mylabpcb/myCPU/Cad/Sep2_200_Wall v2.stl

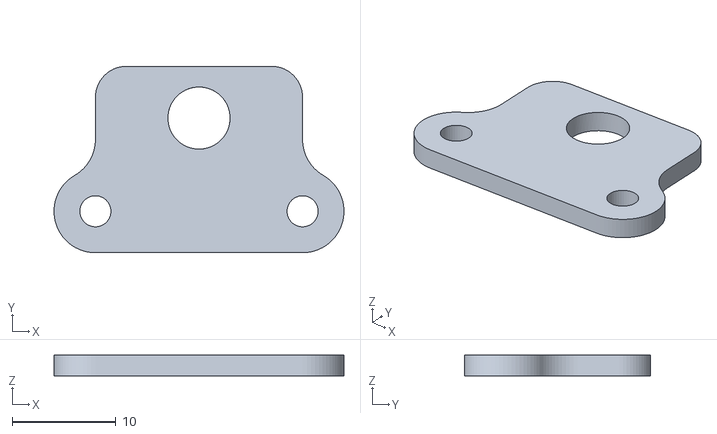
[picture p21: CAD file, 2022-01-03]
Cad/Sep2_200_Wall v2.stl
28.0 x 18.0 x 2.00
