mylabpcb/myCPU/Cad/Sep3_200_Wall v3.stl

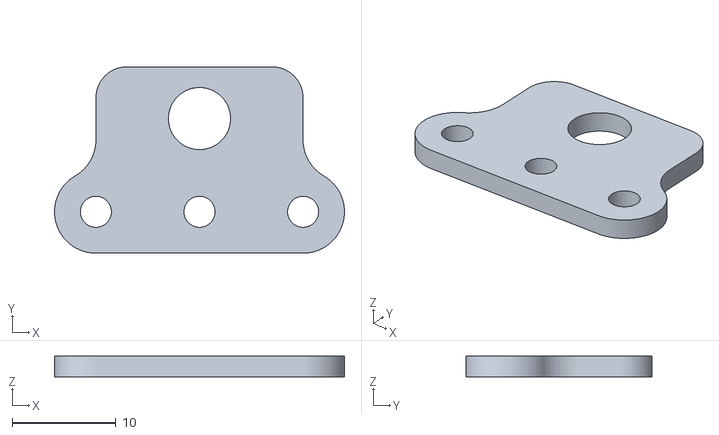
[picture p22: CAD file, 2022-01-03]
Cad/Sep3_200_Wall v3.stl
28.0 x 18.0 x 2.00
