mylabpcb/myCPU/Cad/Sep.stl

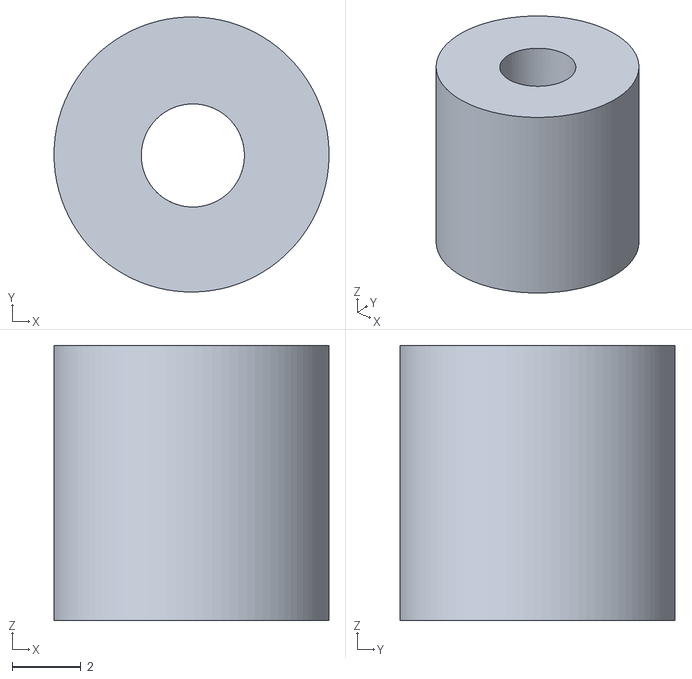
[picture p23: CAD file, 2022-01-03]
Cad/Sep.stl
8.00 x 8.00 x 8.00
