mylabpcb/myCPU/Cad/Sep2_180.stl

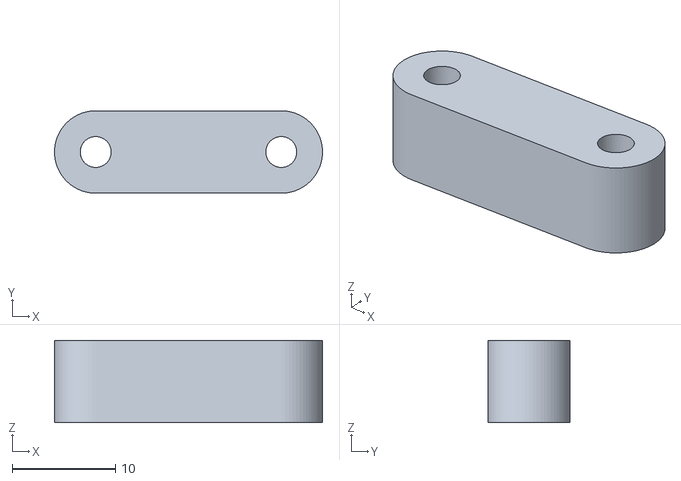
[picture p24: CAD file, 2022-01-03]
Cad/Sep2_180.stl
26.0 x 8.00 x 8.00
