mylabpcb/myCPU/Docs/myCPU_BUS_Manager_module_full.pdf

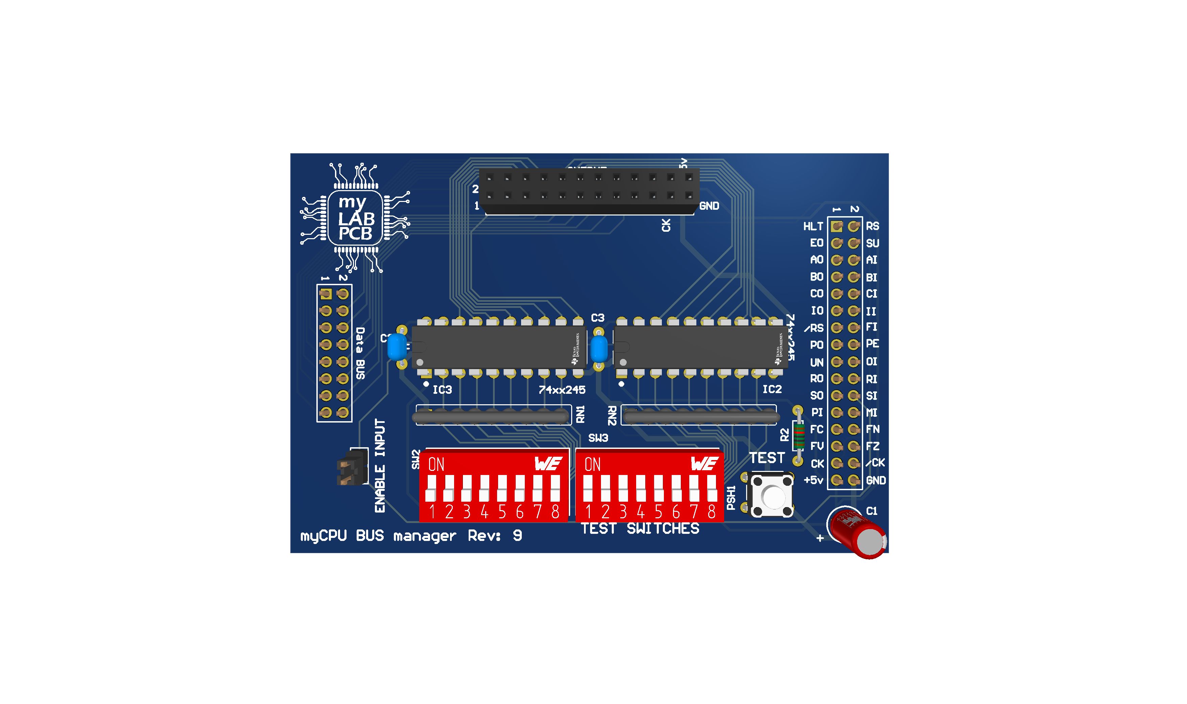
[picture p73: page 1]

Decoupling Capacitors 31 | 42 5 | 6 7 | 8 9 | 10 11 | 12

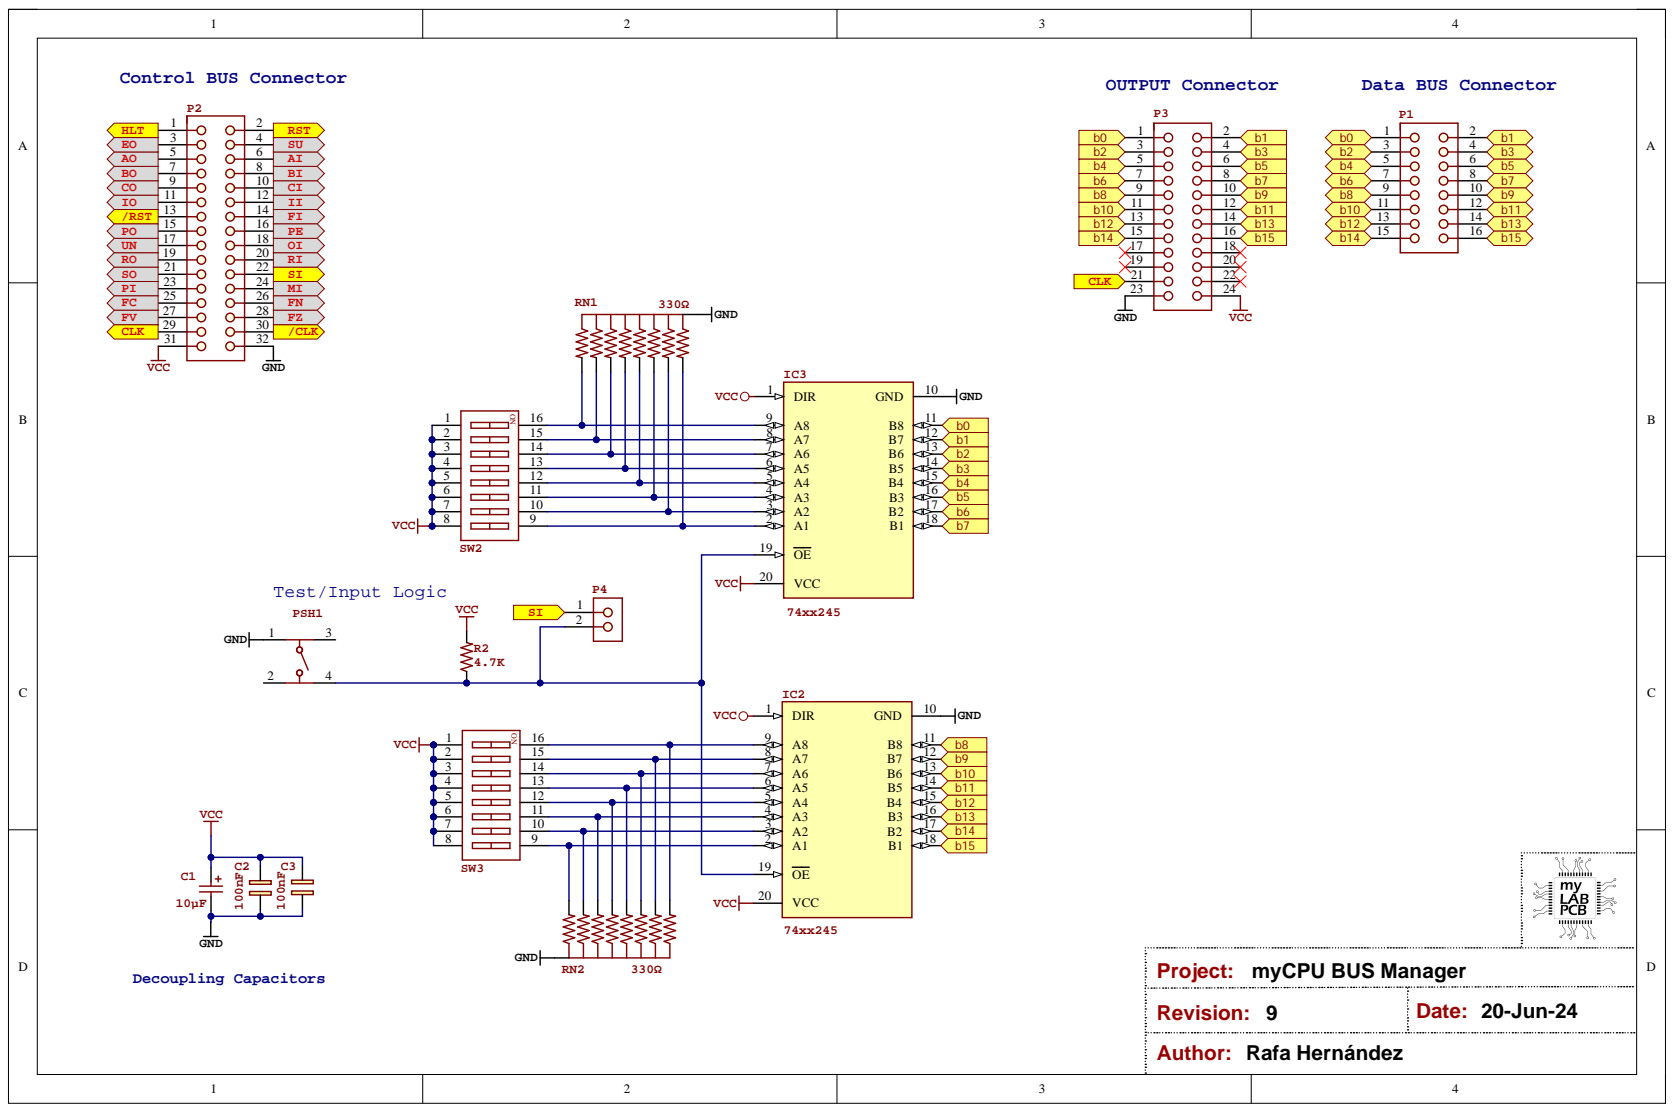
[picture p74: page 3]

Project: myCPU BUS Manager

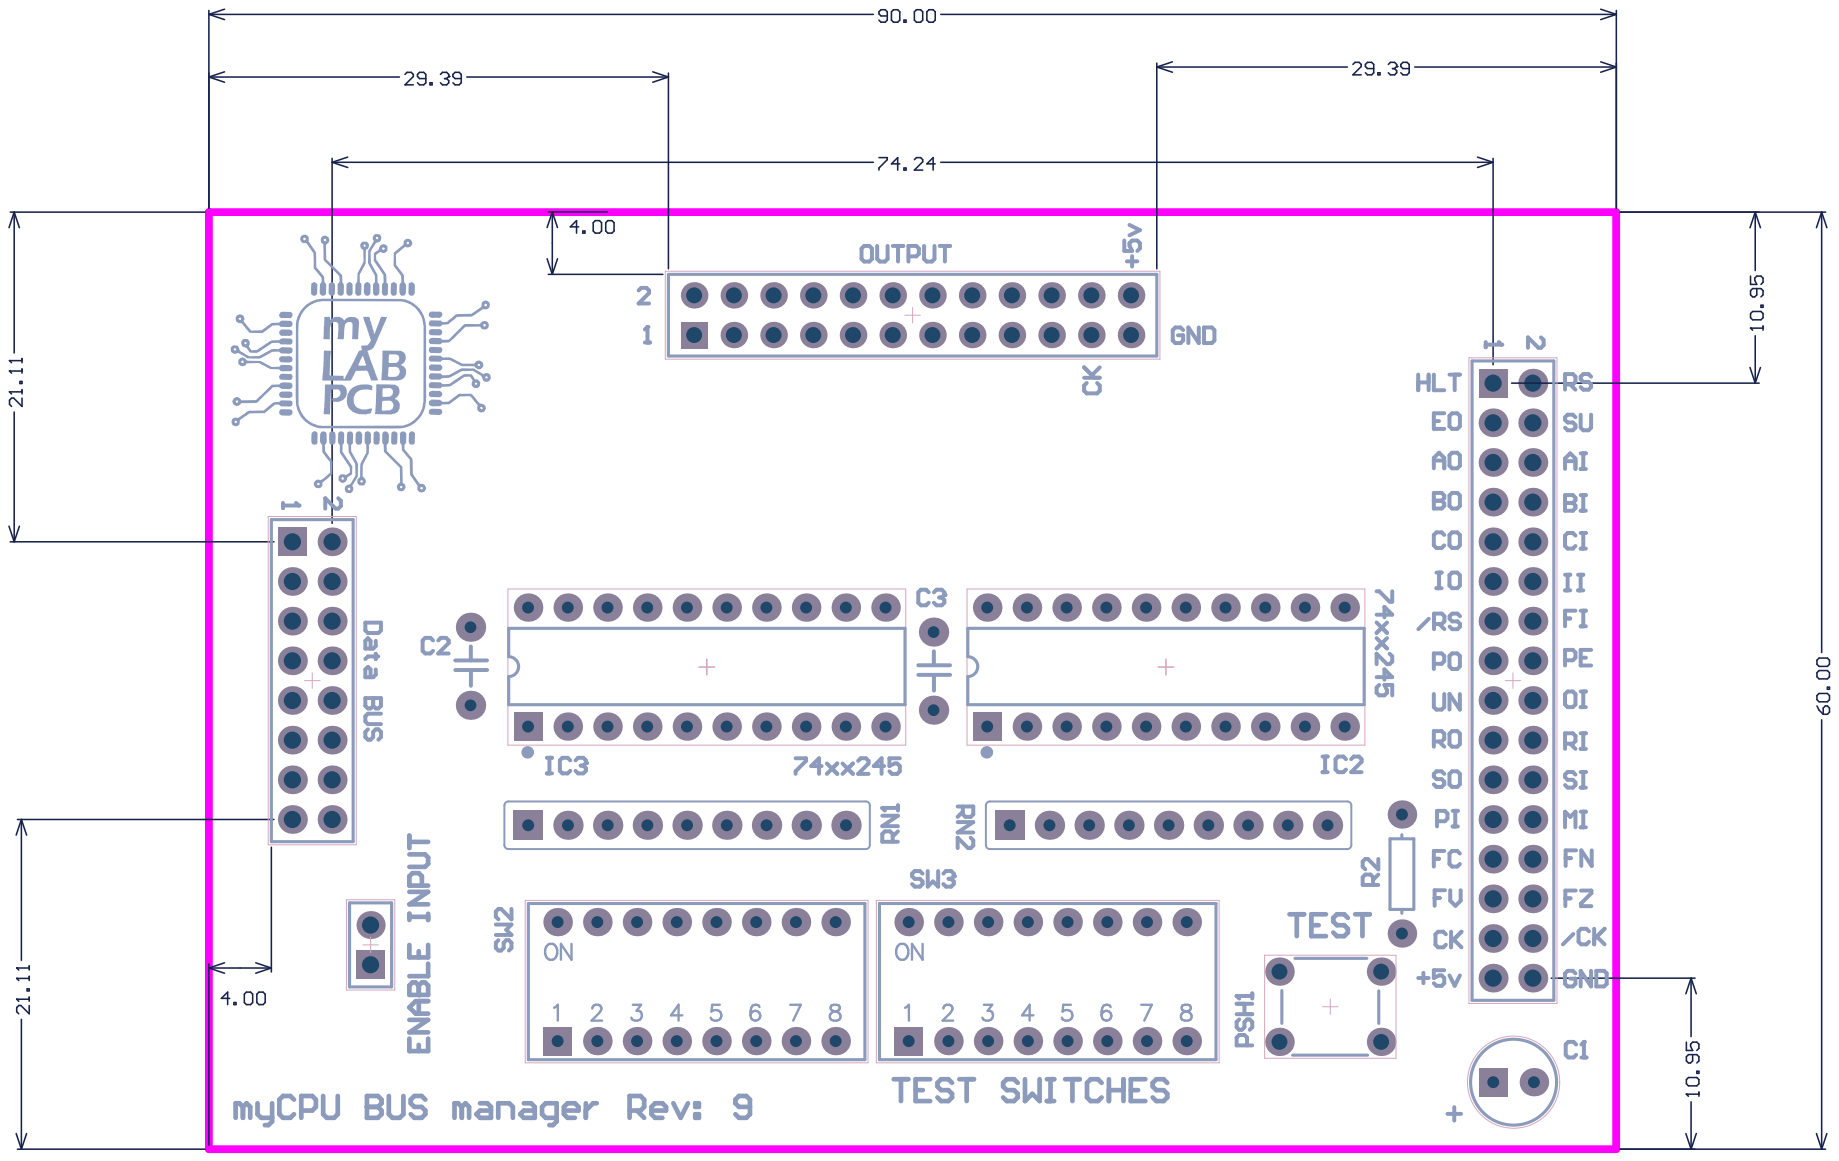
[picture p75: page 4]

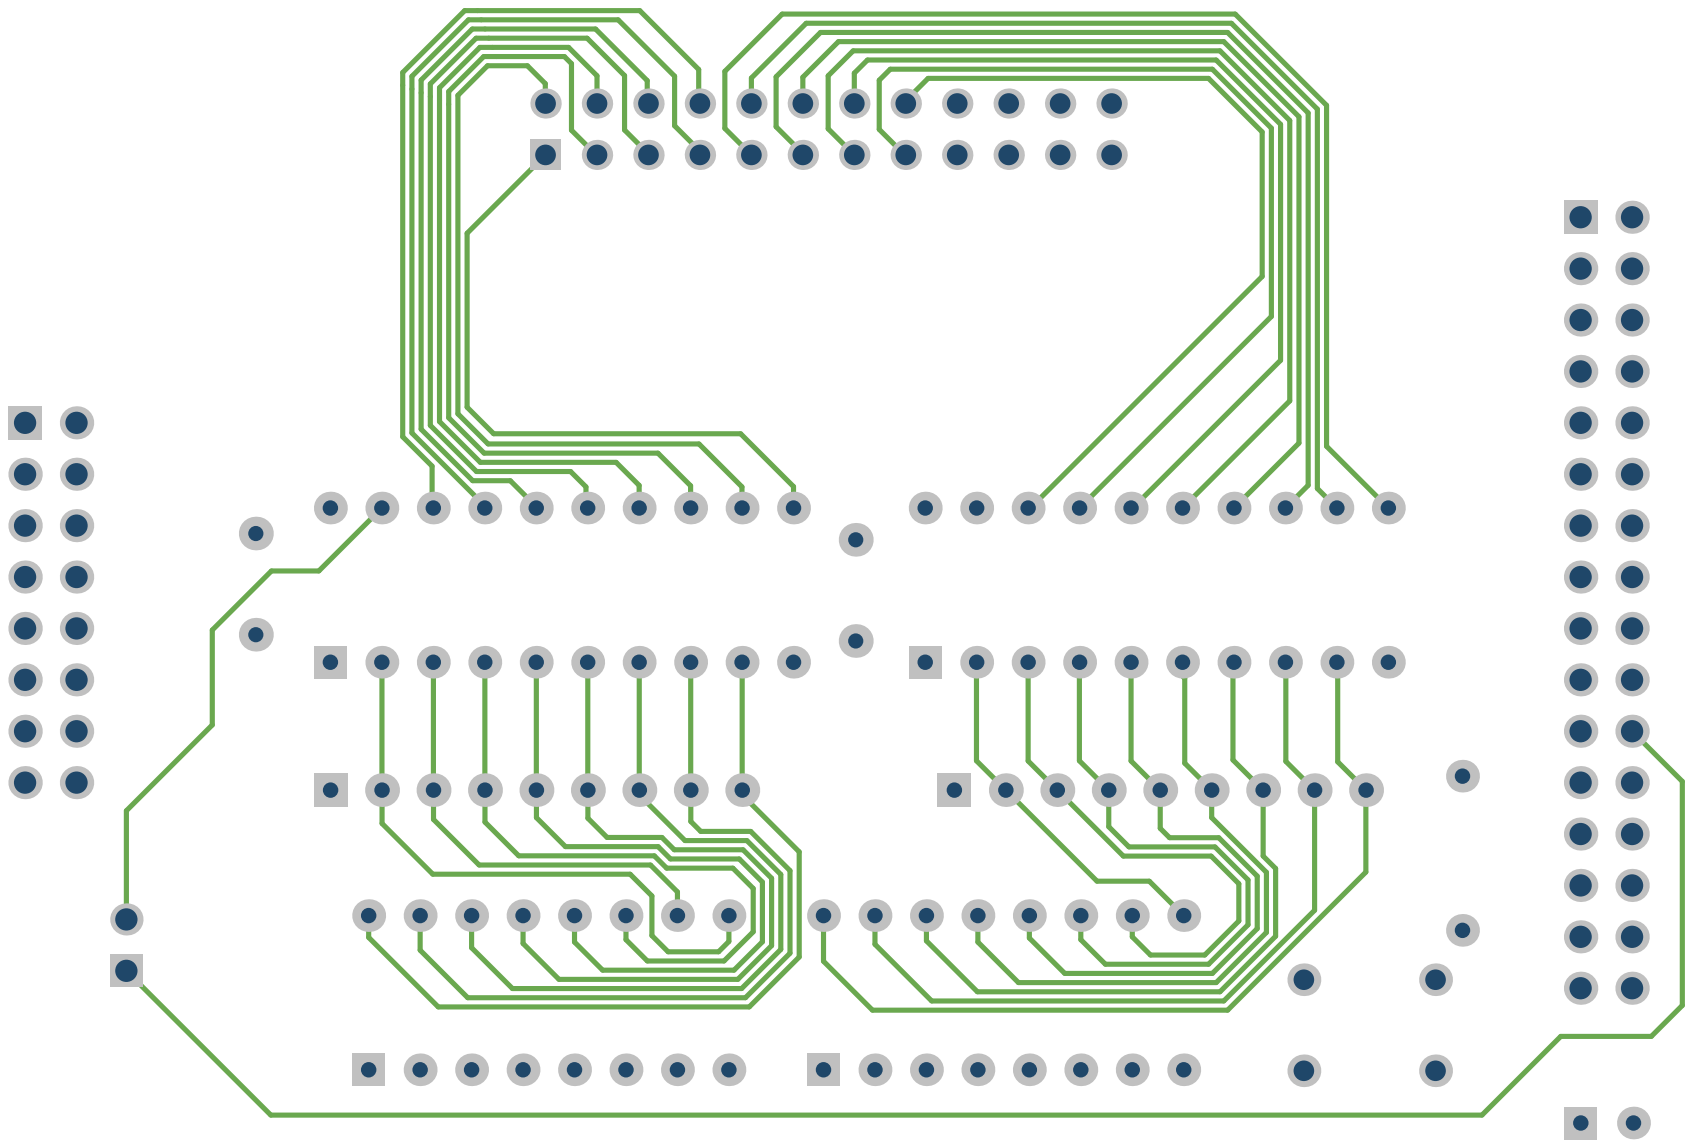
[picture p76: page 5]

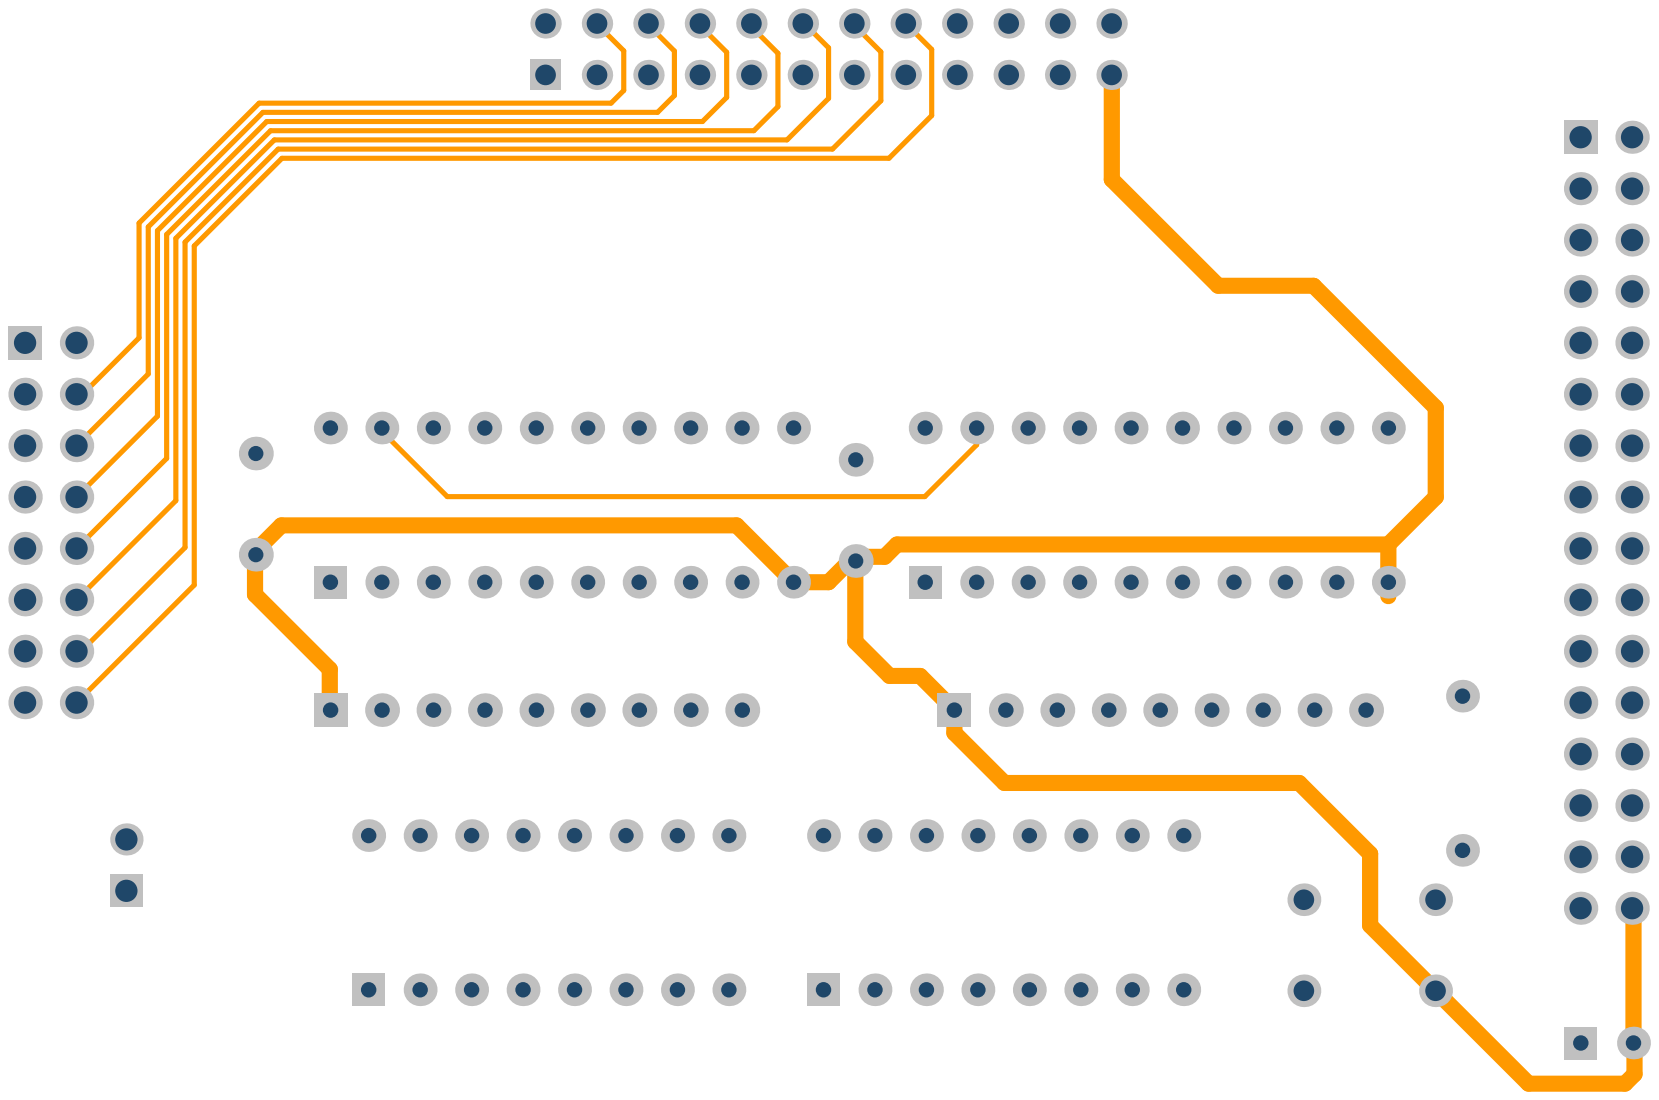
[picture p77: page 6]

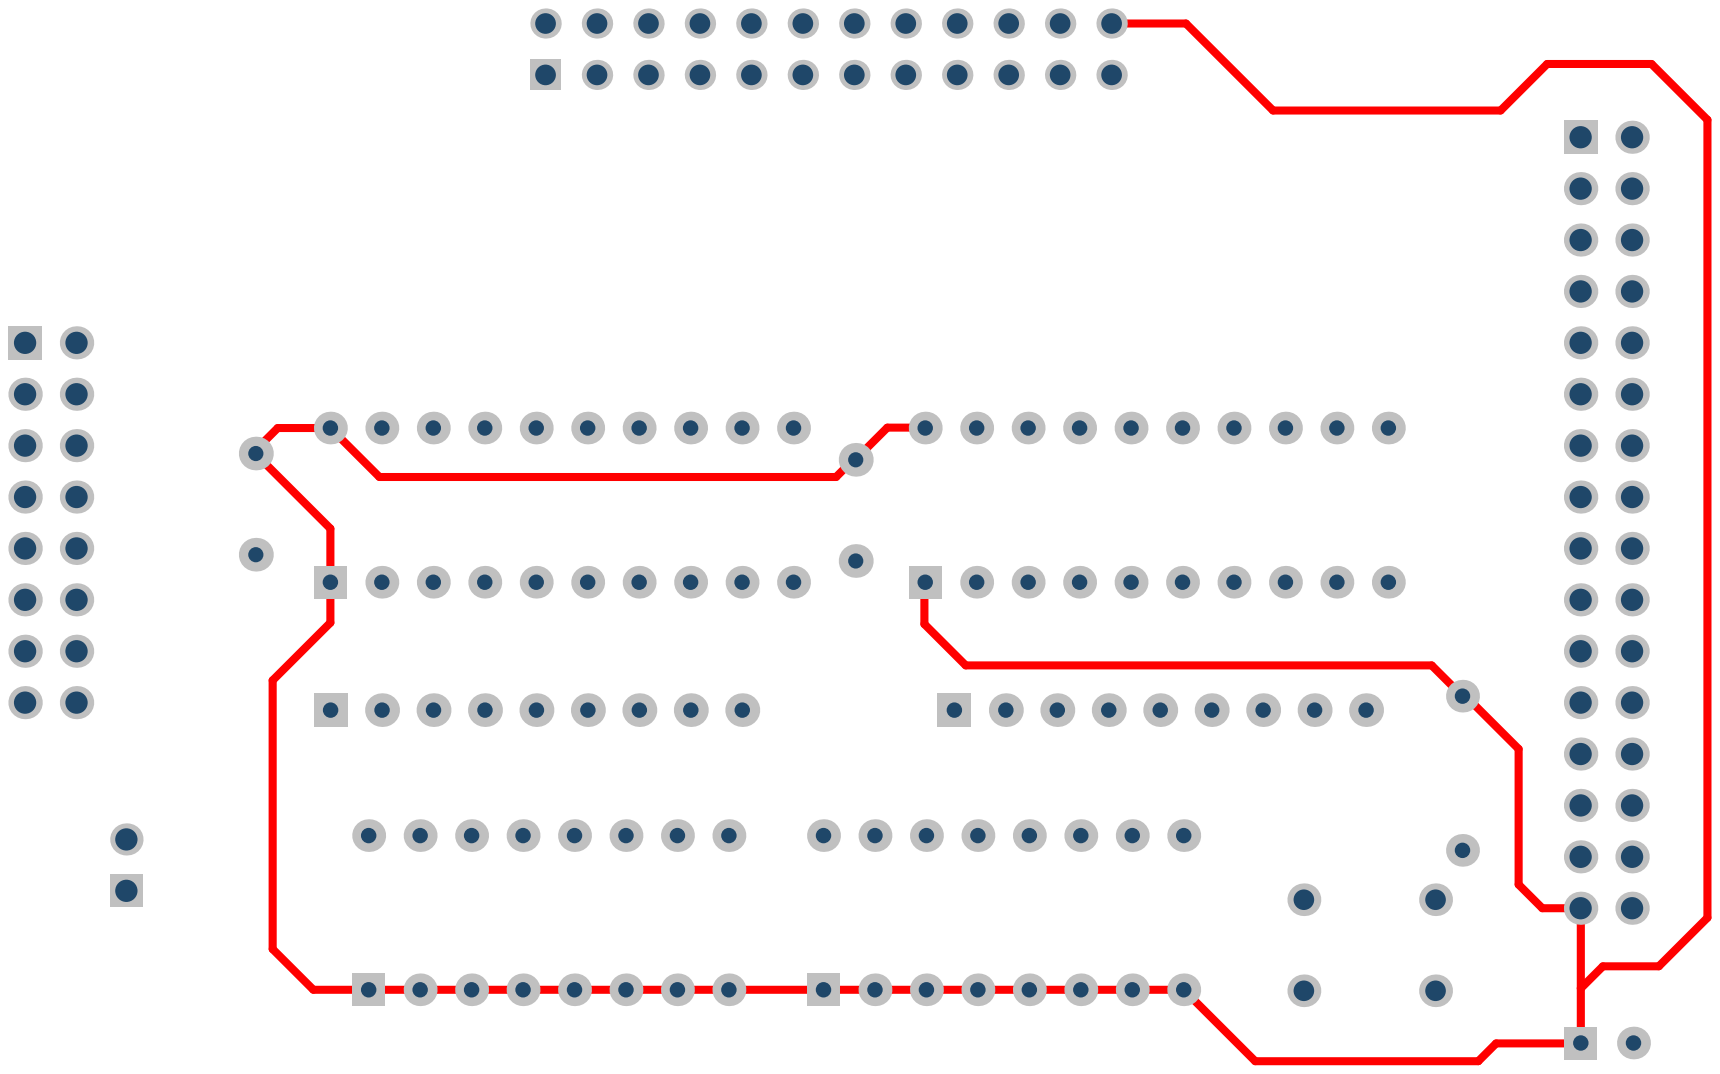
[picture p78: page 7]

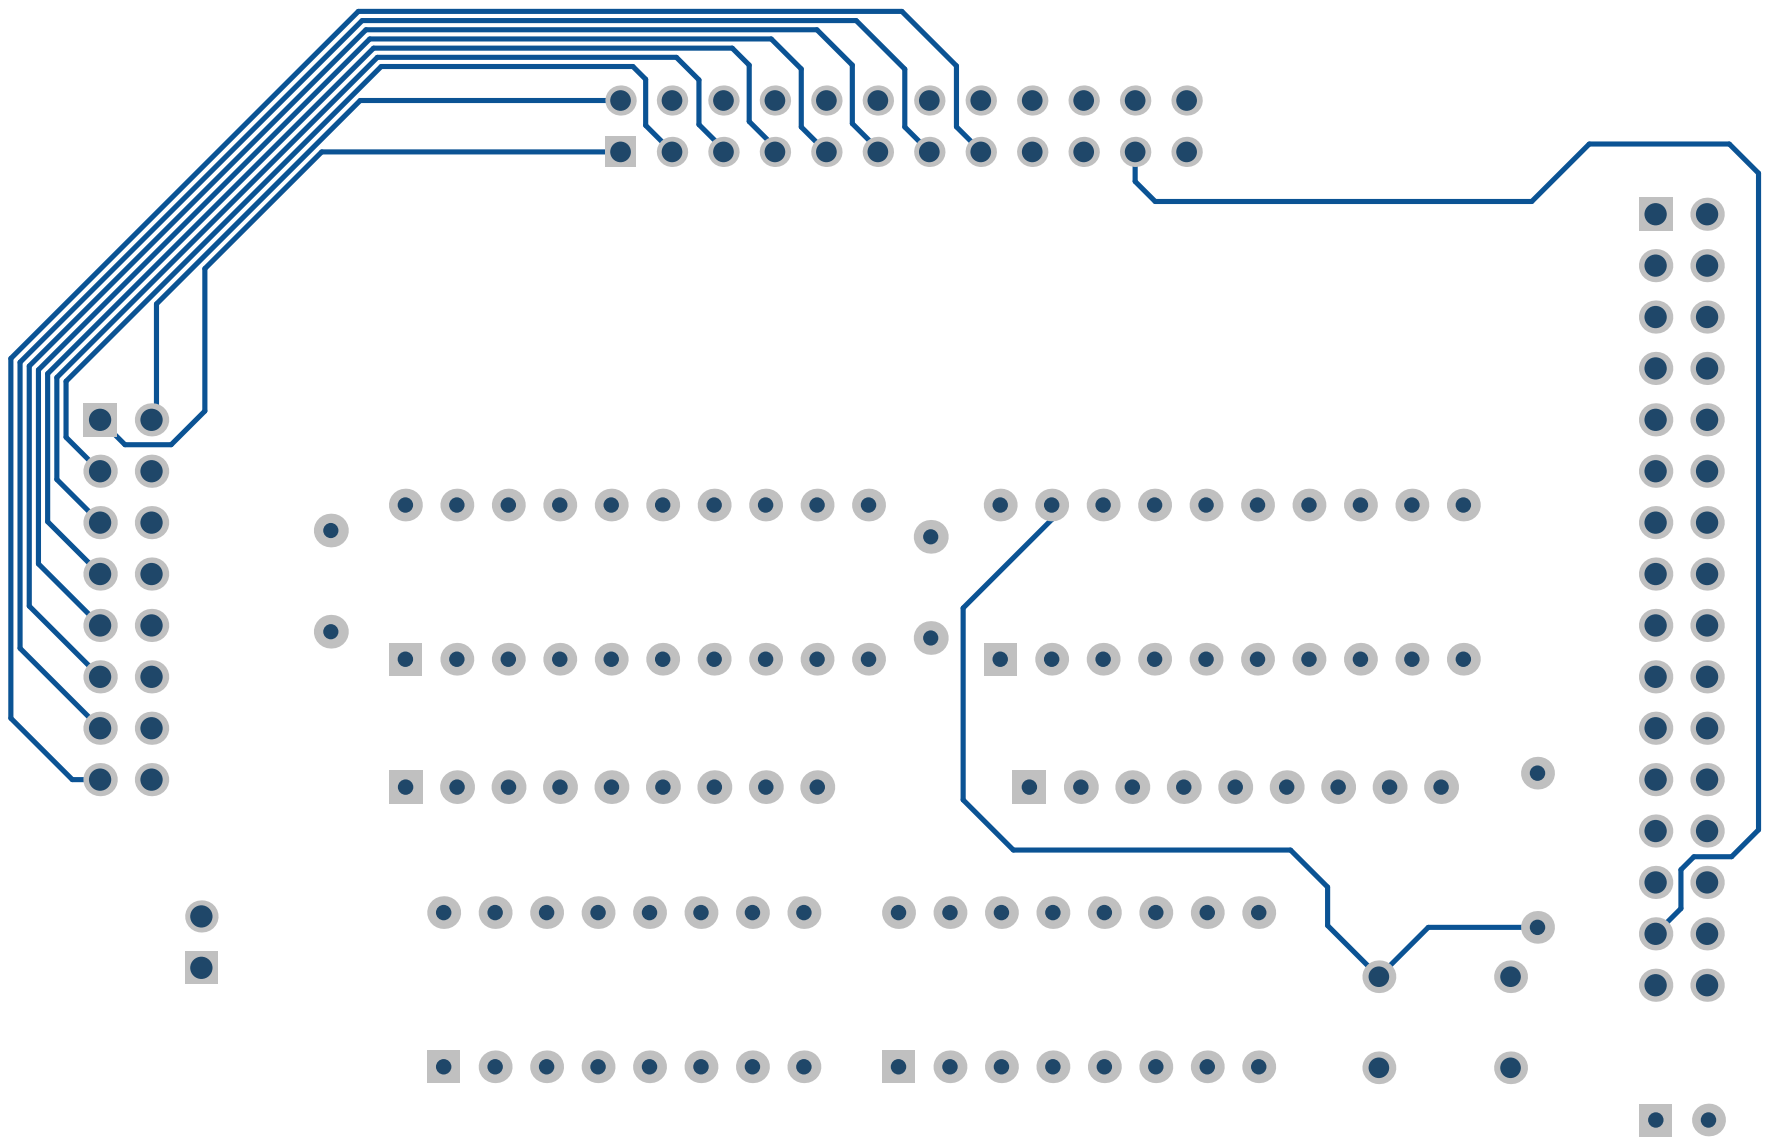
[picture p79: page 8]

# Bill of Materials

# myCPU BUS Manager

Description | Value | Q
Electrolytic capacitor 16v/50v | 10µF | 1
Ceramic capacitor | 100nF | 2
Non inverting bus transceiver | 74xx245 | 2
Pin Header, THT, pitch 2.54mm, Dual Row, Vertical | 16p | 1
Pin Header, THT, pitch 2.54mm, Dual Row, Vertical | 32p | 1
Socket Header, THT, pitch 2.54mm, Dual Row, Vertical | 24p | 1
Pin Header, THT, pitch 2.54mm, Single Row, Vertical | 2p | 1
Tactile button 6 mm | 6mm | 1
Resistor Axial | 4.7K | 1
Resistor array 8 elements,9 pins | 330 | 2
DIP switch 8 positions | 8p | 2

# Assembly List

## myCPU BUS Manager

Designator | Description | Value
C1 | Electrolytic capacitor 16v/50v | 10µF
C2 | Ceramic capacitor | 100nF
C3 | Ceramic capacitor | 100nF
IC2 | Non inverting bus transceiver | 74xx245
IC3 | Non inverting bus transceiver | 74xx245
P1 | Pin Header, THT, pitch 2.54mm, Dual Row, Vertical | 16p
P2 | Pin Header, THT, pitch 2.54mm, Dual Row, Vertical | 32p
P3 | Socket Header, THT, pitch 2.54mm, Dual Row, Vertical | 24p
P4 | Pin Header, THT, pitch 2.54mm, Single Row, Vertical | 2p
PSH1 | Tactile button 6 mm | 6mm
R2 | Resistor Axial | 4.7K
RN1 | Resistor array 8 elements,9 pins | 330
RN2 | Resistor array 8 elements,9 pins | 330
SW2 | DIP switch 8 positions | 8p
SW3 | DIP switch 8 positions | 8p
