mylabpcb/myCPU/Docs/myCPU_BUS_module_full.pdf

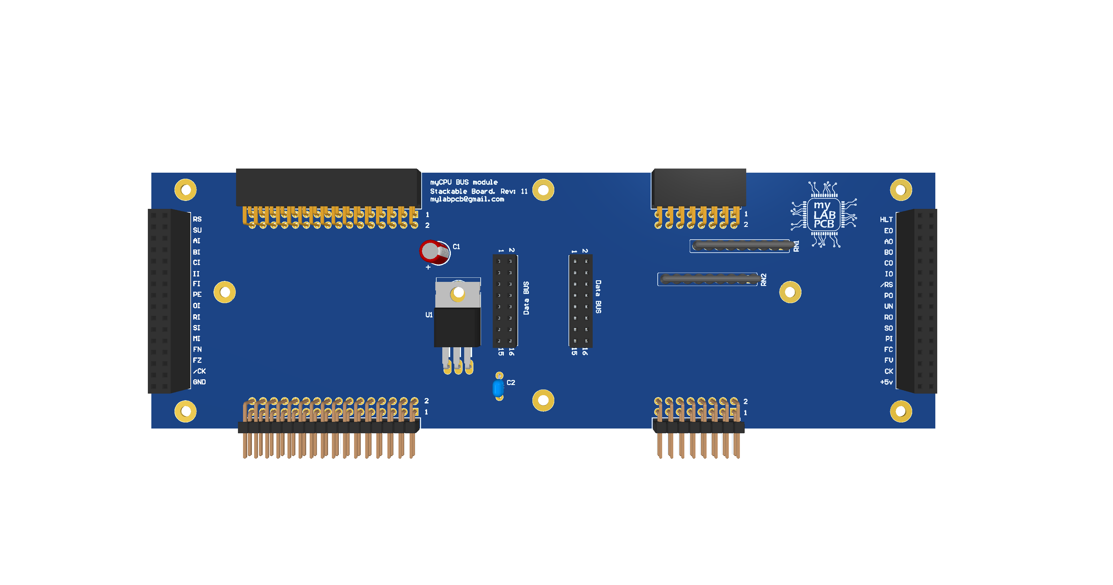
[picture p80: page 1]

# GND GND b1b3b5b7b9b11 b13 b15

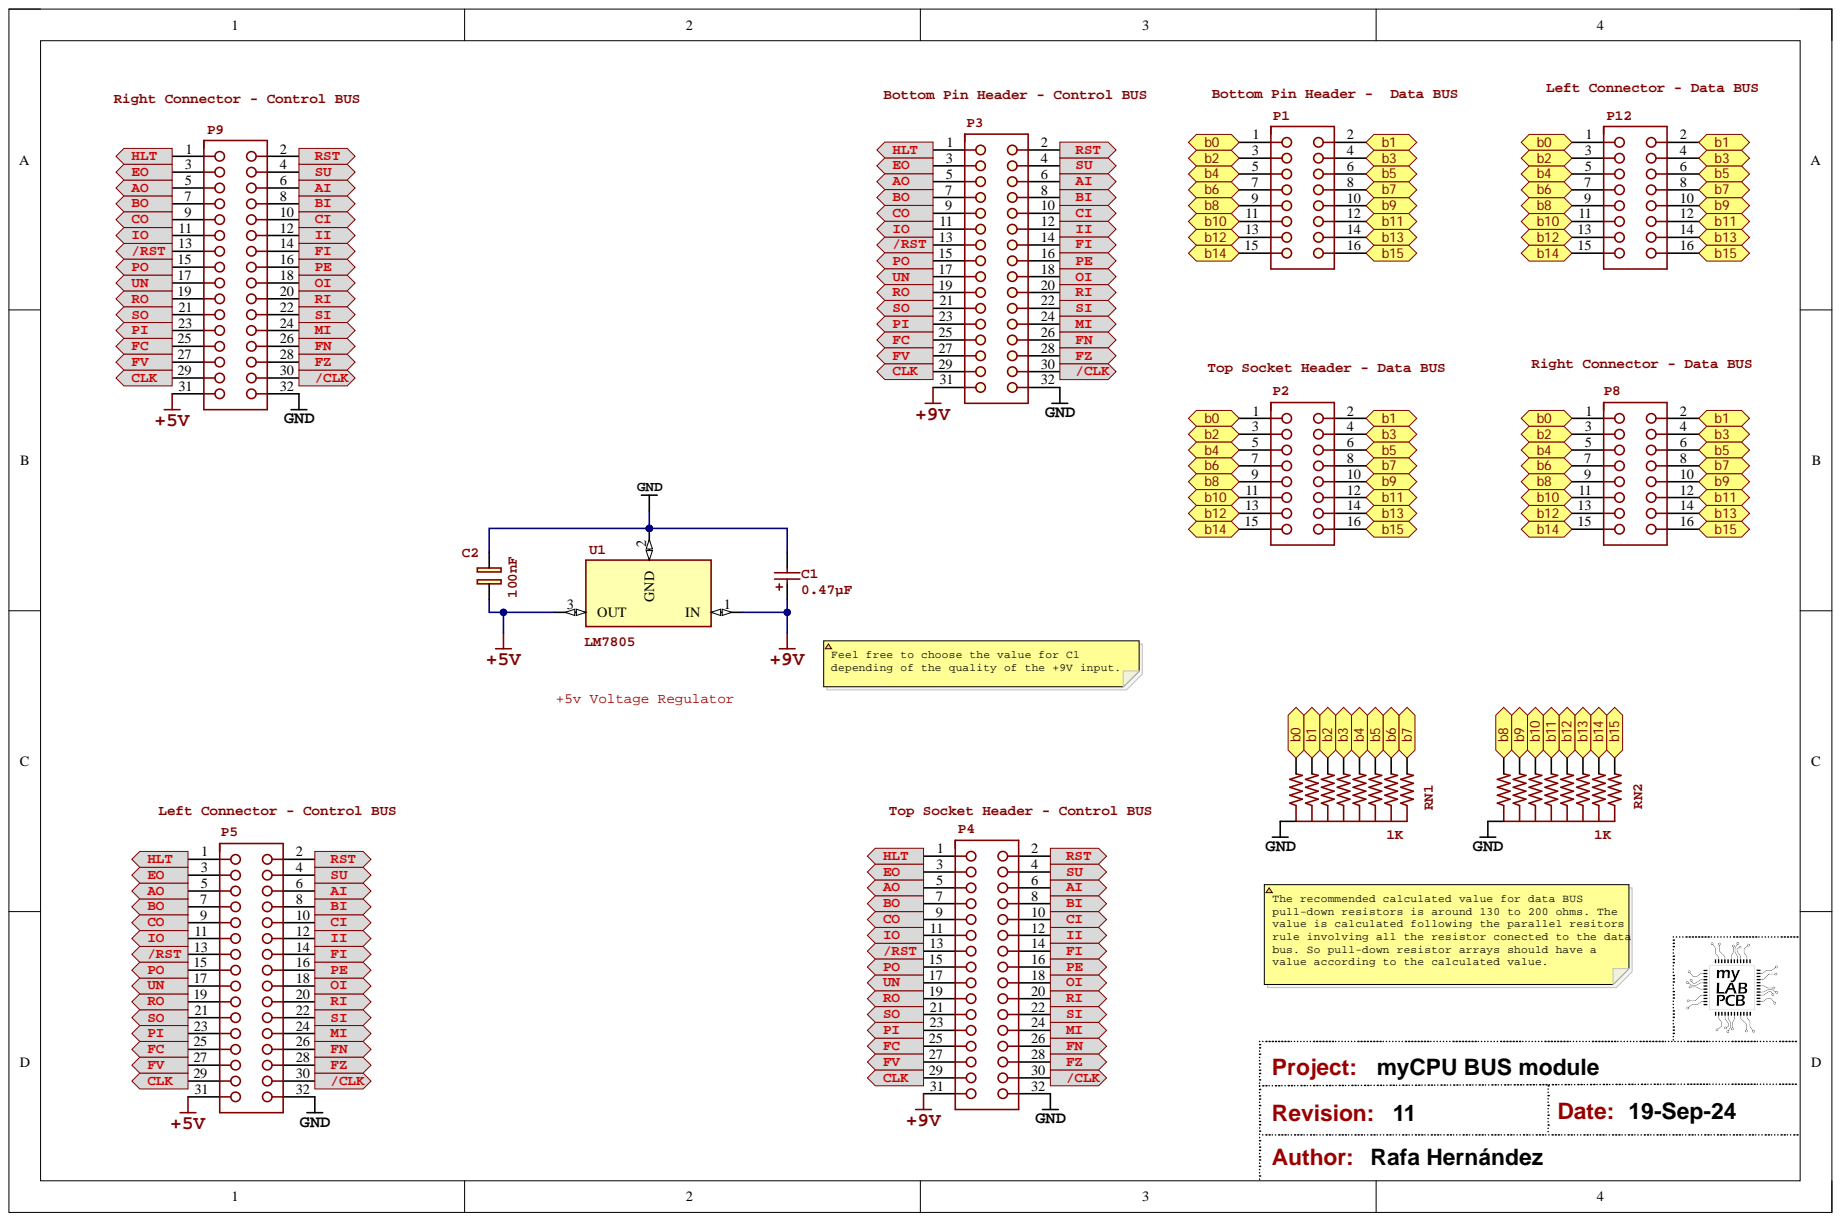
[picture p81: page 3]

Left Connector - Data BUS

Right Connector - Control BUS

Bottom Pin Header - Control BUS

Right Connector - Data BUS

Left Connector - Control BUS

Top Socket Header - Control BUS

Project: myCPU BUS module

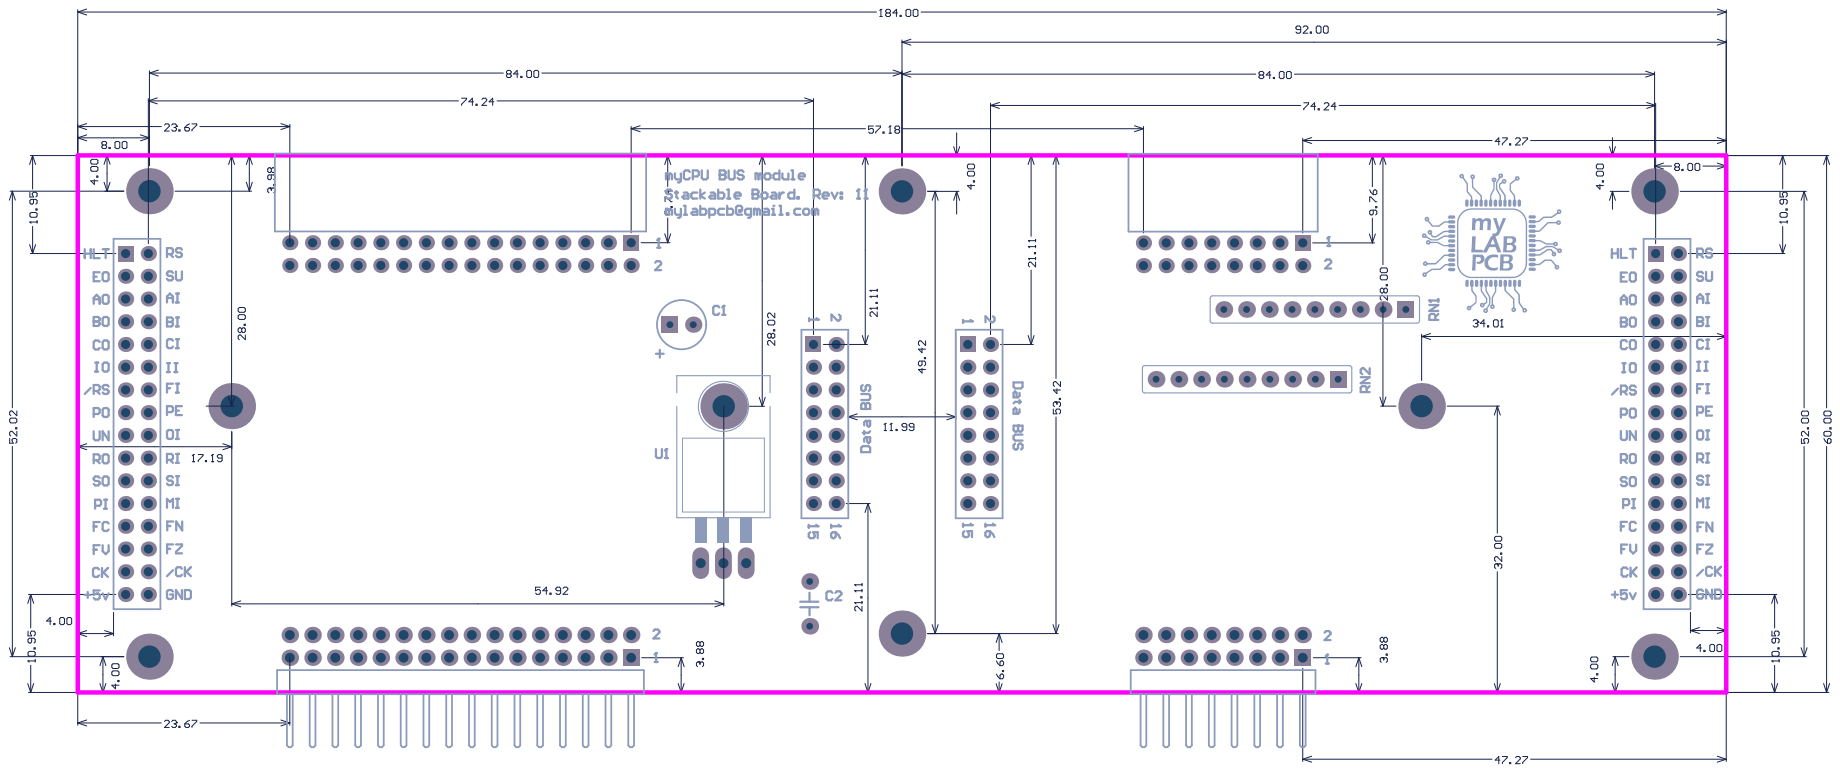
[picture p82: page 4]

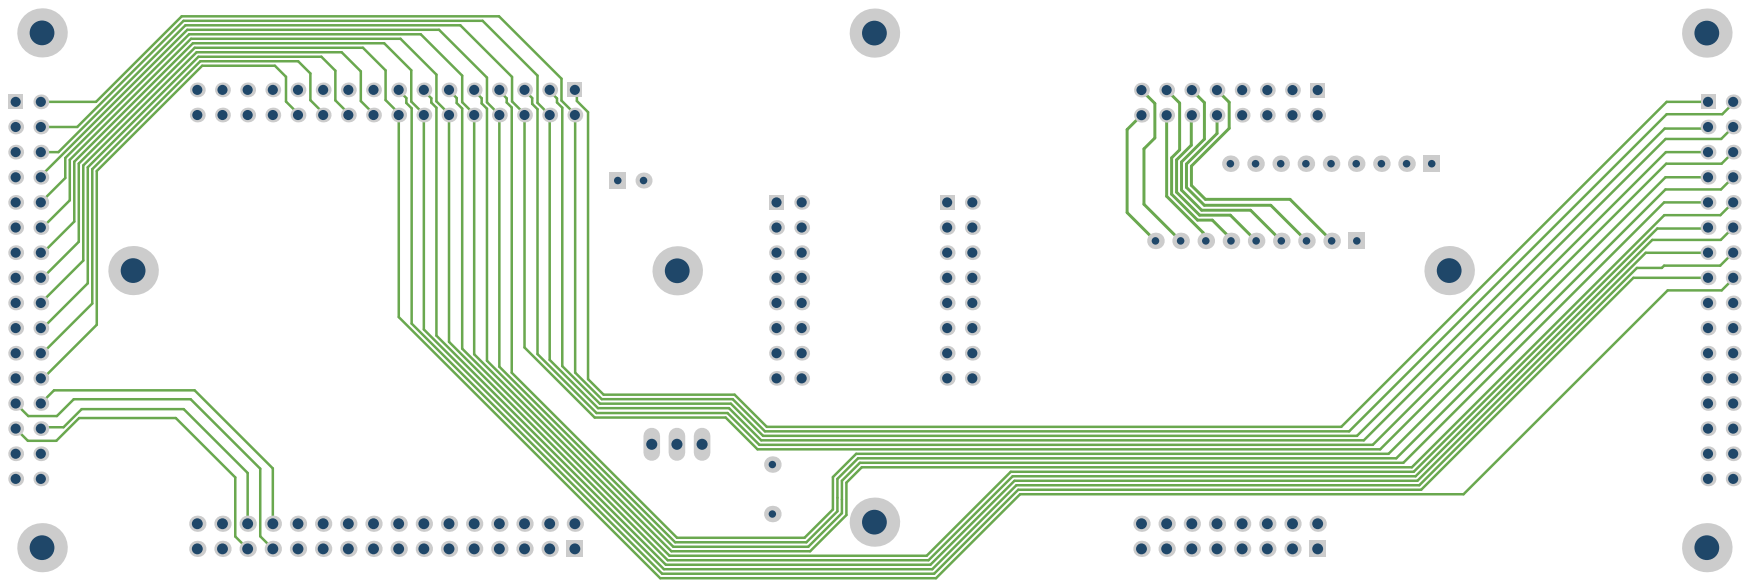
[picture p83: page 5]

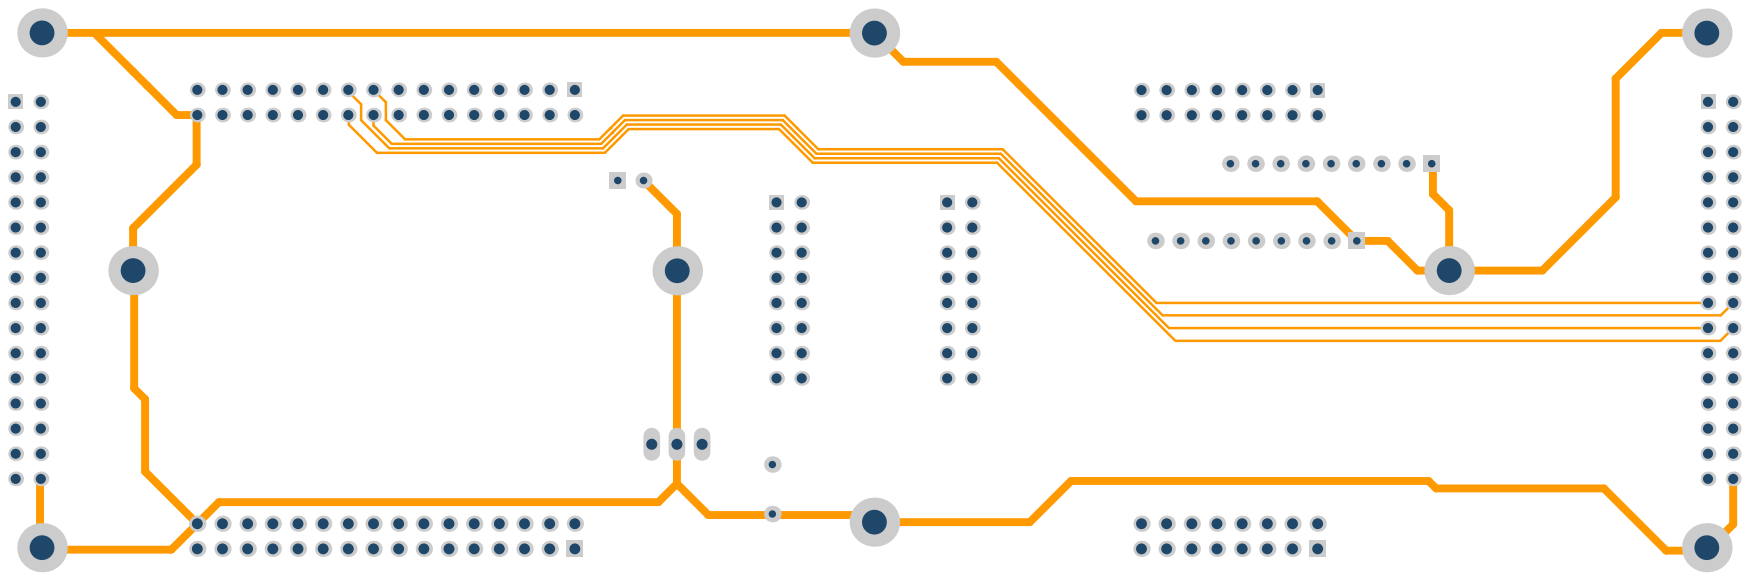
[picture p84: page 6]

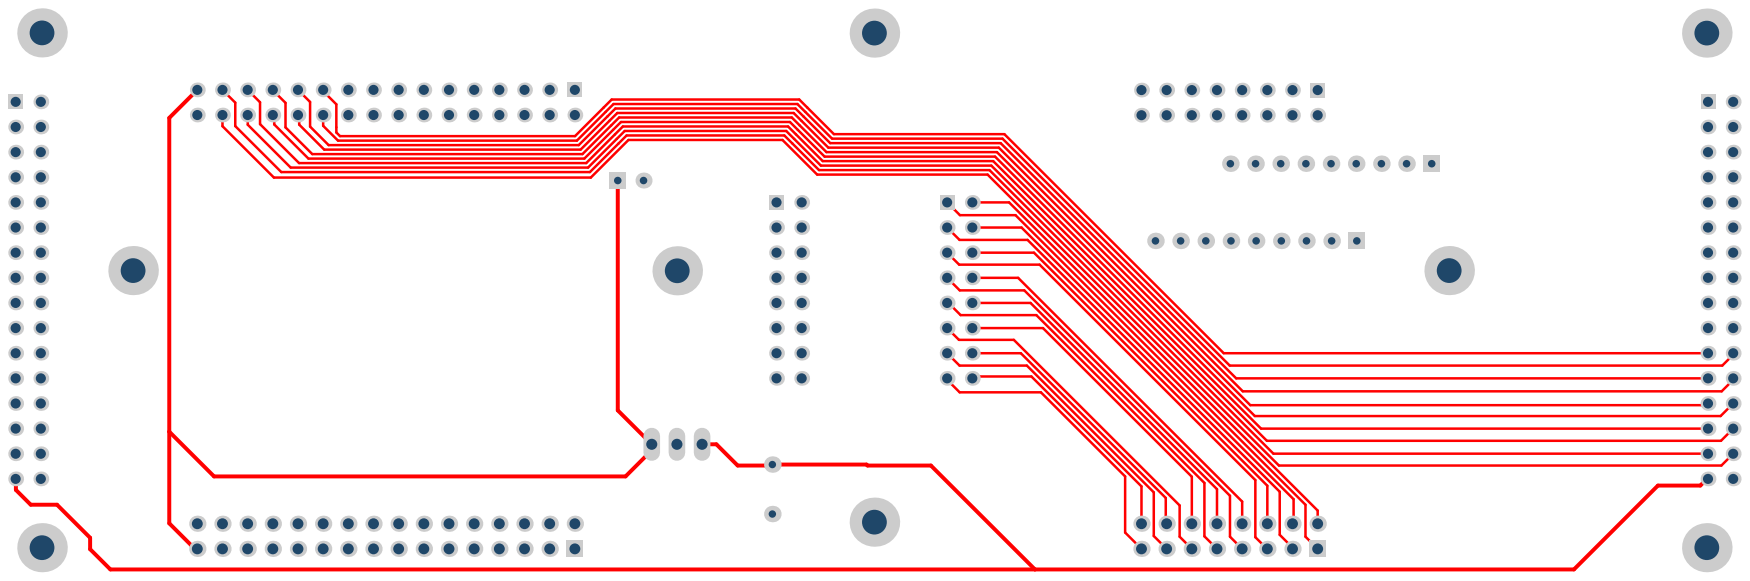
[picture p85: page 7]

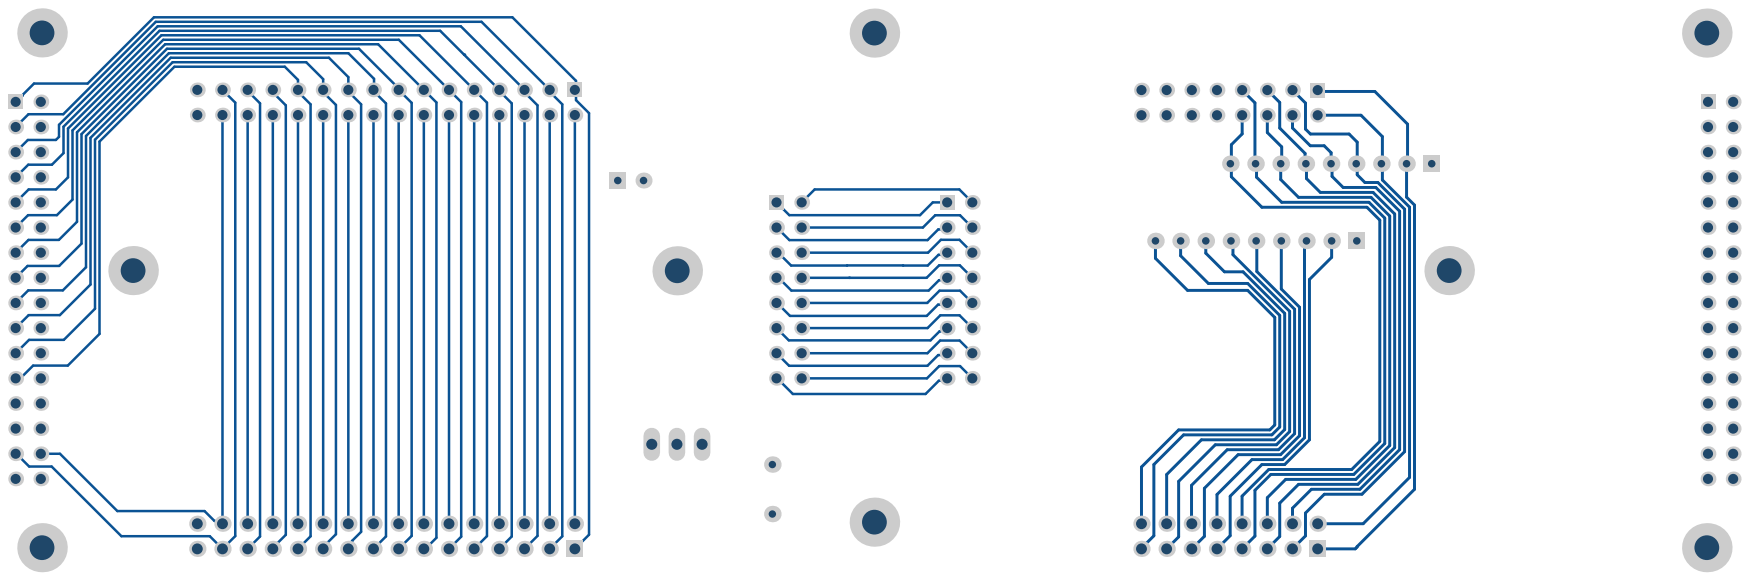
[picture p86: page 8]

# Bill of Materials

# myCPU BUS module

Description | Value | Q
Electrolytic capacitor 16v/50v | 0.47µF | 1
Ceramic capacitor | 100nF | 1
Pin Header, THT, pitch 2.54mm, Dual Row, Angled | 16p | 1
Socket Header, THT, pitch 2.54mm, Dual Row, Angled | 16p | 1
Pin Header, THT, pitch 2.54mm, Dual Row, Angled | 32p | 1
Socket Header, THT, pitch 2.54mm, Dual Row, Angled | 32p | 1
Socket Header, THT, pitch 2.54mm, Dual Row, Vertical | 32p | 2
Socket Header, THT, pitch 2.54mm, Dual Row, Vertical | 16p | 2
Resistor array 8 elements,9 pins | 1K | 2
5v/1A Voltage Regulator | LM7805 | 1

# Assembly List

## myCPU BUS module

Designator | Description | Value
C1 | Electrolytic capacitor 16v/50v | 0.47µF
C2 | Ceramic capacitor | 100nF
P1 | Pin Header, THT, pitch 2.54mm, Dual Row, Angled | 16p
P2 | Socket Header, THT, pitch 2.54mm, Dual Row, Angled | 16p
P3 | Pin Header, THT, pitch 2.54mm, Dual Row, Angled | 32p
P4 | Socket Header, THT, pitch 2.54mm, Dual Row, Angled | 32p
P5 | Socket Header, THT, pitch 2.54mm, Dual Row, Vertical | 32p
P8 | Socket Header, THT, pitch 2.54mm, Dual Row, Vertical | 16p
P9 | Socket Header, THT, pitch 2.54mm, Dual Row, Vertical | 32p
P12 | Socket Header, THT, pitch 2.54mm, Dual Row, Vertical | 16p
RN1 | Resistor array 8 elements,9 pins | 1K
RN2 | Resistor array 8 elements,9 pins | 1K
U1 | 5v/1A Voltage Regulator | LM7805
