mylabpcb/myCPU/Docs/myCPU_CSM_module_full.pdf

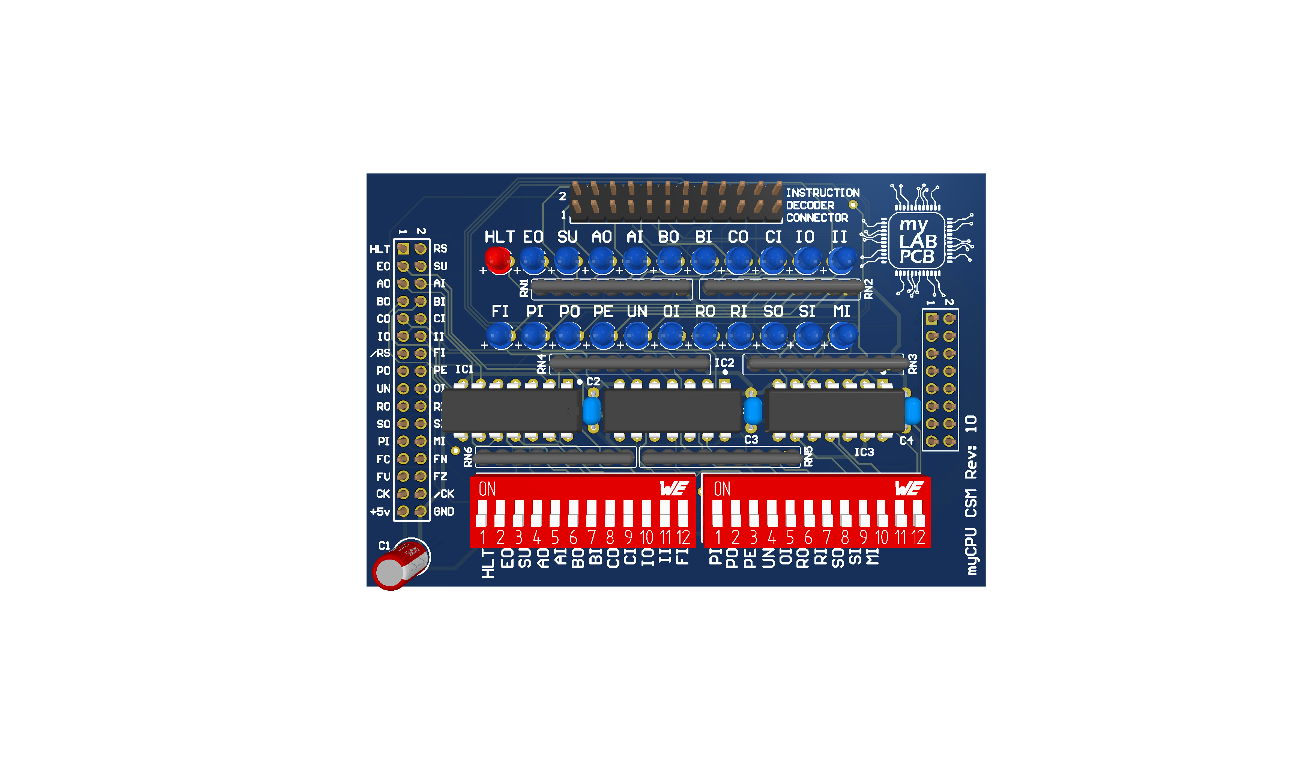
[picture p87: page 1]

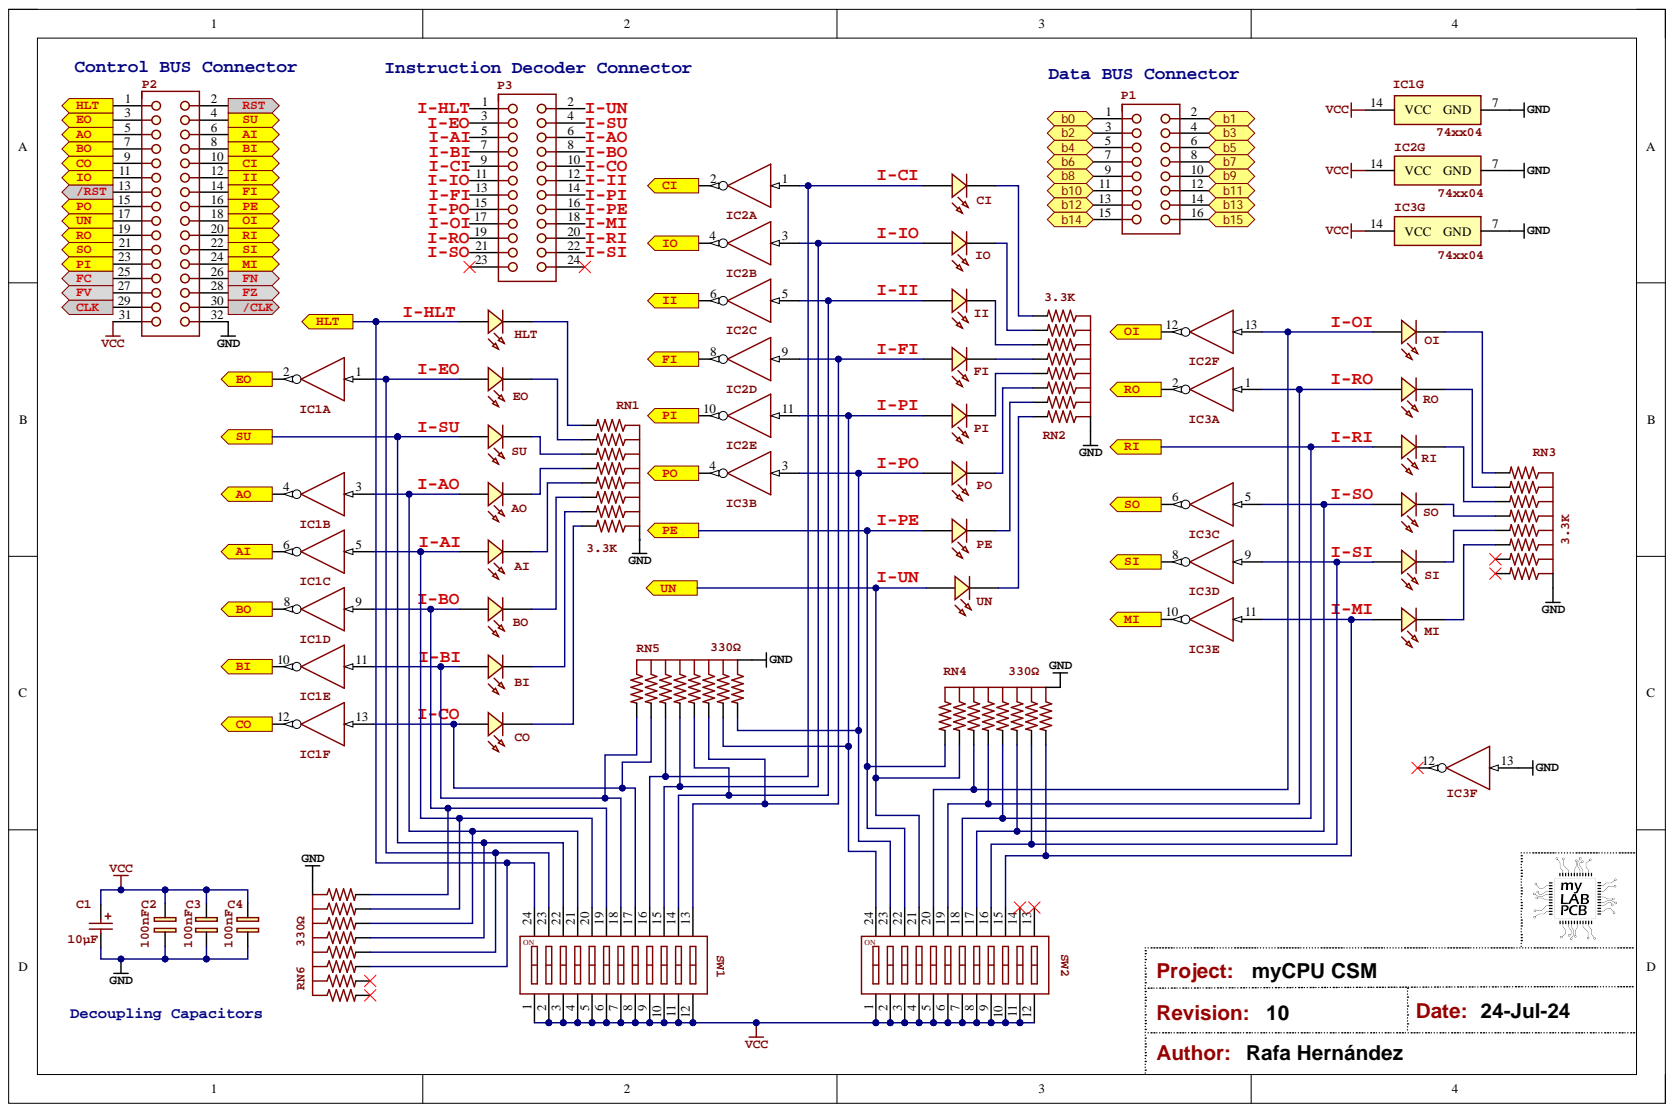
[picture p88: page 3]

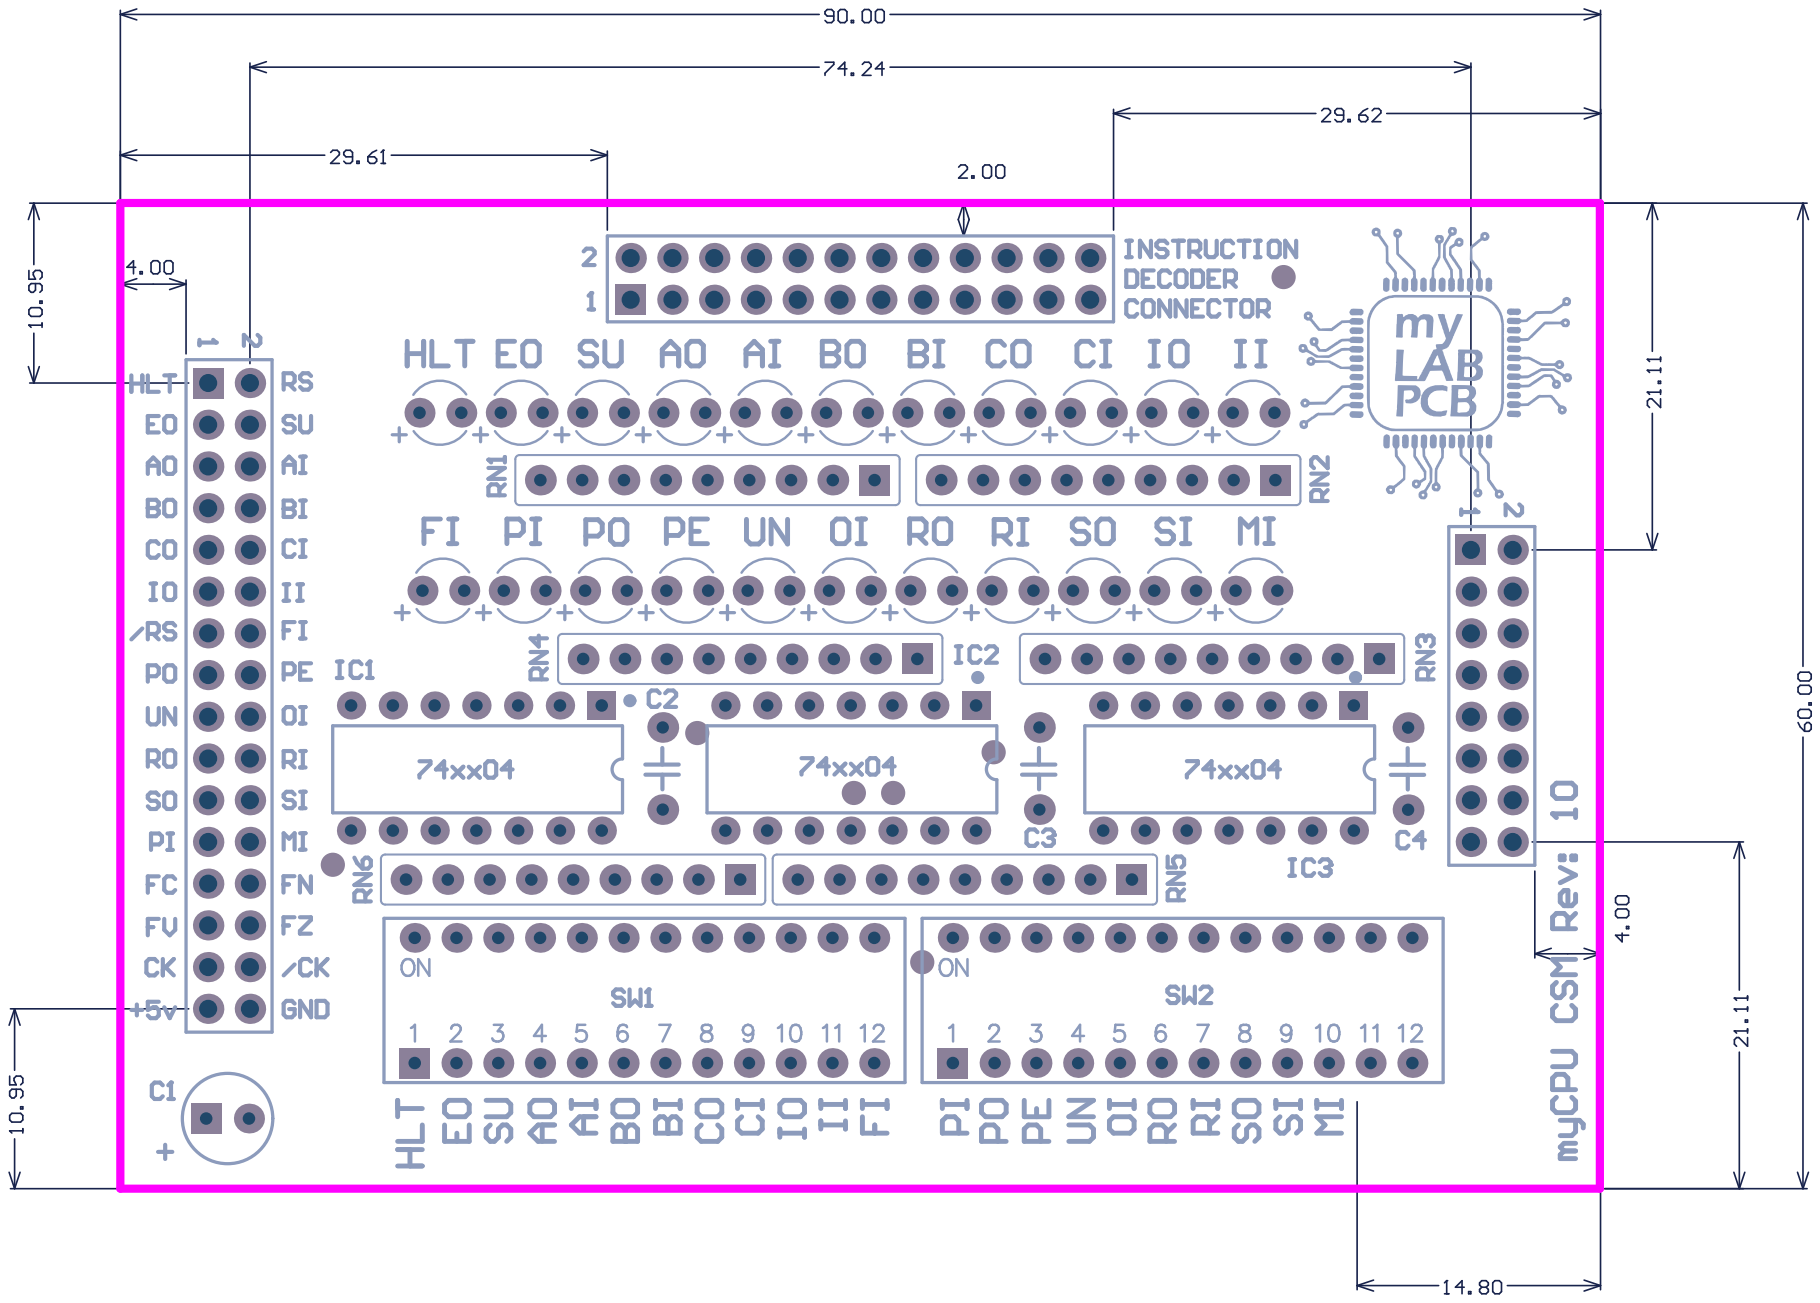
[picture p89: page 4]

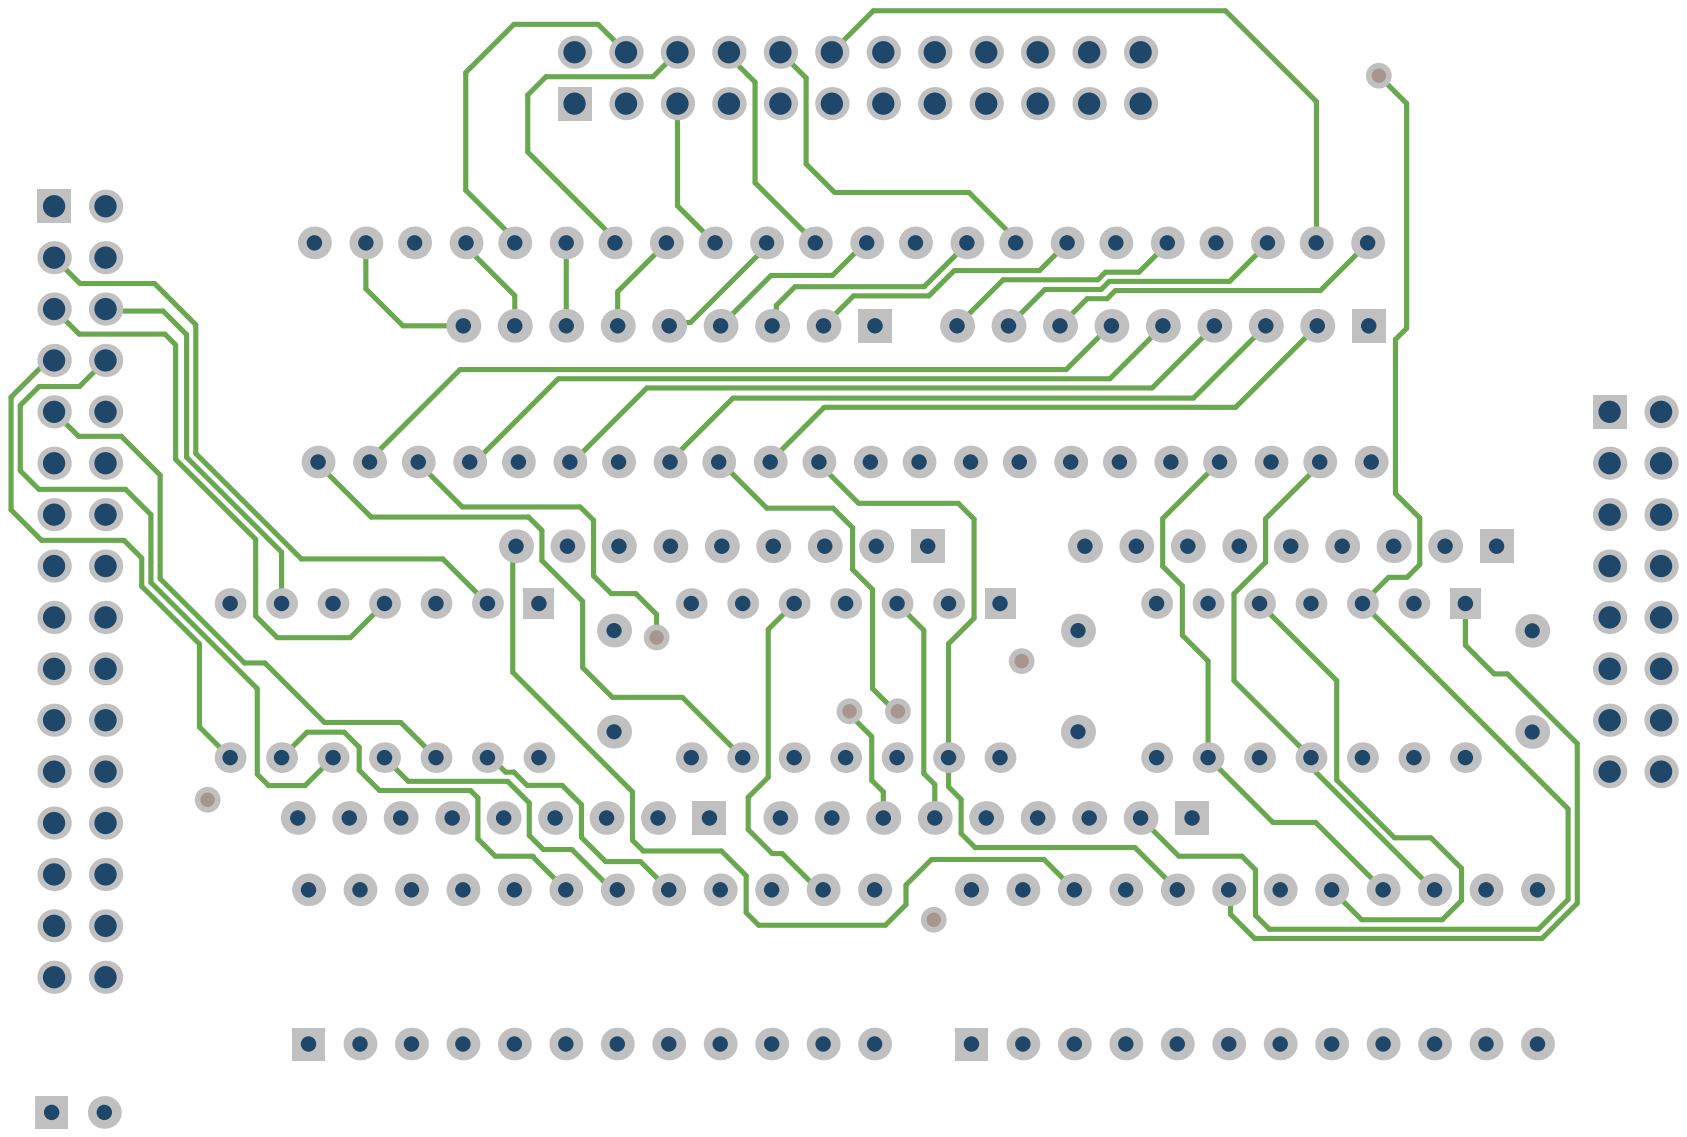
[picture p90: page 5]

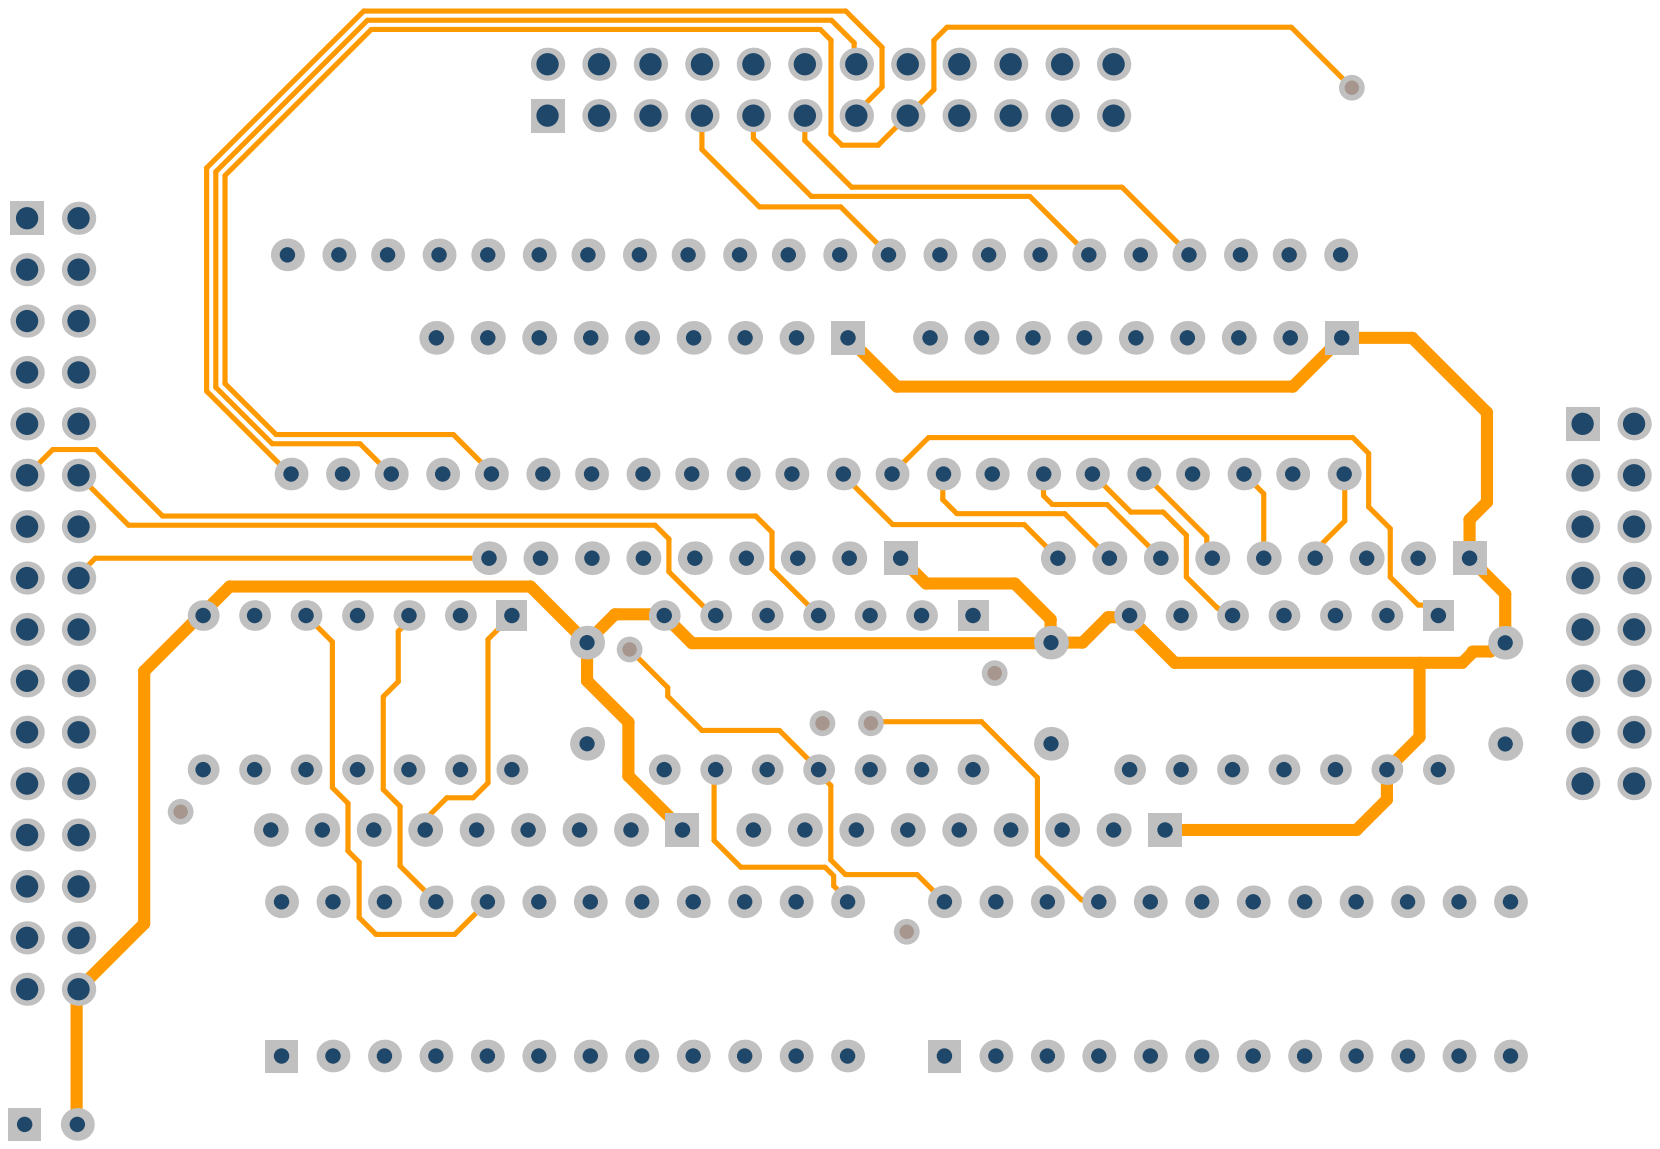
[picture p91: page 6]

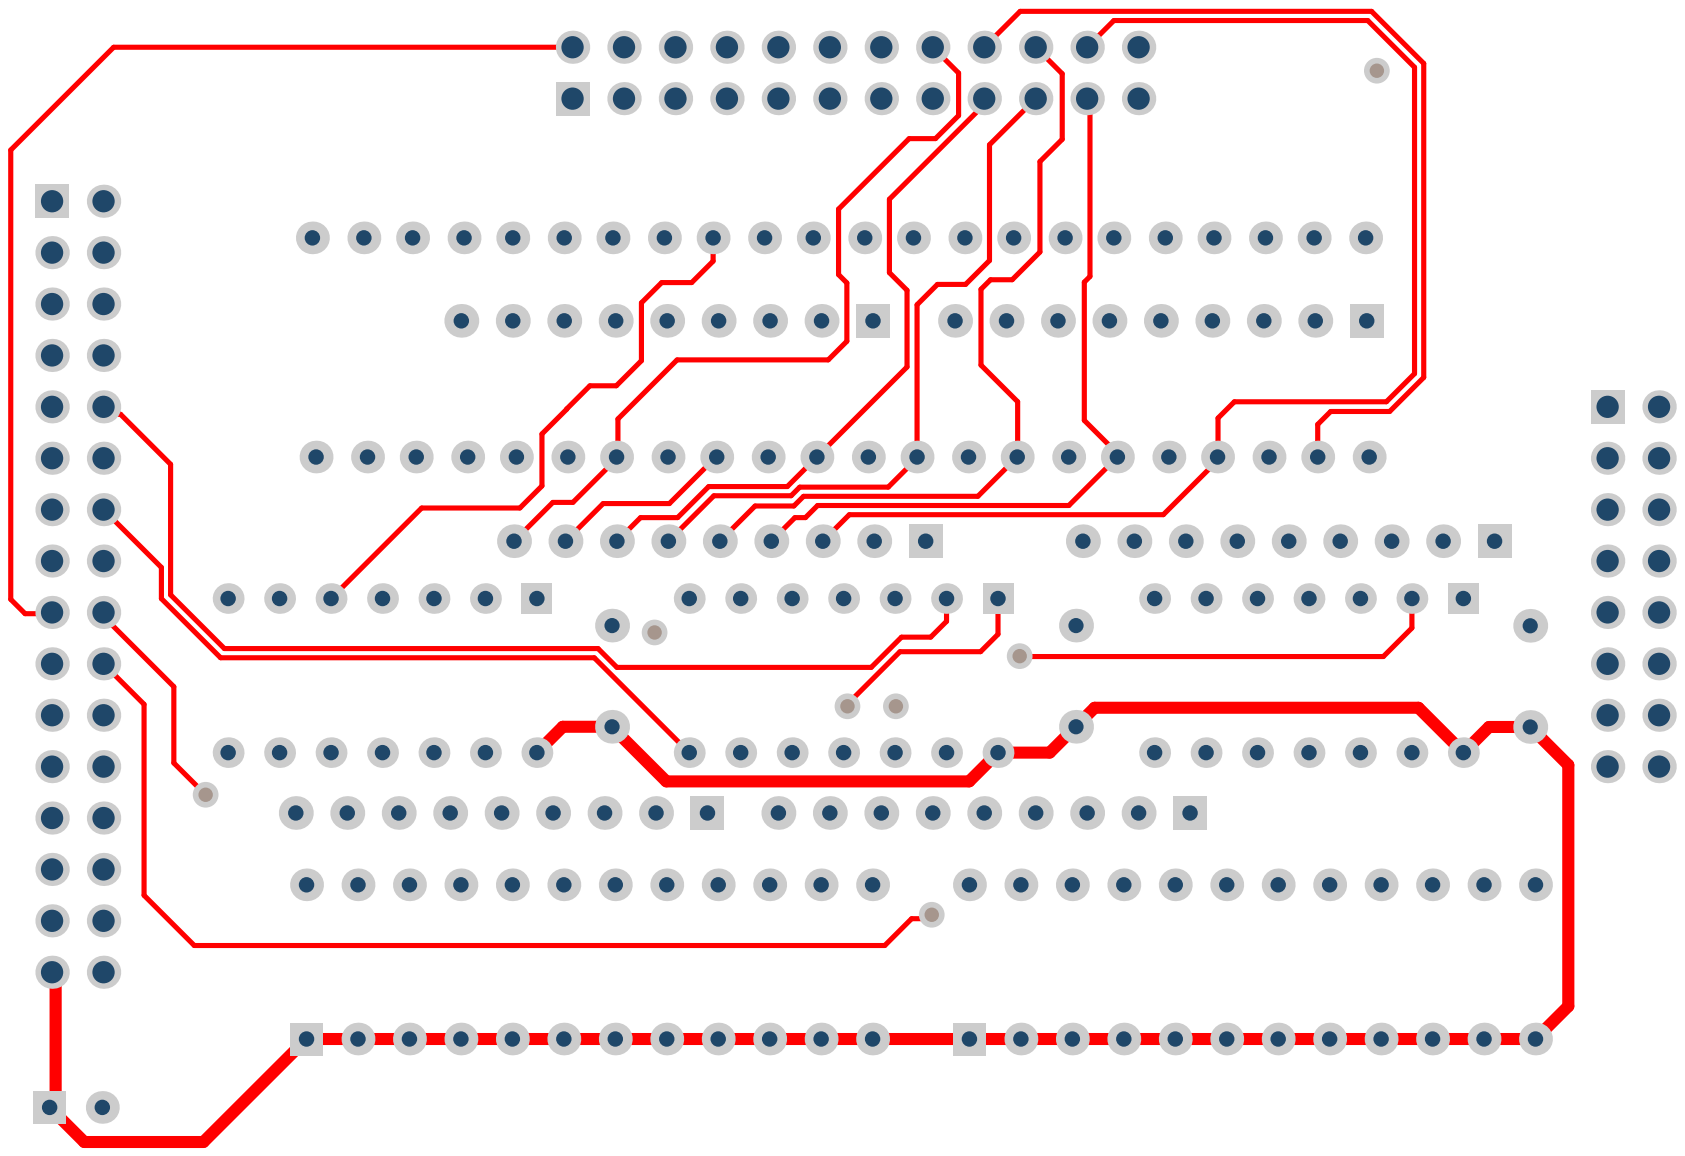
[picture p92: page 7]

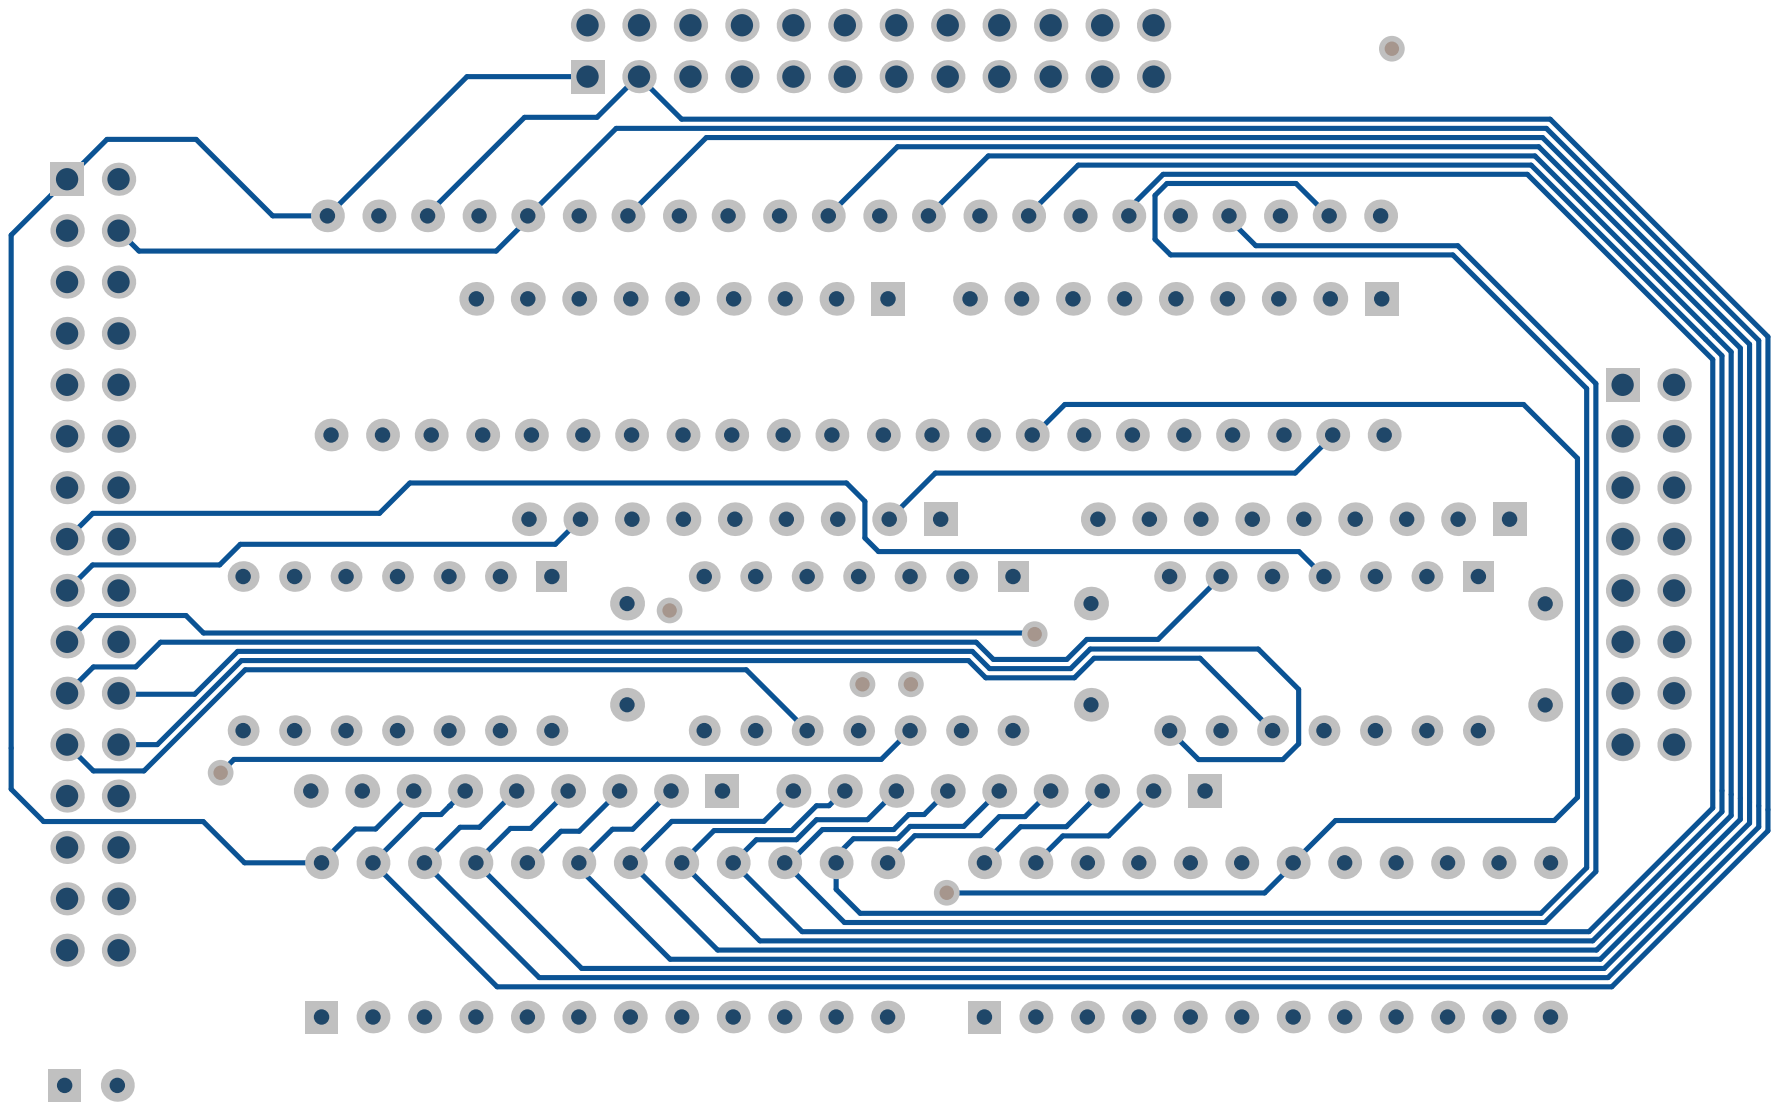
[picture p93: page 8]

# Bill of Materials

## myCPU CSM

Description | Value | Q
Led 3mm Round | Blue | 21
Electrolytic capacitor 16v/50v | 10µF | 1
Ceramic capacitor | 100nF | 3
Led 3mm Round | Red | 1
Hex inverters | 74xx04 | 3
Pin Header, THT, pitch 2.54mm, Dual Row, Vertical | 16p | 1
Pin Header, THT, pitch 2.54mm, Dual Row, Vertical | 32p | 1
Pin Header, THT, pitch 2.54mm, Dual Row, Vertical | 24p | 1
Resistor array 8 elements,9 pins | 3.3K | 3
Resistor array 8 elements,9 pins | 330 | 3
DIP switch 12 positions | 12p | 2

# Assembly List

## myCPU CSM

Designator | Description | Value
AI | Led 3mm Round | Blue
AO | Led 3mm Round | Blue
BI | Led 3mm Round | Blue
BO | Led 3mm Round | Blue
C1 | Electrolytic capacitor 16v/50v | 10µF
C2 | Ceramic capacitor | 100nF
C3 | Ceramic capacitor | 100nF
C4 | Ceramic capacitor | 100nF
CI | Led 3mm Round | Blue
CO | Led 3mm Round | Blue
EO | Led 3mm Round | Blue
FI | Led 3mm Round | Blue
HLT | Led 3mm Round | Red
IC1 | Hex inverters | 74xx04
IC2 | Hex inverters | 74xx04
IC3 | Hex inverters | 74xx04
II | Led 3mm Round | Blue
IO | Led 3mm Round | Blue
MI | Led 3mm Round | Blue
OI | Led 3mm Round | Blue
P1 | Pin Header, THT, pitch 2.54mm, Dual Row, Vertical | 16p
P2 | Pin Header, THT, pitch 2.54mm, Dual Row, Vertical | 32p
P3 | Pin Header, THT, pitch 2.54mm, Dual Row, Vertical | 24p
PE | Led 3mm Round | Blue
PI | Led 3mm Round | Blue
PO | Led 3mm Round | Blue
RI | Led 3mm Round | Blue
RN1 | Resistor array 8 elements,9 pins | 3.3K
RN2 | Resistor array 8 elements,9 pins | 3.3K
RN3 | Resistor array 8 elements,9 pins | 3.3K
RN4 | Resistor array 8 elements,9 pins | 330
RN5 | Resistor array 8 elements,9 pins | 330
RN6 | Resistor array 8 elements,9 pins | 330
RO | Led 3mm Round | Blue
SI | Led 3mm Round | Blue
SO | Led 3mm Round | Blue
SU | Led 3mm Round | Blue
SW1 | DIP switch 12 positions | 12p
SW2 | DIP switch 12 positions | 12p
UN | Led 3mm Round | Blue
