mylabpcb/myCPU/Docs/myCPU_EEProm Programmer_AT28C64_module_full.pdf

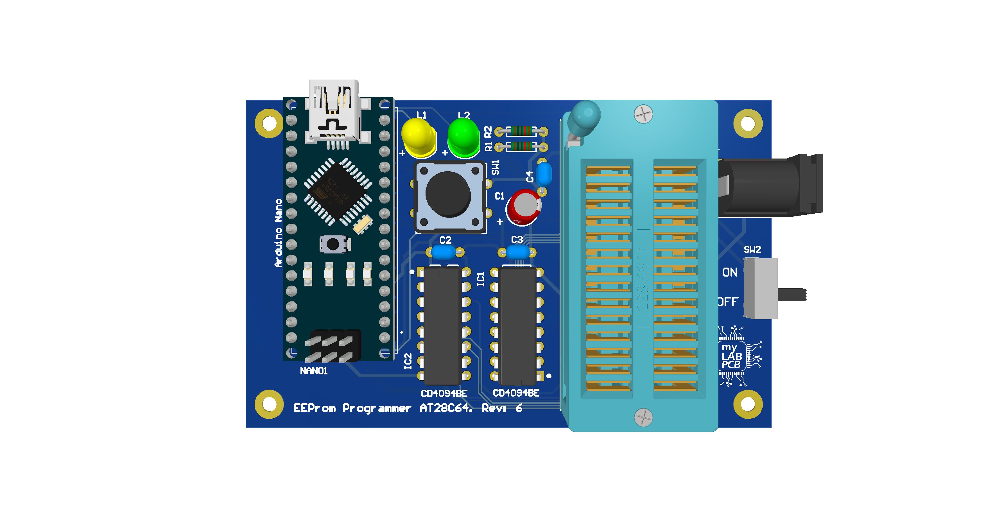
[picture p101: page 1]

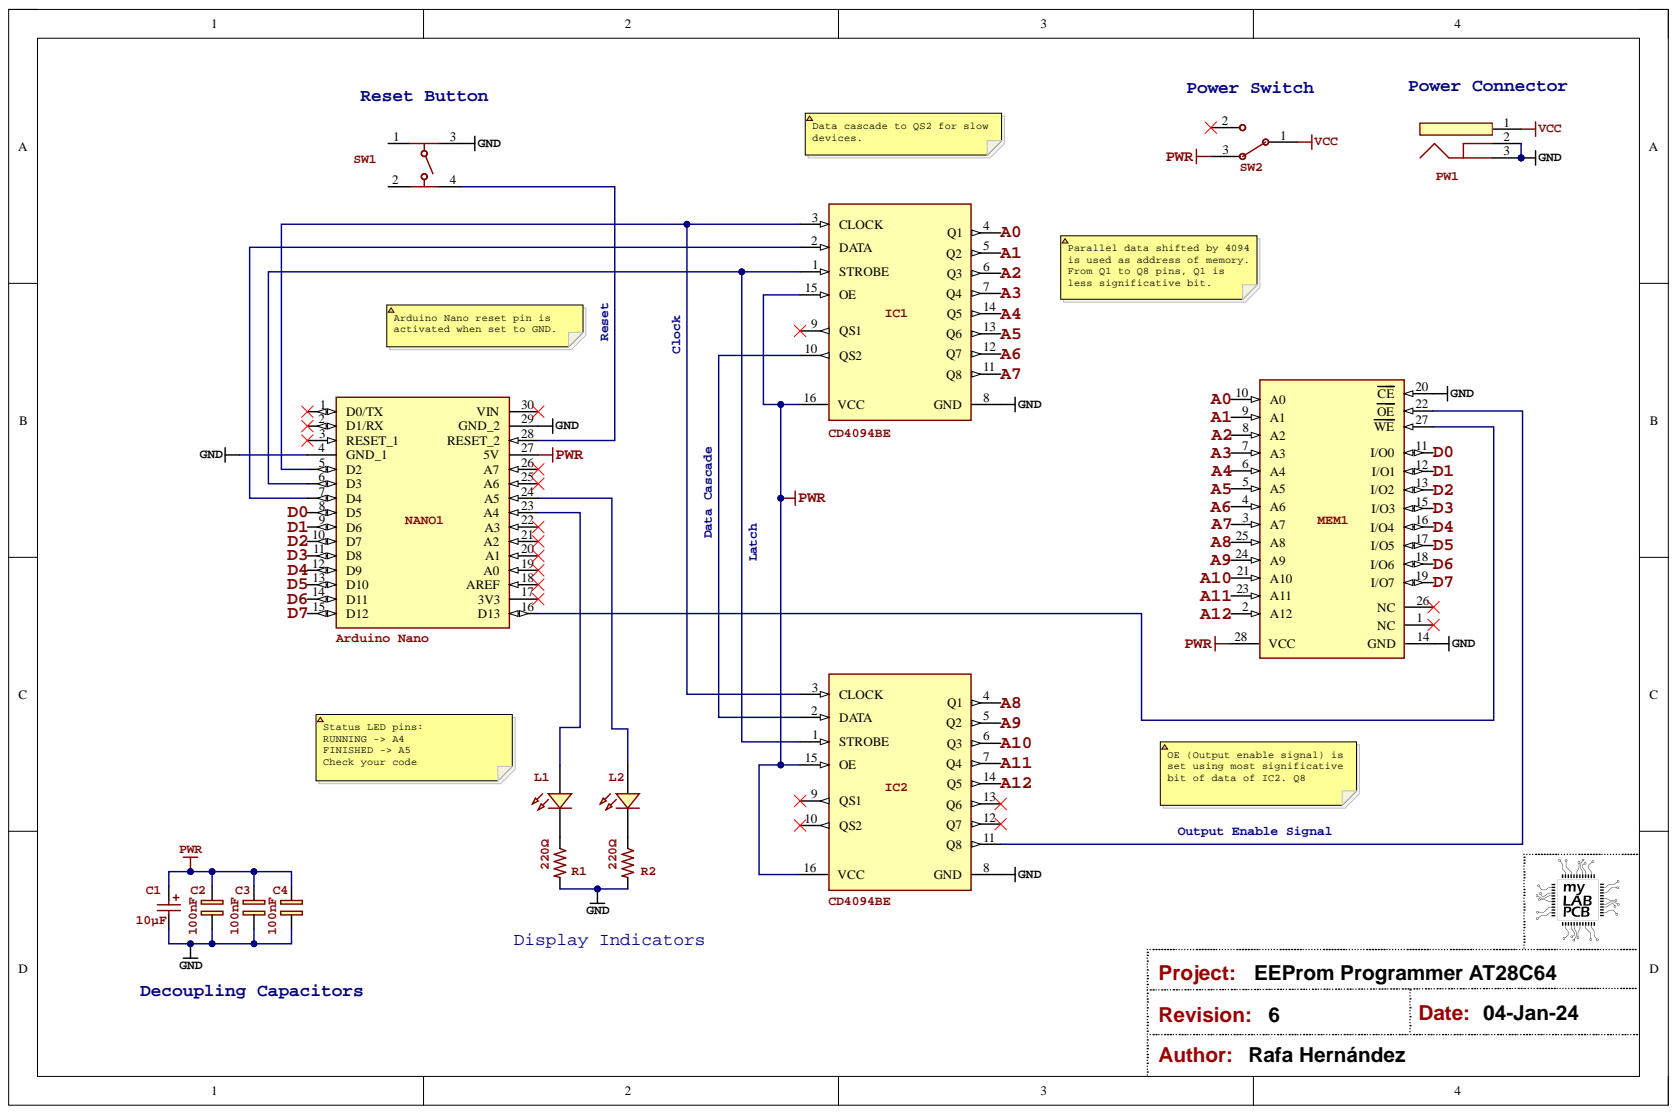
[picture p102: page 3]

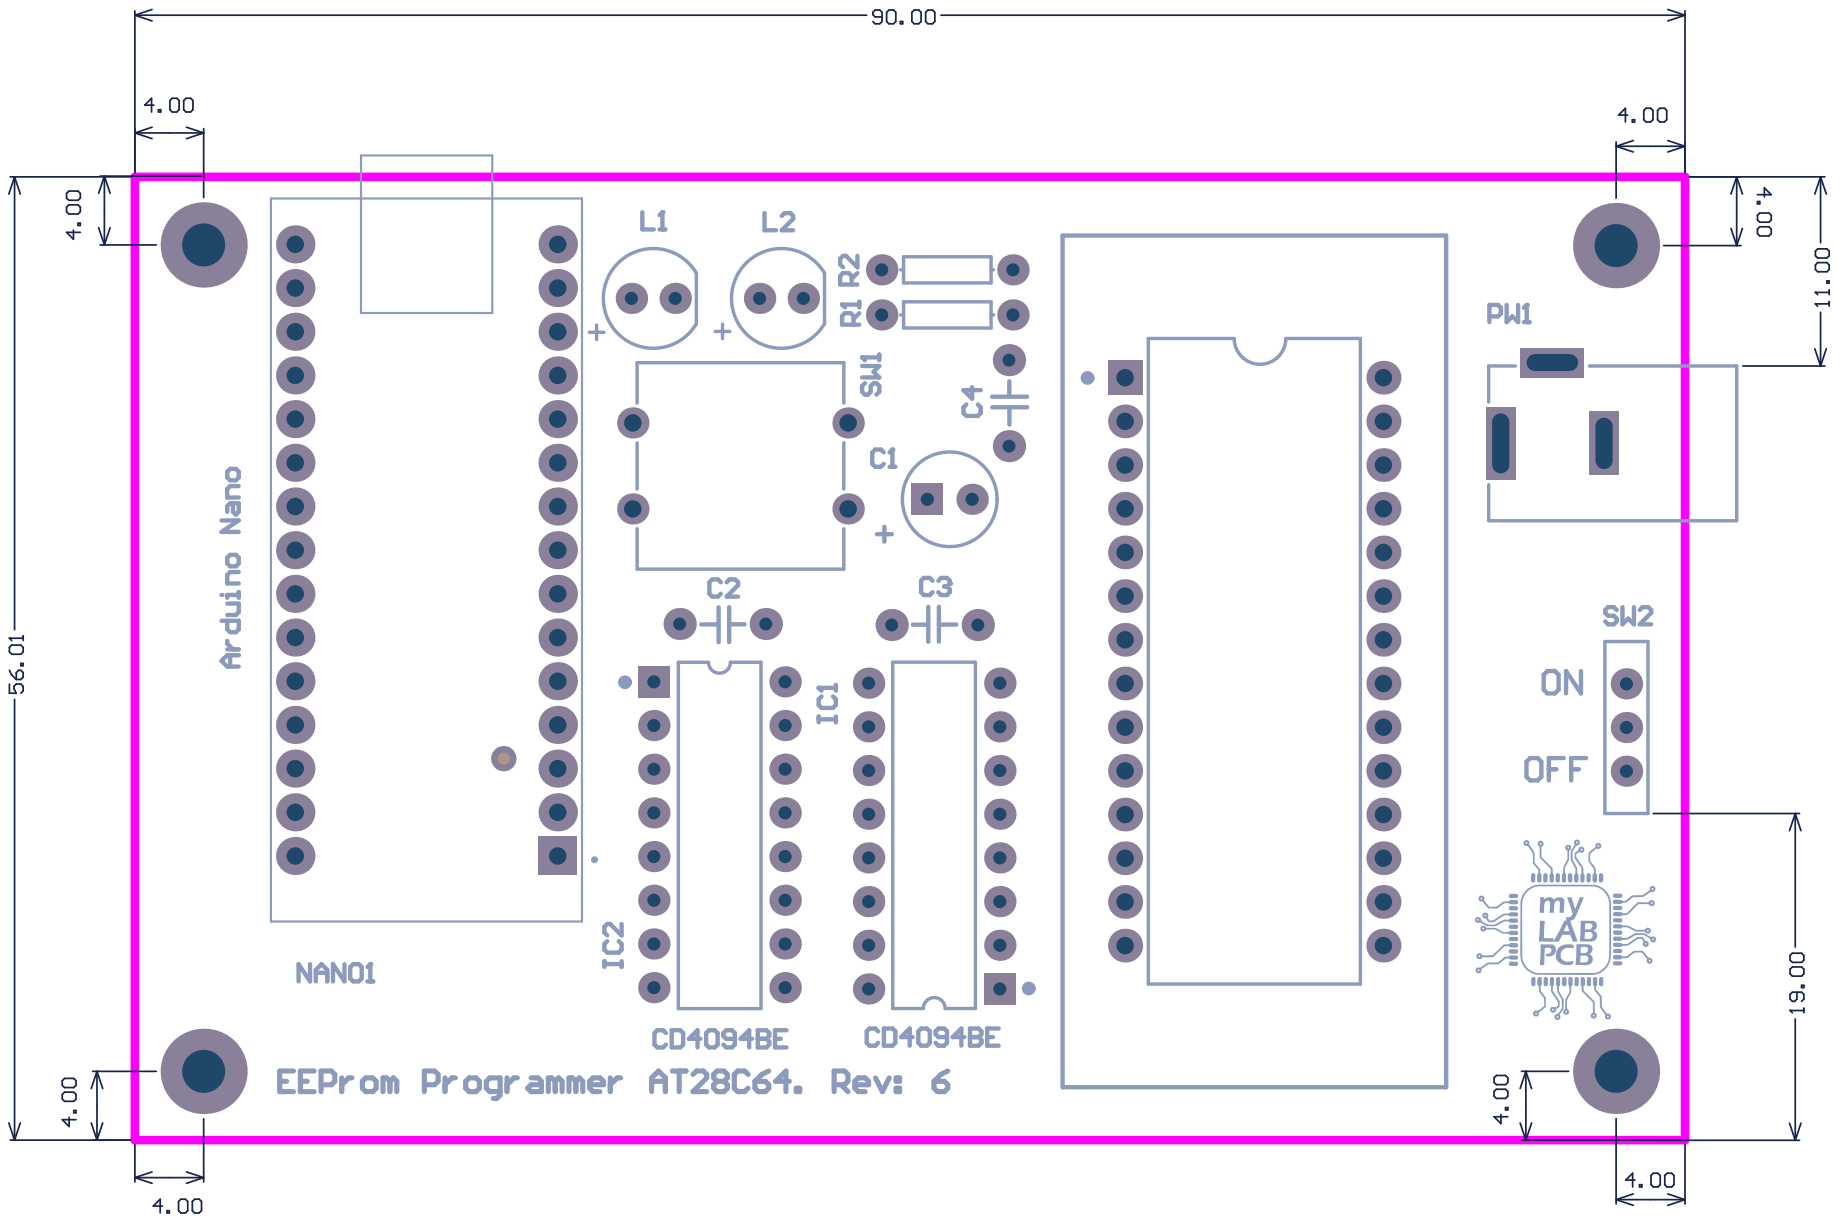
[picture p103: page 4]

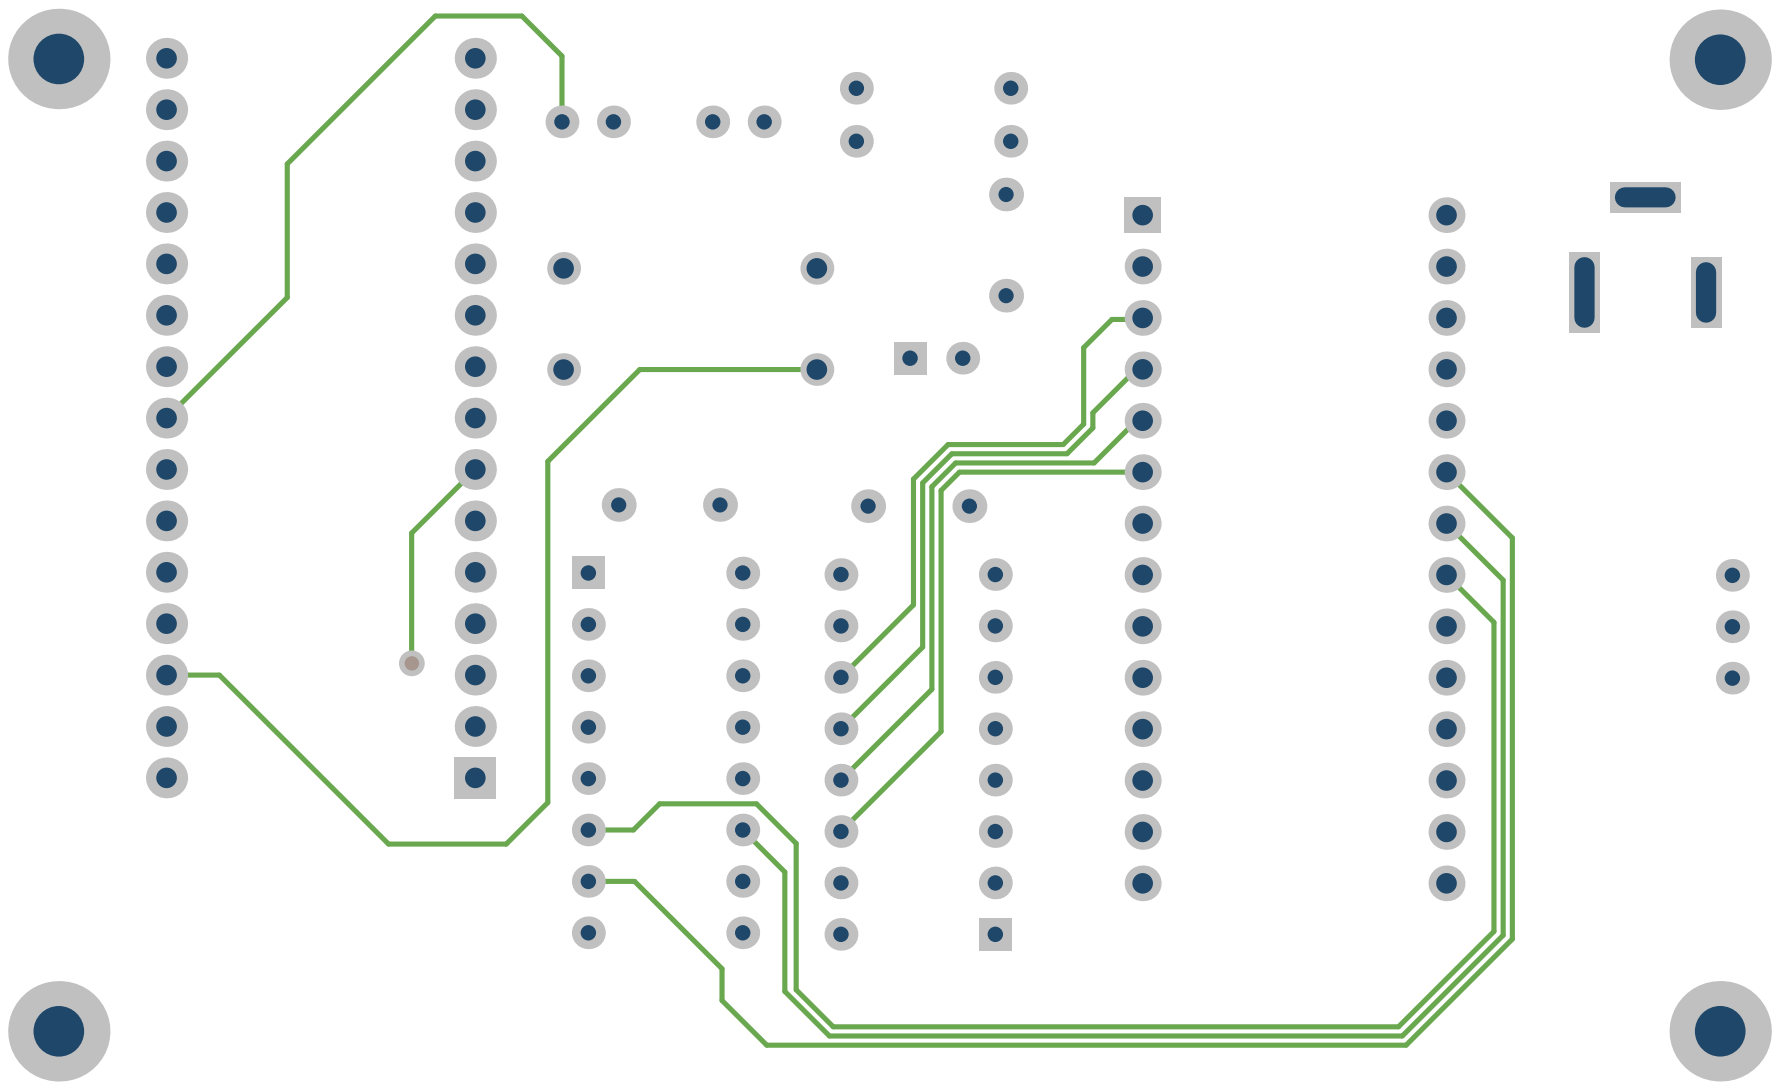
[picture p104: page 5]

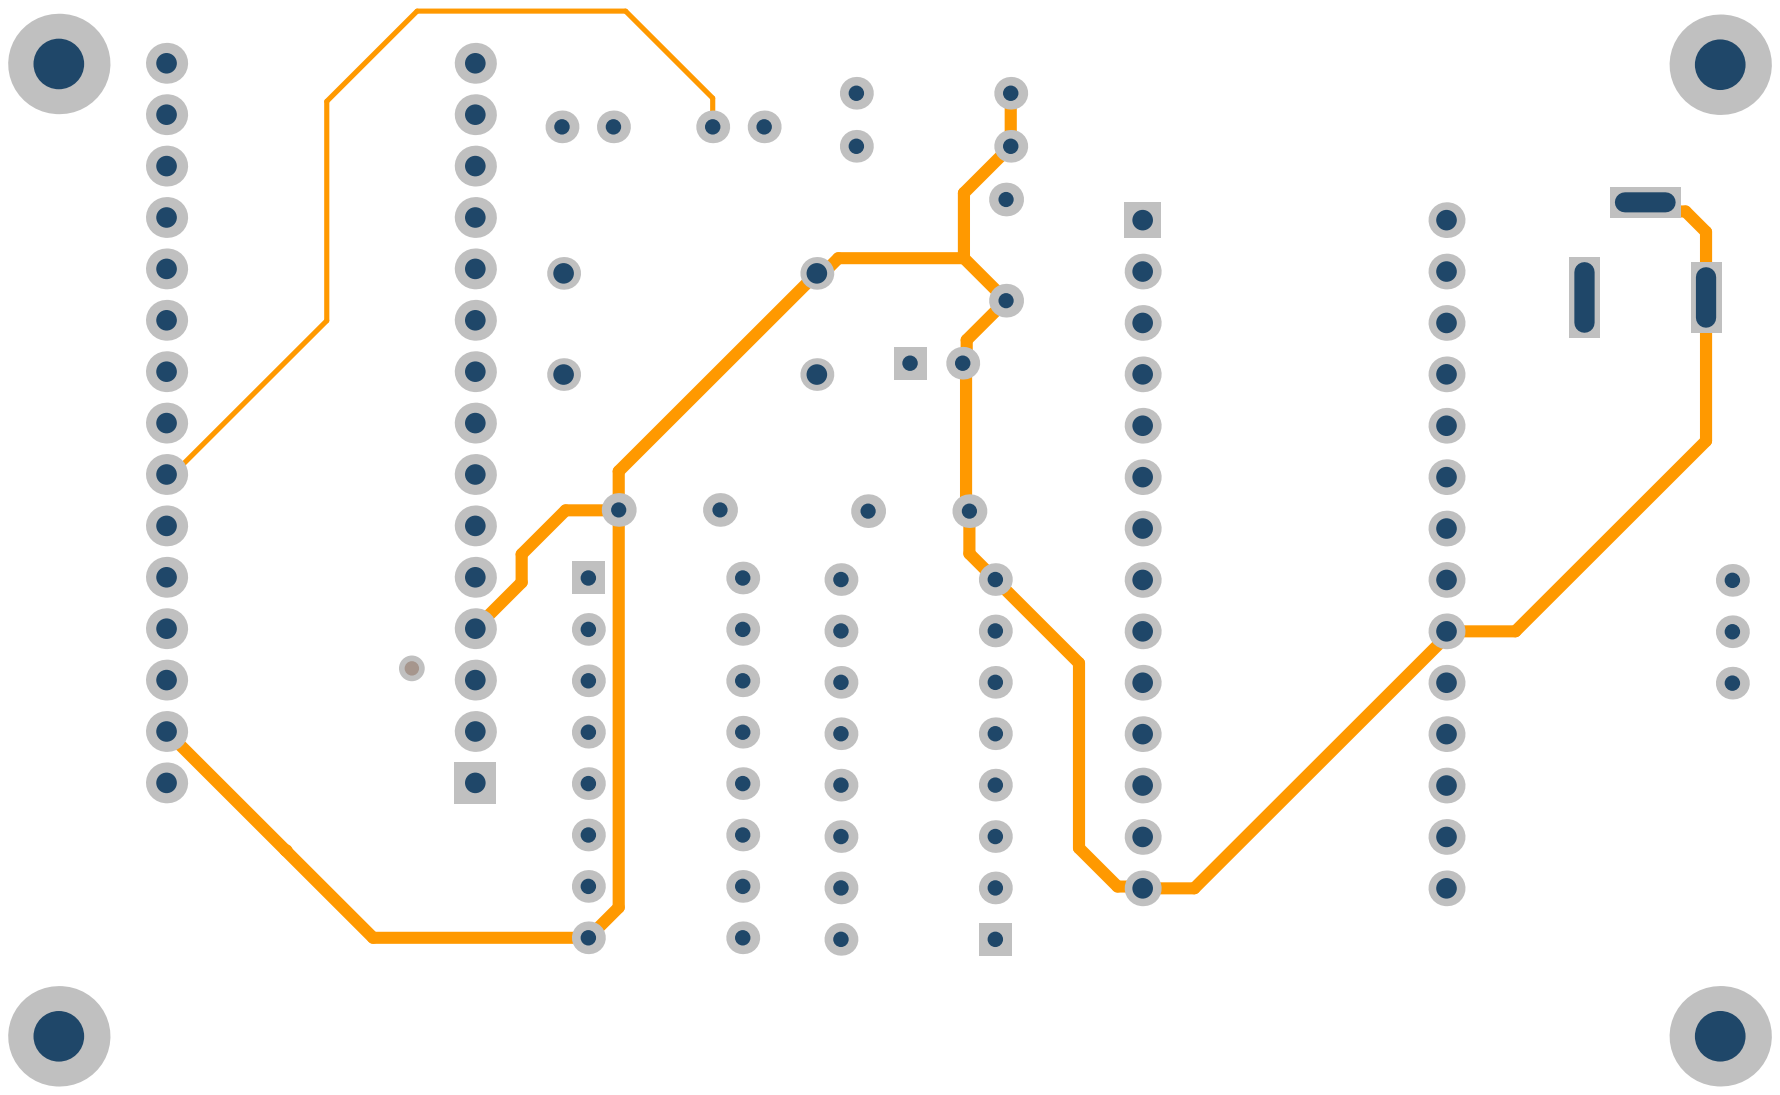
[picture p105: page 6]

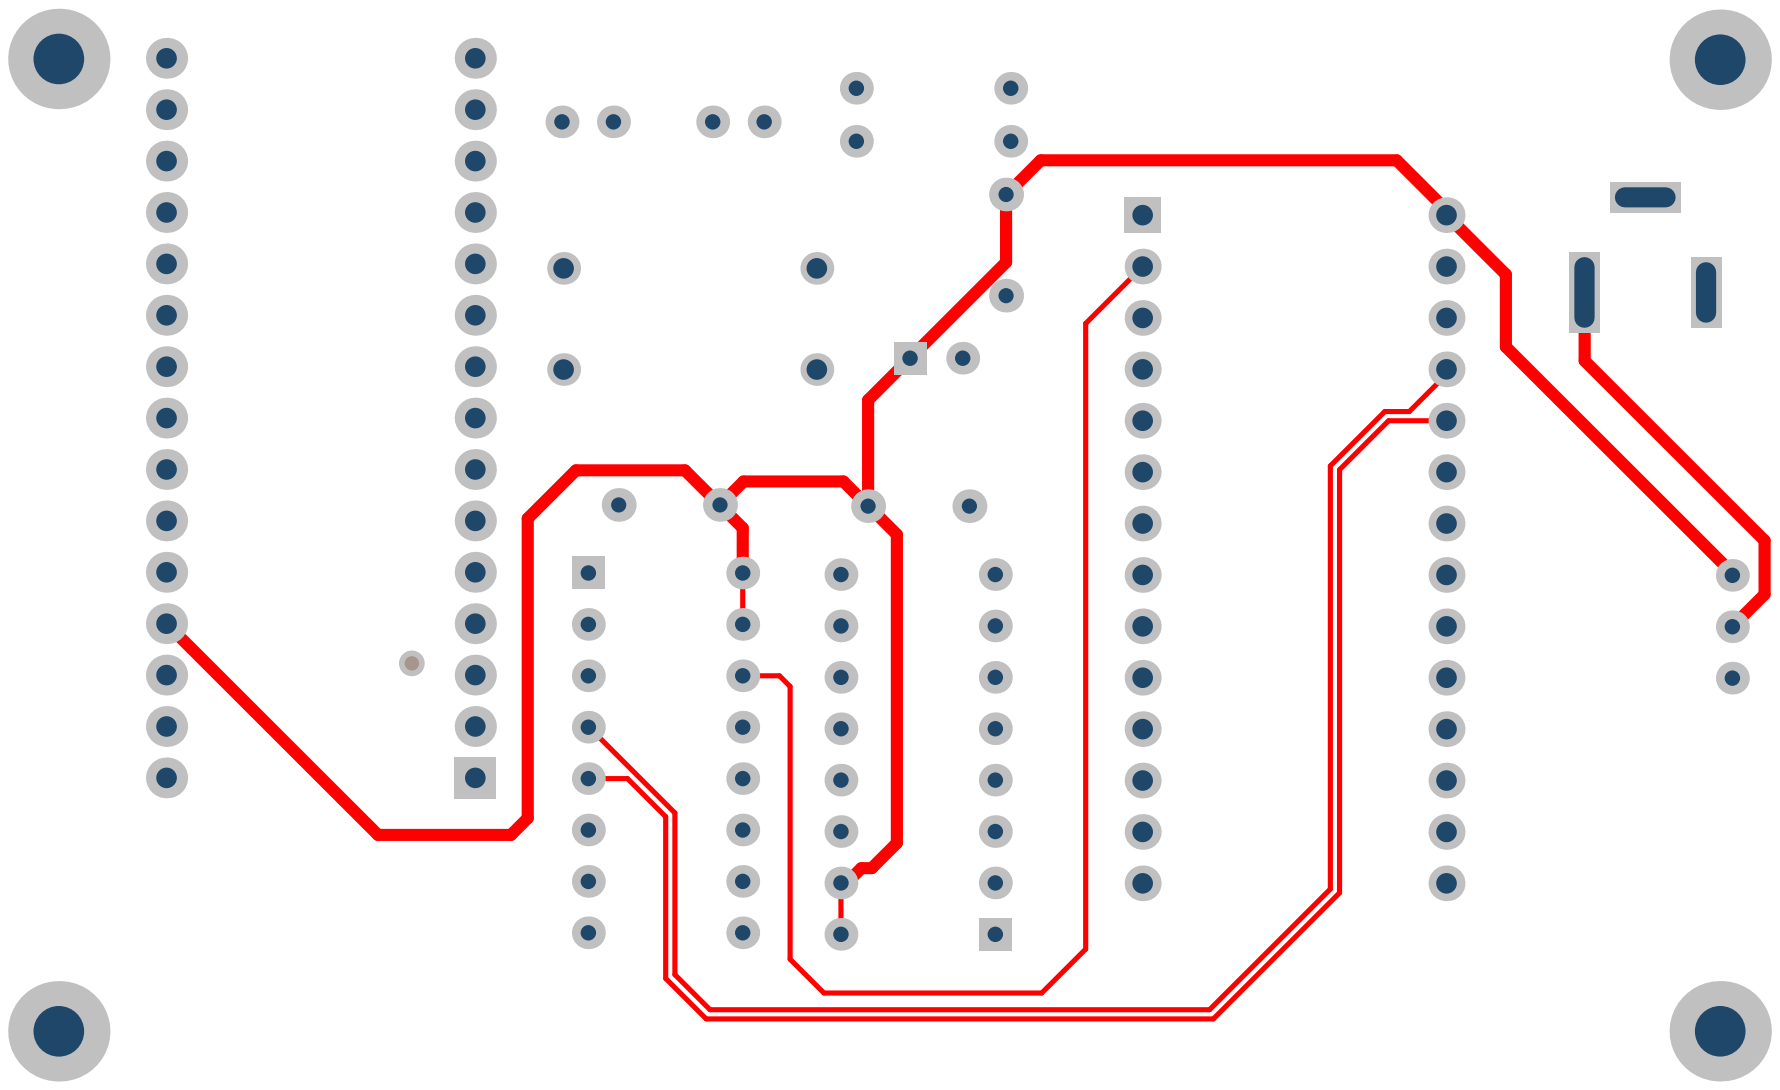
[picture p106: page 7]

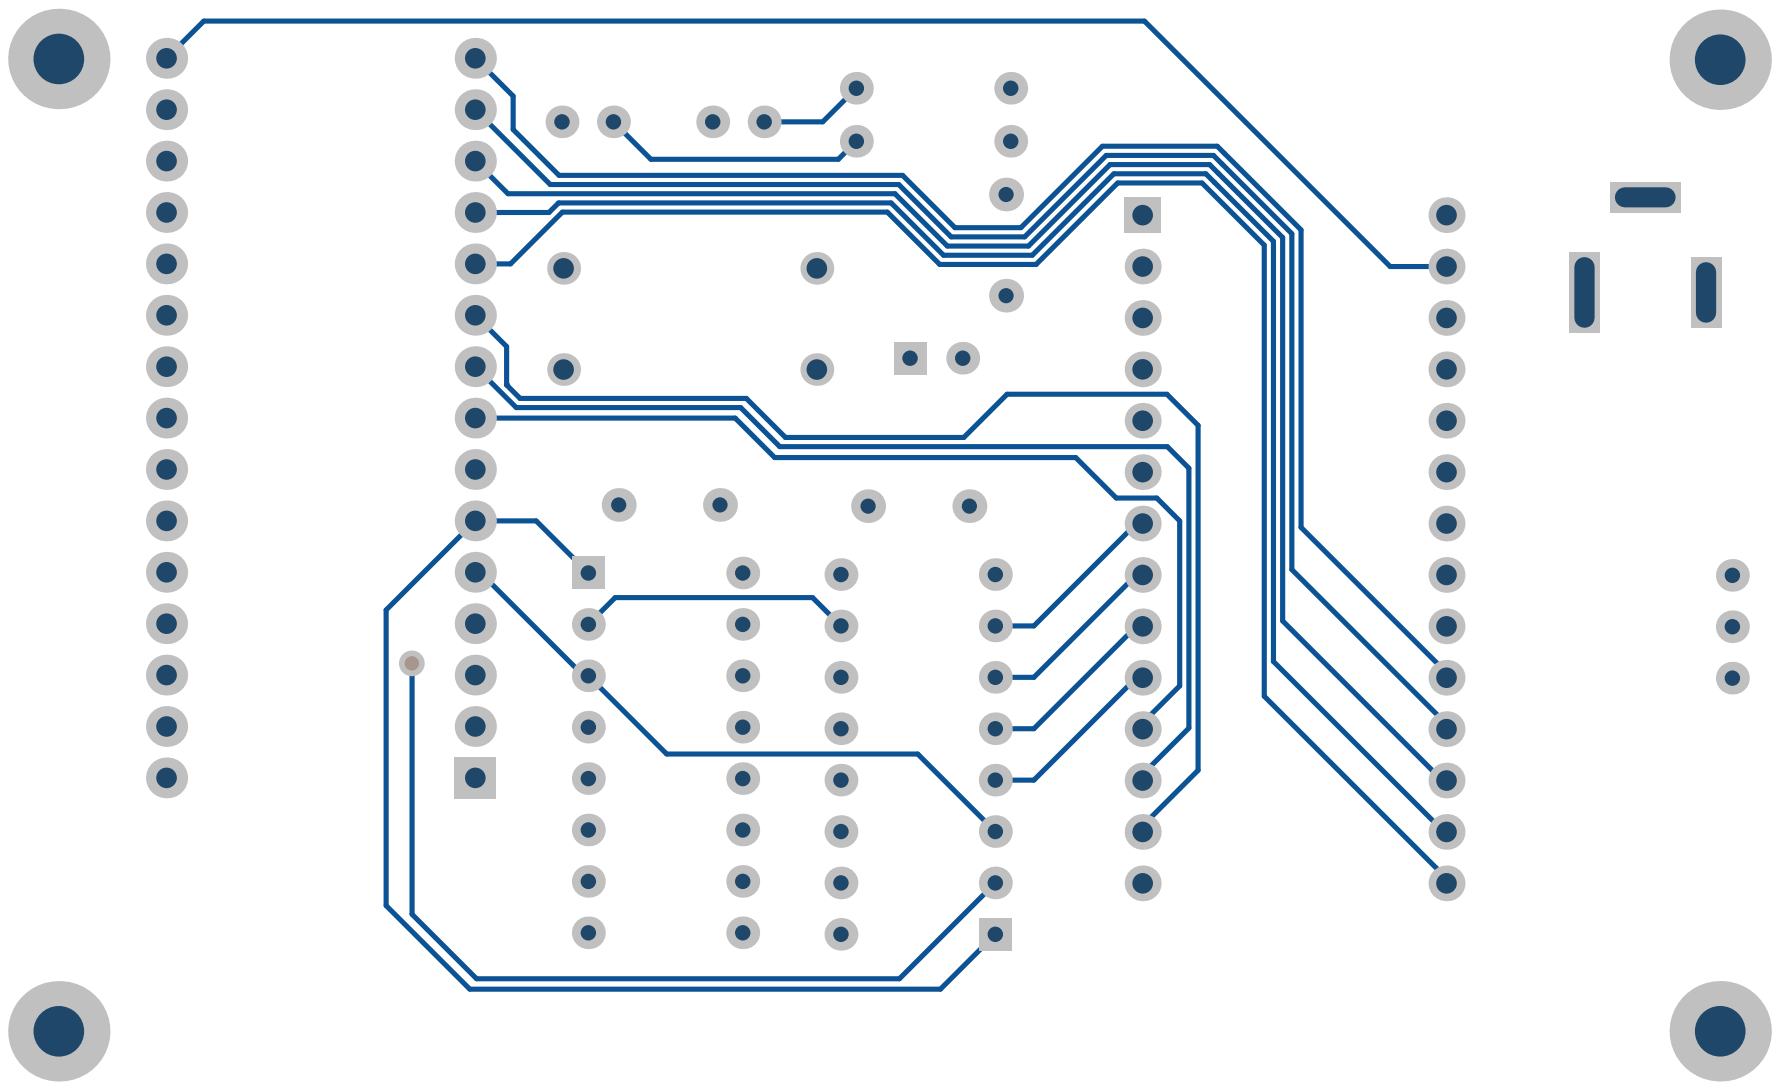
[picture p107: page 8]

# Bill of Materials

# EEProm Programmer AT28C64

Description | Value | Q
Electrolytic capacitor 16v/50v | 10µF | 1
Ceramic capacitor | 100nF | 3
CMOS 8 bits shift register,3 state | CD4094 | 2
Led 5mm Round | Yellow | 1
Led 5mm Round | Green | 1
AT28C64 ZIF Socket | ZIF socket 28W | 1
Arduino NANO v3 | v3 | 1
DC Power Jack, 2.5 A, 2mm Center Pin, 3 Position | 2mm 3p | 1
Resistor Axial | 220 | 2
Tactile button 12 mm | 12mm | 1
Mini slide switch 2 pos, 3 pins | SP2T | 1

# Assembly List

## EEProm Programmer AT28C64

Designator | Description | Value
C1 | Electrolytic capacitor 16v/50v | 10µF
C2 | Ceramic capacitor | 100nF
C3 | Ceramic capacitor | 100nF
C4 | Ceramic capacitor | 100nF
IC1 | CMOS 8 bits shift register,3 state | CD4094
IC2 | CMOS 8 bits shift register,3 state | CD4094
L1 | Led 5mm Round | Yellow
L2 | Led 5mm Round | Green
MEM1 | AT28C64 ZIF Socket | ZIF socket 28W
NANO1 | Arduino NANO v3 | v3
PW1 | DC Power Jack, 2.5 A, 2mm Center Pin, 3 Position | 2mm 3p
R1 | Resistor Axial | 220
R2 | Resistor Axial | 220
SW1 | Tactile button 12 mm | 12mm
SW2 | Mini slide switch 2 pos, 3 pins | SP2T
