mylabpcb/myCPU/Docs/myCPU_Program_Counter_module_full.pdf

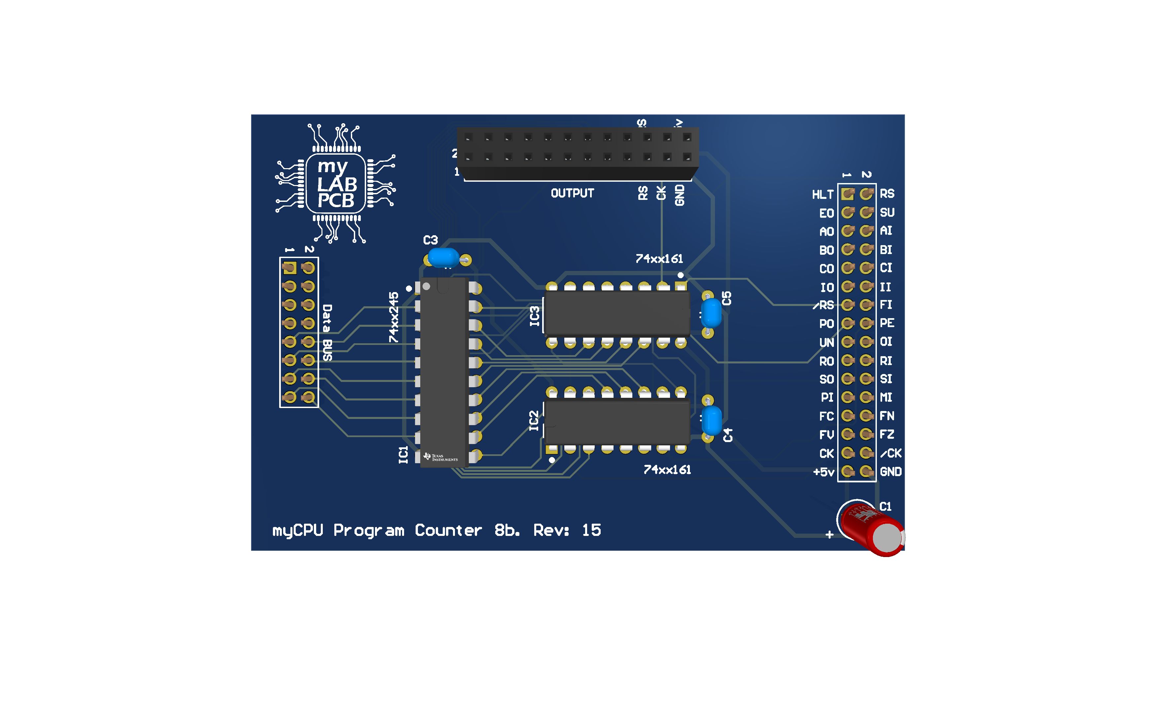
[picture p122: page 1]

Control BUS Connector | OUTPUT Connector | Data BUS Connector

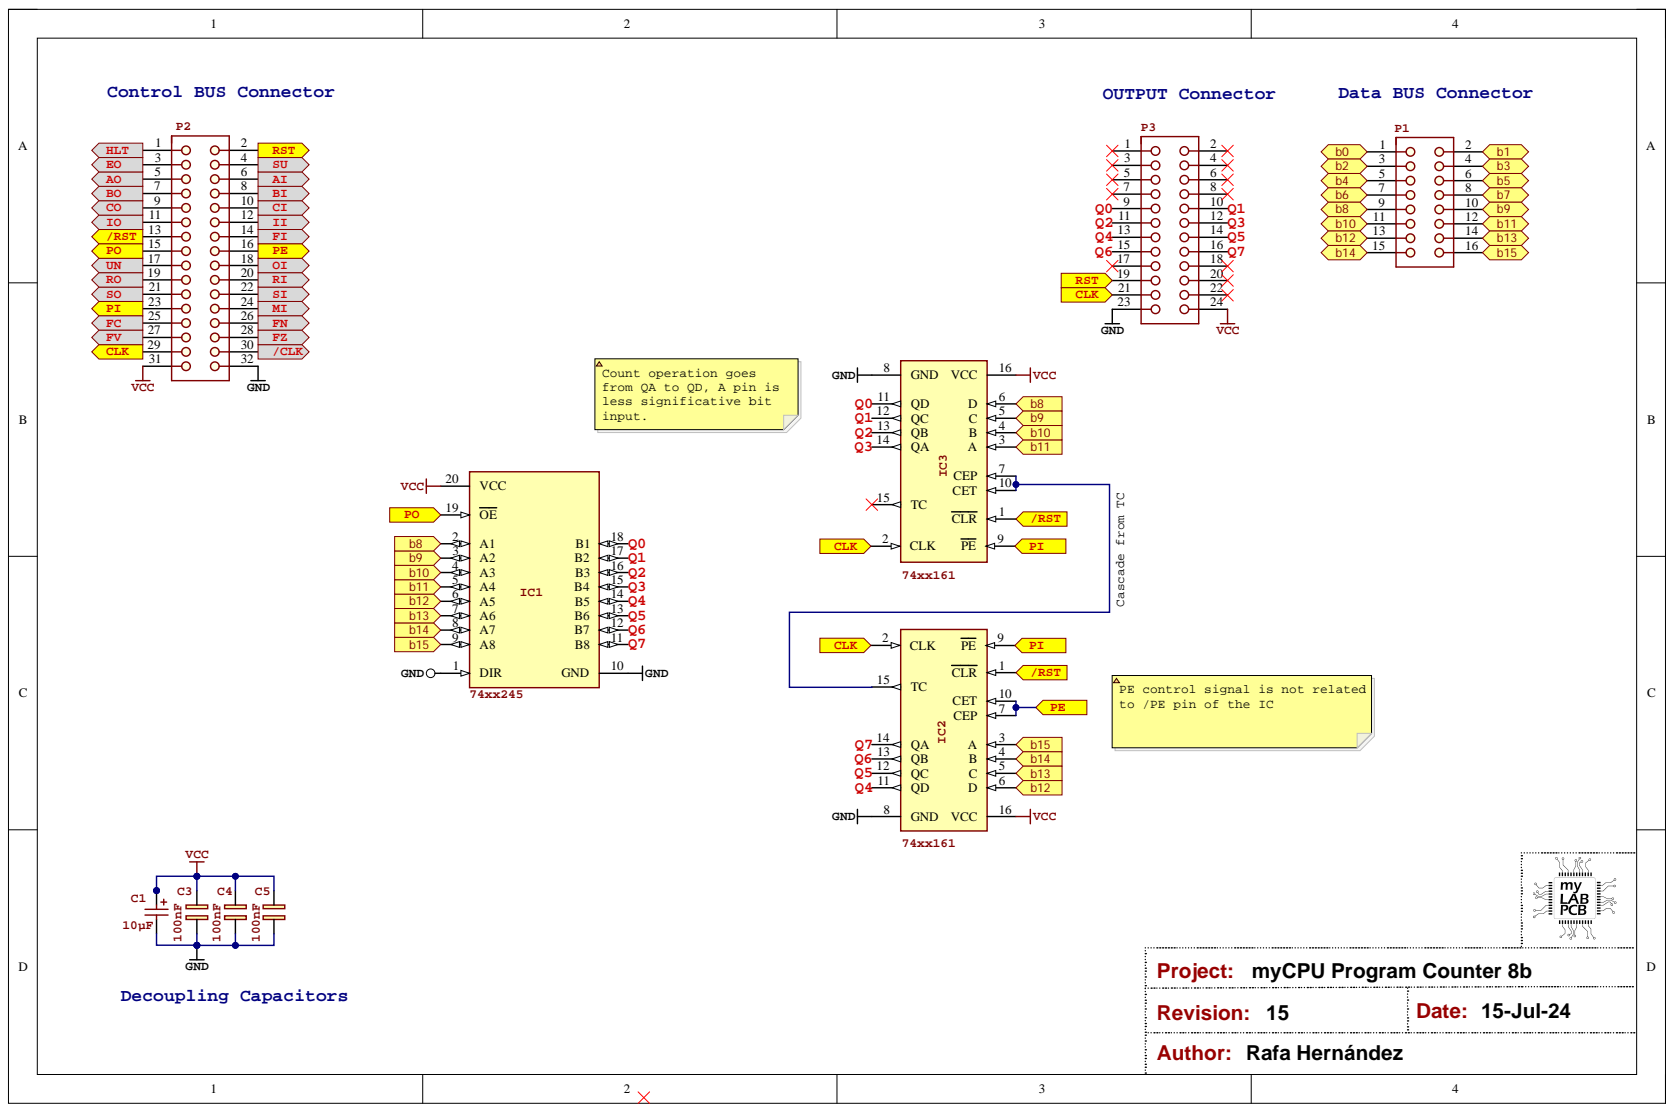
[picture p123: page 3]

Count operation goes
from QA to QD, A pin is
less significative bit
input.

PE control signal is not related
to /PE pin of the IC

Project: myCPU Program Counter 8b

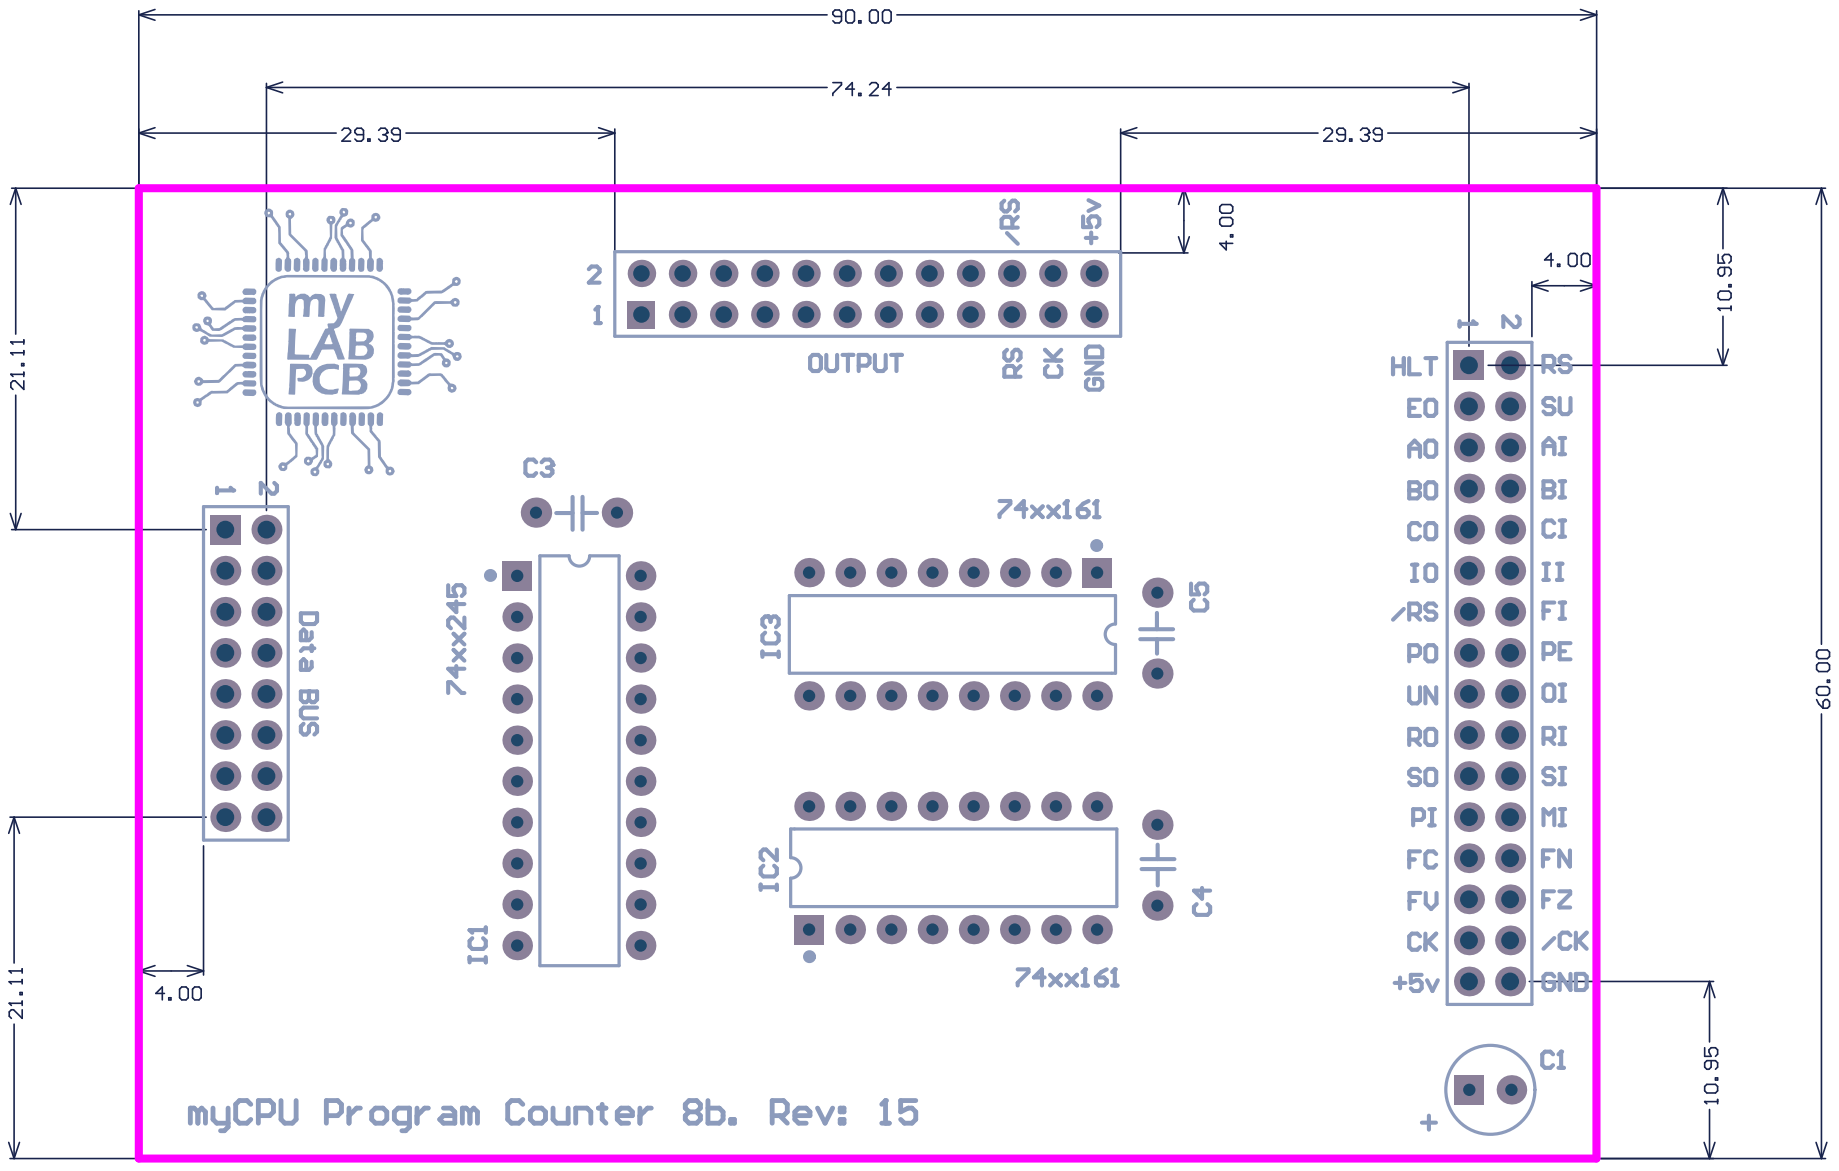
[picture p124: page 4]

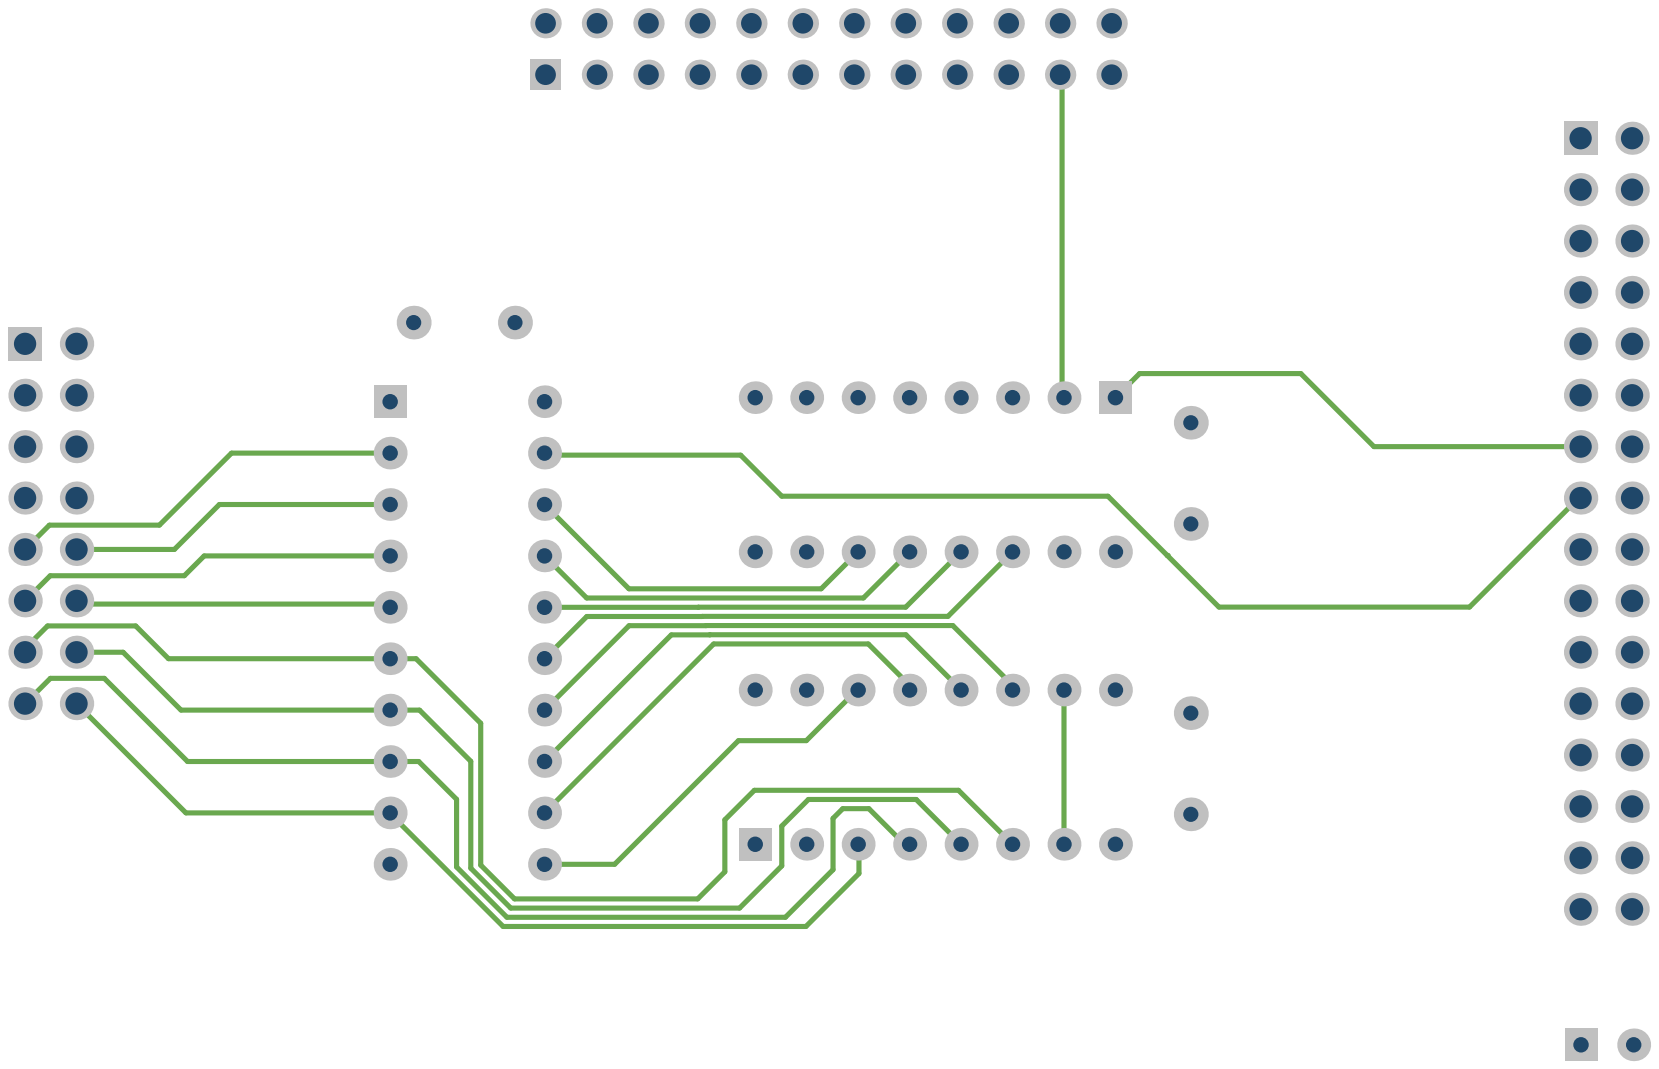
[picture p125: page 5]

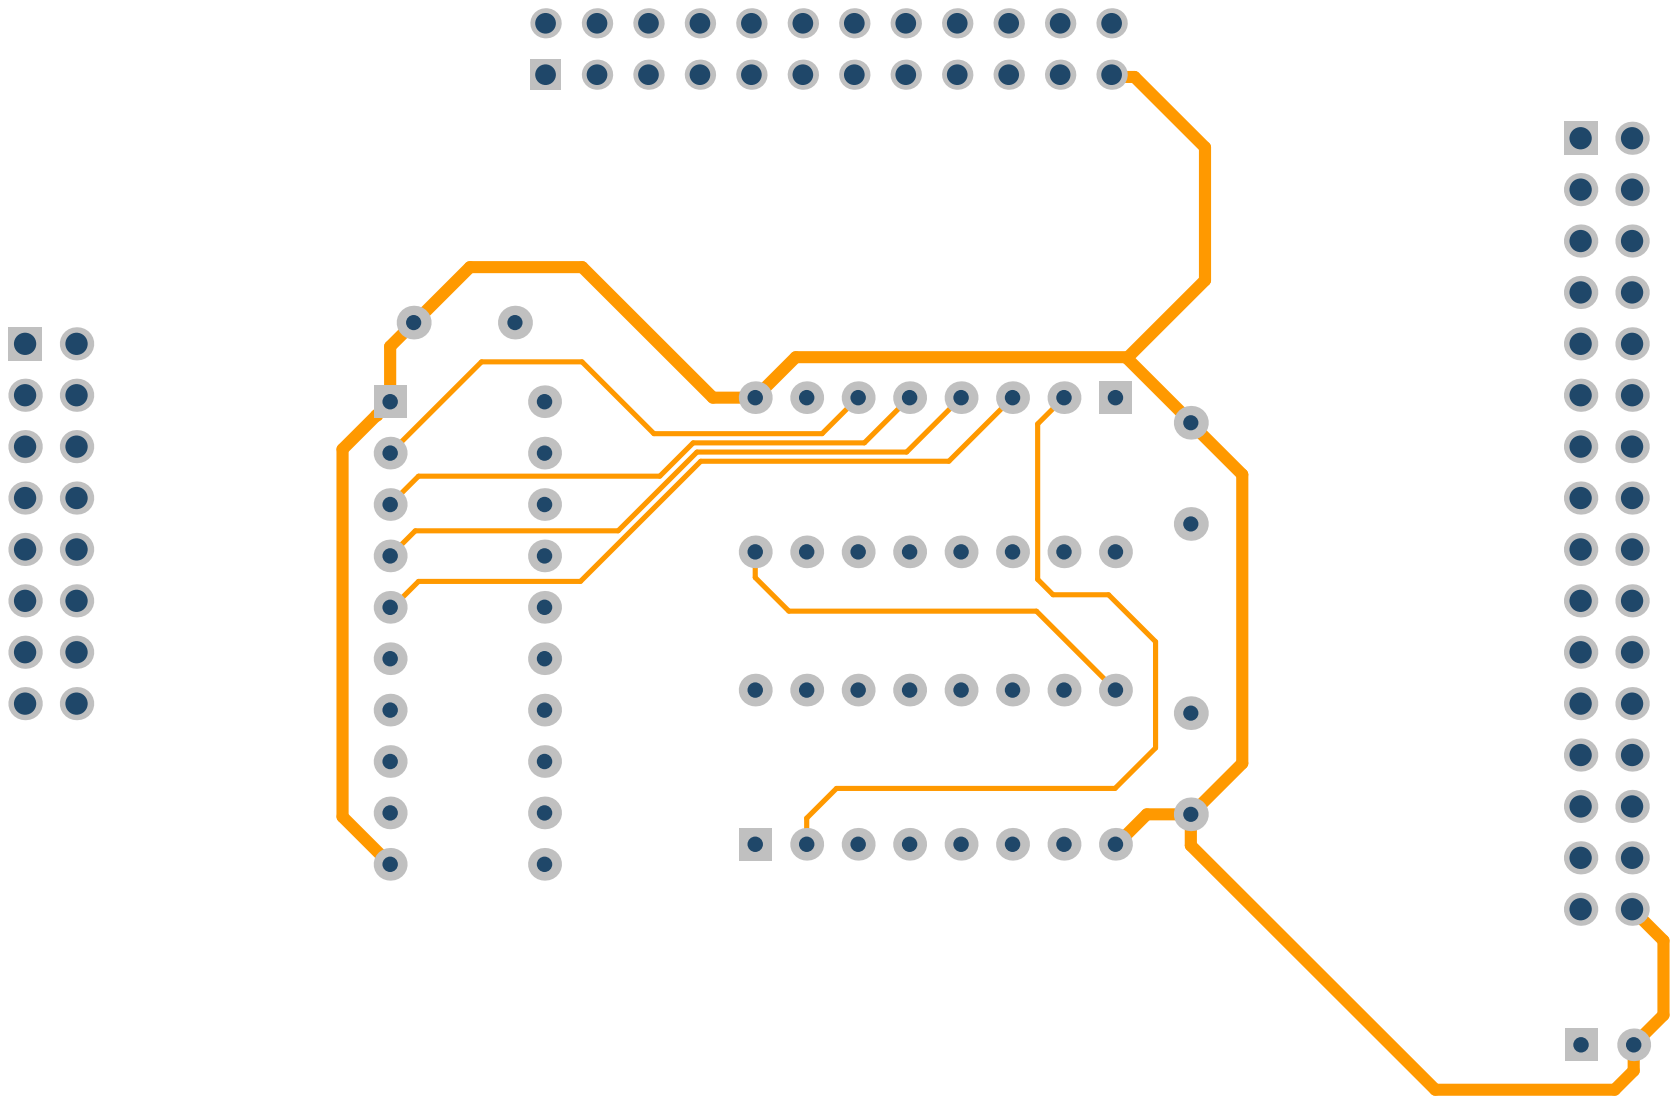
[picture p126: page 6]

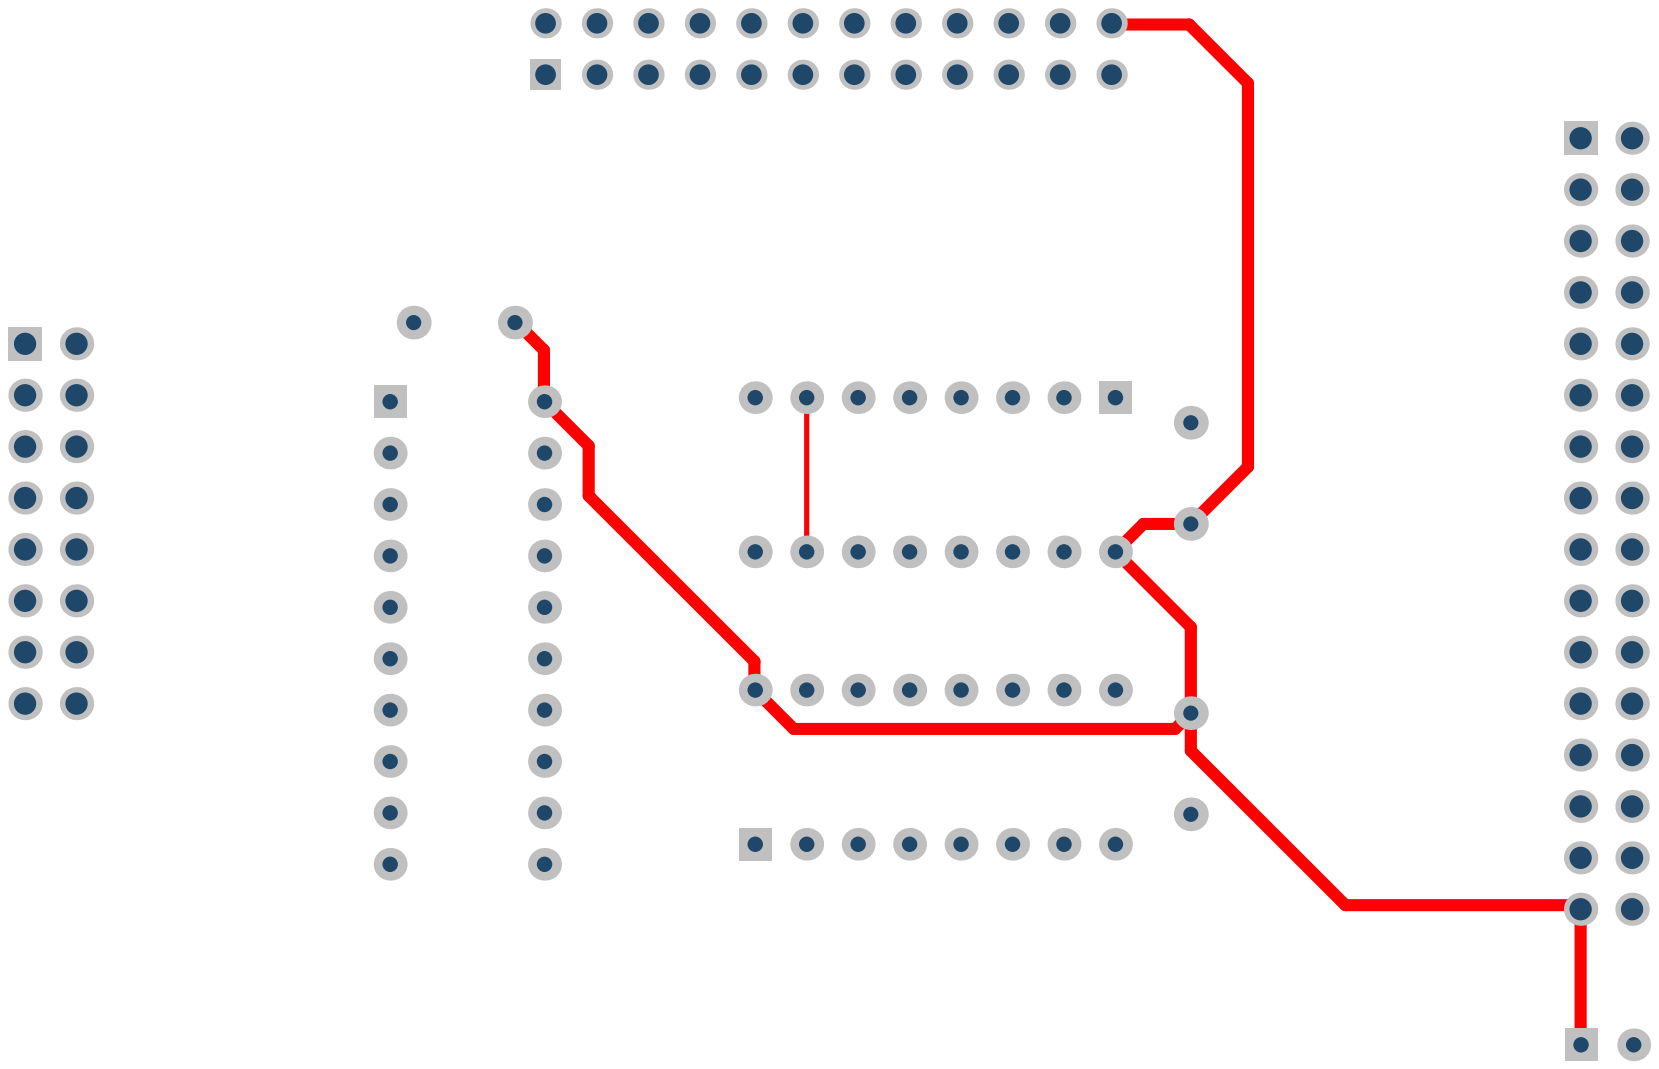
[picture p127: page 7]

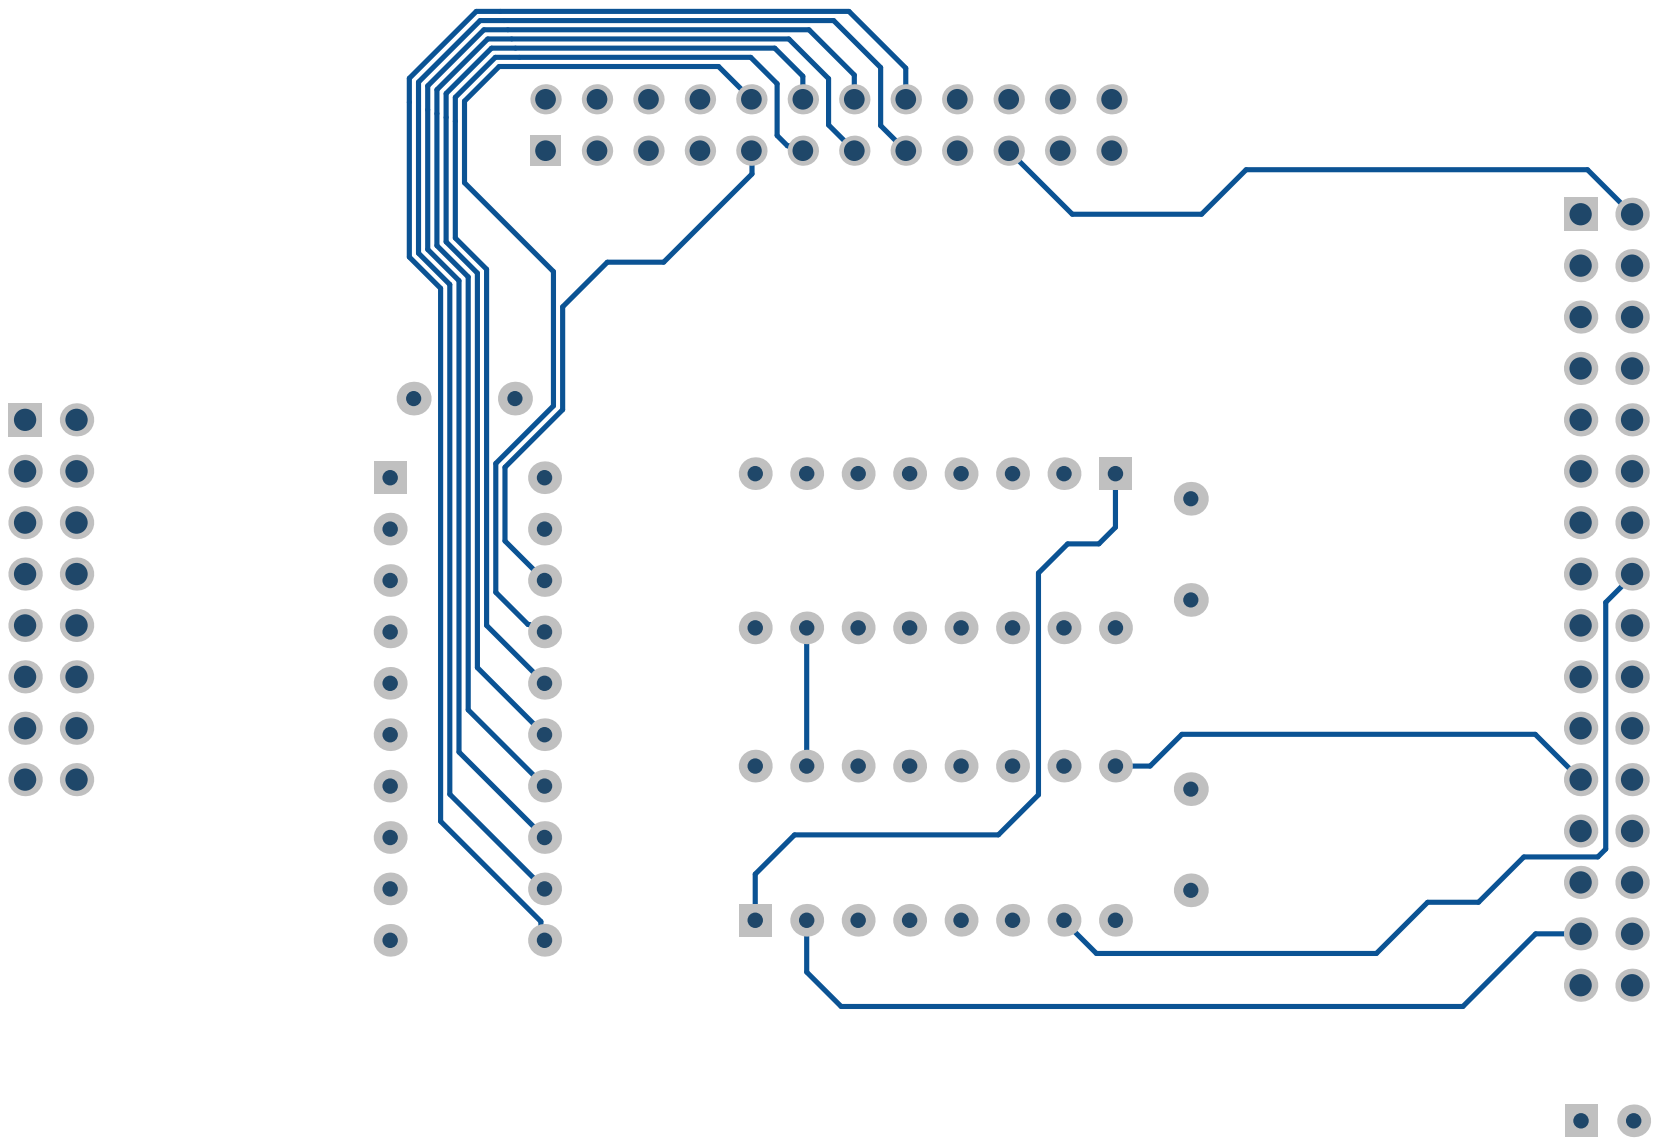
[picture p128: page 8]

# Bill of Materials

# myCPU Program Counter 8b

Description | Value | Q
Electrolytic capacitor 16v/50v | 10µF | 1
Ceramic capacitor | 100nF | 3
Non inverting bus transceiver | 74xx245 | 1
4-Bit sync counter | 74xx161 | 2
Pin Header, THT, pitch 2.54mm, Dual Row, Vertical | 16p | 1
Pin Header, THT, pitch 2.54mm, Dual Row, Vertical | 32p | 1
Socket Header, THT, pitch 2.54mm, Dual Row, Vertical | 24p | 1

# Assembly List

# myCPU Program Counter 8b

Designator | Description | Value
C1 | Electrolytic capacitor 16v/50v | 10µF
C3 | Ceramic capacitor | 100nF
C4 | Ceramic capacitor | 100nF
C5 | Ceramic capacitor | 100nF
IC1 | Non inverting bus transceiver | 74xx245
IC2 | 4-Bit sync counter | 74xx161
IC3 | 4-Bit sync counter | 74xx161
P1 | Pin Header, THT, pitch 2.54mm, Dual Row, Vertical | 16p
P2 | Pin Header, THT, pitch 2.54mm, Dual Row, Vertical | 32p
P3 | Socket Header, THT, pitch 2.54mm, Dual Row, Vertical | 24p
