mylabpcb/myCPU/Docs/myCPU_Protoboard_245_L_module_full.pdf

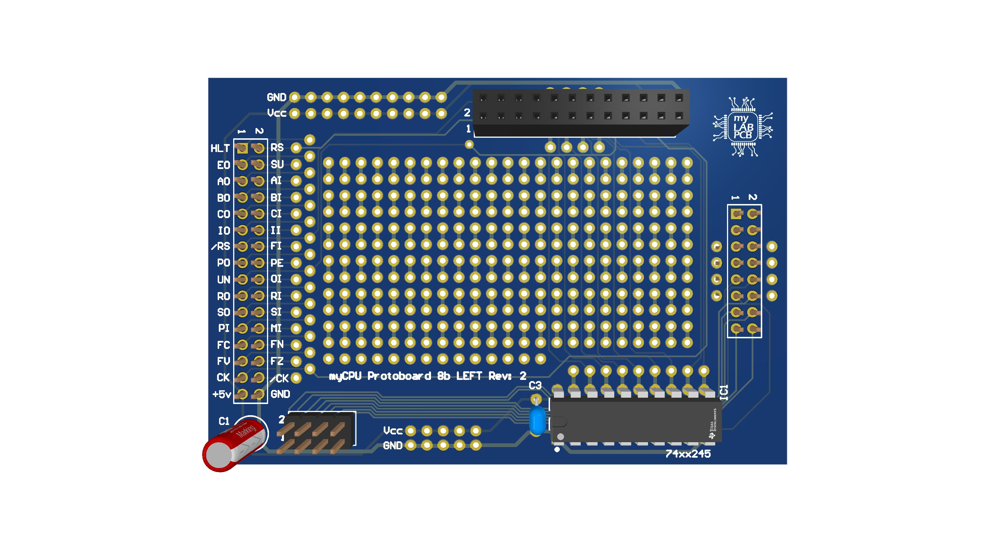
[picture p129: page 1]

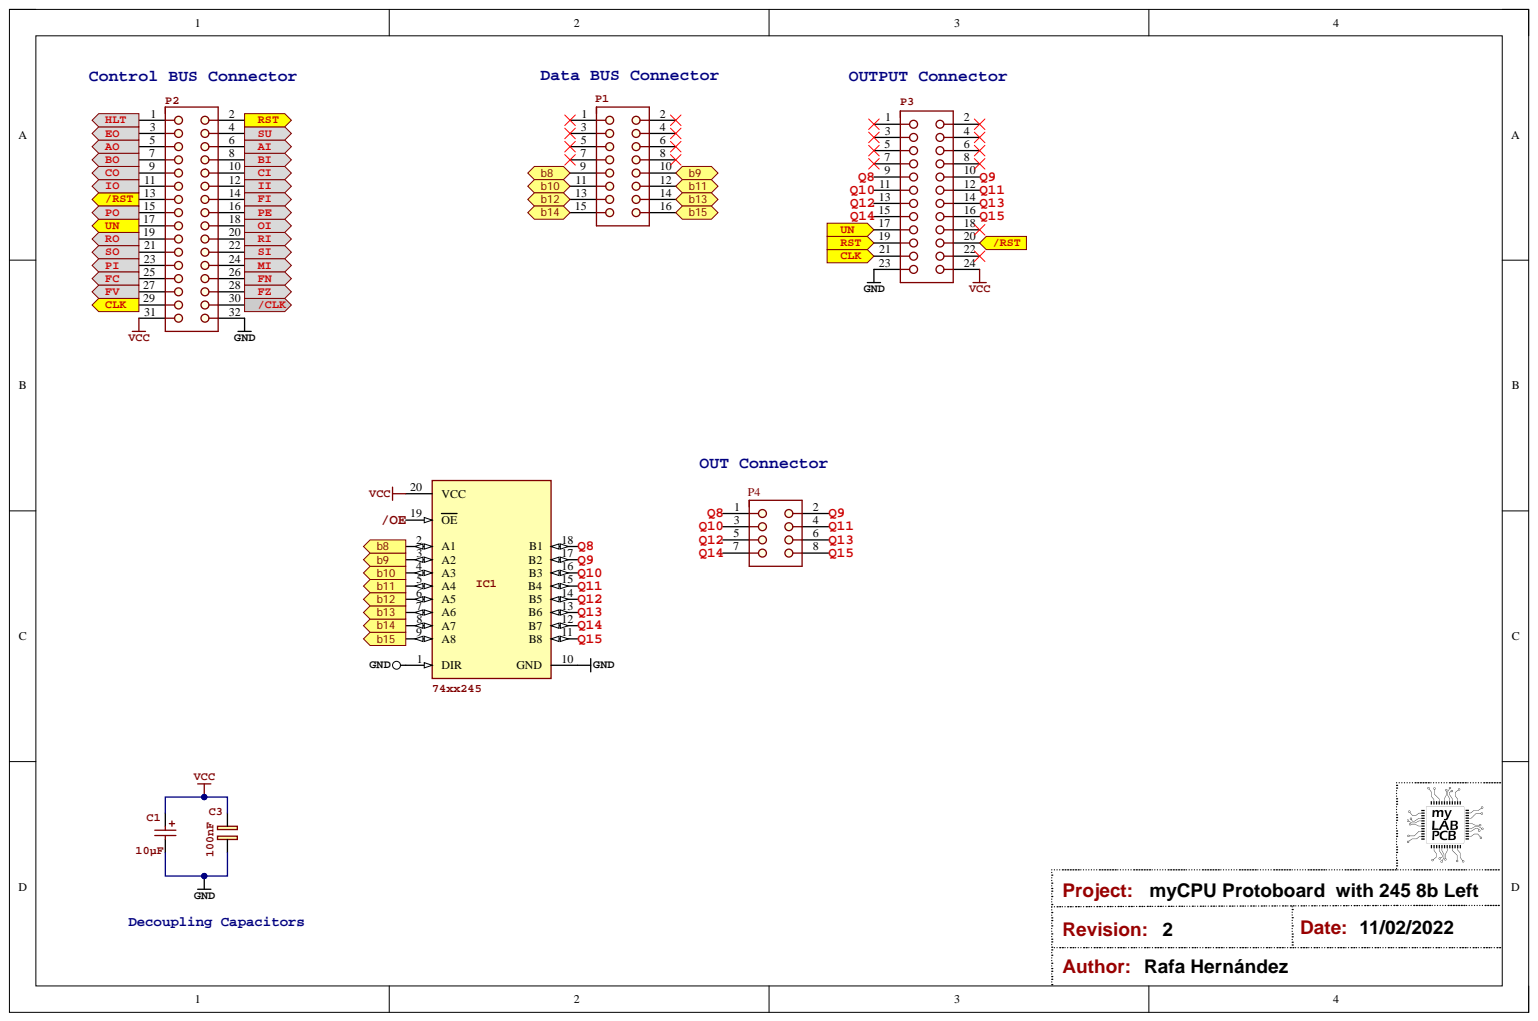
[picture p130: page 3]

Project: myCPU Protoboard with 245 8b Left

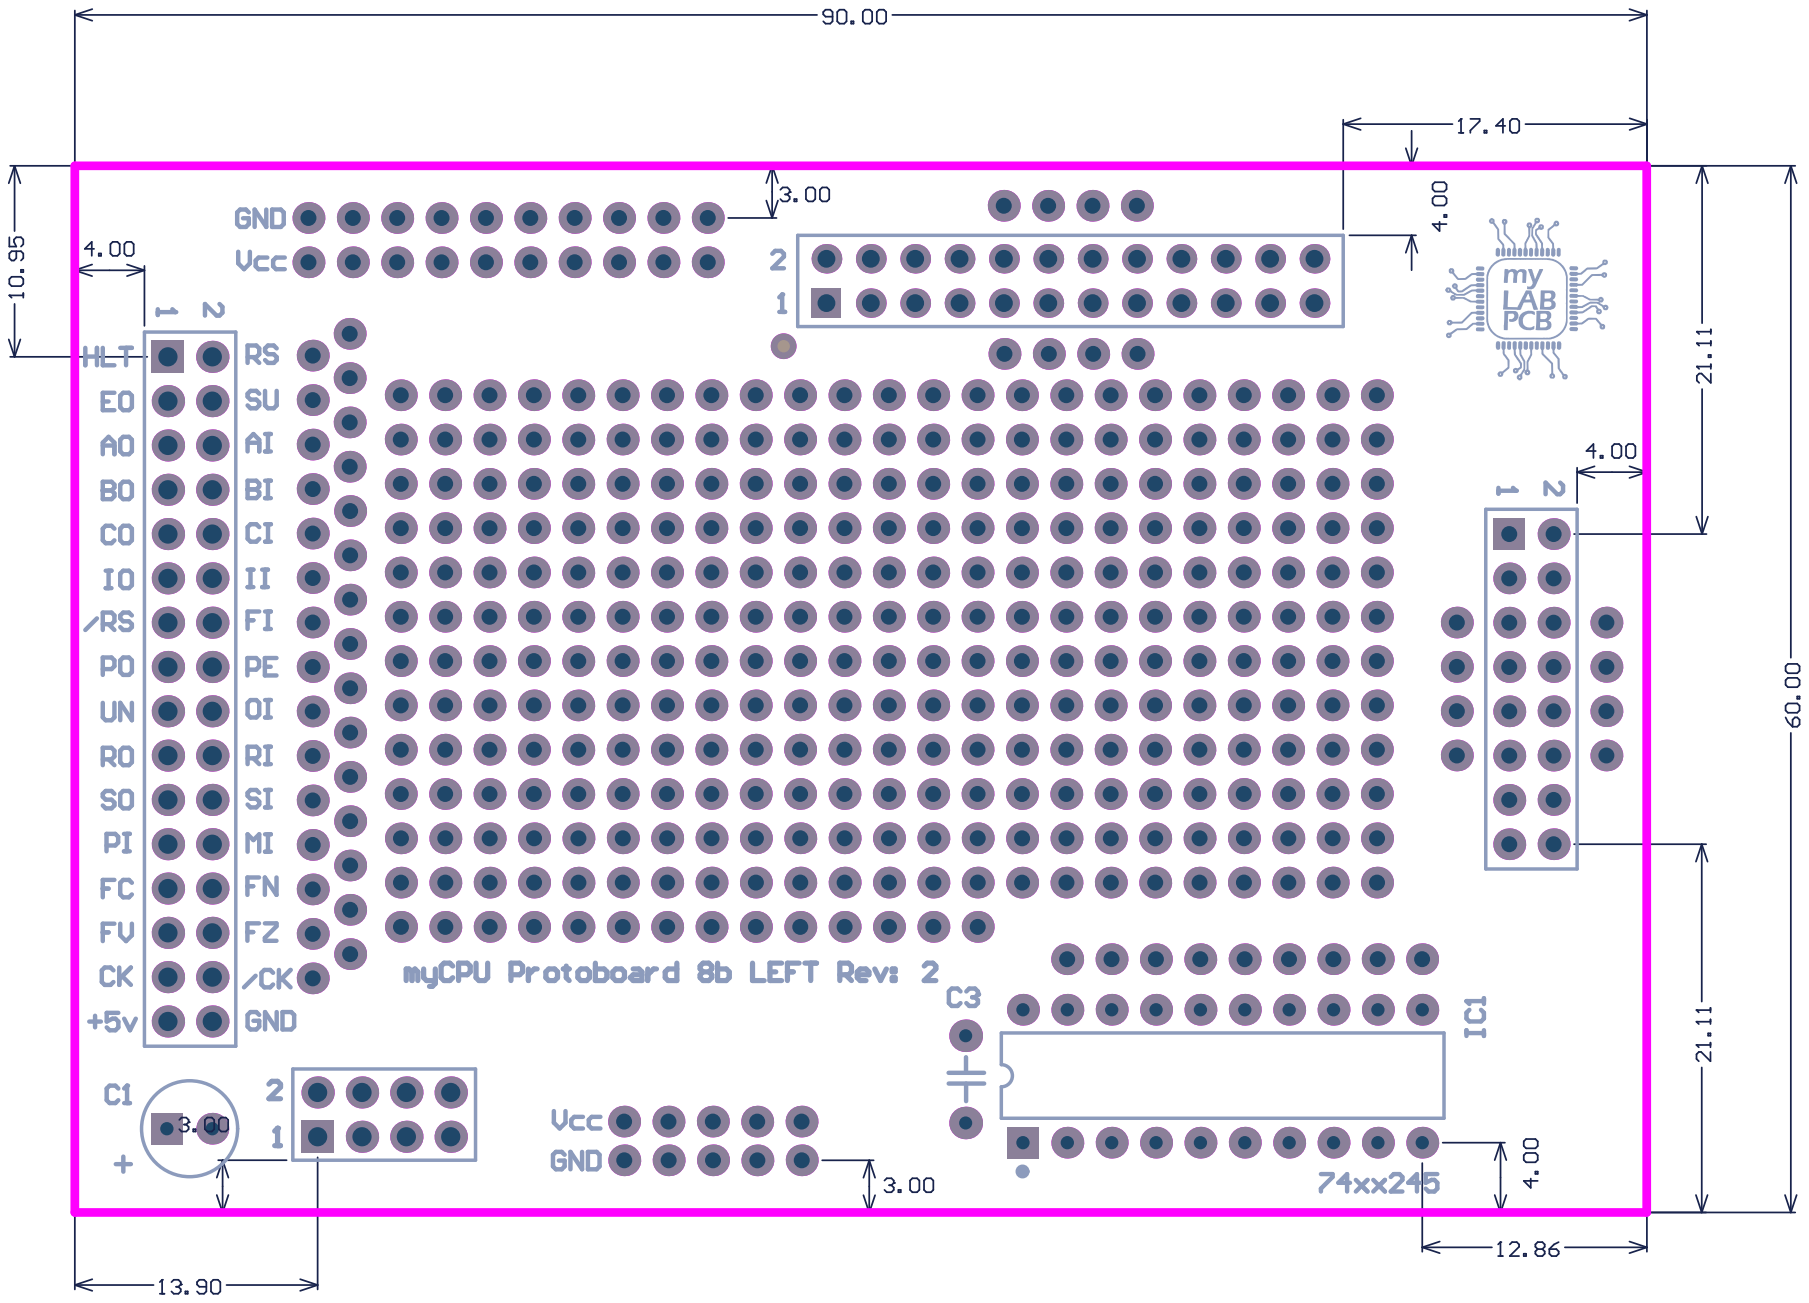
[picture p131: page 4]

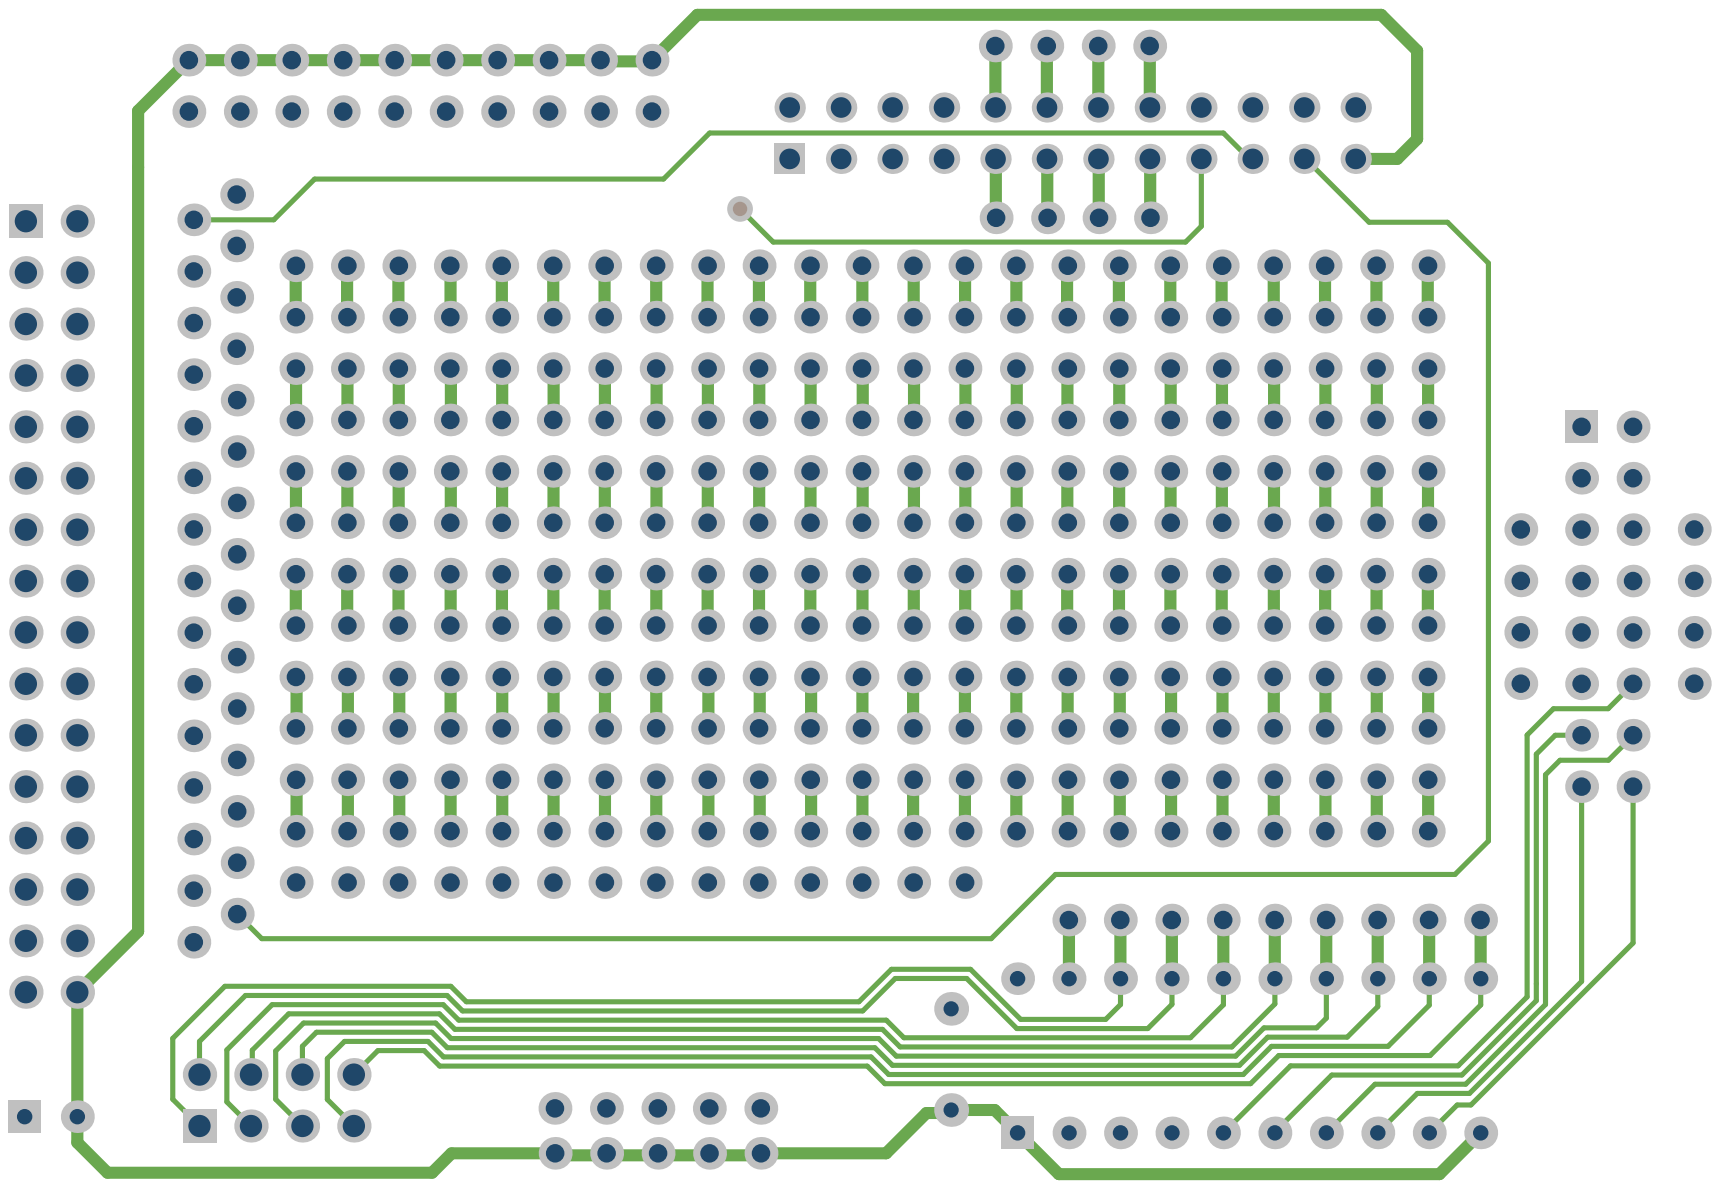
[picture p132: page 5]

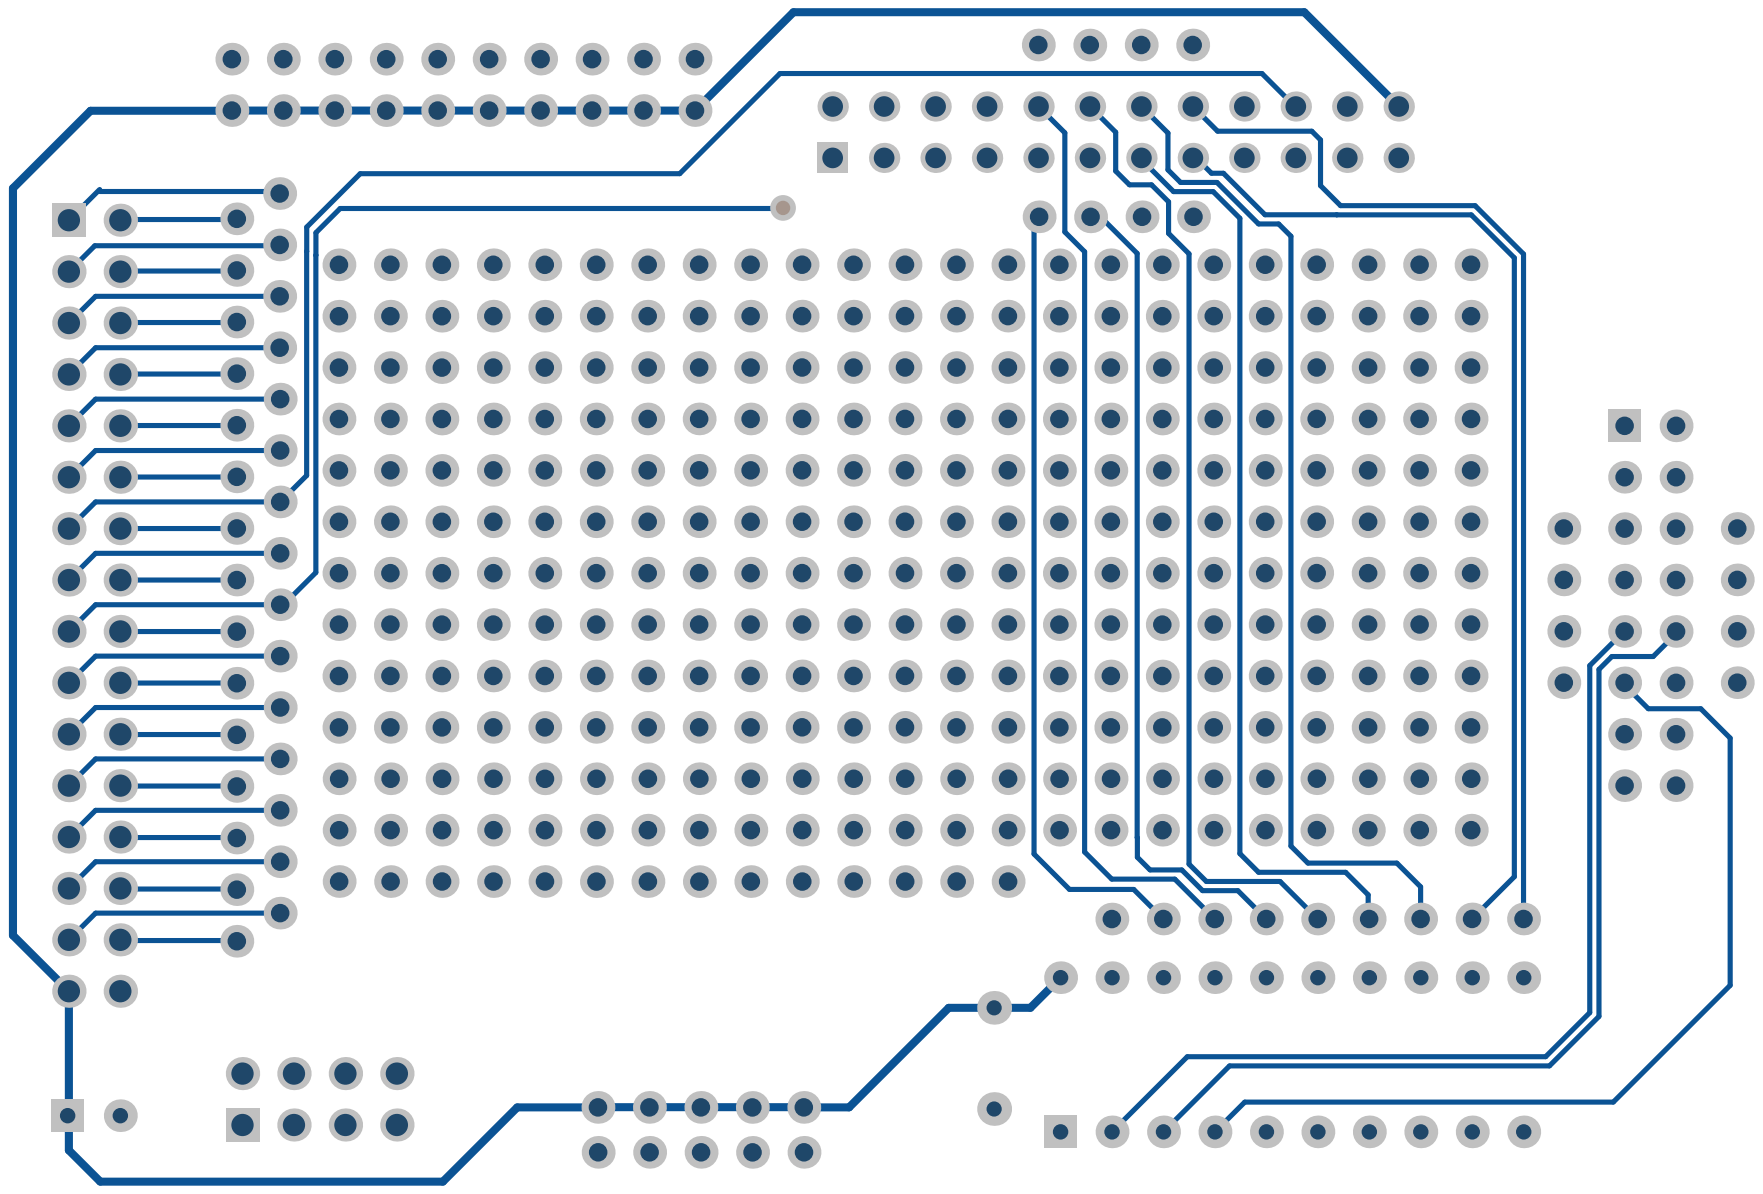
[picture p133: page 6]

# Bill of Materials

## myCPU Protoboard with 245 8b L

Description | Value | Q
Ceramic capacitor | 100nF | 1
Electrolytic capacitor 16v/50v | 10µF | 1
Non inverting bus transceiver | 74xx245 | 1
Pin Header, THT, pitch 2.54mm, Dual Row, Vertical | 16p | 1
Pin Header, THT, pitch 2.54mm, Dual Row, Vertical | 32p | 1
Pin Header, THT, pitch 2.54mm, Dual Row, Vertical | 8p | 1
Socket Header, THT, pitch 2.54mm, Dual Row, Vertical | 24p | 1

# Assembly List

## myCPU Protoboard with 245 8b L

Designator | Description | Value
C1 | Electrolytic capacitor 16v/50v | 10µF
C3 | Ceramic capacitor | 100nF
IC1 | Non inverting bus transceiver | 74xx245
P1 | Pin Header, THT, pitch 2.54mm, Dual Row, Vertical | 16p
P2 | Pin Header, THT, pitch 2.54mm, Dual Row, Vertical | 32p
P3 | Socket Header, THT, pitch 2.54mm, Dual Row, Vertical | 24p
P4 | Pin Header, THT, pitch 2.54mm, Dual Row, Vertical | 8p
