mylabpcb/myCPU/Docs/myCPU_Protoboard_245_R_module_full.pdf

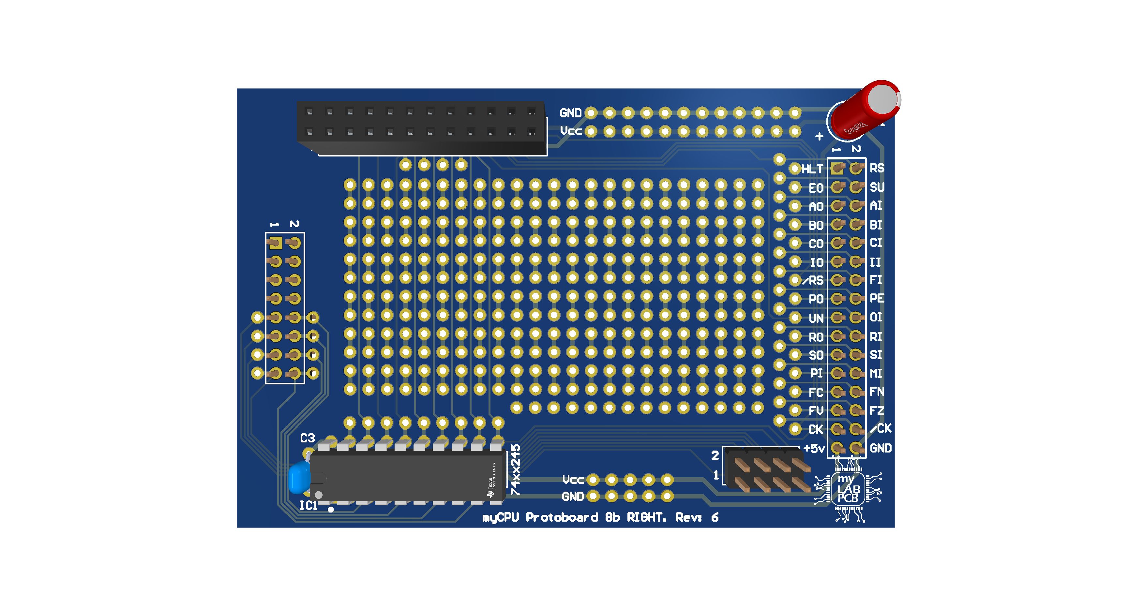
[picture p134: page 1]

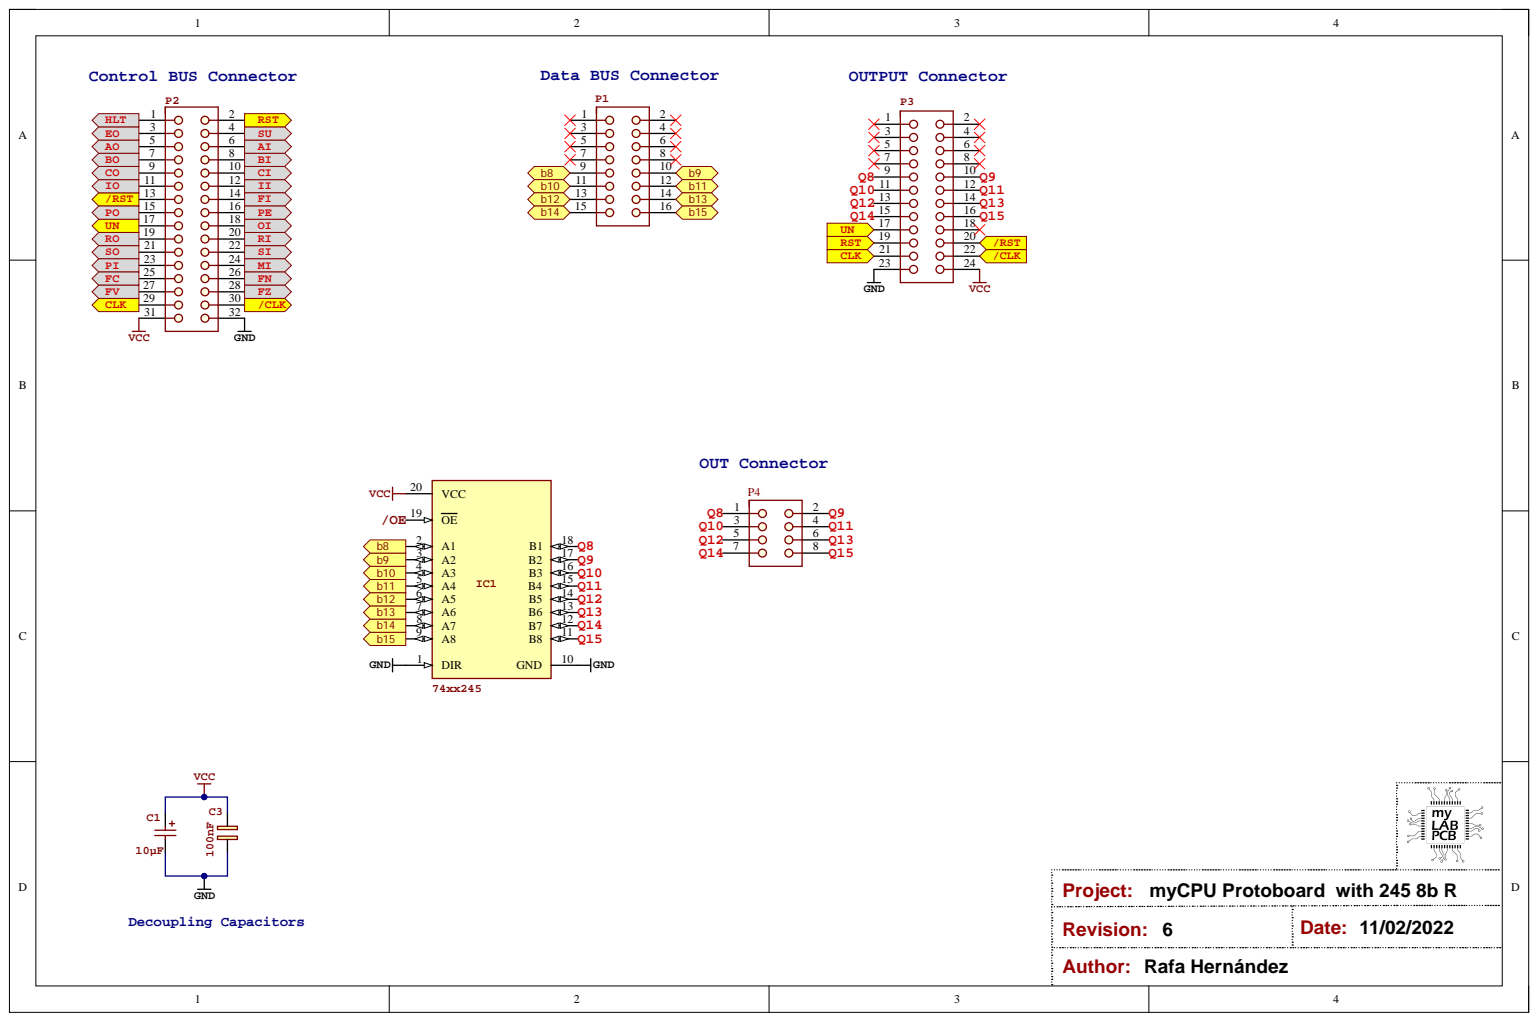
[picture p135: page 3]

Project: myCPU Protoboard with 245 8b R

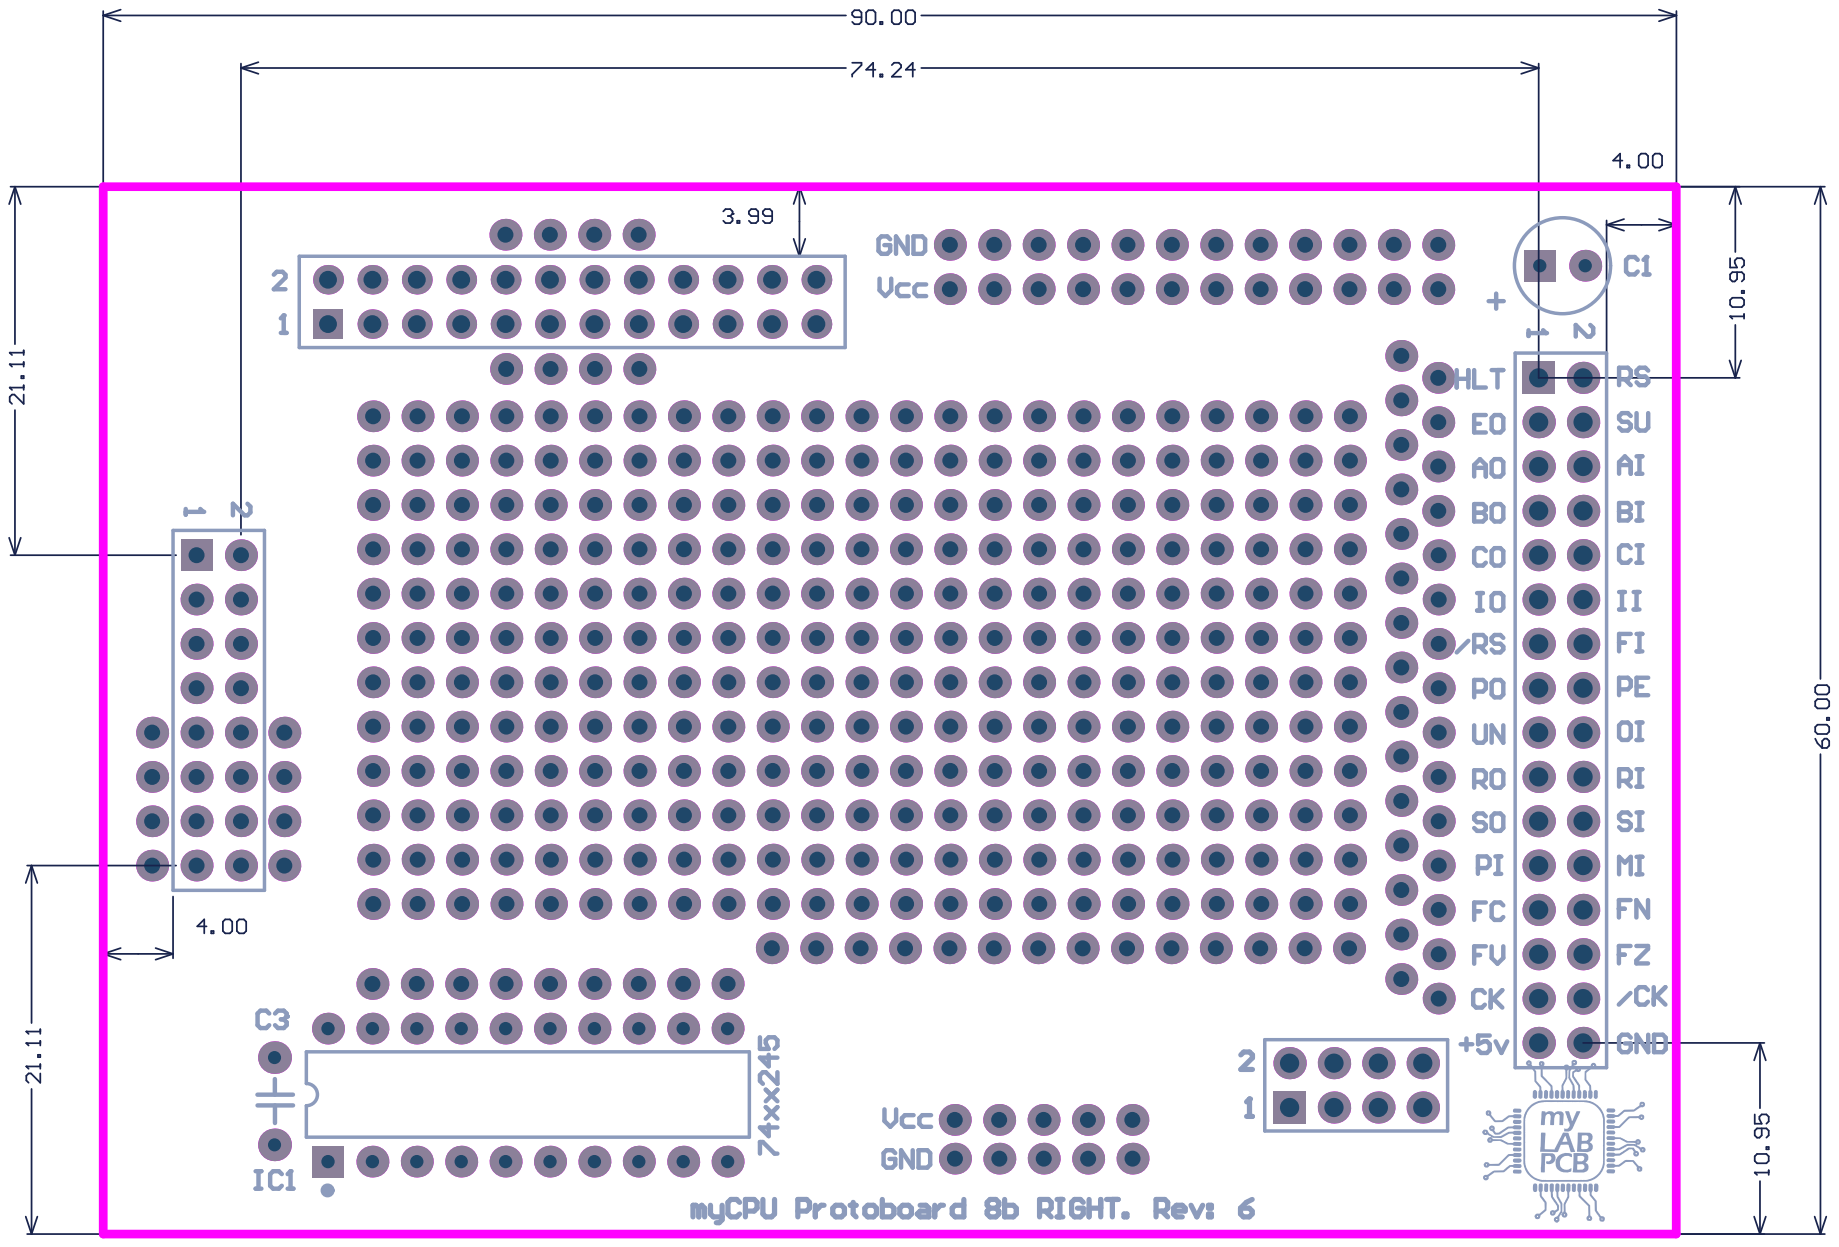
[picture p136: page 4]

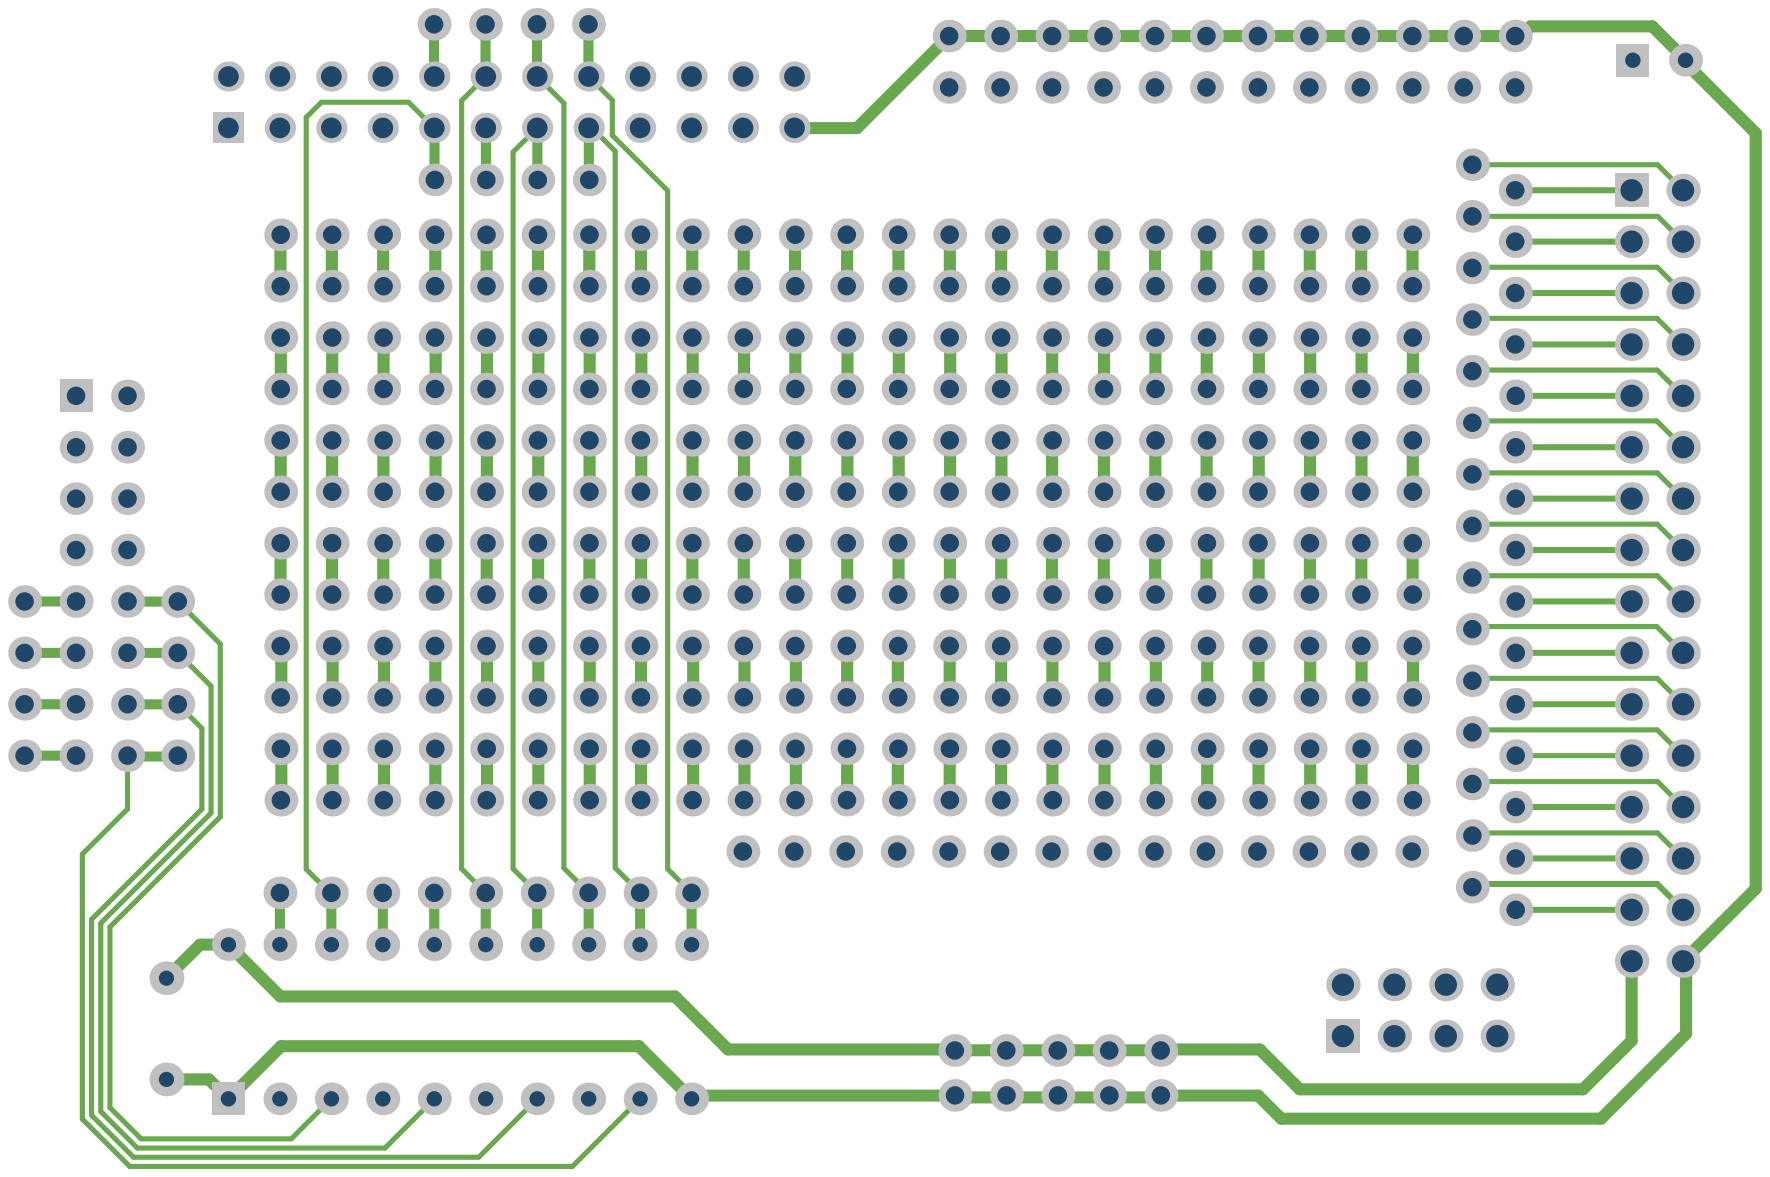
[picture p137: page 5]

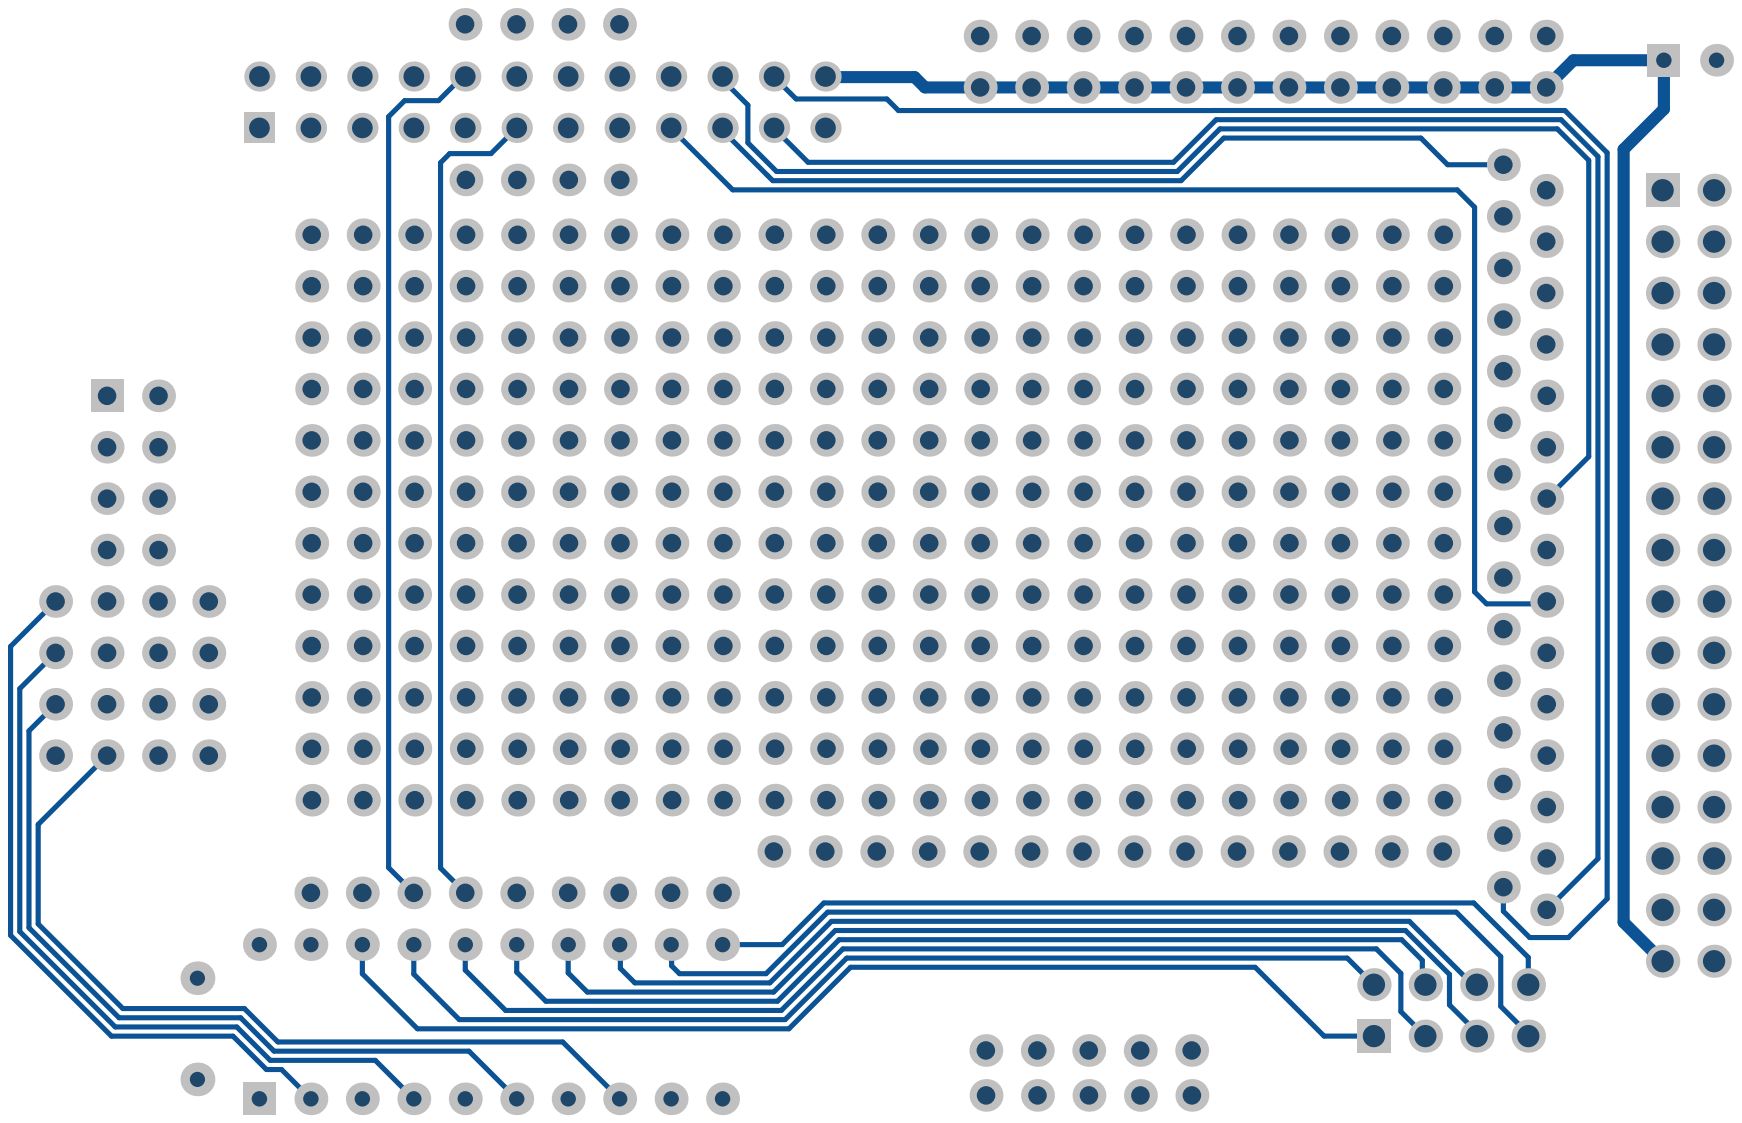
[picture p138: page 6]

# Bill of Materials

## myCPU Protoboard with 245 8b R

Description | Value | Q
Electrolytic capacitor 16v/50v | 10µF | 1
Ceramic capacitor | 100nF | 1
Non inverting bus transceiver | 74xx245 | 1
Pin Header, THT, pitch 2.54mm, Dual Row, Vertical, 16p | 16p | 1
Pin Header, THT, pitch 2.54mm, Dual Row, Vertical, 32p | 32p | 1
Socket Header, THT, pitch 2.54mm, Dual Row, Vertical, 24p | | 1
Pin Header, THT, pitch 2.54mm, Dual Row, Vertical, 8p | 8p | 1

# Assembly List

## myCPU Protoboard with 245 8b R

Designator | Description | Value
C1 | Electrolytic capacitor 16v/50v | 10µF
C3 | Ceramic capacitor | 100nF
IC1 | Non inverting bus transceiver | 74xx245
P1 | Pin Header, THT, pitch 2.54mm, Dual Row, Vertical | 16p
P2 | Pin Header, THT, pitch 2.54mm, Dual Row, Vertical | 32p
P3 | Socket Header, THT, pitch 2.54mm, Dual Row, Vertical | 24p
P4 | Pin Header, THT, pitch 2.54mm, Dual Row, Vertical | 8p
