mylabpcb/myCPU/Docs/myCPU_RAM189_module_full.pdf

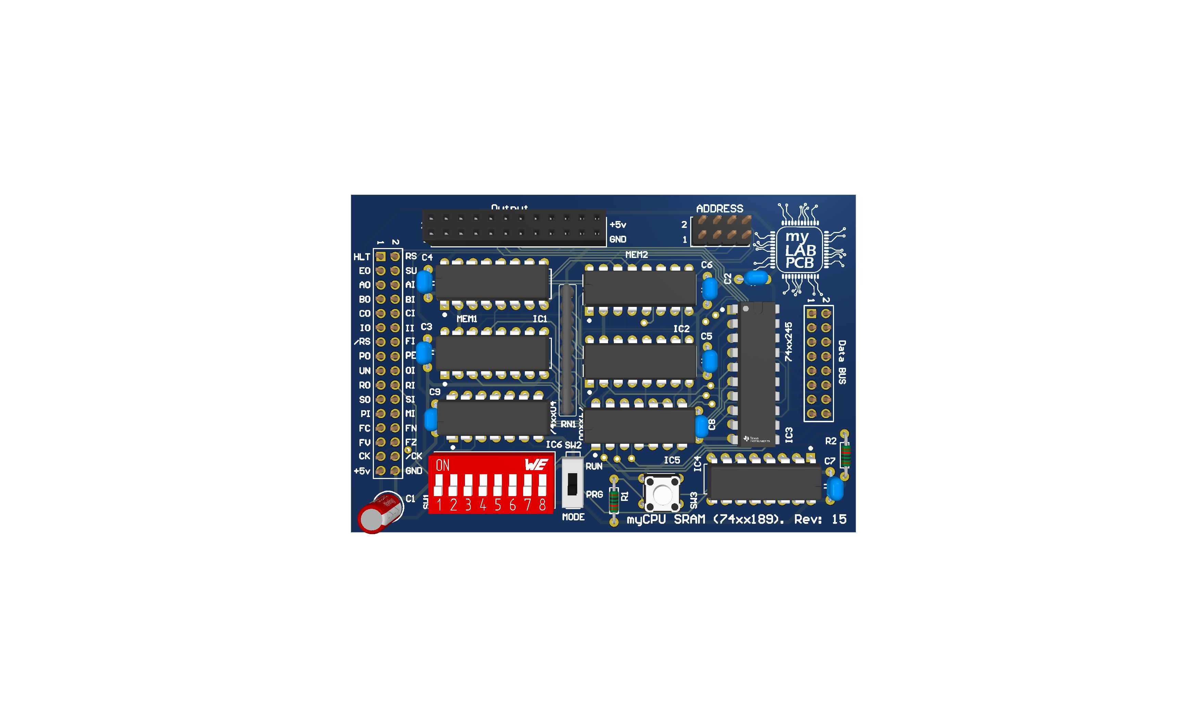
[picture p139: page 1]

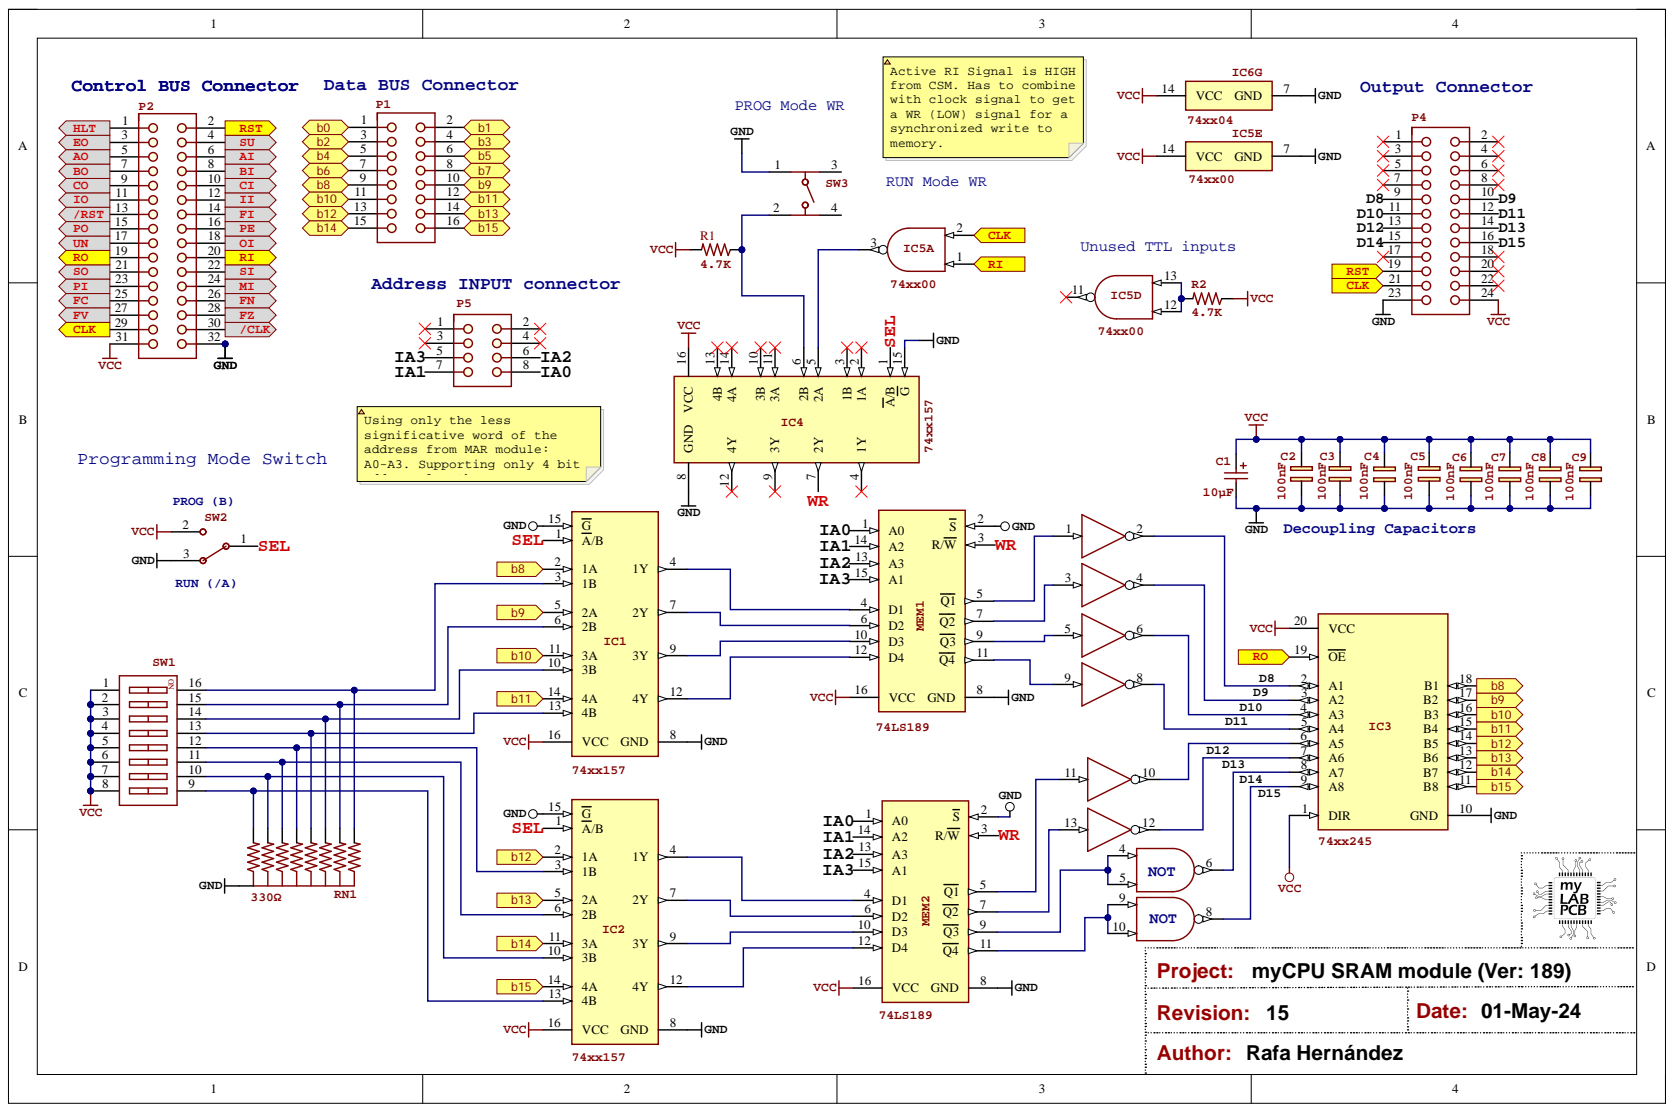
[picture p140: page 3]

Active RI Signal is HIGH
from CSM. Has to combine
with clock signal to get
a WR (LOW) signal for a
synchronized write to
memory.

Using only the less
significative word of the
address from MAR module:
A0-A3. Supporting only 4 bit

Project: myCPU SRAM module (Ver: 189)

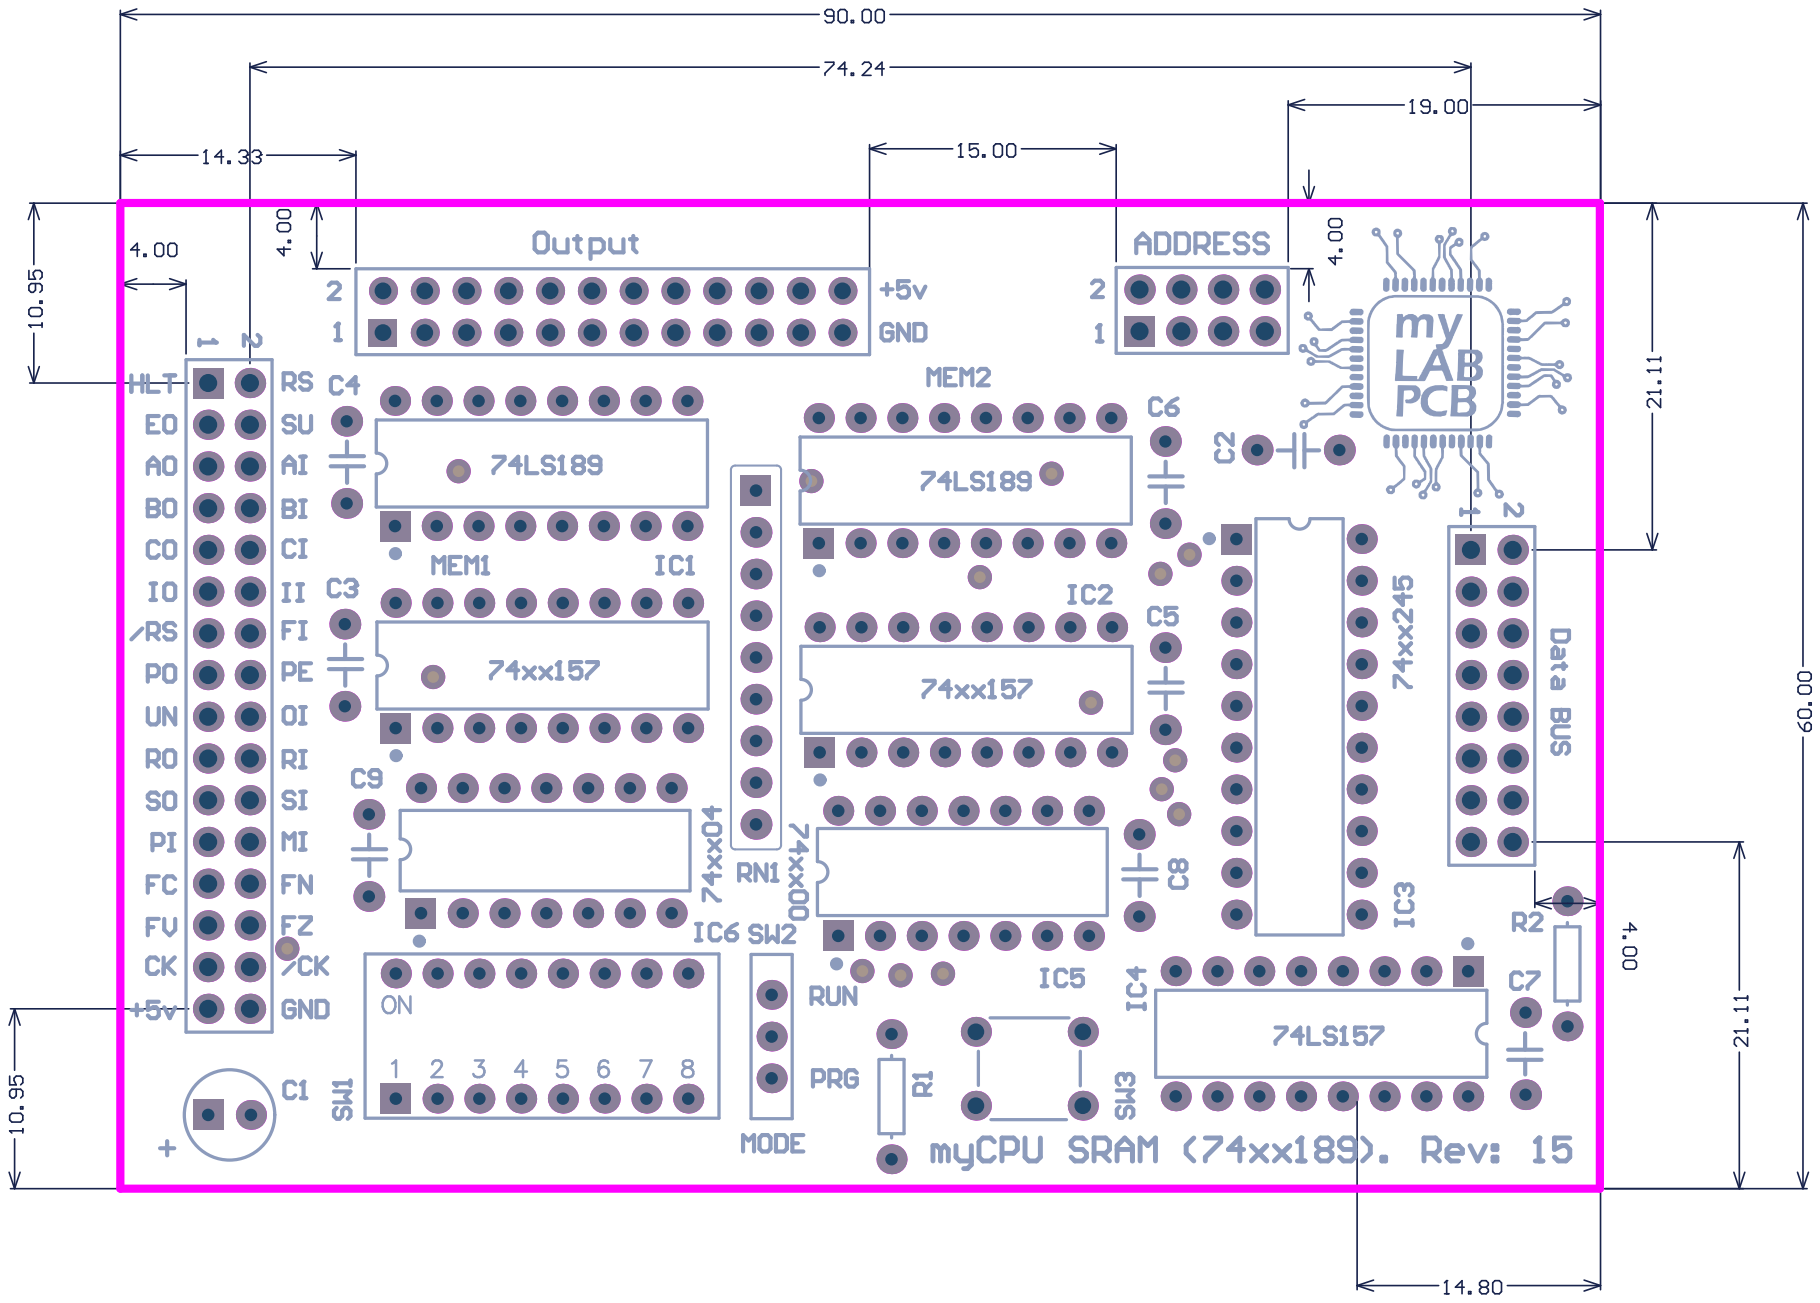
[picture p141: page 4]

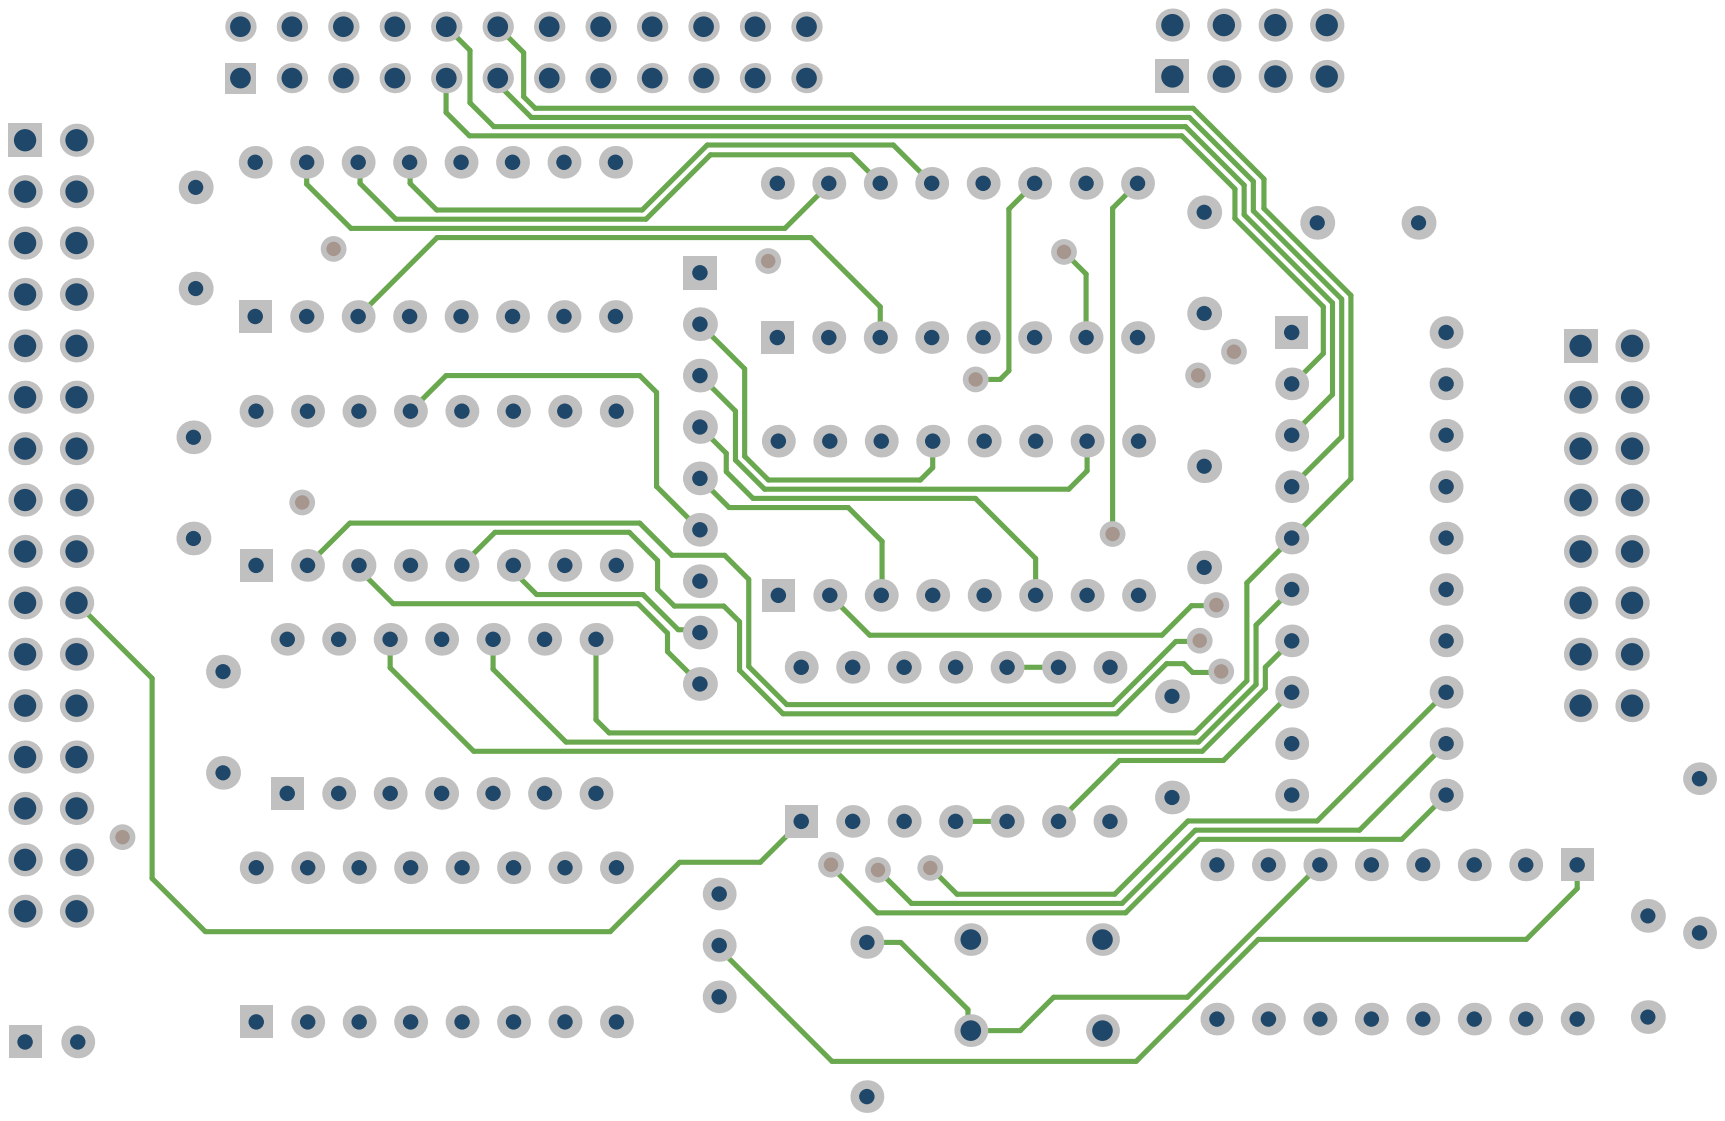
[picture p142: page 5]

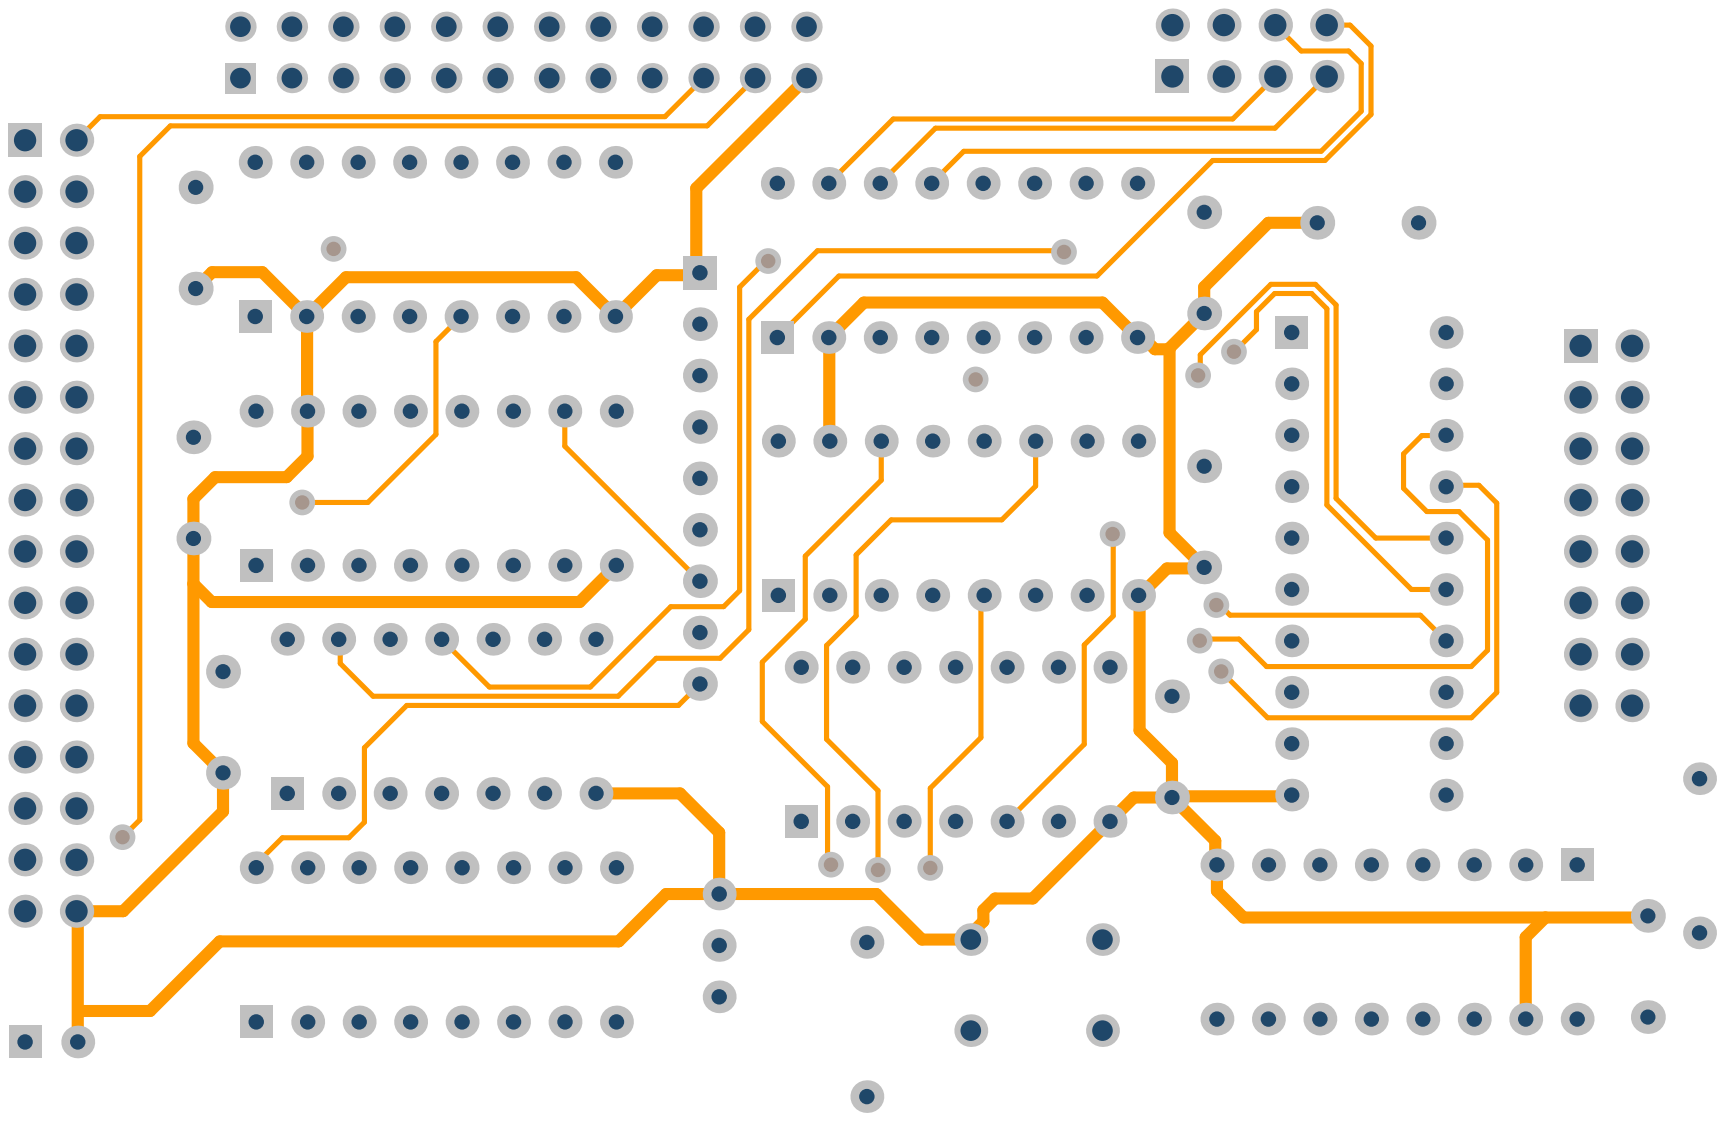
[picture p143: page 6]

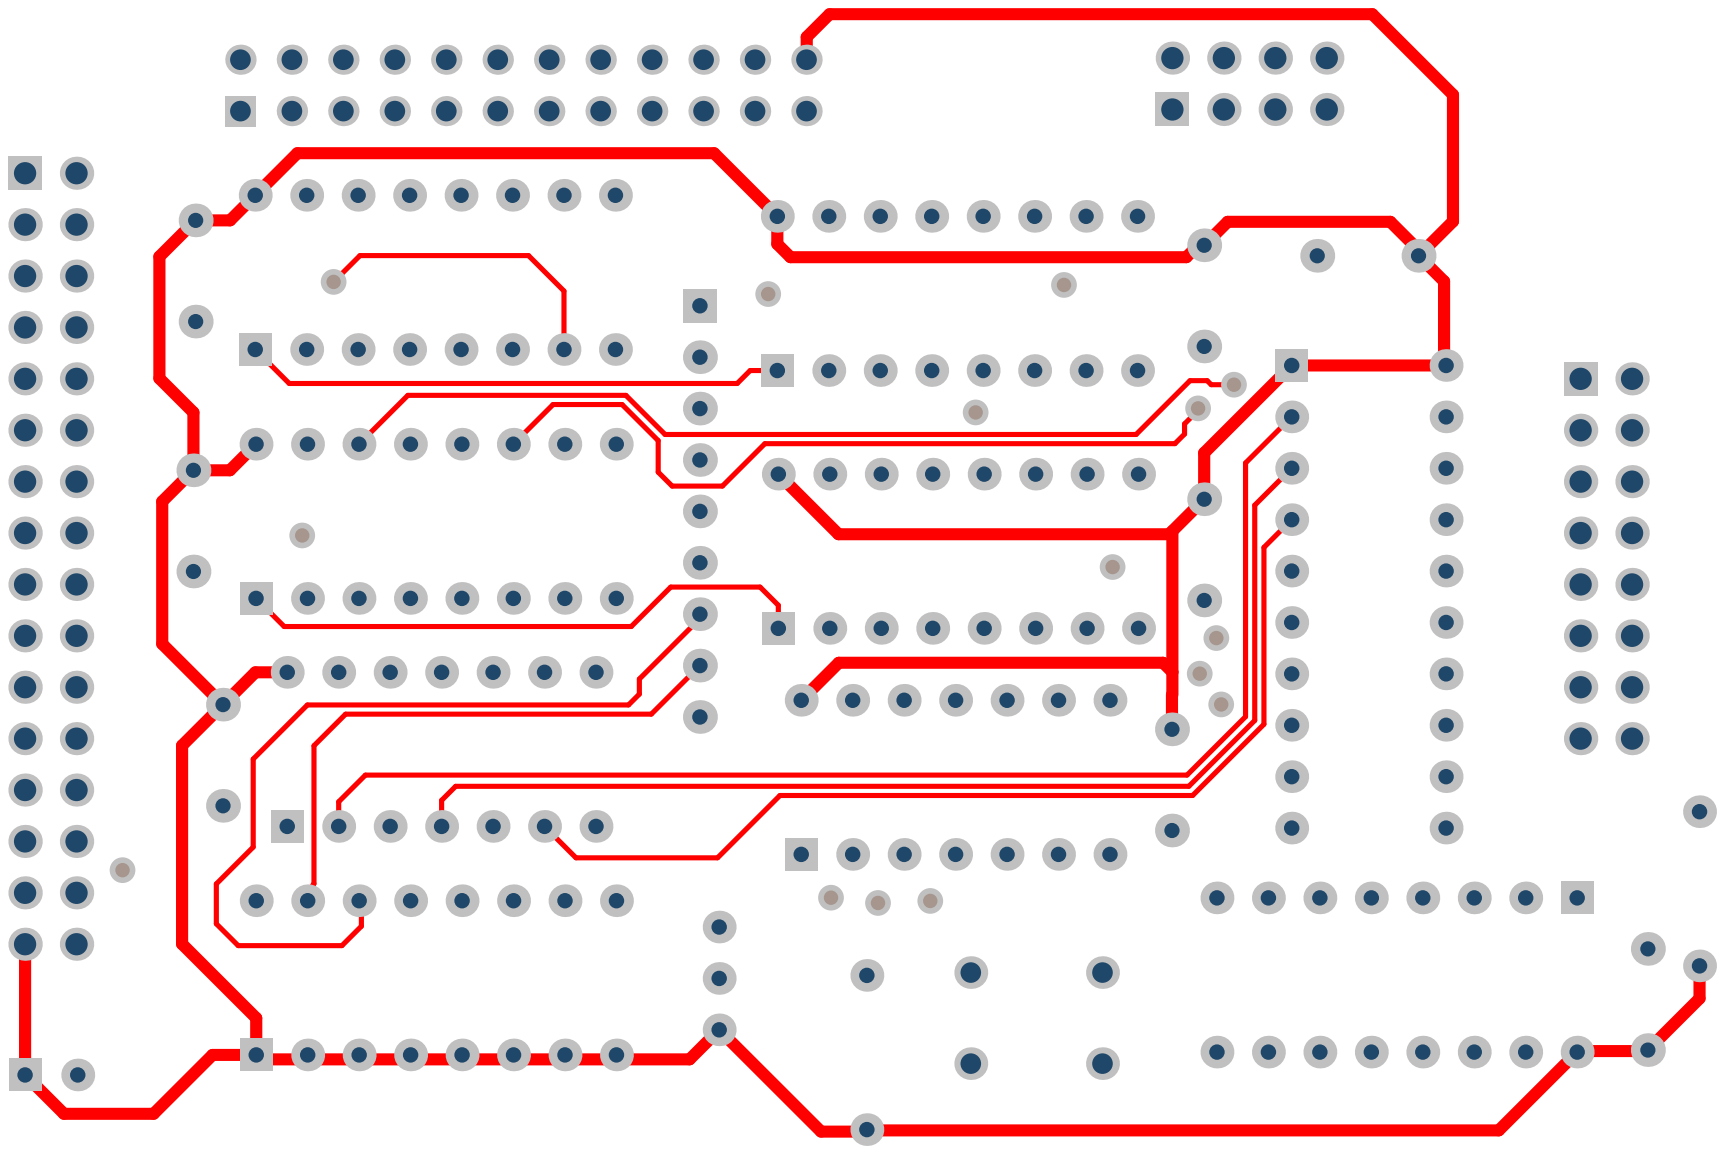
[picture p144: page 7]

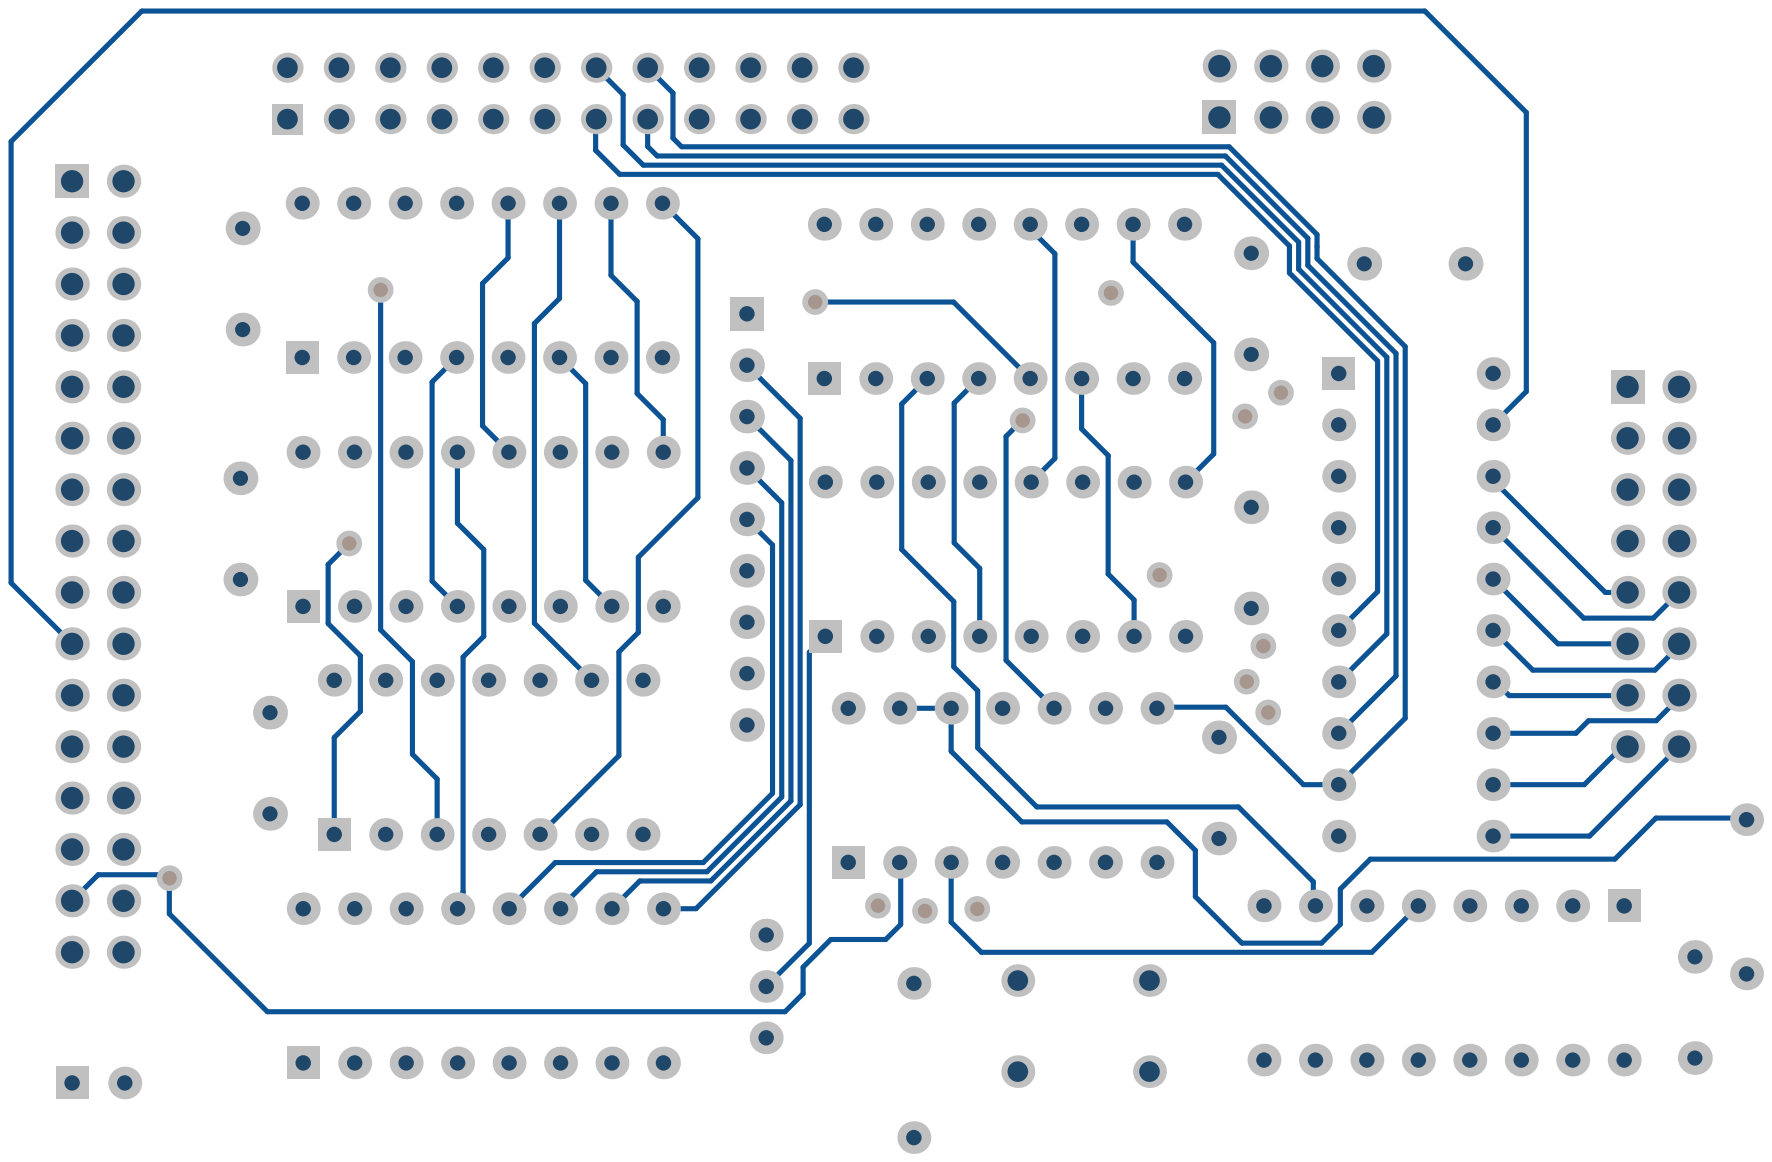
[picture p145: page 8]

# Bill of Materials

# myCPU SRAM module (Ver: 189)

Description | Value | Q
Electrolytic capacitor 16v/50v | 10µF | 1
Ceramic capacitor | 100nF | 8
4-Bits 2-Line to 1 Line data selector | 74xx157 | 3
Non inverting bus transceiver | 74xx245 | 1
Quad 2-input NAND gates | 74xx00 | 1
Hex inverters | 74xx04 | 1
SRAM 16x1 inverted outputs | 74LS189 | 2
Pin Header, THT, pitch 2.54mm, Dual Row, Vertical | 16p | 1
Pin Header, THT, pitch 2.54mm, Dual Row, Vertical | 32p | 1
Socket Header, THT, pitch 2.54mm, Dual Row, Vertical | 24p | 1
Pin Header, THT, pitch 2.54mm, Dual Row, Vertical | 8p | 1
Resistor Axial | 4.7K | 2
Resistor array 8 elements,9 pins | 330 | 1
DIP switch 8 positions | 8p | 1
Mini slide switch 2 pos, 3 pins | SP2T | 1
Tactile button 6 mm | 6mm | 1

# Assembly List

## myCPU SRAM module (Ver: 189)

Designator | Description | Value
C1 | Electrolytic capacitor 16v/50v | 10µF
C2 | Ceramic capacitor | 100nF
C3 | Ceramic capacitor | 100nF
C4 | Ceramic capacitor | 100nF
C5 | Ceramic capacitor | 100nF
C6 | Ceramic capacitor | 100nF
C7 | Ceramic capacitor | 100nF
C8 | Ceramic capacitor | 100nF
C9 | Ceramic capacitor | 100nF
IC1 | 4-Bits 2-Line to 1 Line data selector | 74xx157
IC2 | 4-Bits 2-Line to 1 Line data selector | 74xx157
IC3 | Non inverting bus transceiver | 74xx245
IC4 | 4-Bits 2-Line to 1 Line data selector | 74xx157
IC5 | Quad 2-input NAND gates | 74xx00
IC6 | Hex inverters | 74xx04
MEM1 | SRAM 16x1 inverted outputs | 74LS189
MEM2 | SRAM 16x1 inverted outputs | 74LS189
P1 | Pin Header, THT, pitch 2.54mm, Dual Row, Vertical | 16p
P2 | Pin Header, THT, pitch 2.54mm, Dual Row, Vertical | 32p
P4 | Socket Header, THT, pitch 2.54mm, Dual Row, Vertical | 24p
P5 | Pin Header, THT, pitch 2.54mm, Dual Row, Vertical | 8p
R1 | Resistor Axial | 4.7K
R2 | Resistor Axial | 4.7K
RN1 | Resistor array 8 elements,9 pins | 330
SW1 | DIP switch 8 positions | 8p
SW2 | Mini slide switch 2 pos, 3 pins | SP2T
SW3 | Tactile button 6 mm | 6mm
