mylabpcb/myCPU/Docs/myCPU_Register_8b_L_module_full.pdf

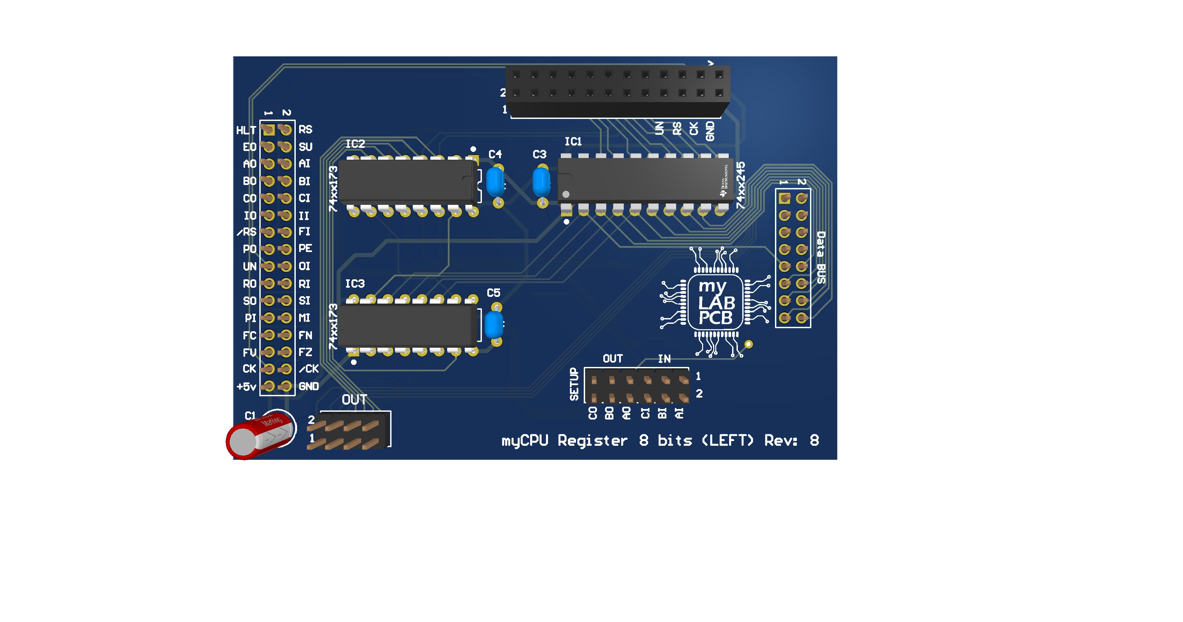
[picture p146: page 1]

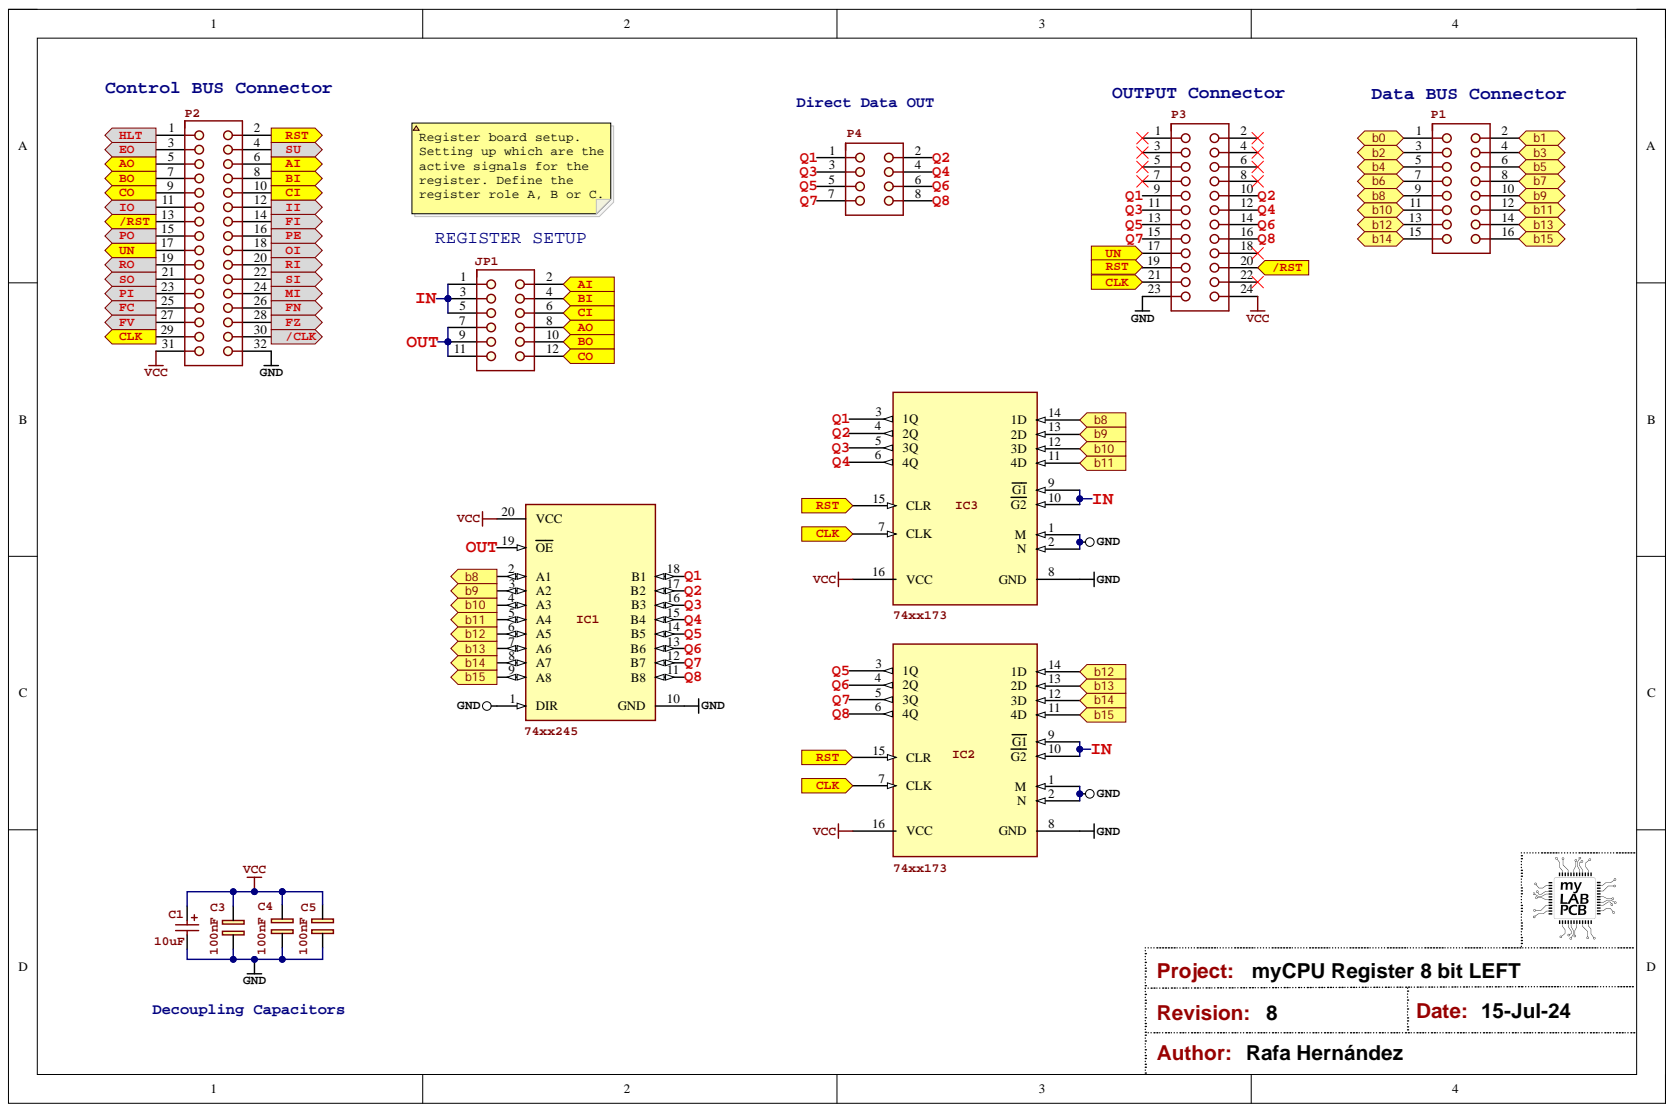
[picture p147: page 3]

Register board setup.
Setting up which are the
active signals for the
register. Define the
register role A, B or C.

Project: myCPU Register 8 bit LEFT

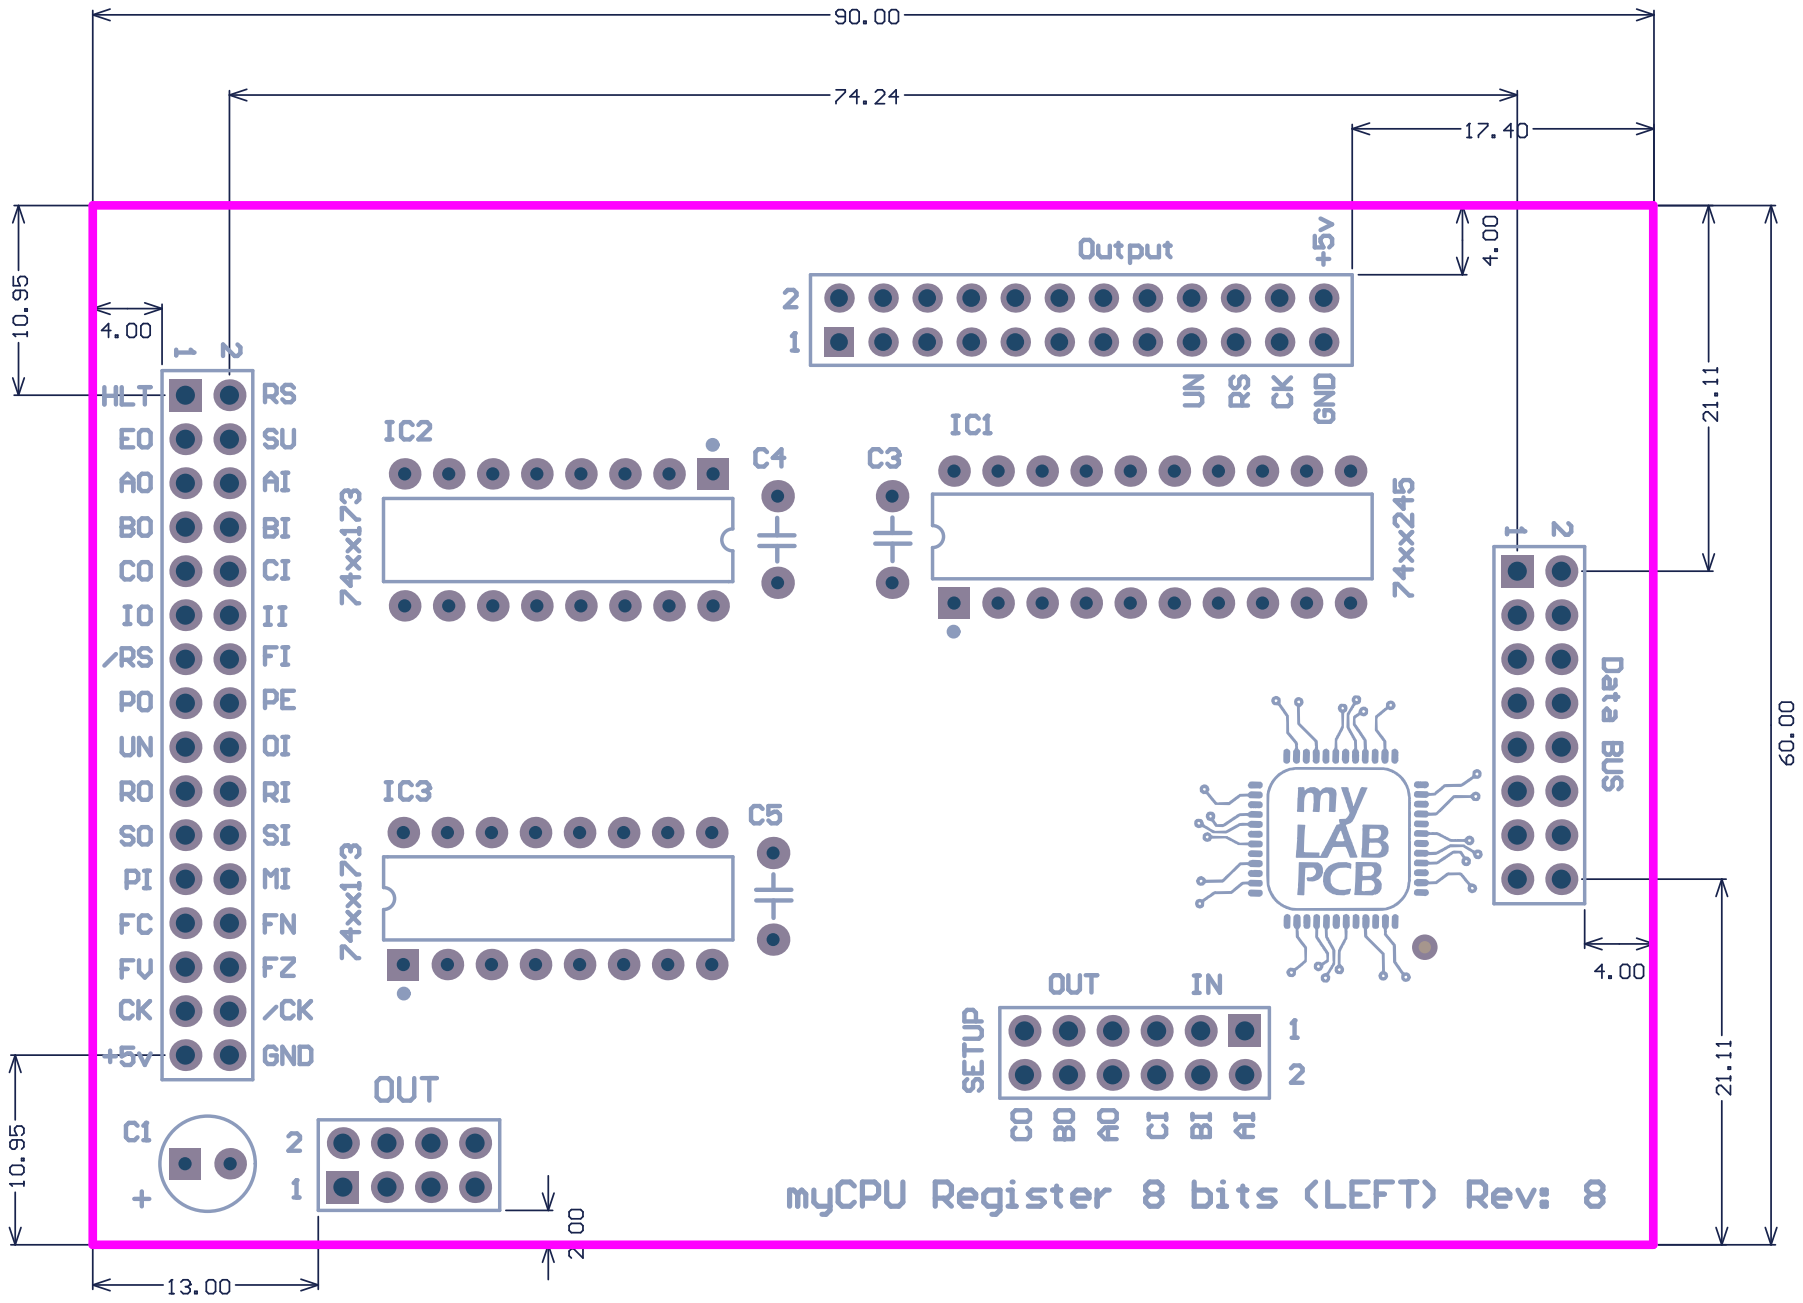
[picture p148: page 4]

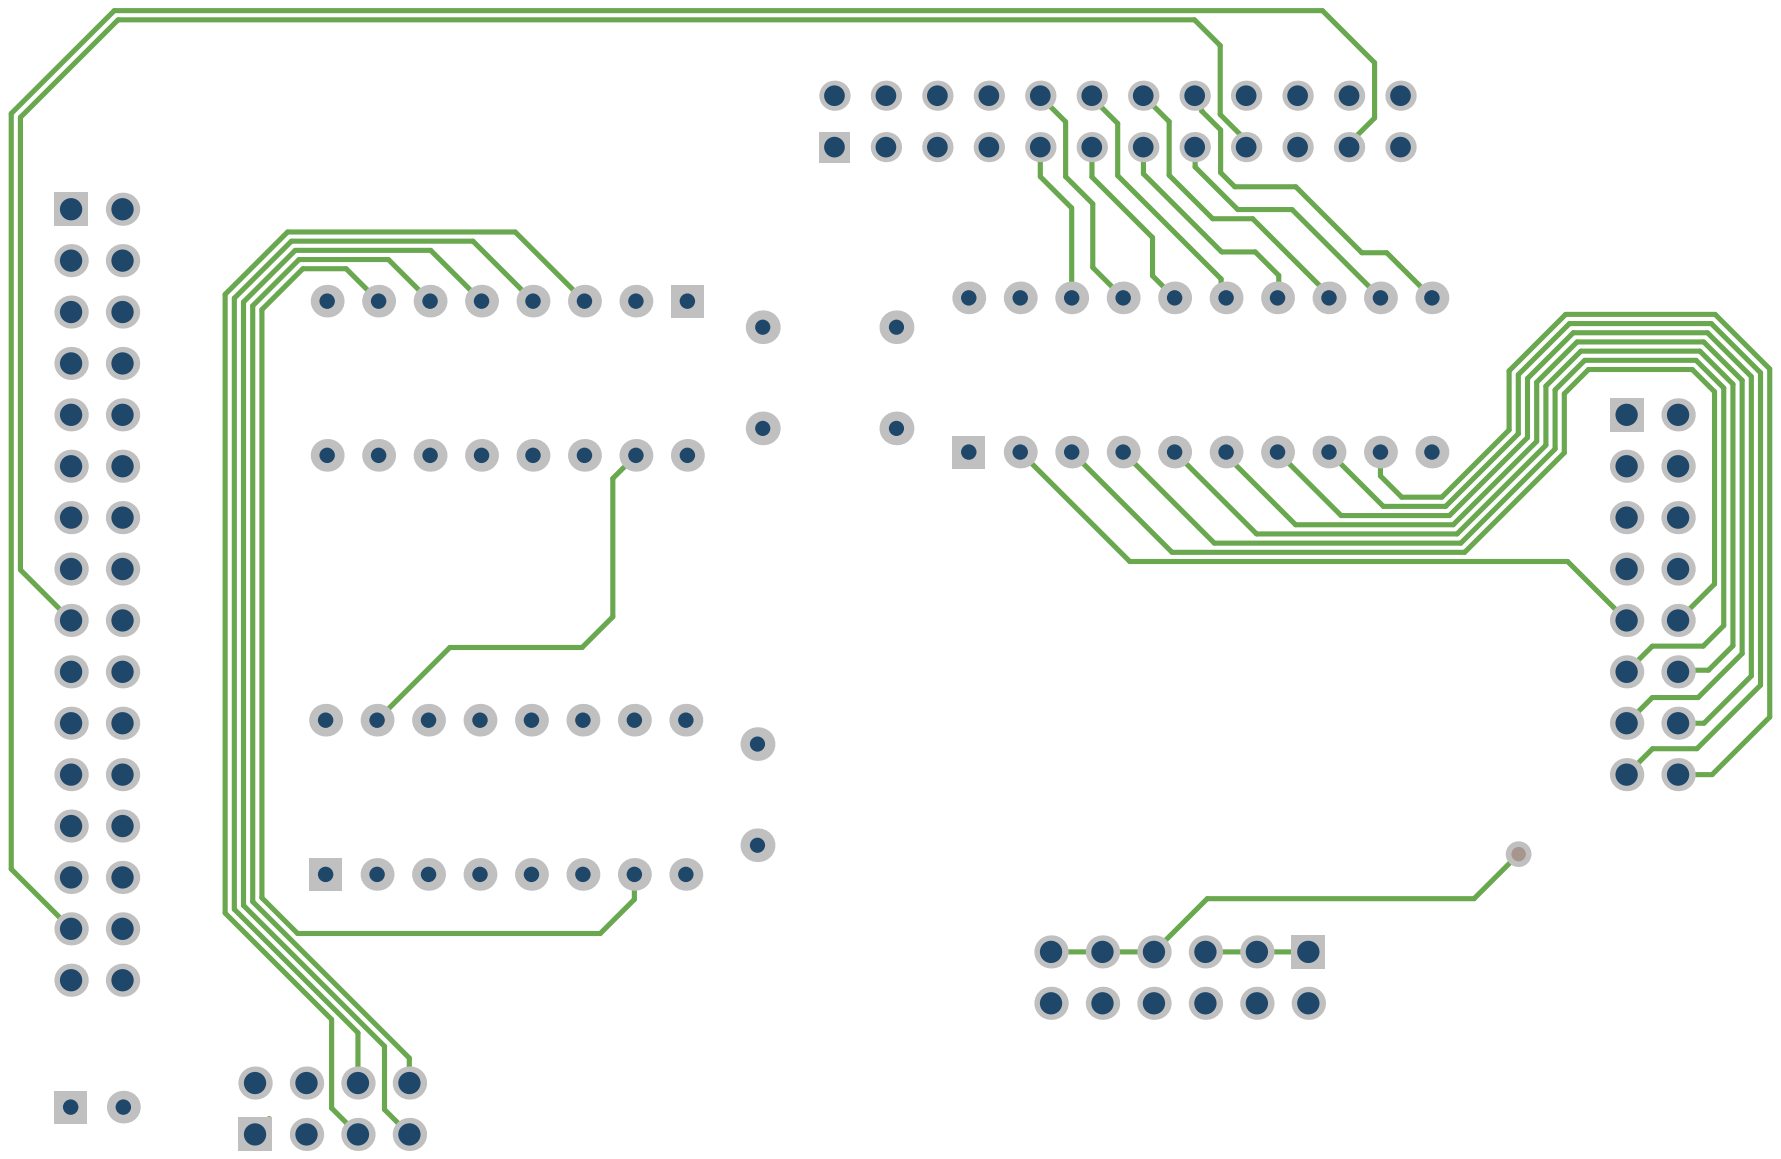
[picture p149: page 5]

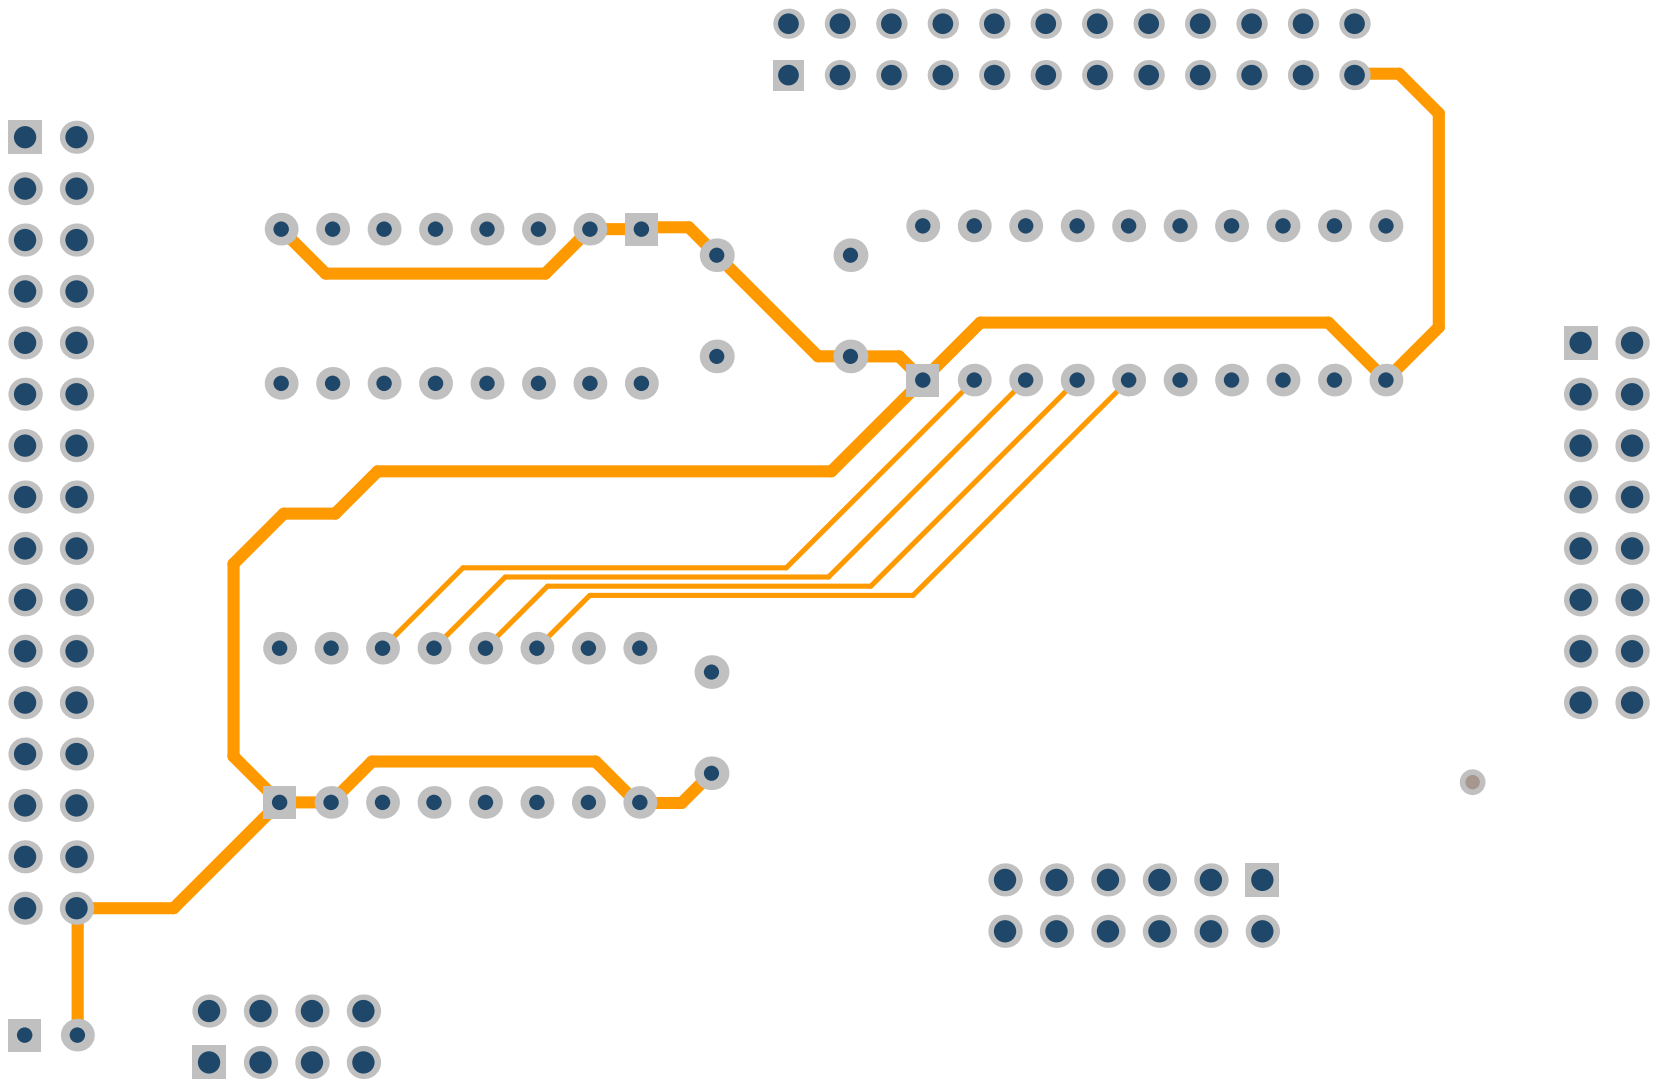
[picture p150: page 6]

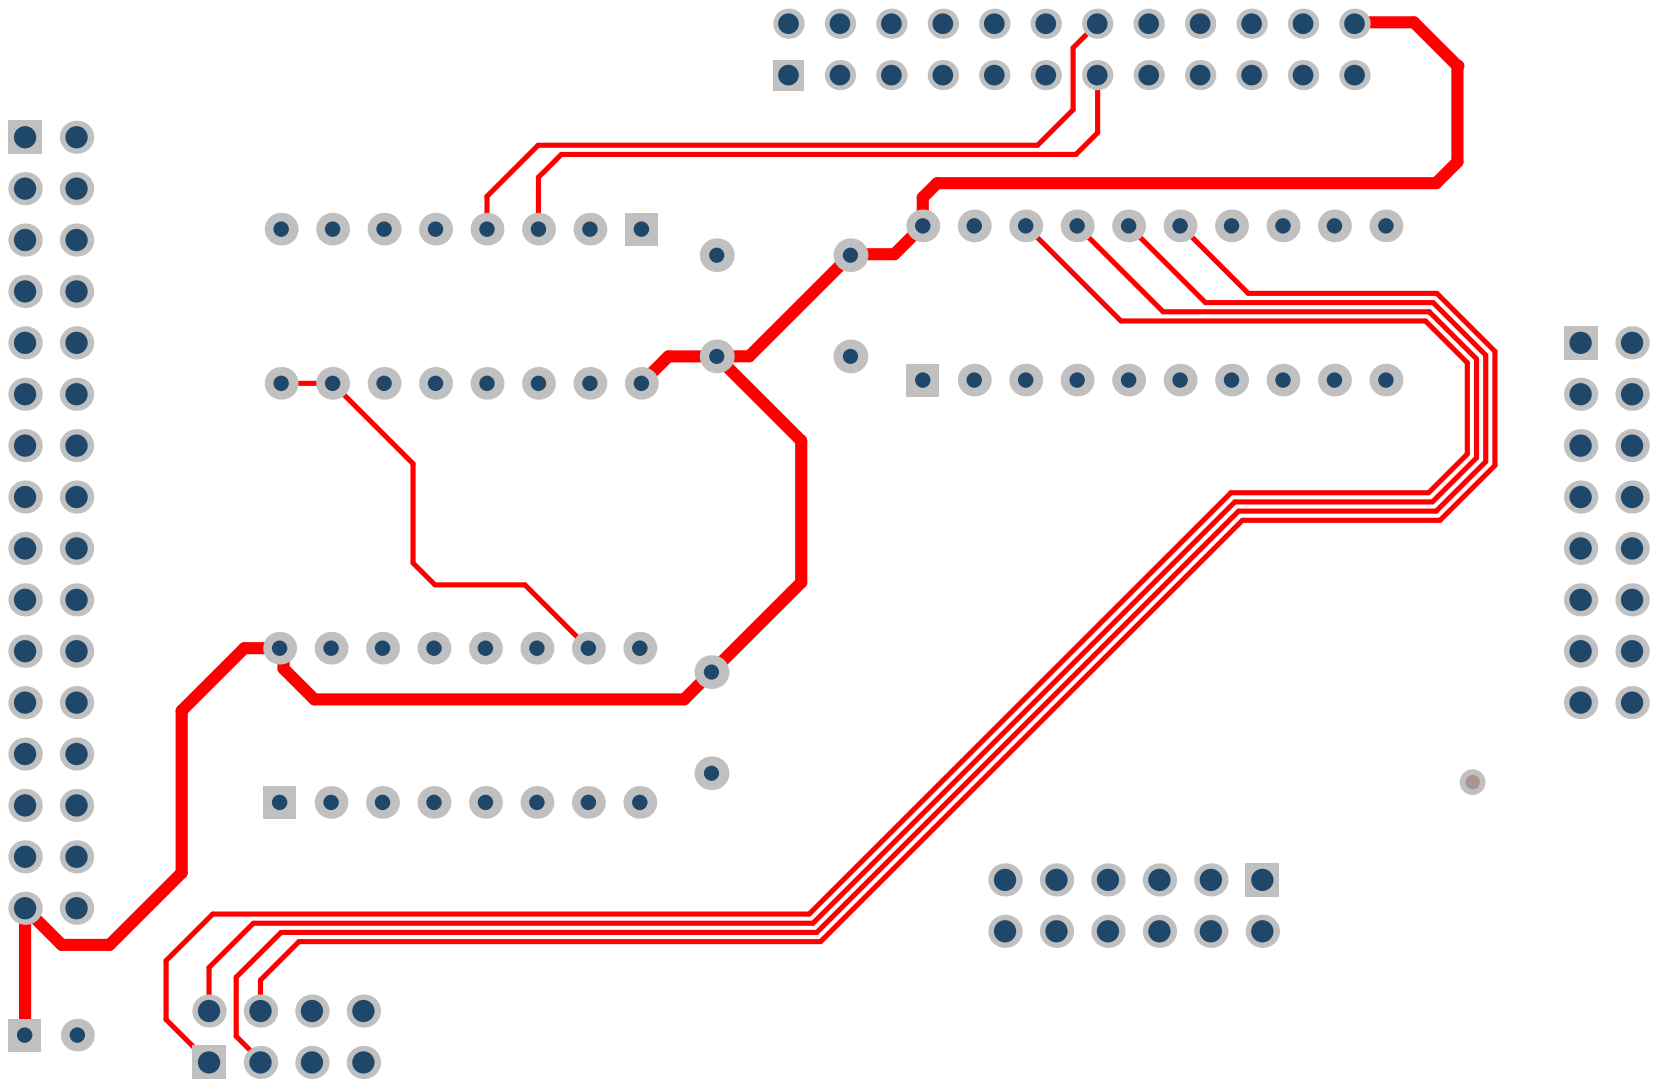
[picture p151: page 7]

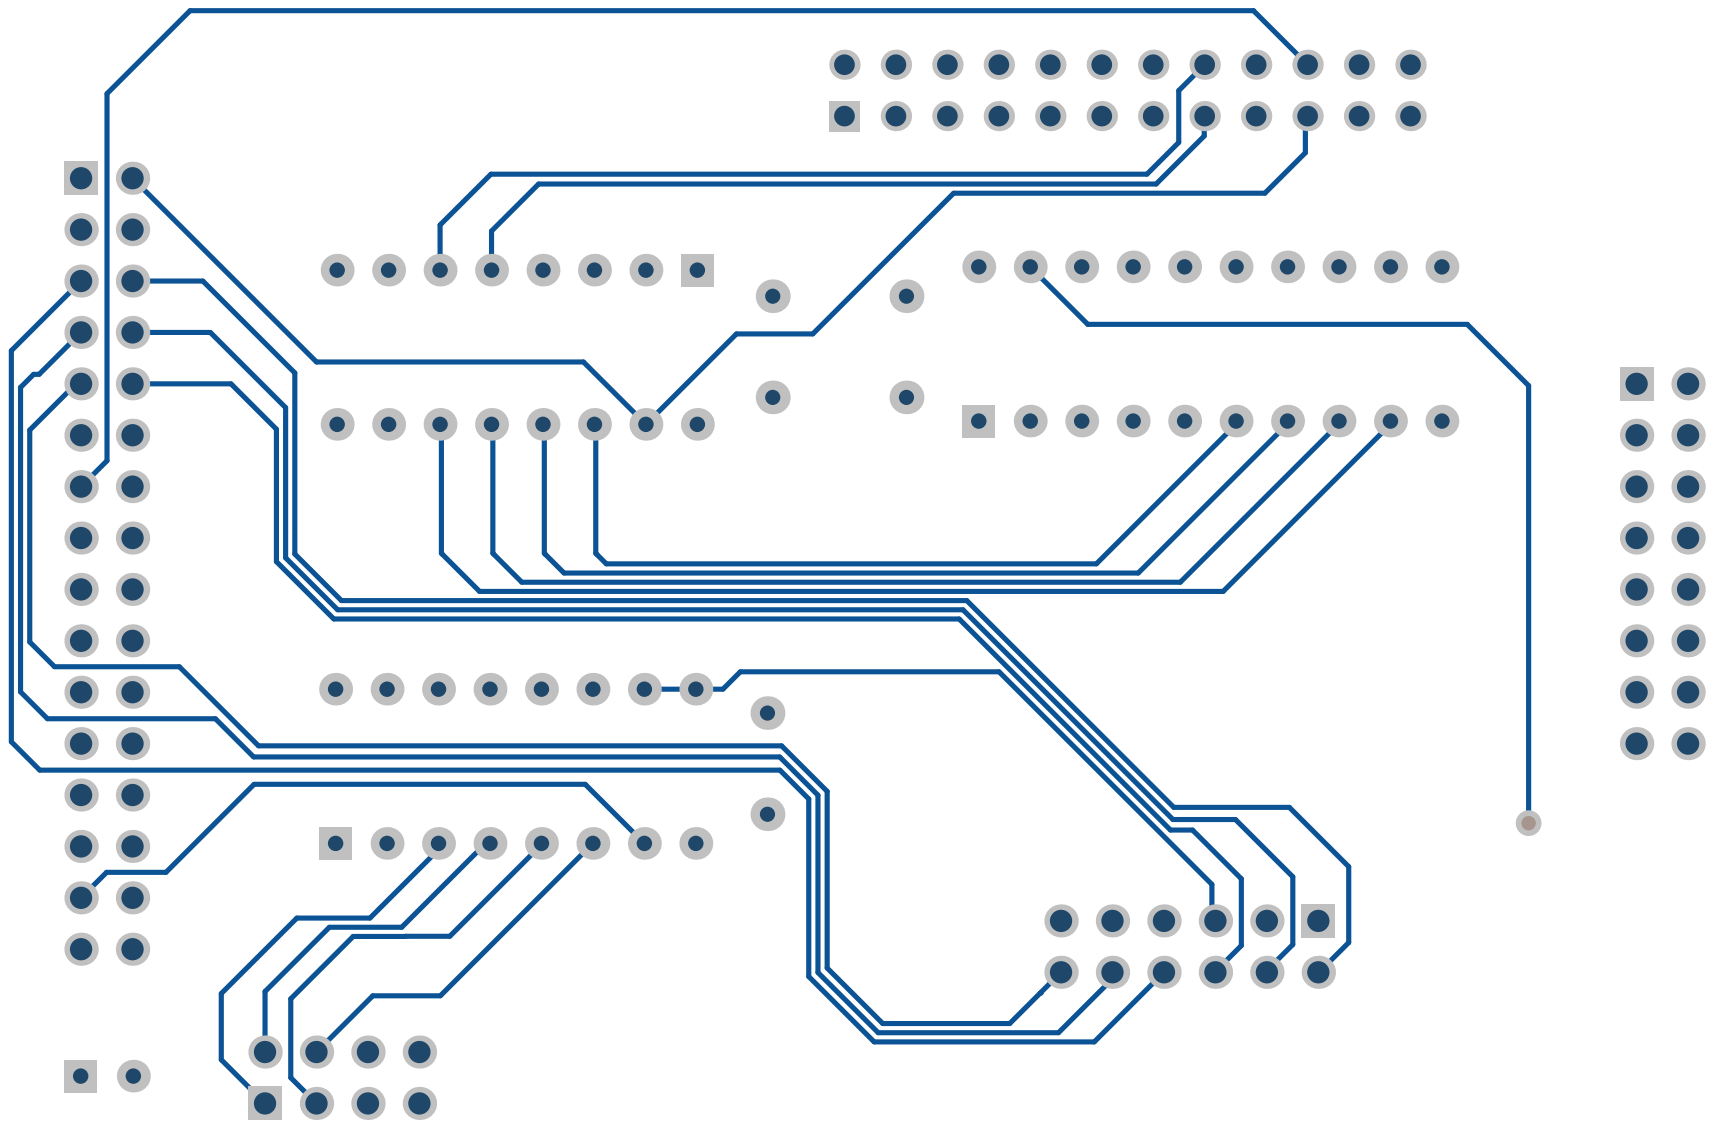
[picture p152: page 8]

# Bill of Materials

# myCPU Register 8 bit

Description | Value | Q
Electrolytic capacitor 16v/50v | 10µF | 1
Ceramic capacitor | 100nF | 3
Non inverting bus transceiver | 74xx245 | 1
4-bit D-Type Register with 3 state outputs | 74xx173 | 2
Pin Header, THT, pitch 2.54mm, Dual Row, Vertical | 12p | 1
Pin Header, THT, pitch 2.54mm, Dual Row, Vertical | 16p | 1
Pin Header, THT, pitch 2.54mm, Dual Row, Vertical | 32p | 1
Socket Header, THT, pitch 2.54mm, Dual Row, Vertical | 24p | 1
Pin Header, THT, pitch 2.54mm, Dual Row, Vertical | 8p | 1

# Assembly List

## myCPU Register 8 bit

Designator | Description | Value
C1 | Electrolytic capacitor 16v/50v | 10µF
C3 | Ceramic capacitor | 100nF
C4 | Ceramic capacitor | 100nF
C5 | Ceramic capacitor | 100nF
IC1 | Non inverting bus transceiver | 74xx245
IC2 | 4-bit D-Type Register with 3 state outputs | 74xx173
IC3 | 4-bit D-Type Register with 3 state outputs | 74xx173
JP1 | Pin Header, THT, pitch 2.54mm, Dual Row, Vertical | 12p
P1 | Pin Header, THT, pitch 2.54mm, Dual Row, Vertical | 16p
P2 | Pin Header, THT, pitch 2.54mm, Dual Row, Vertical | 32p
P3 | Socket Header, THT, pitch 2.54mm, Dual Row, Vertical | 24p
P4 | Pin Header, THT, pitch 2.54mm, Dual Row, Vertical | 8p
