mylabpcb/myCPU/Docs/myCPU_Reset_IO_module_full.pdf

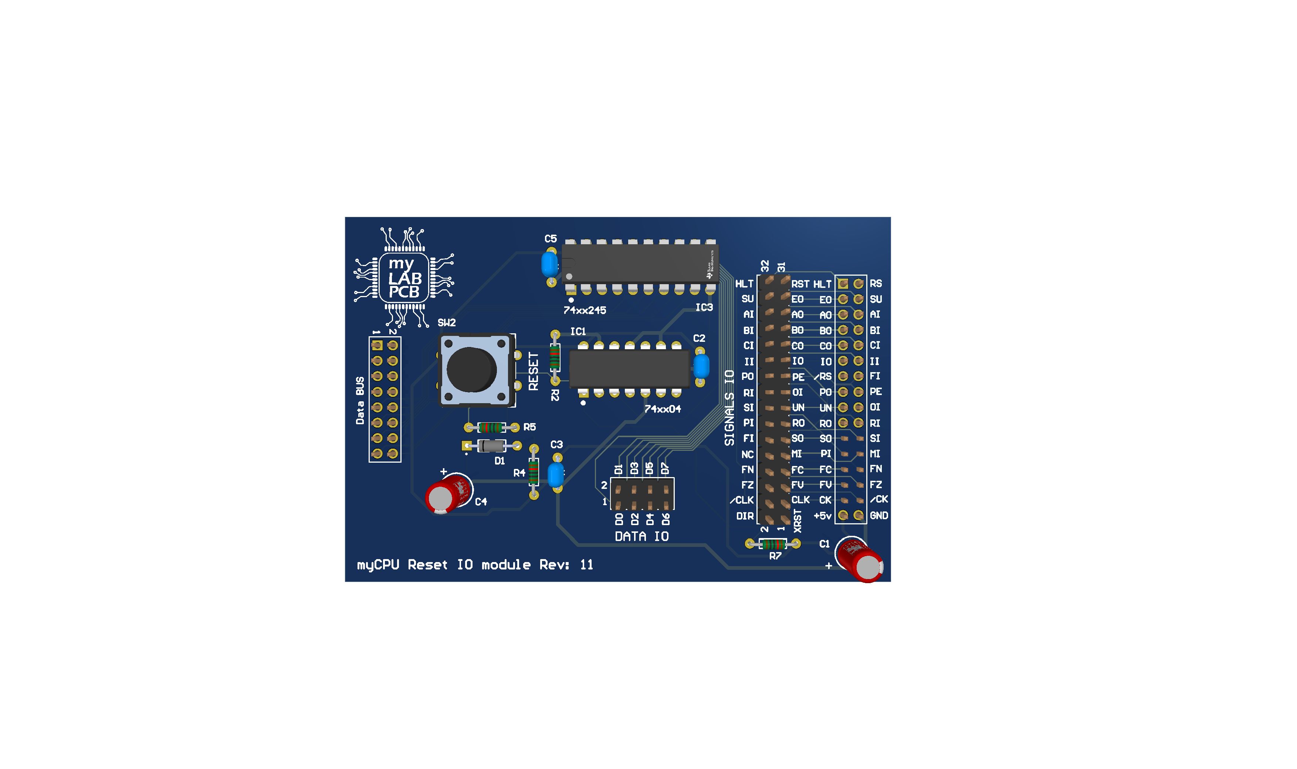
[picture p160: page 1]

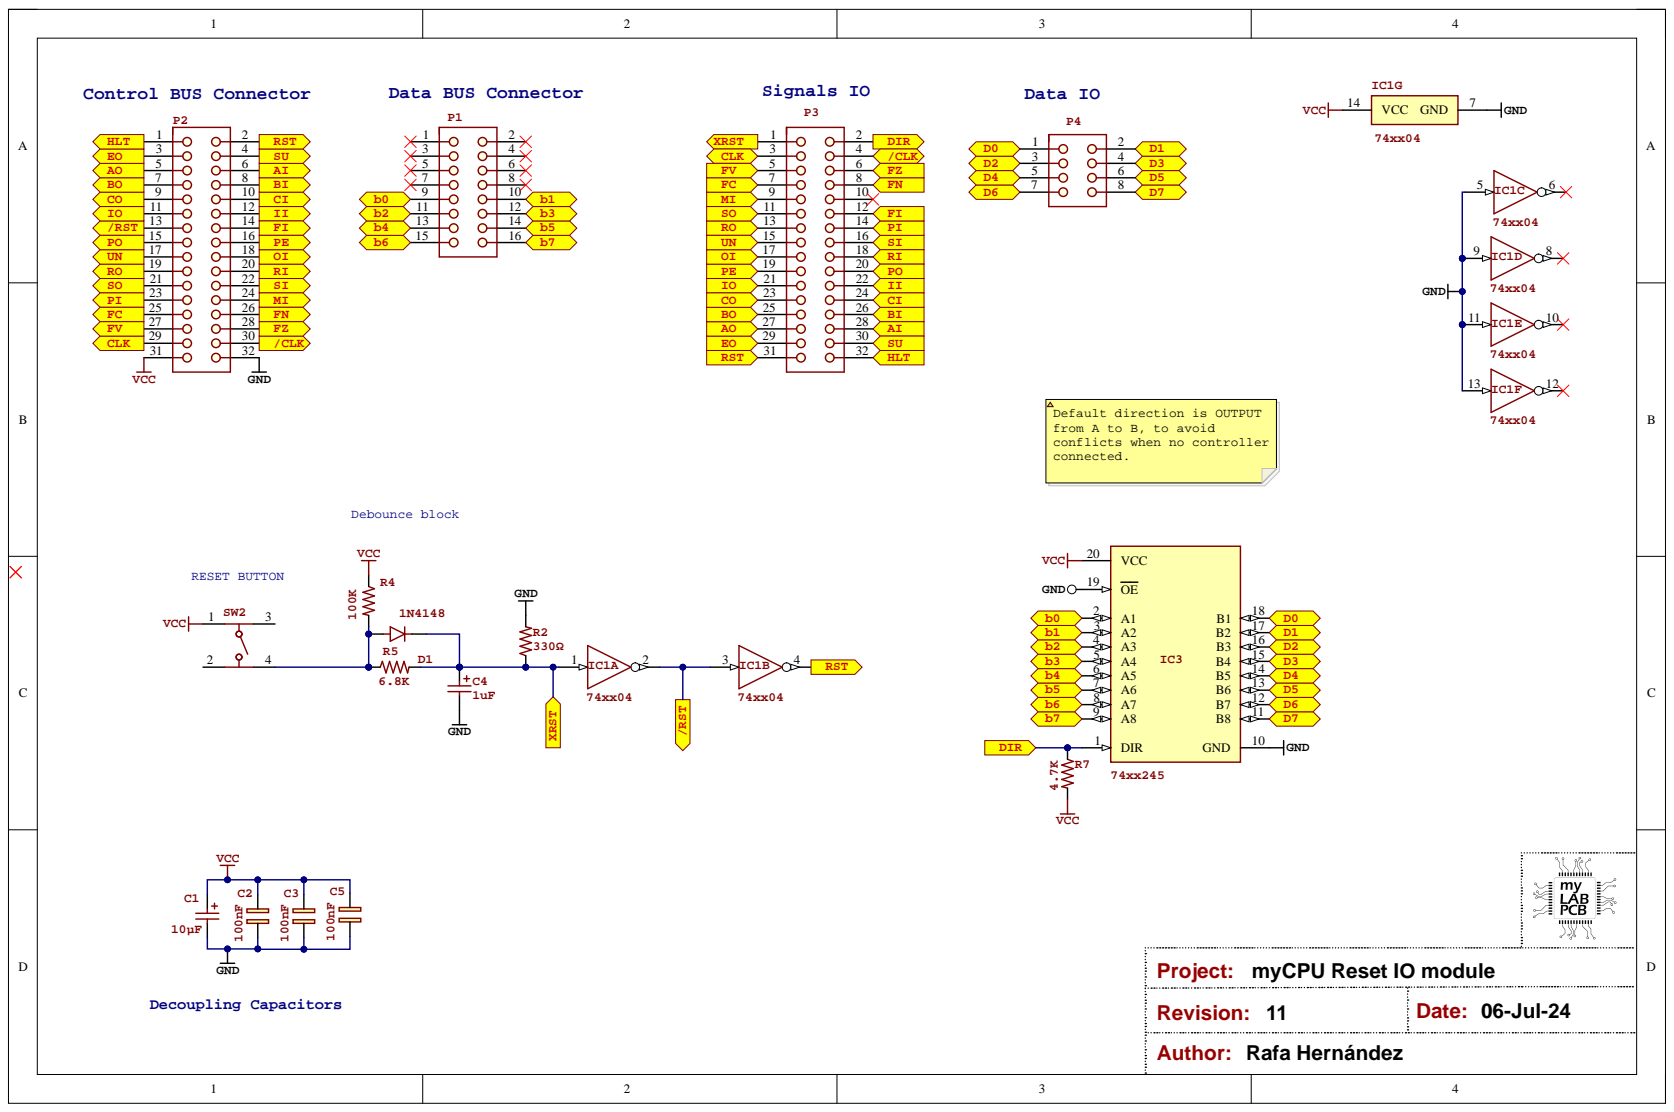
[picture p161: page 3]

Default direction is OUTPUT
from A to B, to avoid
conflicts when no controller
connected.

Project: myCPU Reset IO module

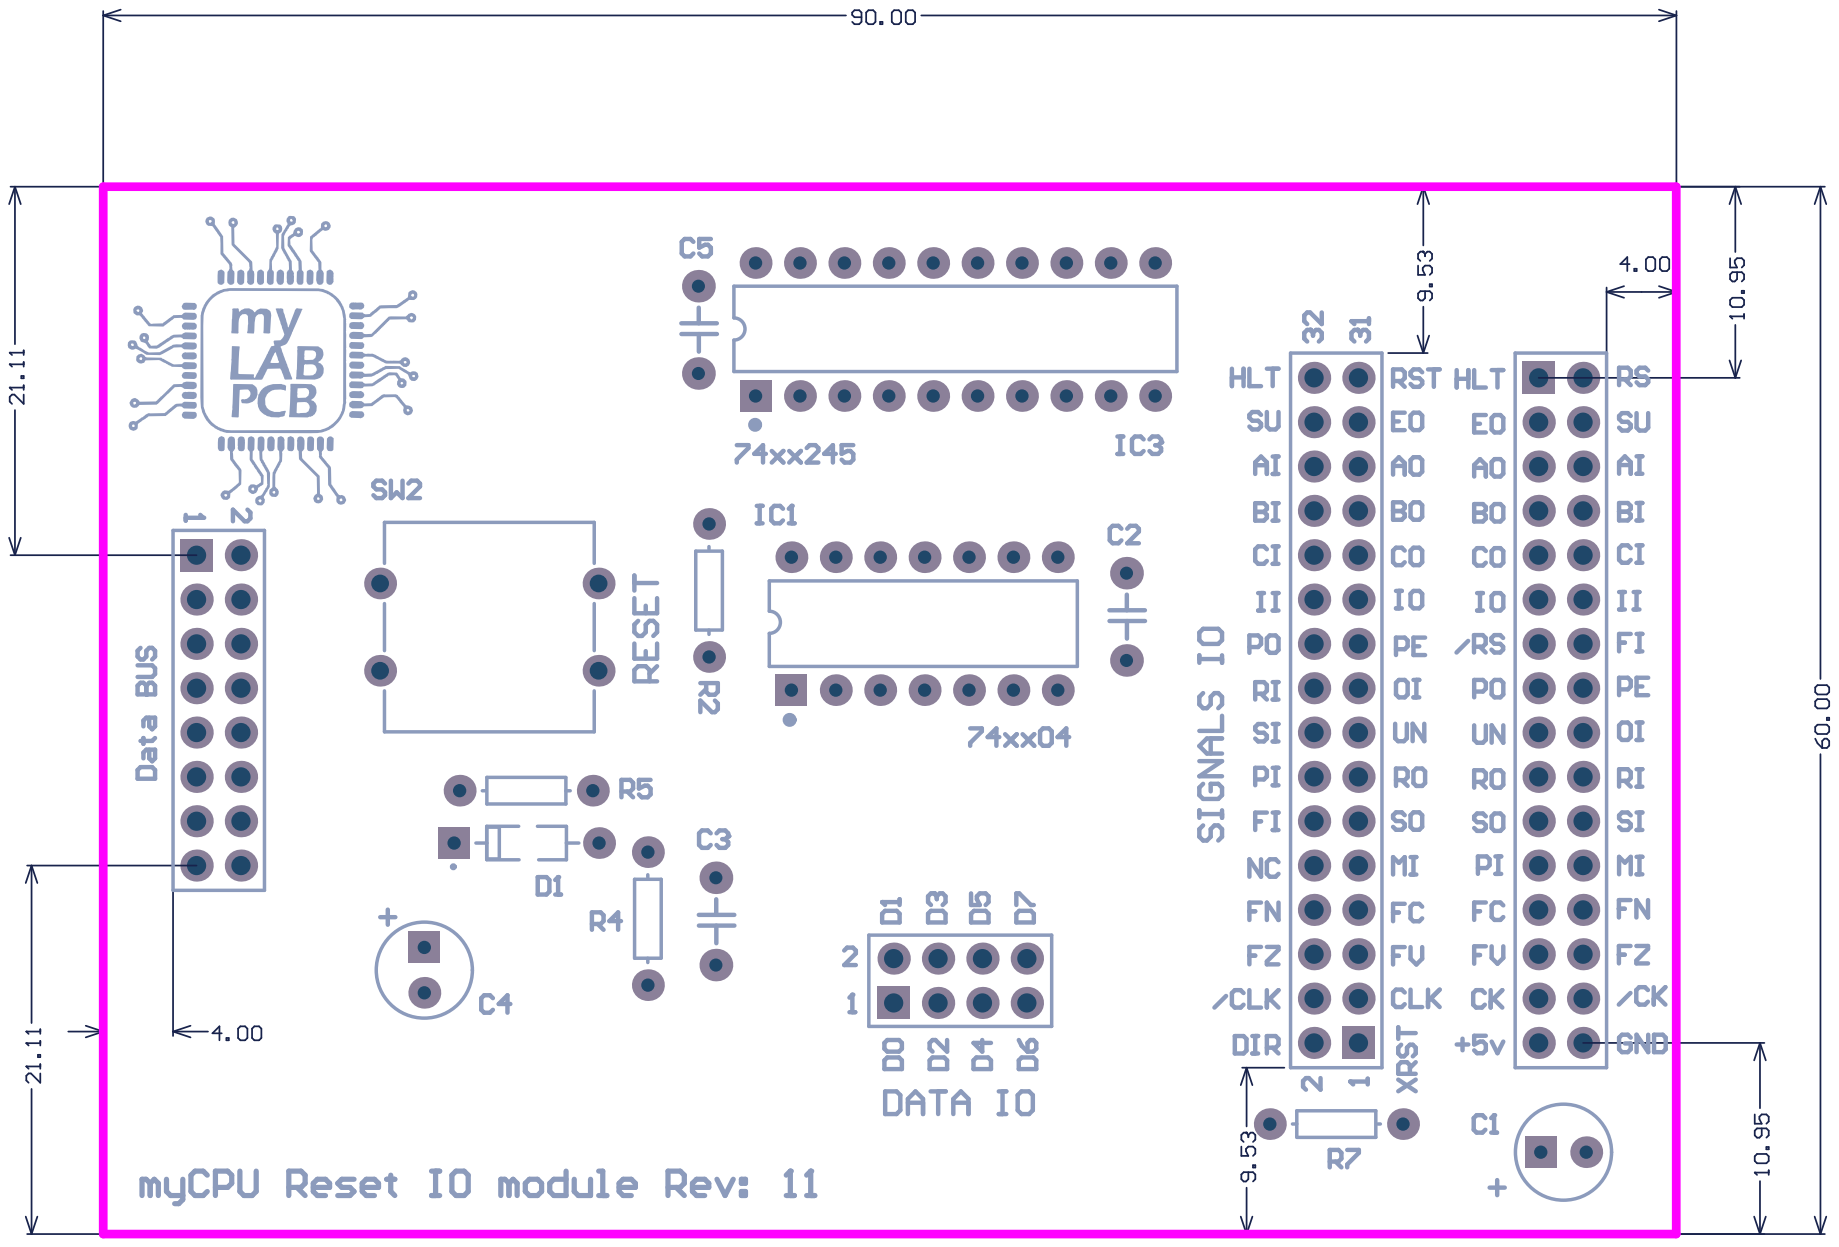
[picture p162: page 4]

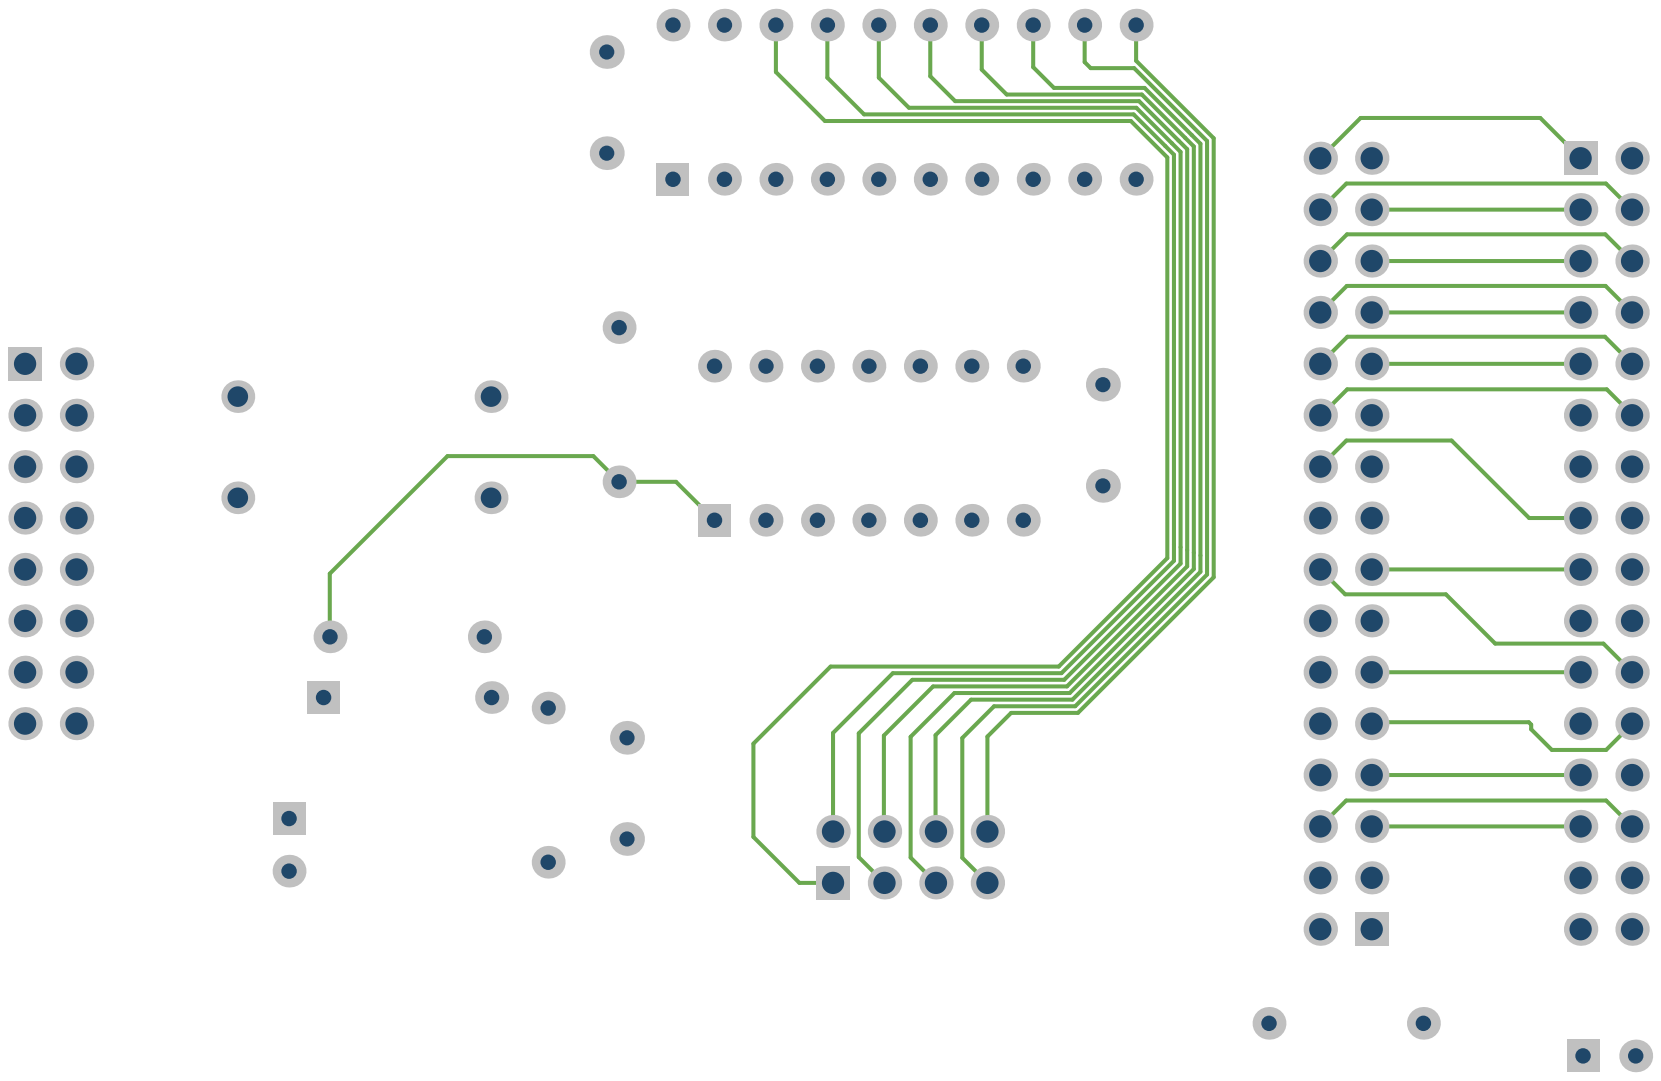
[picture p163: page 5]

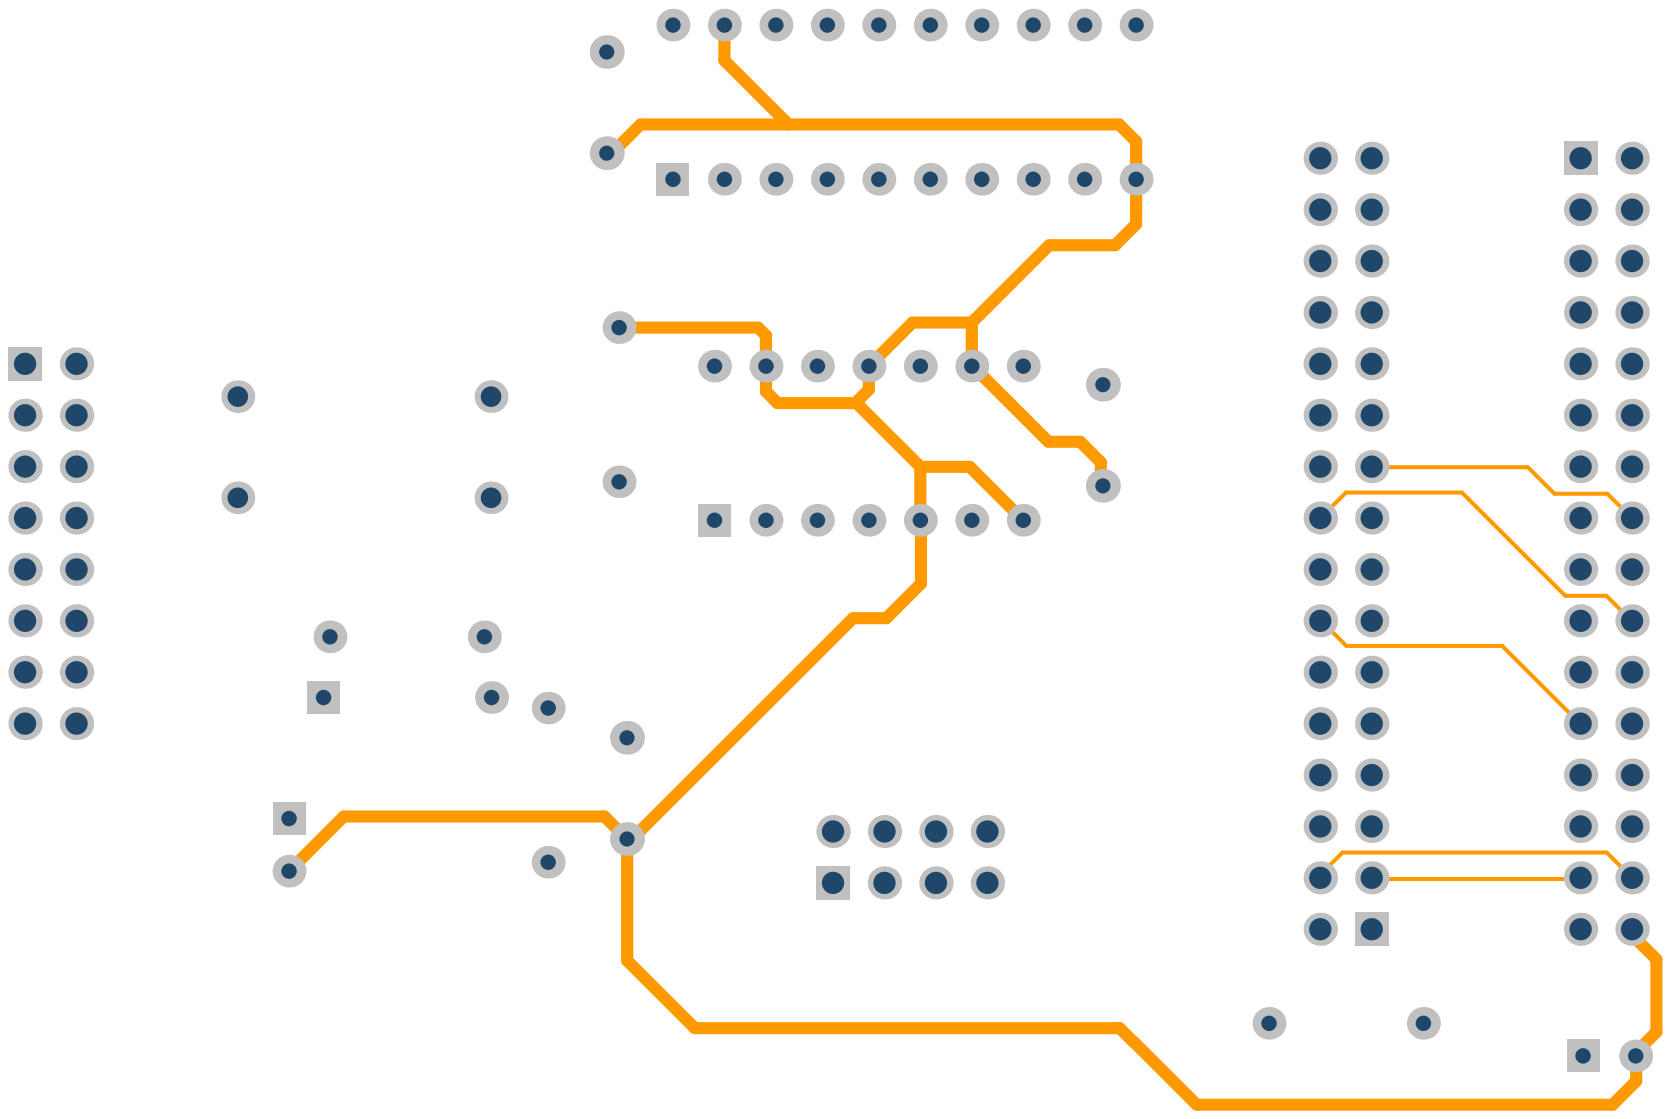
[picture p164: page 6]

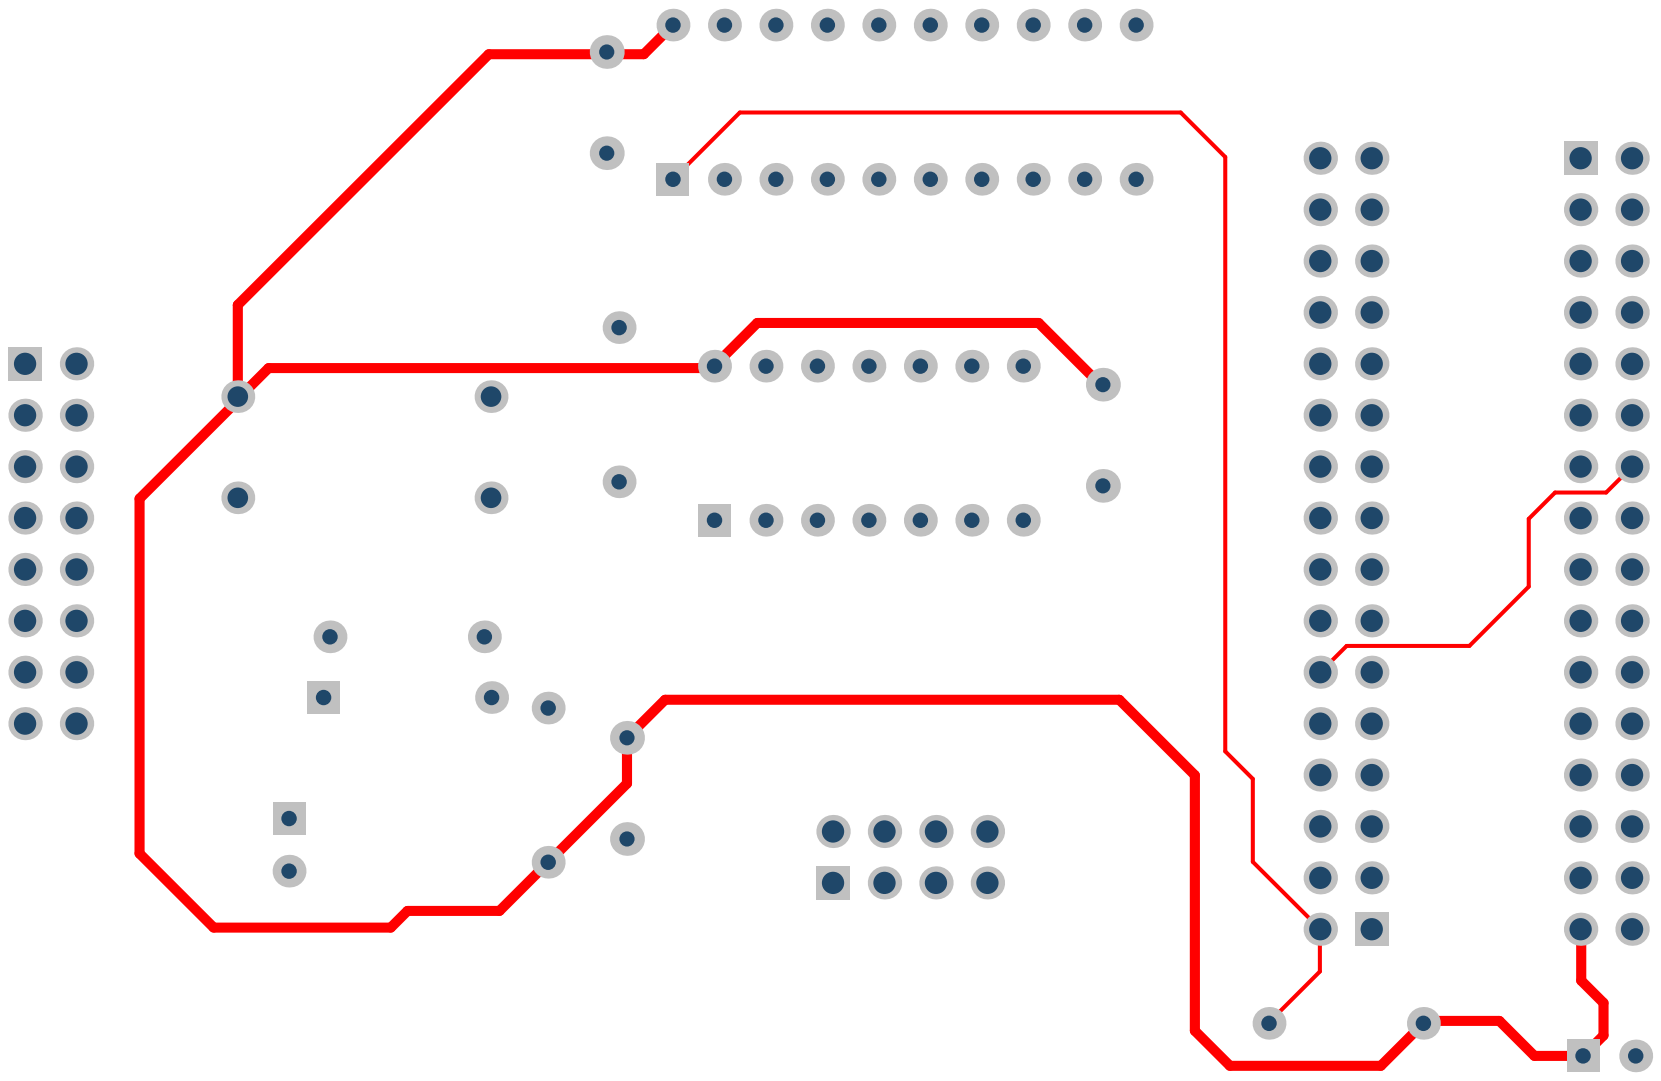
[picture p165: page 7]

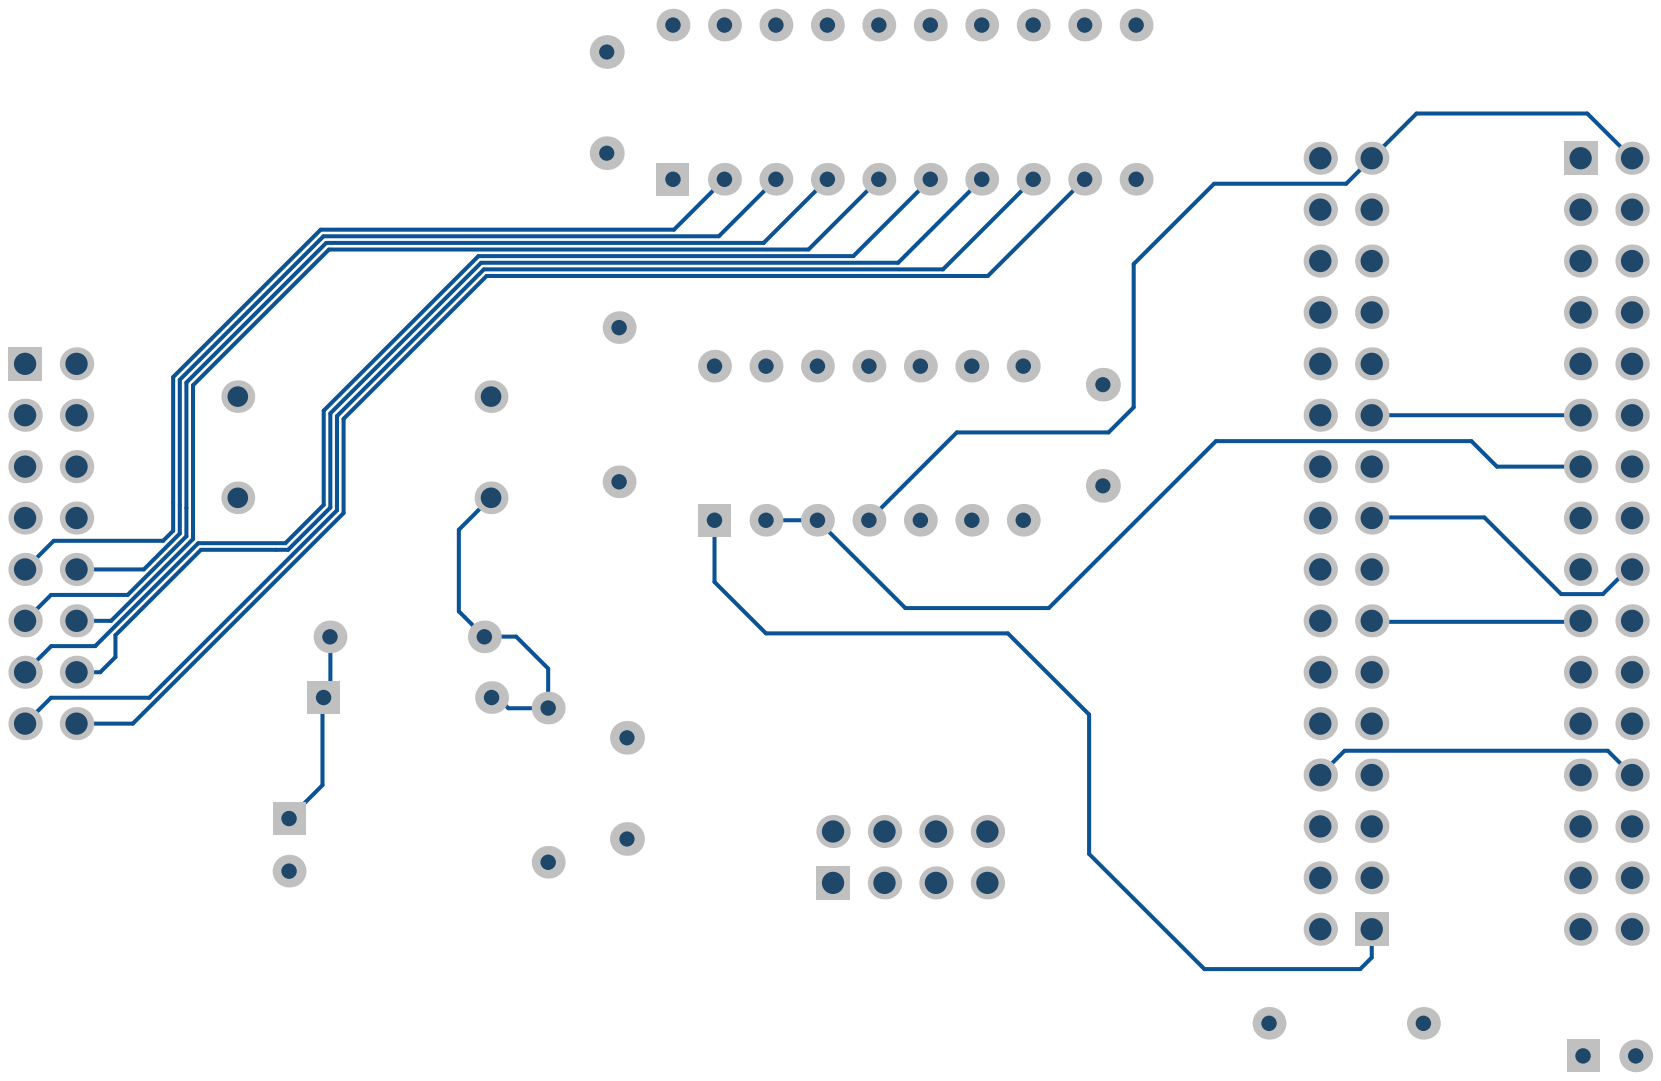
[picture p166: page 8]

# Bill of Materials

# myCPU Reset IO module

Description | Value | Q
Electrolytic capacitor 16v/50v | 10µF | 1
Ceramic capacitor | 100nF | 2
Electrolytic capacitor 16v/50v | 1uF | 1
Switching Signal Diode | 1N4148 | 1
Hex inverters | 74xx04 | 1
Non inverting bus transceiver | 74xx245 | 1
Pin Header, THT, pitch 2.54mm, Dual Row, Vertical | 16p | 1
Pin Header, THT, pitch 2.54mm, Dual Row, Vertical | 32p | 2
Pin Header, THT, pitch 2.54mm, Dual Row, Vertical | 8p | 1
Resistor Axial | 330 | 1
Resistor Axial | 100K | 1
Resistor Axial | 6.8K | 1
Resistor Axial | 4.7K | 1
Tactile button 12 mm | 12mm | 1

# Assembly List

## myCPU Reset IO module

Designator | Description | Value
C1 | Electrolytic capacitor 16v/50v | 10µF
C2 | Ceramic capacitor | 100nF
C4 | Electrolytic capacitor 16v/50v | 1uF
C5 | Ceramic capacitor | 100nF
D1 | Switching Signal Diode | 1N4148
IC1 | Hex inverters | 74xx04
IC3 | Non inverting bus transceiver | 74xx245
P1 | Pin Header, THT, pitch 2.54mm, Dual Row, Vertical | 16p
P2 | Pin Header, THT, pitch 2.54mm, Dual Row, Vertical | 32p
P3 | Pin Header, THT, pitch 2.54mm, Dual Row, Vertical | 32p
P4 | Pin Header, THT, pitch 2.54mm, Dual Row, Vertical | 8p
R2 | Resistor Axial | 330
R4 | Resistor Axial | 100K
R5 | Resistor Axial | 6.8K
R7 | Resistor Axial | 4.7K
SW2 | Tactile button 12 mm | 12mm
