mylabpcb/myCPU/Documentation/myCPU_DisplayLED_16b_module_full.pdf

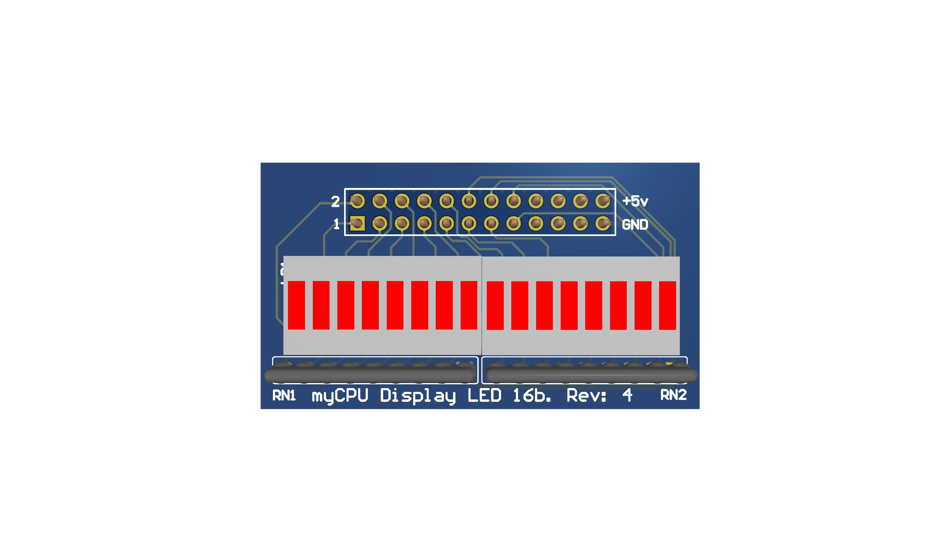
[picture p174: page 1]

## INPUT Data Connector

I12

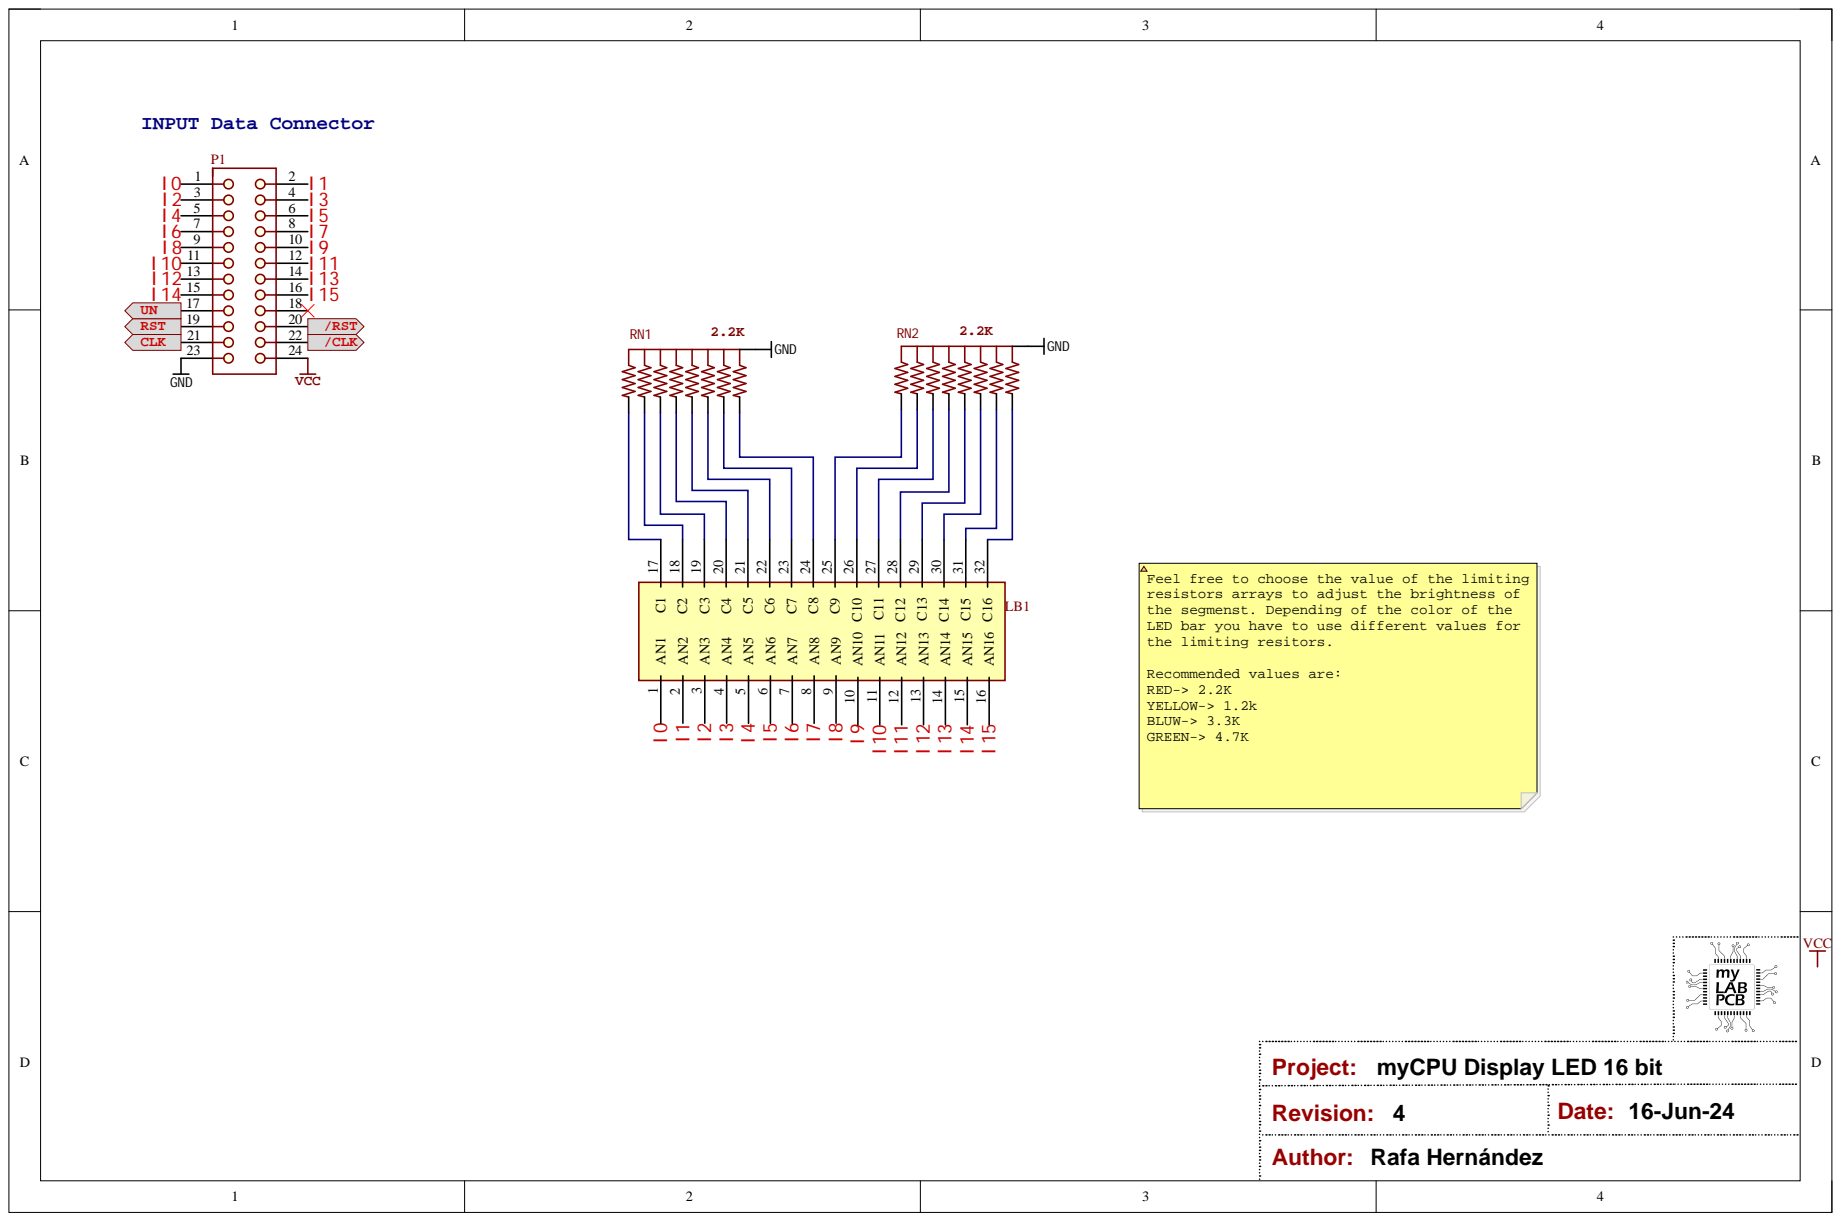
[picture p175: page 3]

Feel free to choose the value of the limiting
resistors arrays to adjust the brightness of
the segmenst. Depending of the color of the
LED bar you have to use different values for
the limiting resitors.

Project: myCPU Display LED 16 bit

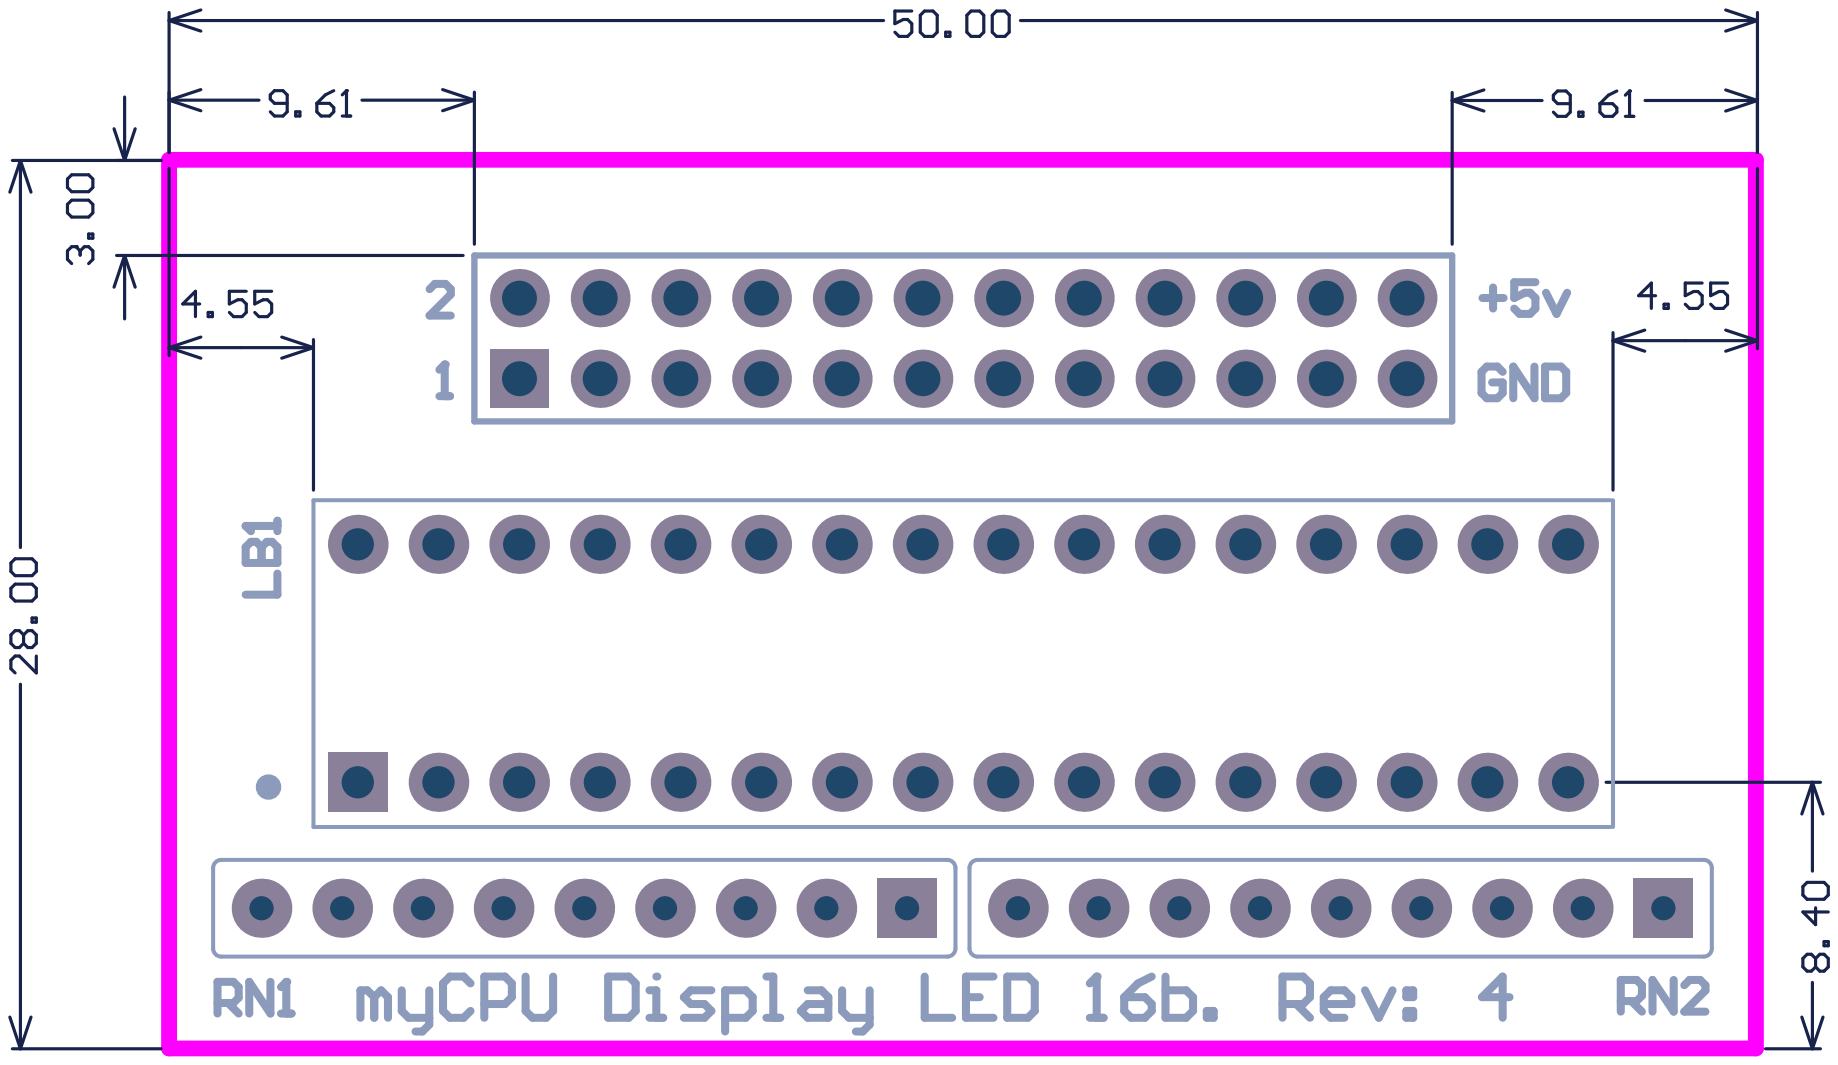
[picture p176: page 4]

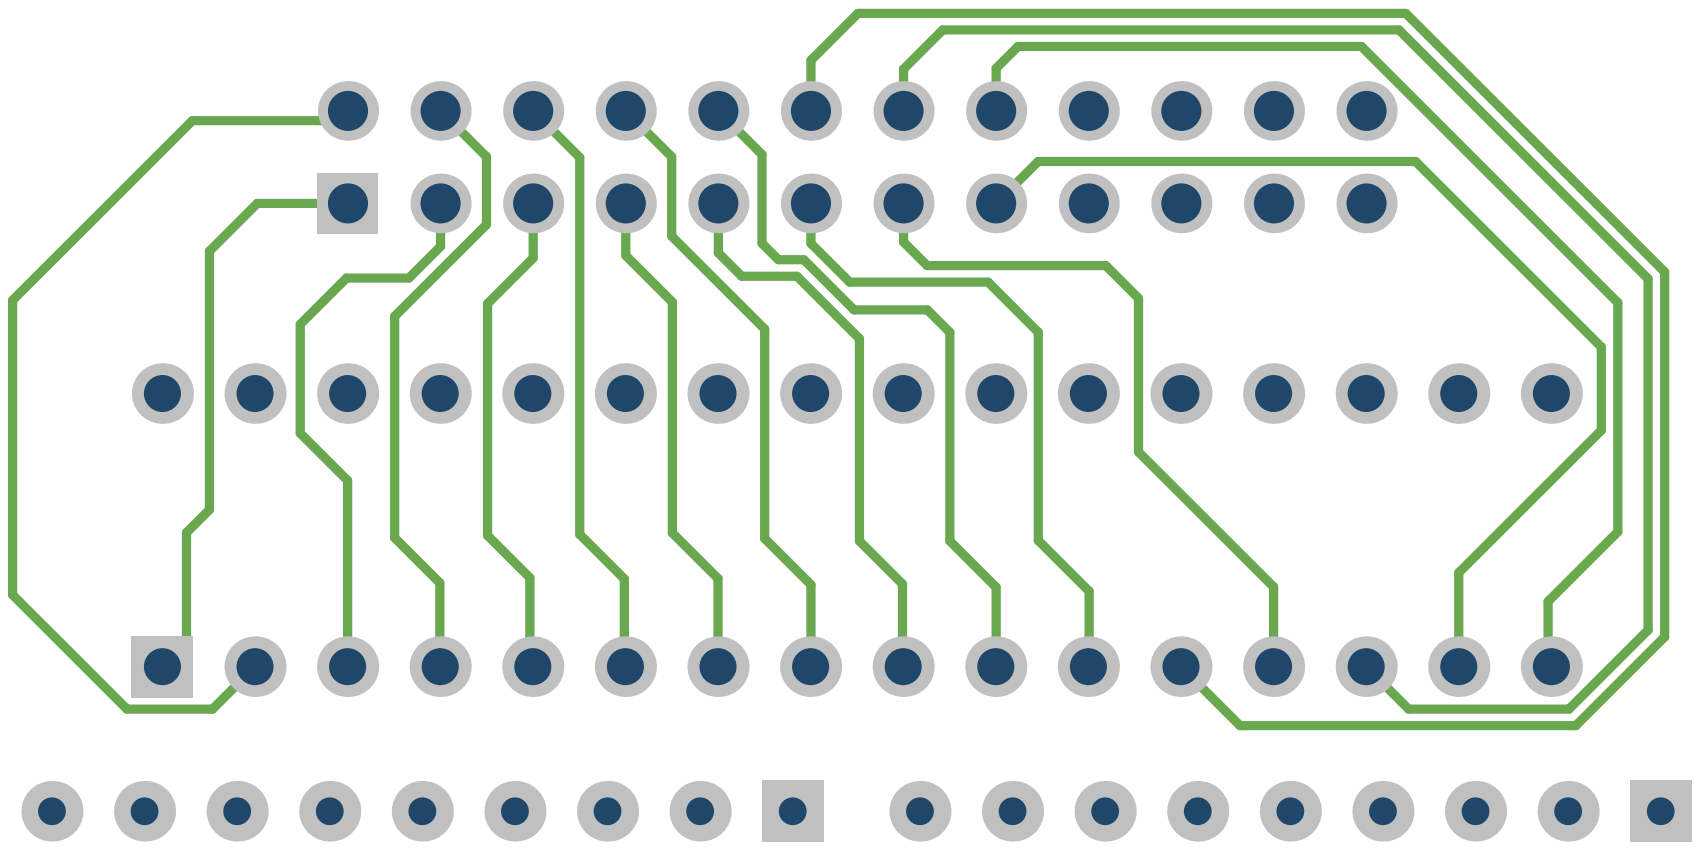
[picture p177: page 5]

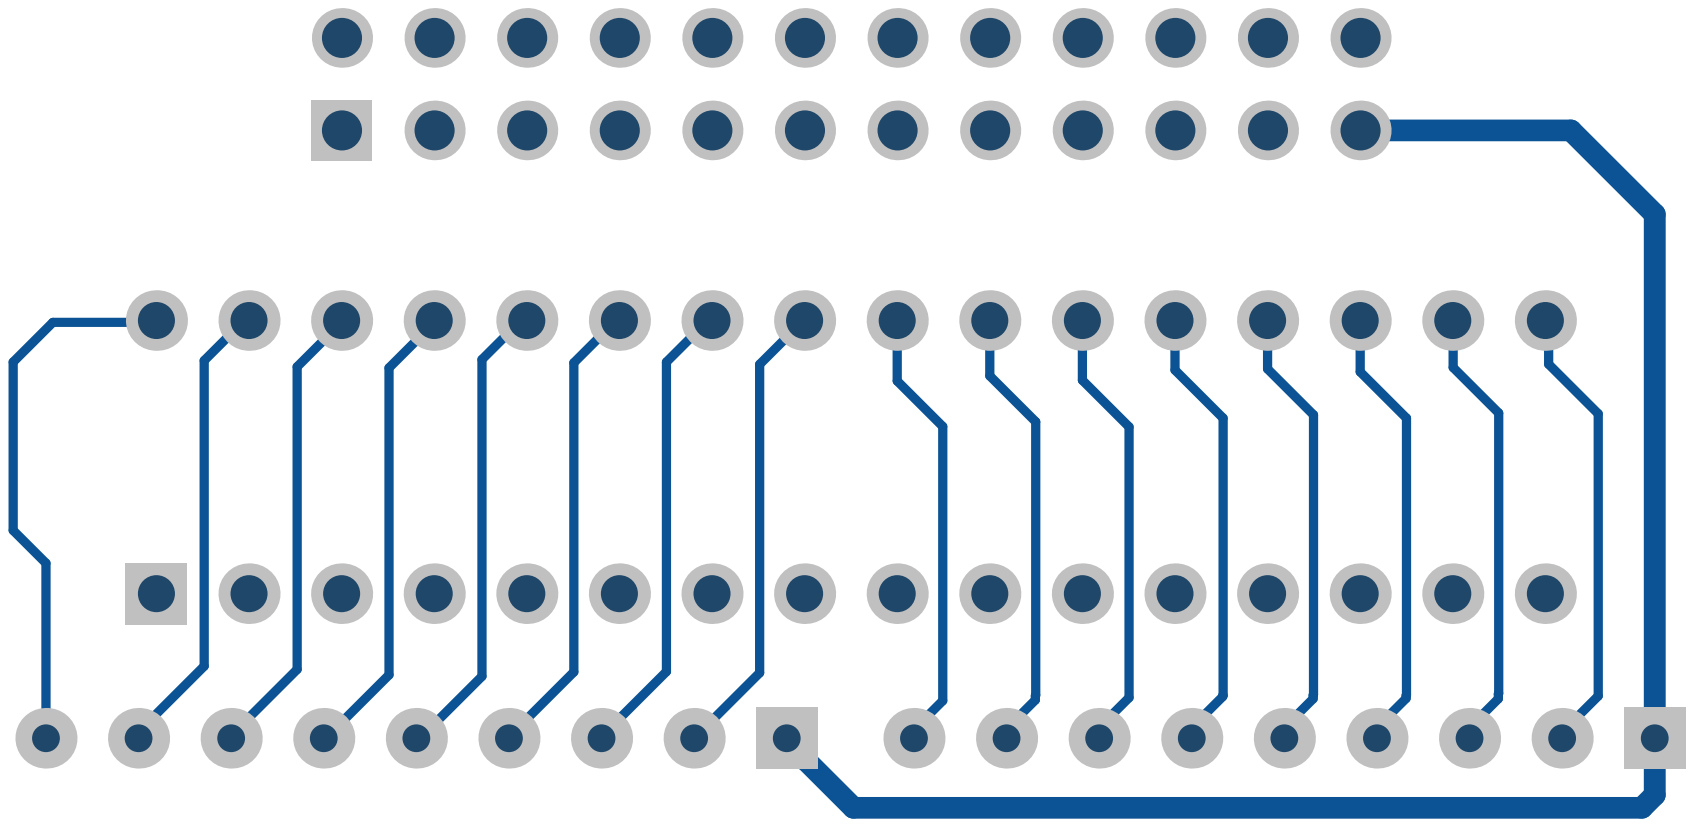
[picture p178: page 6]

# Bill of Materials

# myCPU Display LED 16 bit

Description | Value | Q
Led Indicator Bar 16 segments | | 1
Pin Header, THT, pitch 2.54mm, Dual Row, Vertical, 24p | 24p | 1
Resistor array 8 elements,9 pins | 220Ω | 2

# Assembly List

# myCPU Display LED 16 bit

Designator | Description | Value
LB1 | Led Indicator Bar 16 segments
P1 | Pin Header, THT, pitch 2.54mm, Dual Row, Vertical, 24p | 24p
RN1 | Resistor array 8 elements,9 pins | 220Ω
RN2 | Resistor array 8 elements,9 pins | 220Ω
