mylabpcb/myCPU/Documentation/myCPU_Output_Register_8b_module_full.pdf

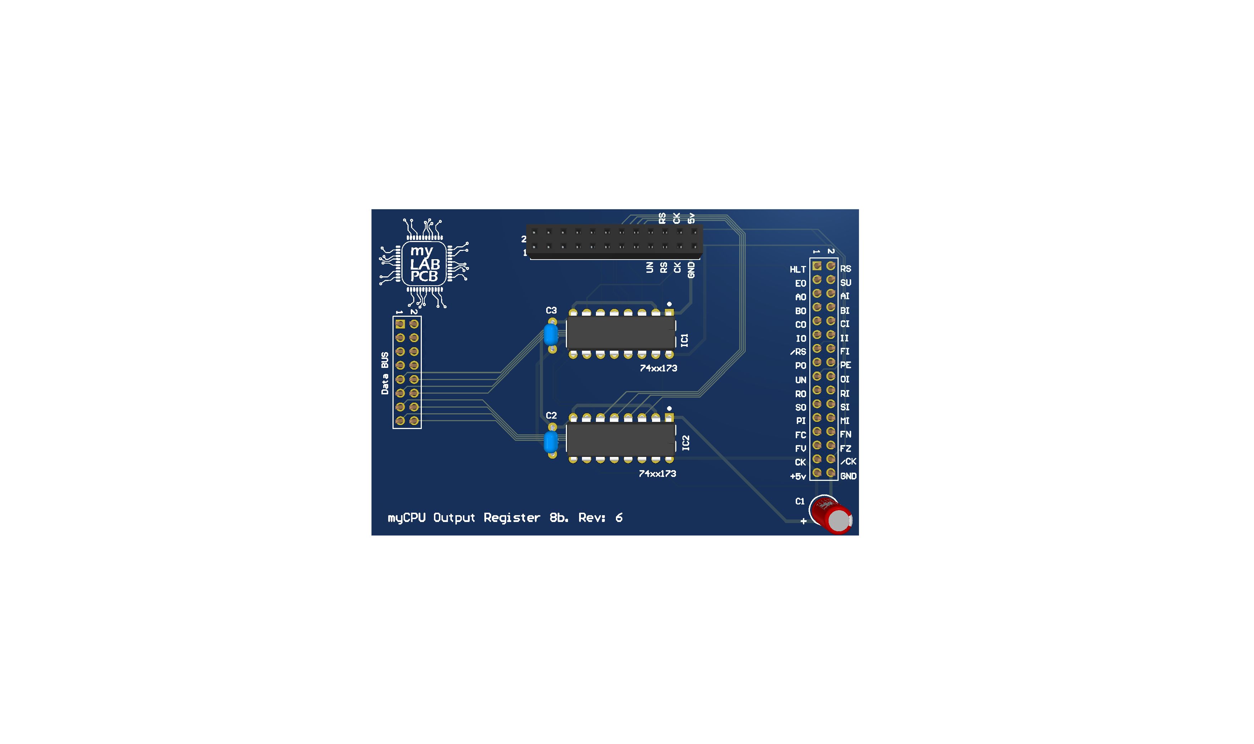
[picture p179: page 1]

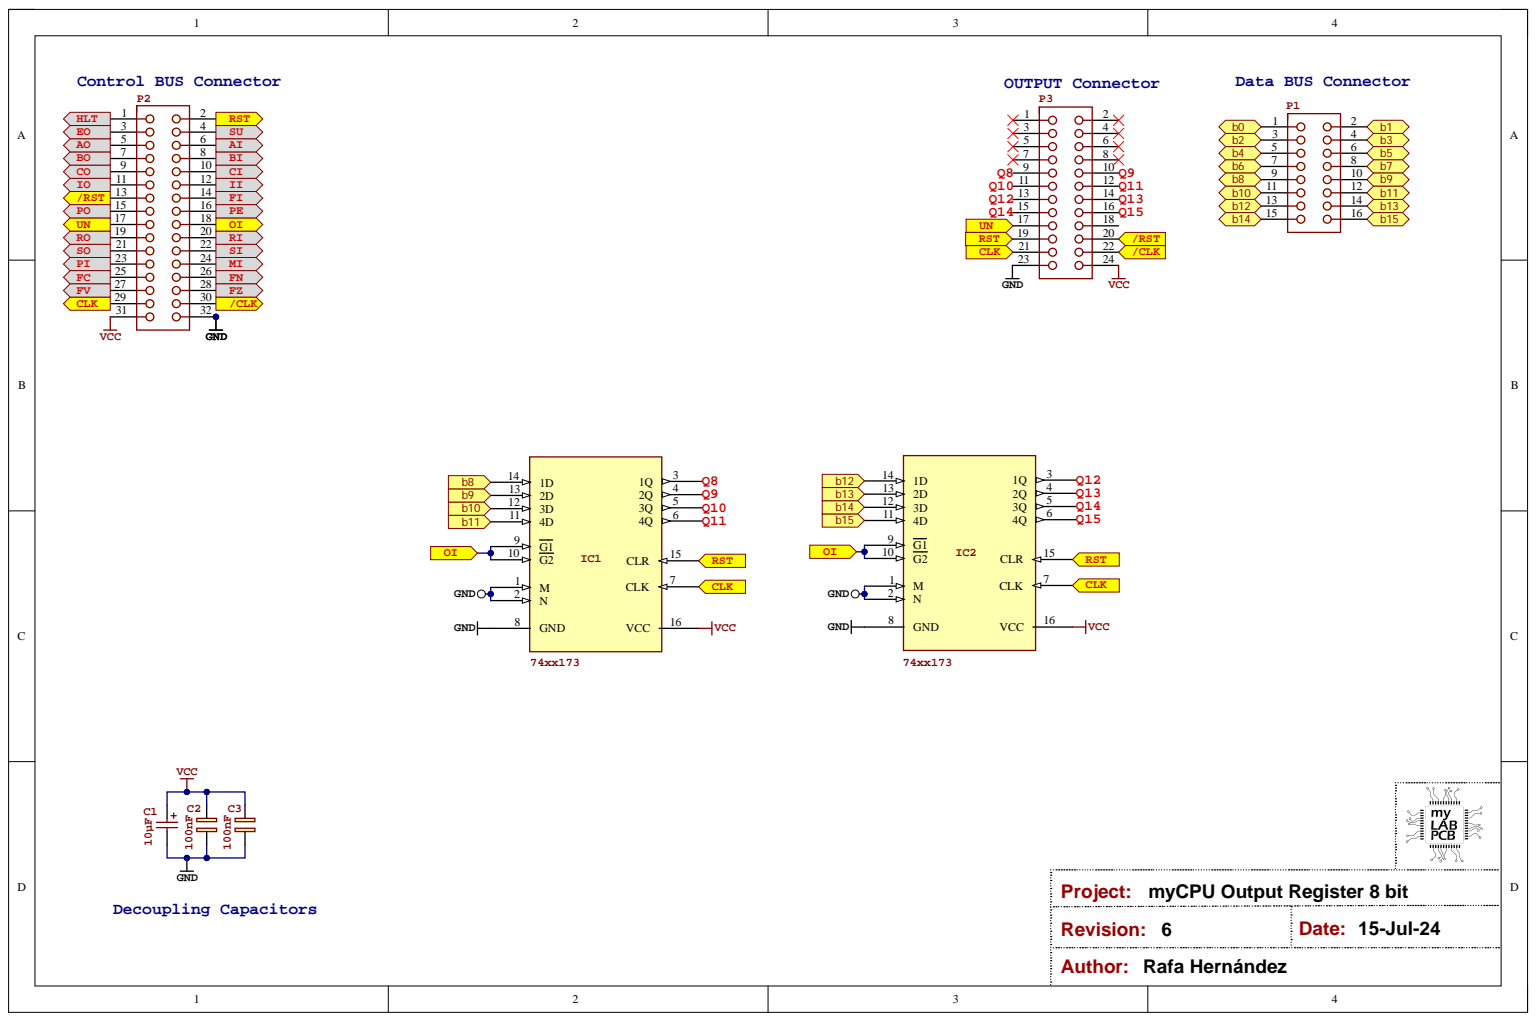
[picture p180: page 3]

Project: myCPU Output Register 8 bit

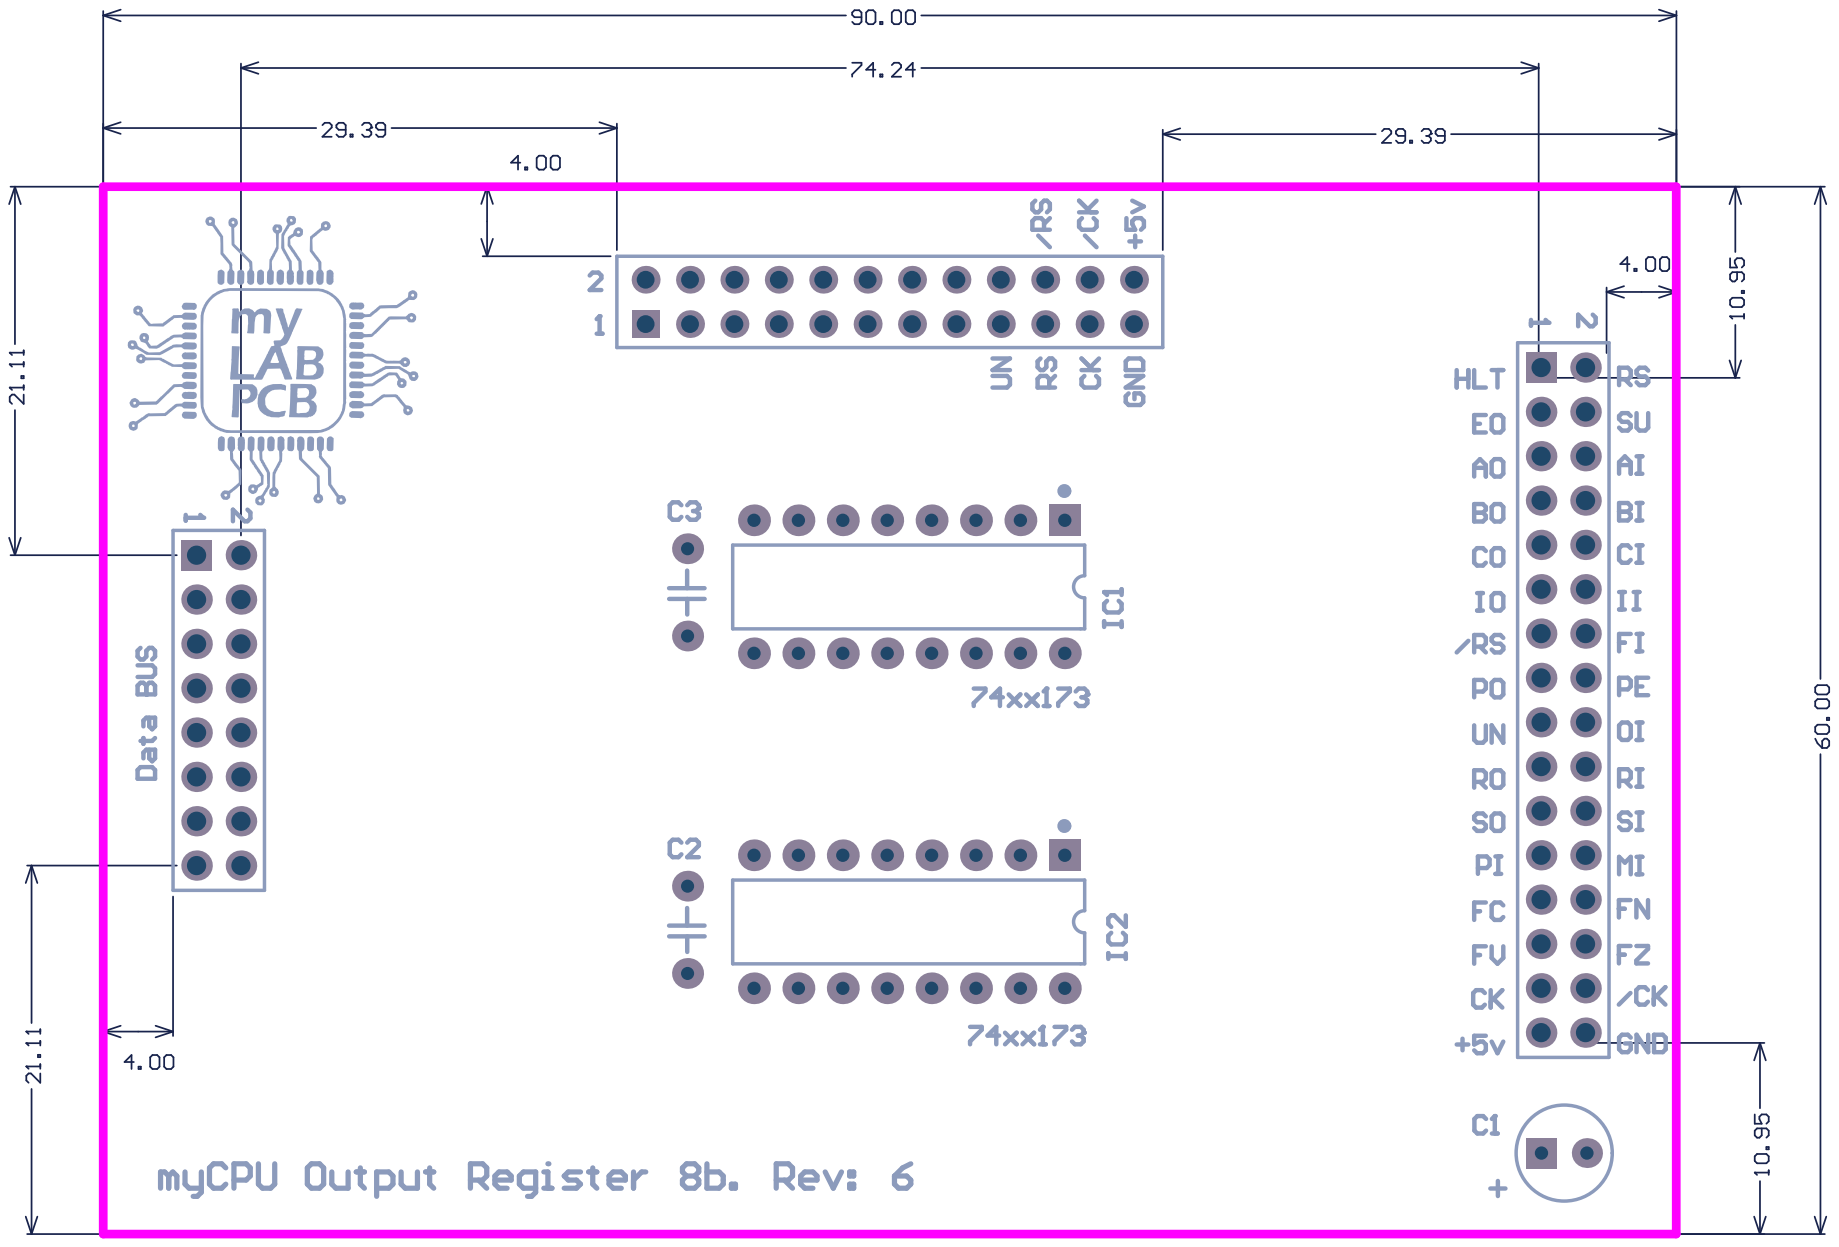
[picture p181: page 4]

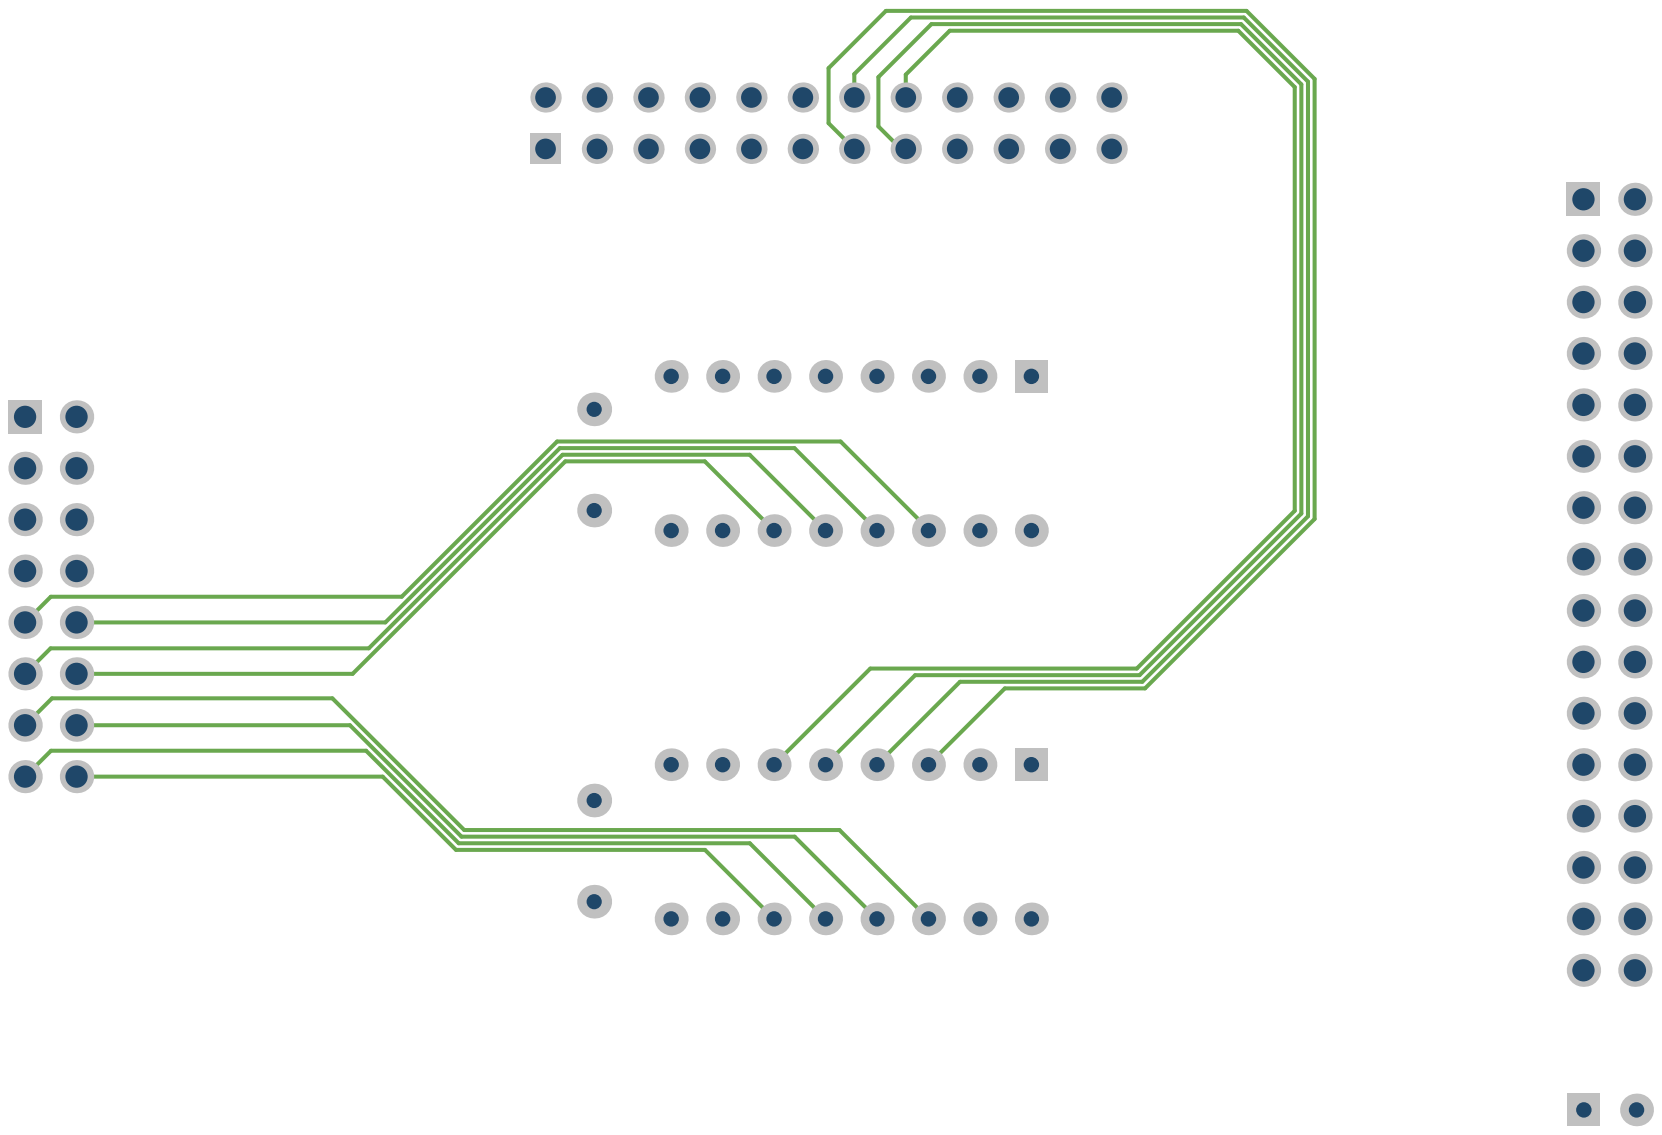
[picture p182: page 5]

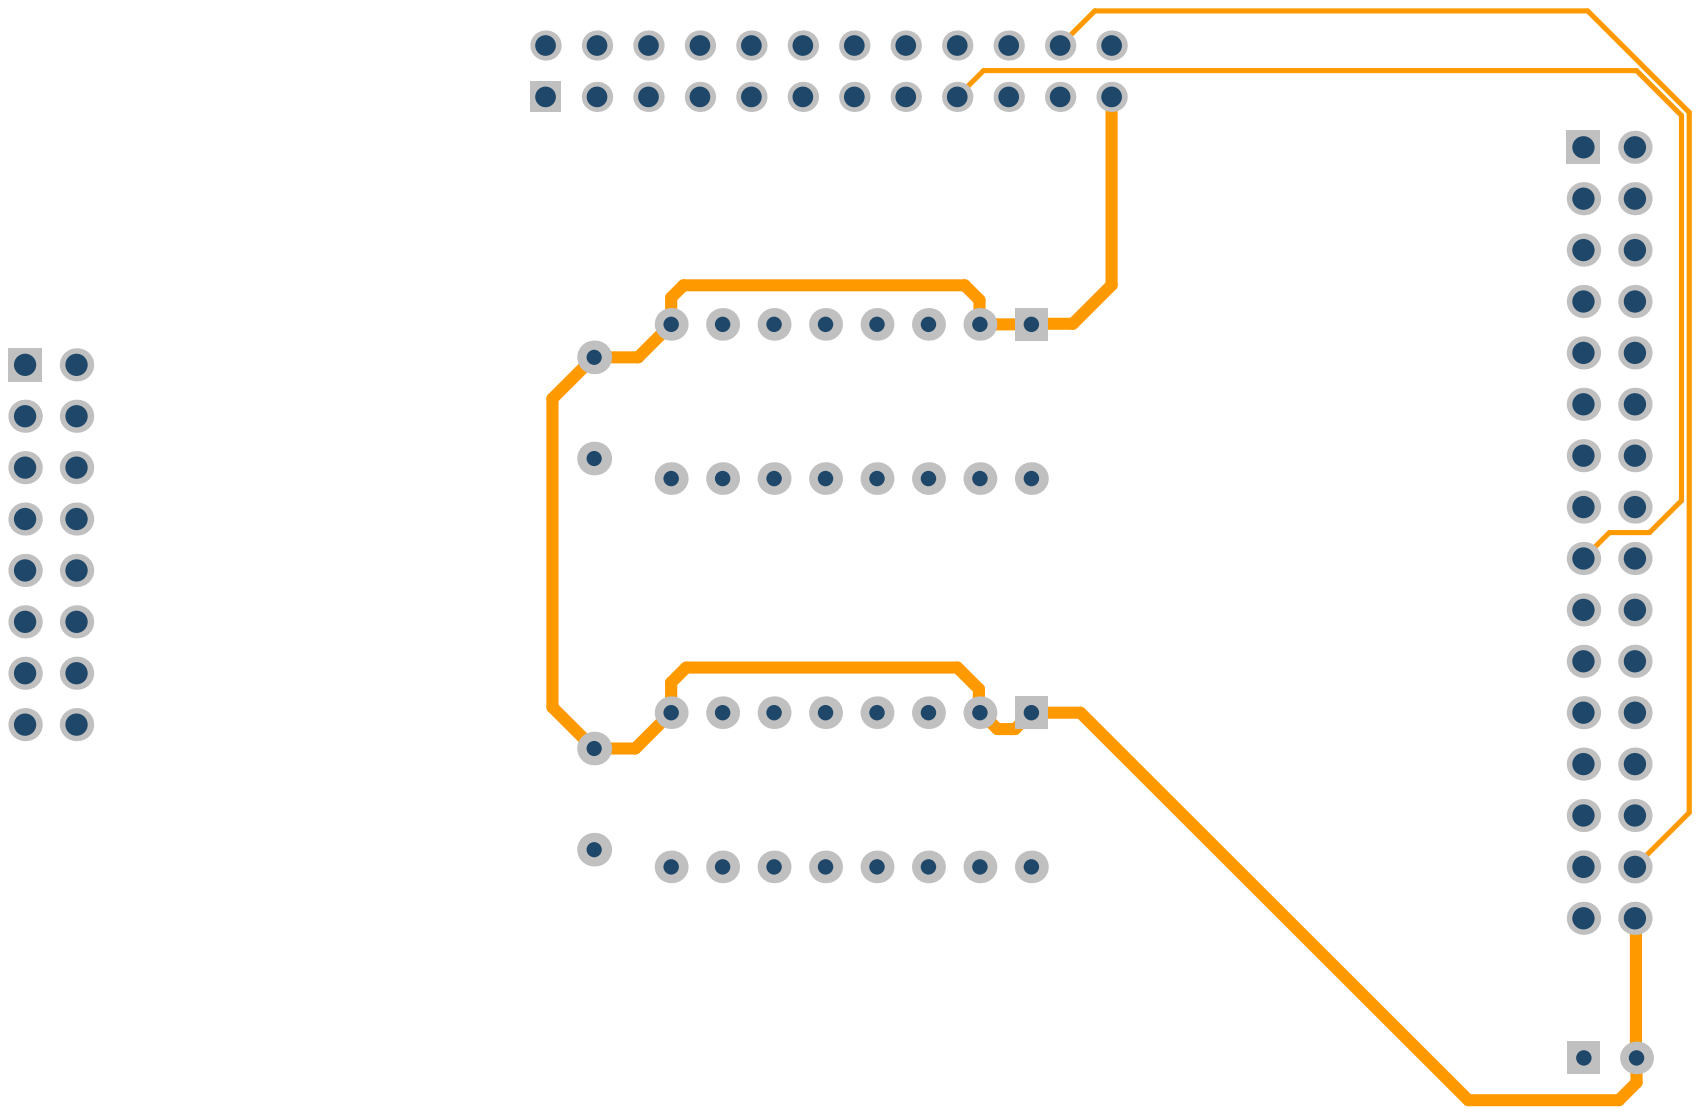
[picture p183: page 6]

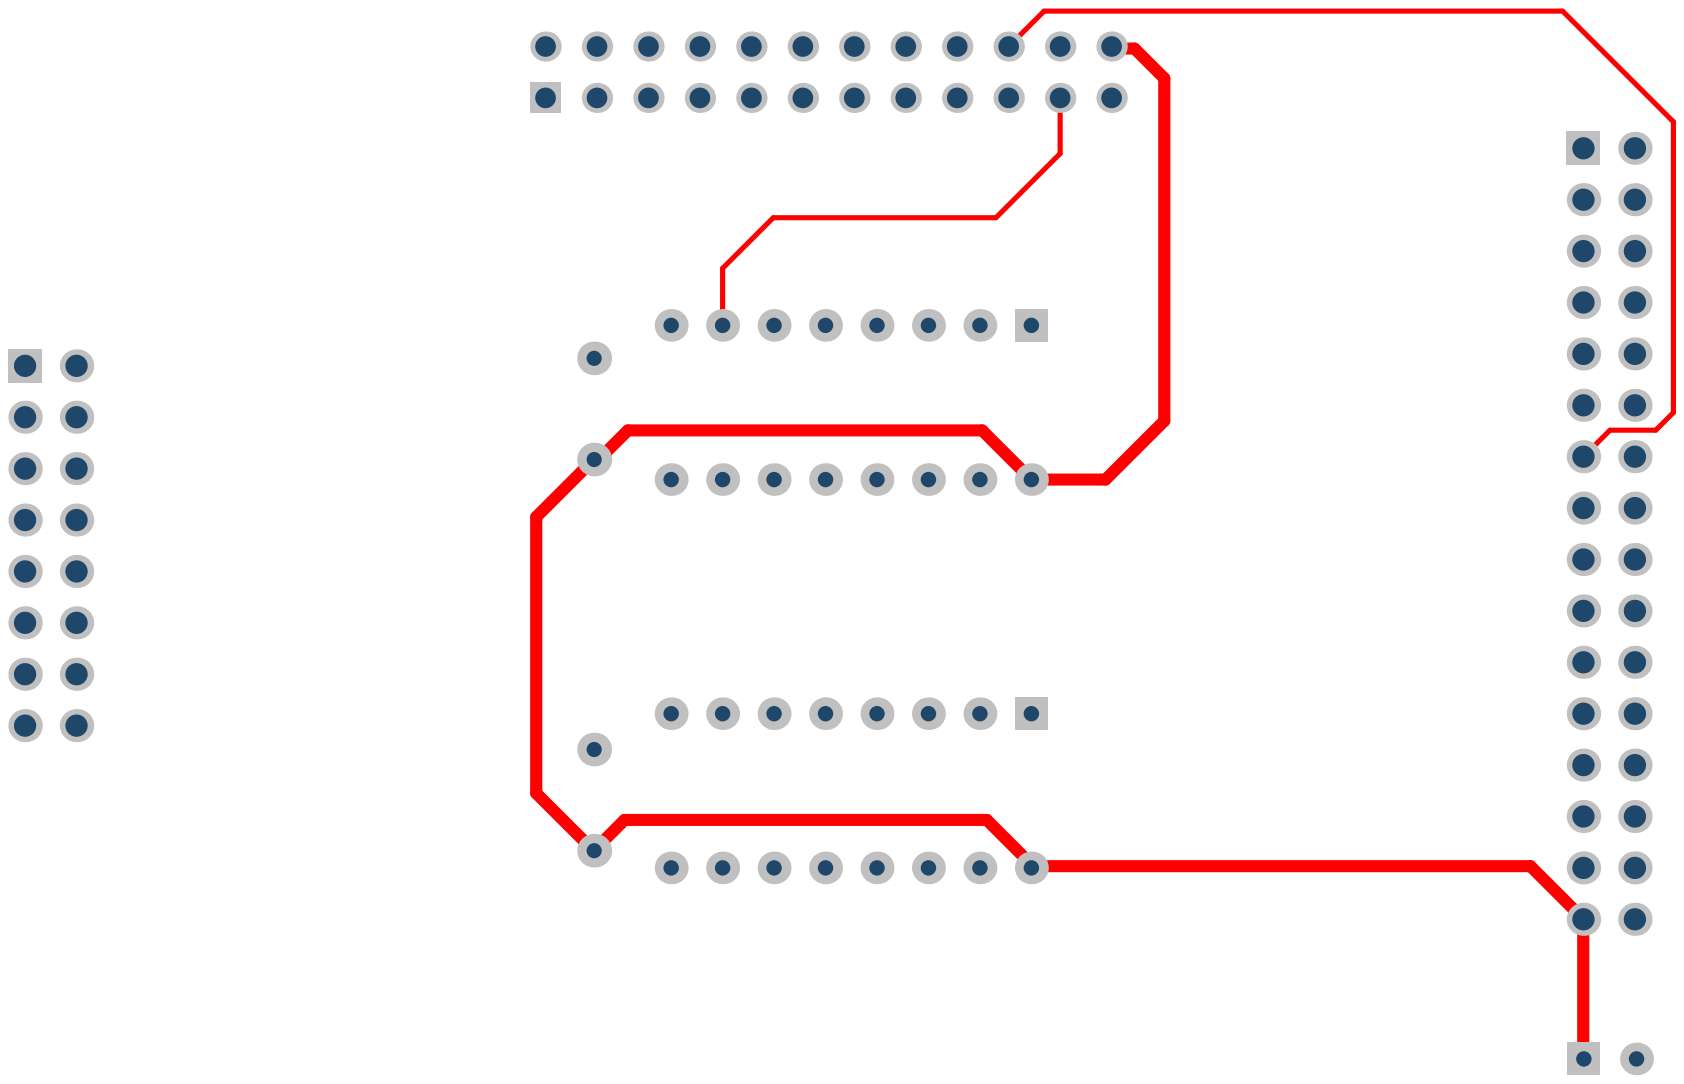
[picture p184: page 7]

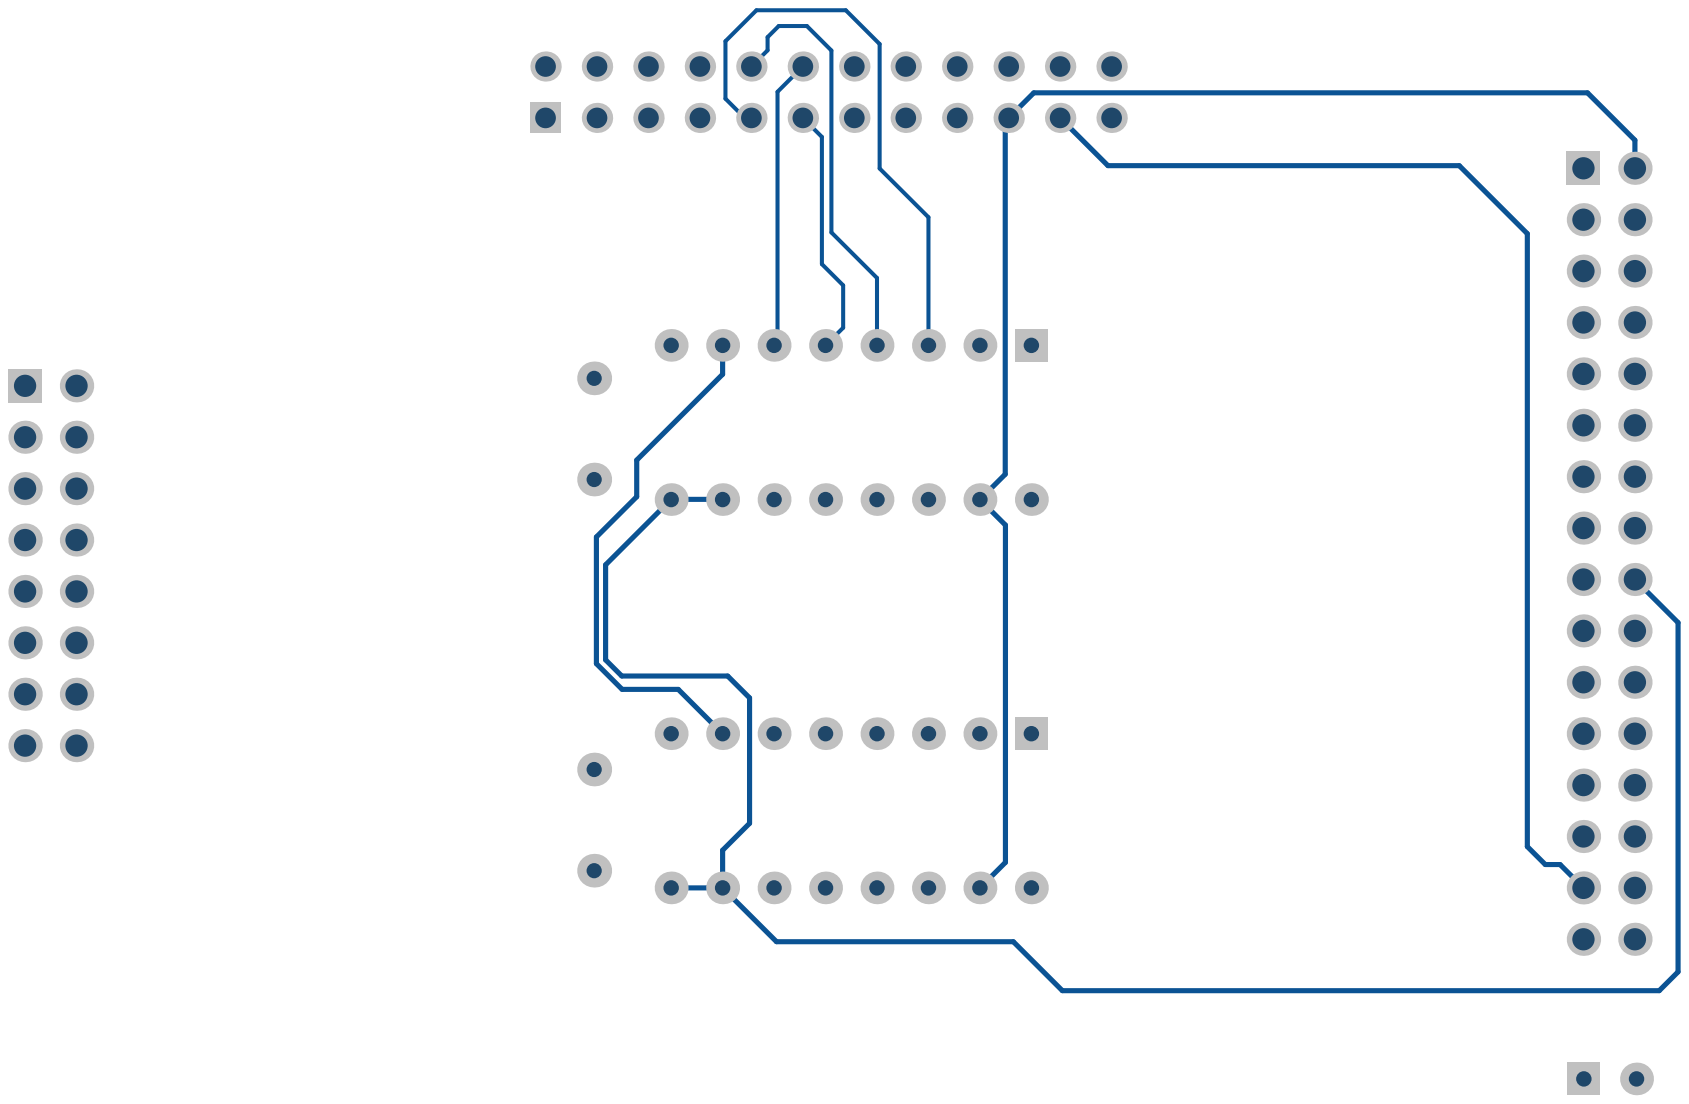
[picture p185: page 8]

# Bill of Materials

# myCPU Output Register 8 bit

Description | Value | Q
Electrolytic capacitor 16v/50v | 10µF | 1
Ceramic or tantalum capacitor | 100nF | 2
4-bit D-Type Register with 3 state outputs | 74xx173 | 2
Pin Header, THT, pitch 2.54mm, Dual Row, Vertical, 16p | 16p | 1
Pin Header, THT, pitch 2.54mm, Dual Row, Vertical, 32p | 32p | 1
Socket Header, THT, pitch 2.54mm, Dual Row, Vertical, 24p | 24p | 1

# Assembly List

## myCPU Output Register 8 bit

Designator | Description | Value
C1 | Electrolytic capacitor 16v/50v | 10µF
C2 | Ceramic or tantalum capacitor | 100nF
C3 | Ceramic or tantalum capacitor | 100nF
IC1 | 4-bit D-Type Register with 3 state outputs | 74xx173
IC2 | 4-bit D-Type Register with 3 state outputs | 74xx173
P1 | Pin Header, THT, pitch 2.54mm, Dual Row, Vertical, 16p | 16p
P2 | Pin Header, THT, pitch 2.54mm, Dual Row, Vertical, 32p | 32p
P3 | Socket Header, THT, pitch 2.54mm, Dual Row, Vertical, 24p | 24p
