mylabpcb/myCPU/Docs/myCPU_Protoboard_L.pdf

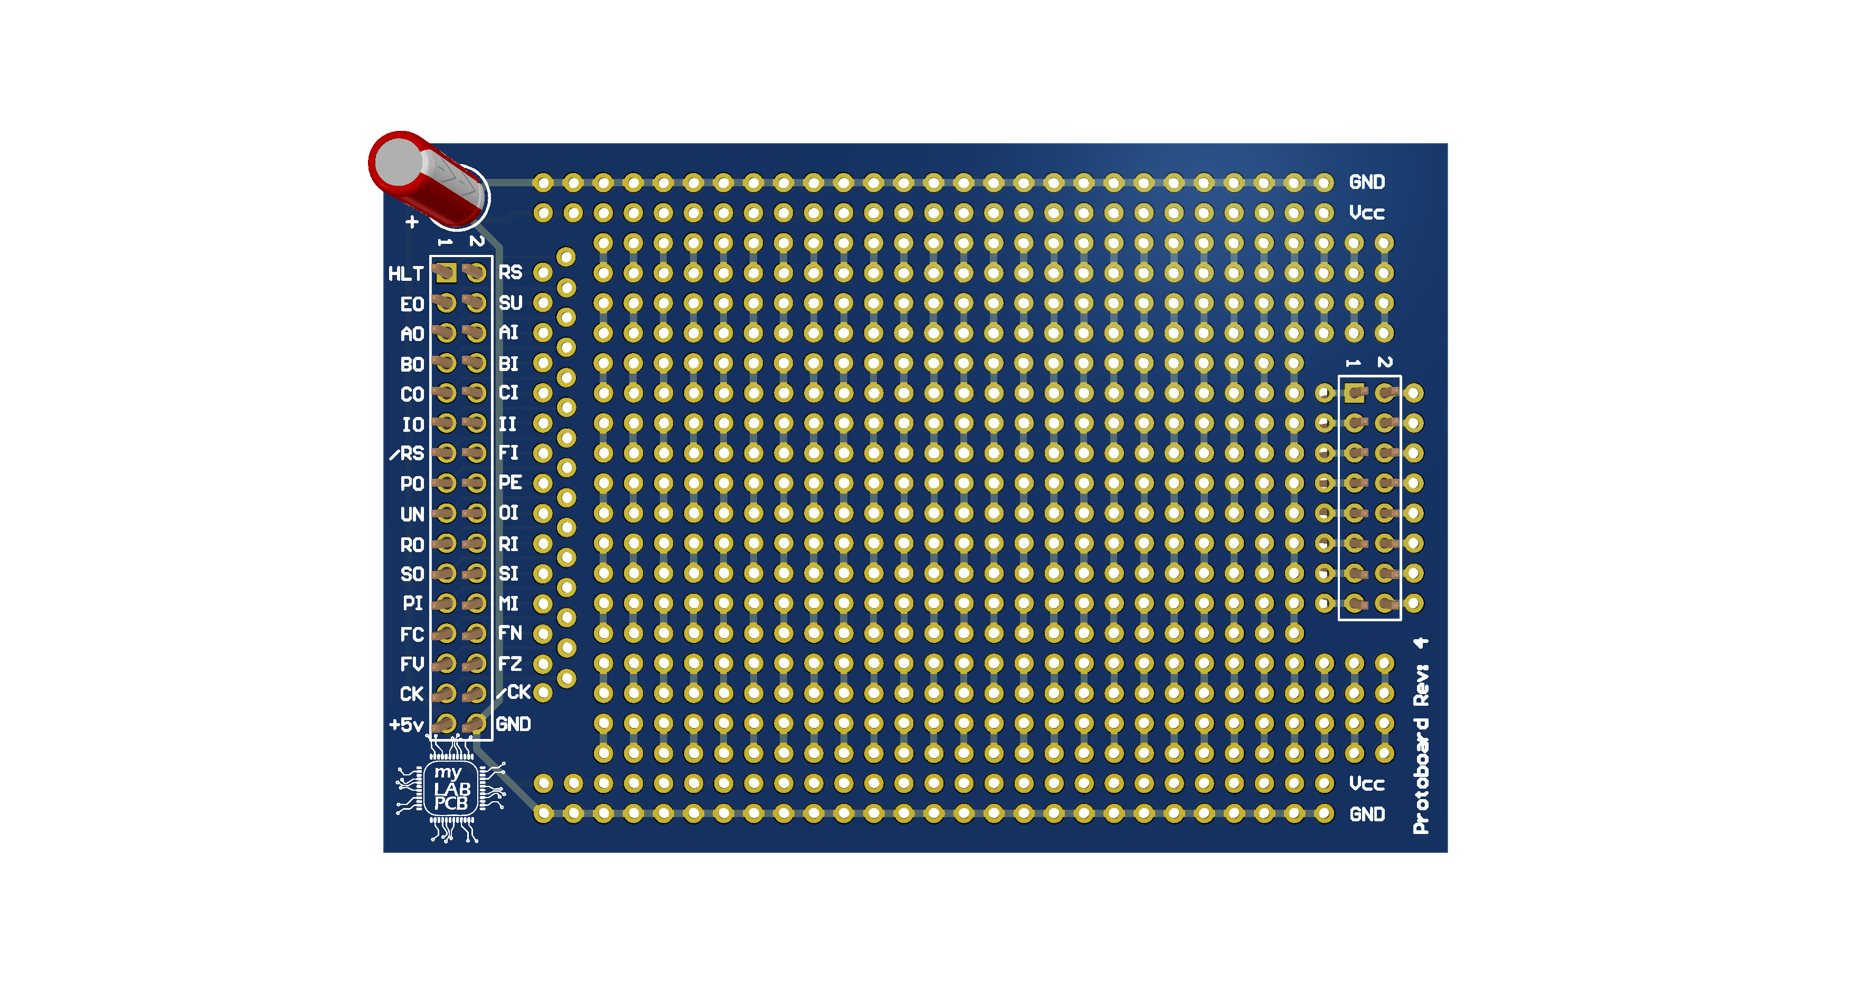
[picture p189: page 1]

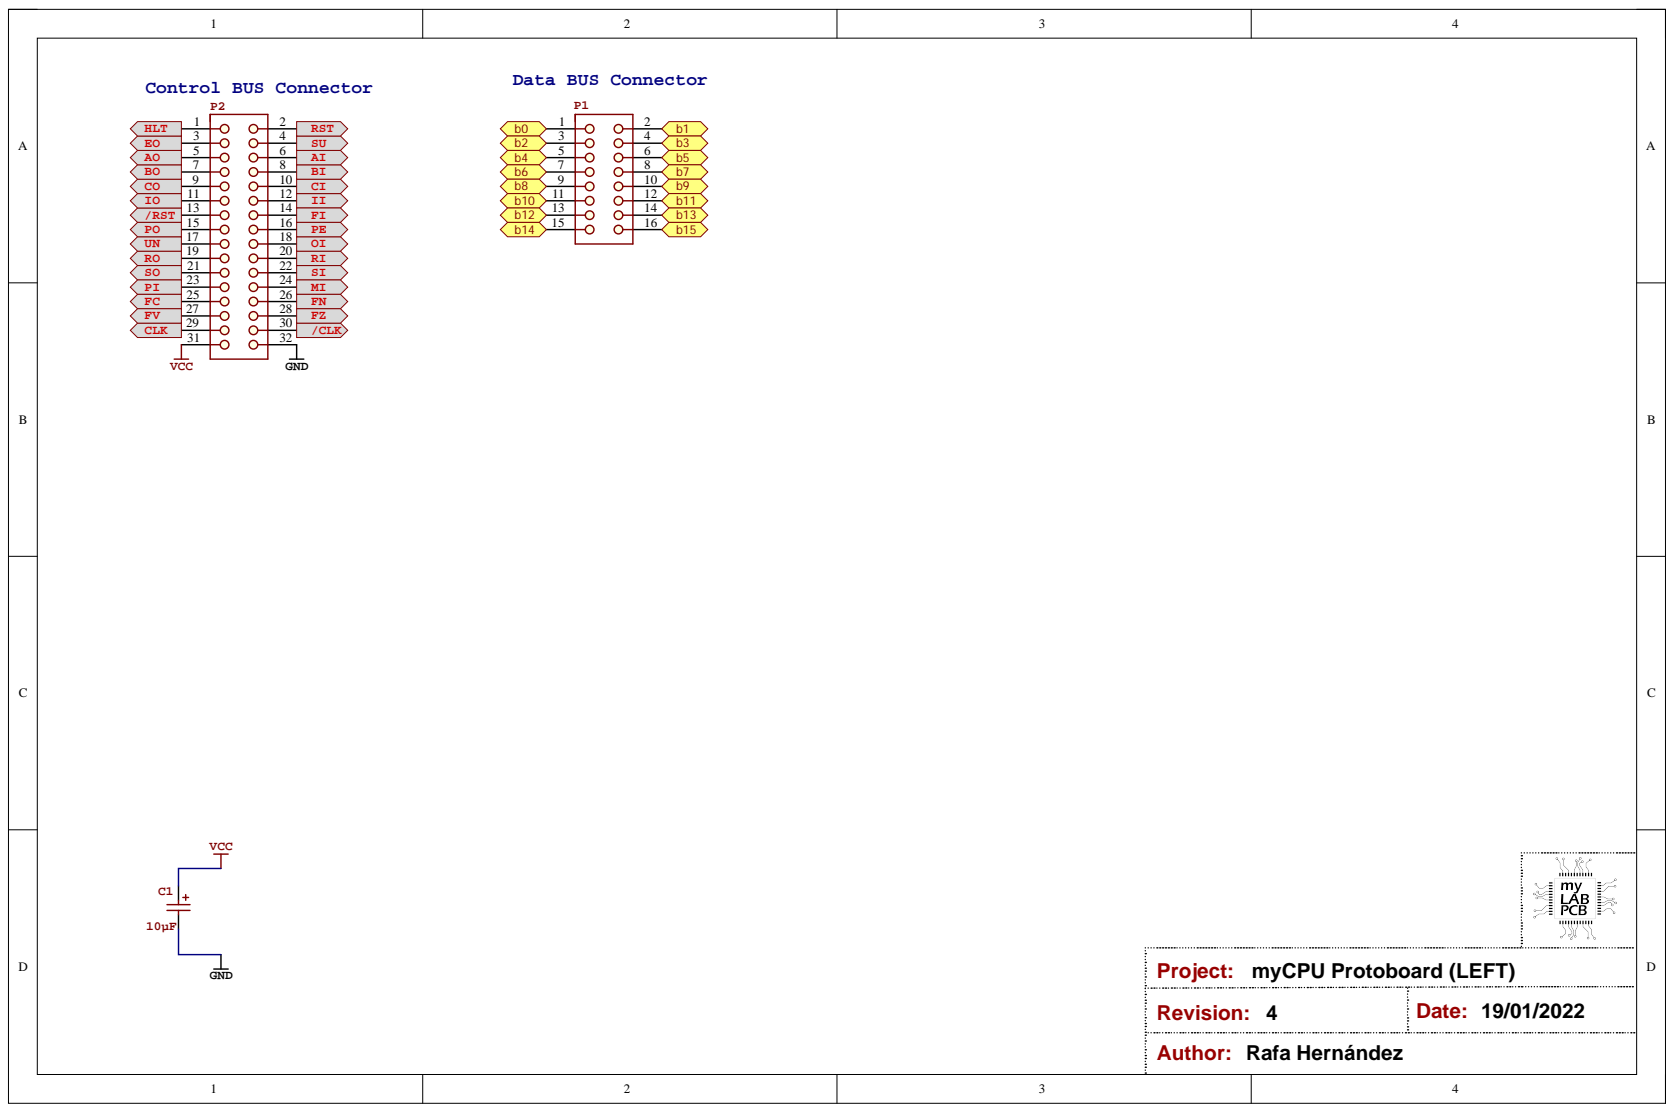
[picture p190: page 3]

Project: myCPU Protoboard (LEFT)

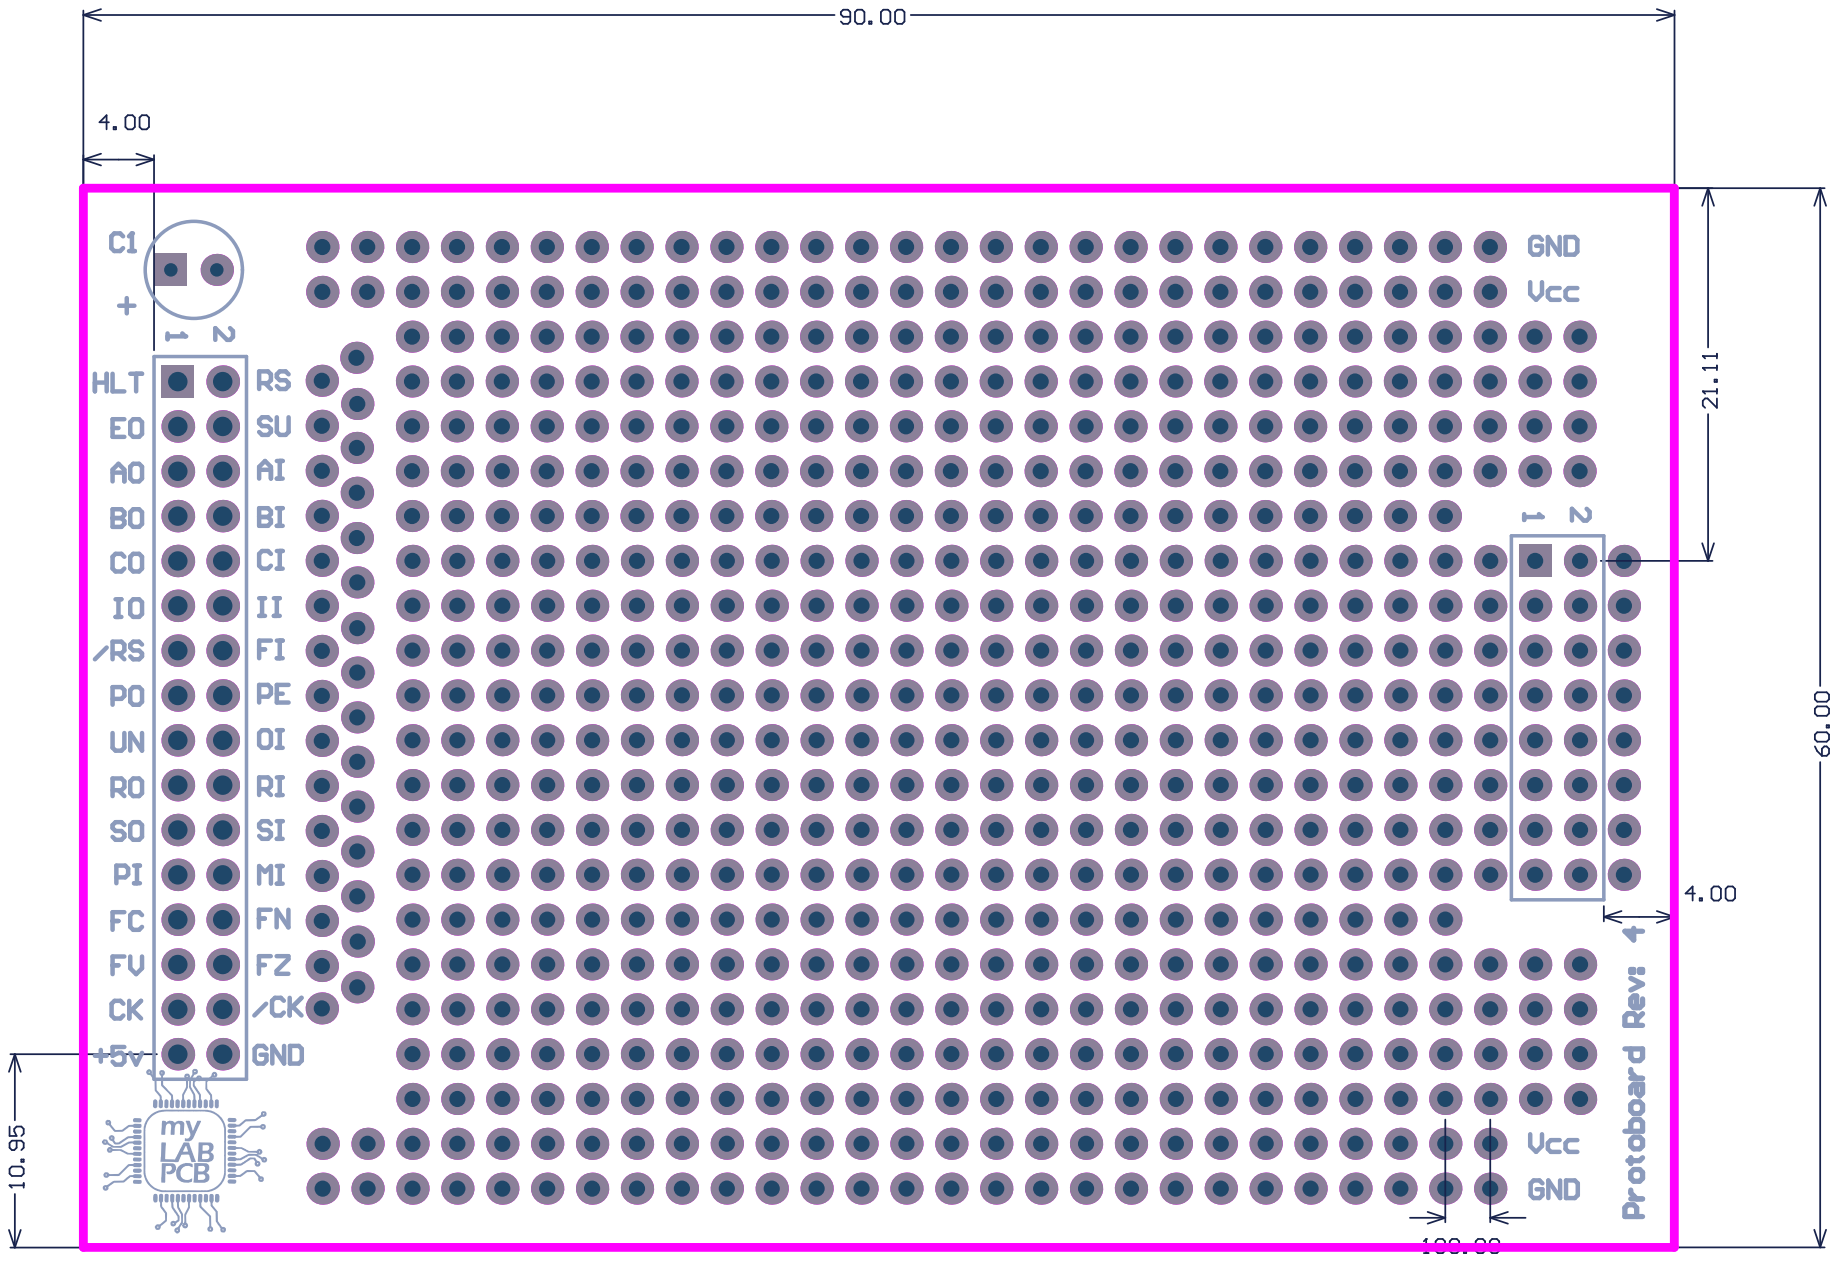
[picture p191: page 4]

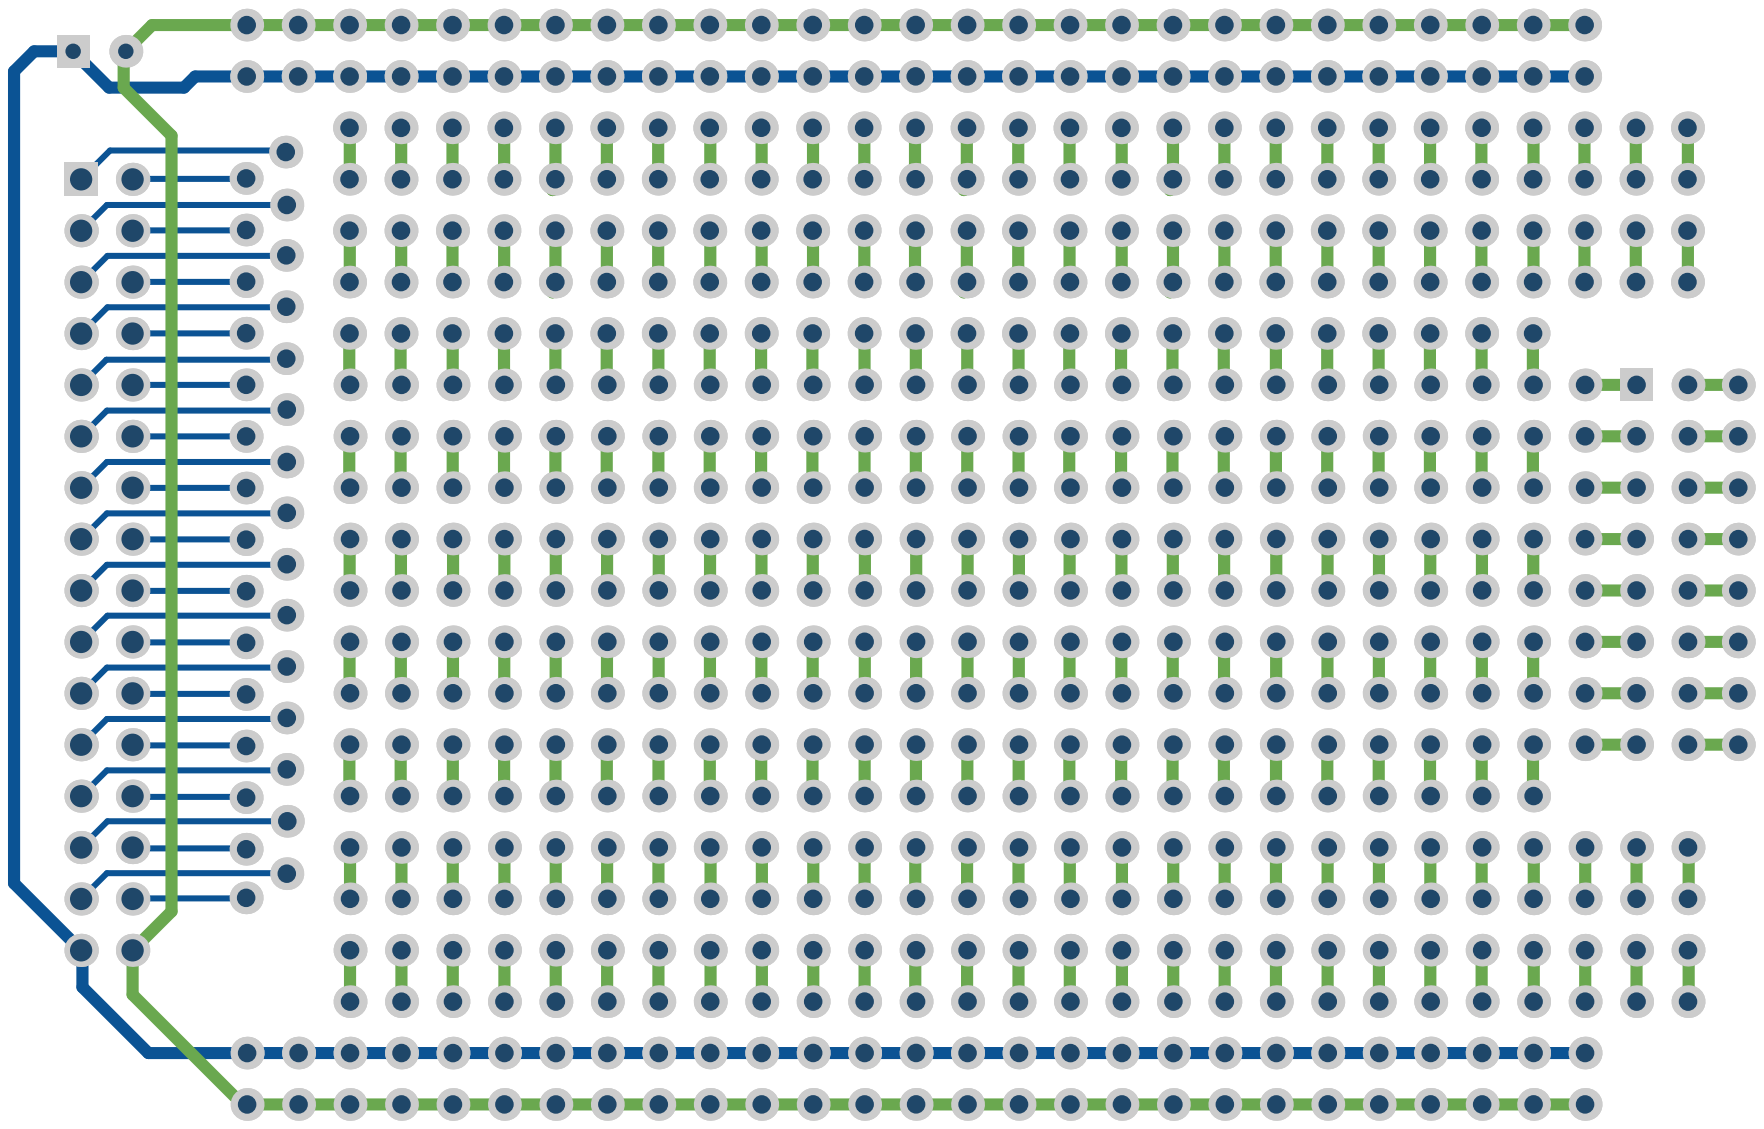
[picture p192: page 5]
