mylabpcb/myCPU/Docs/myCPU_Protoboard_R.pdf

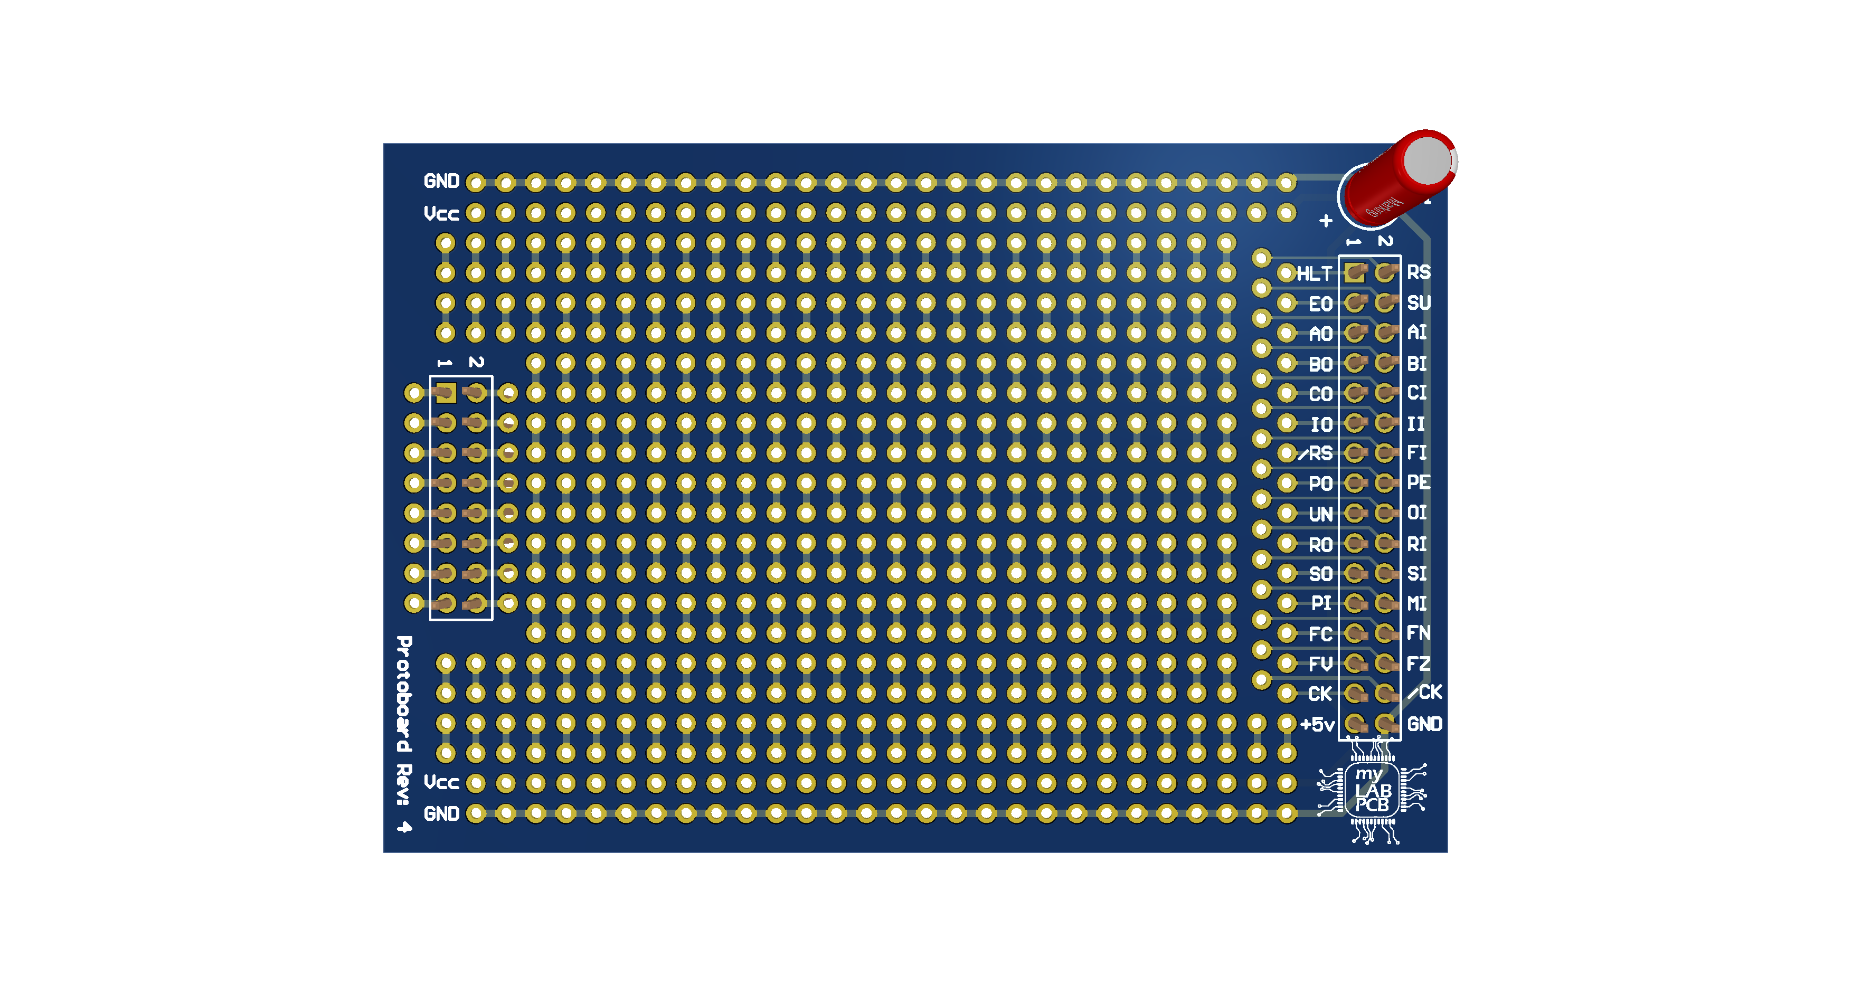
[picture p193: page 1]

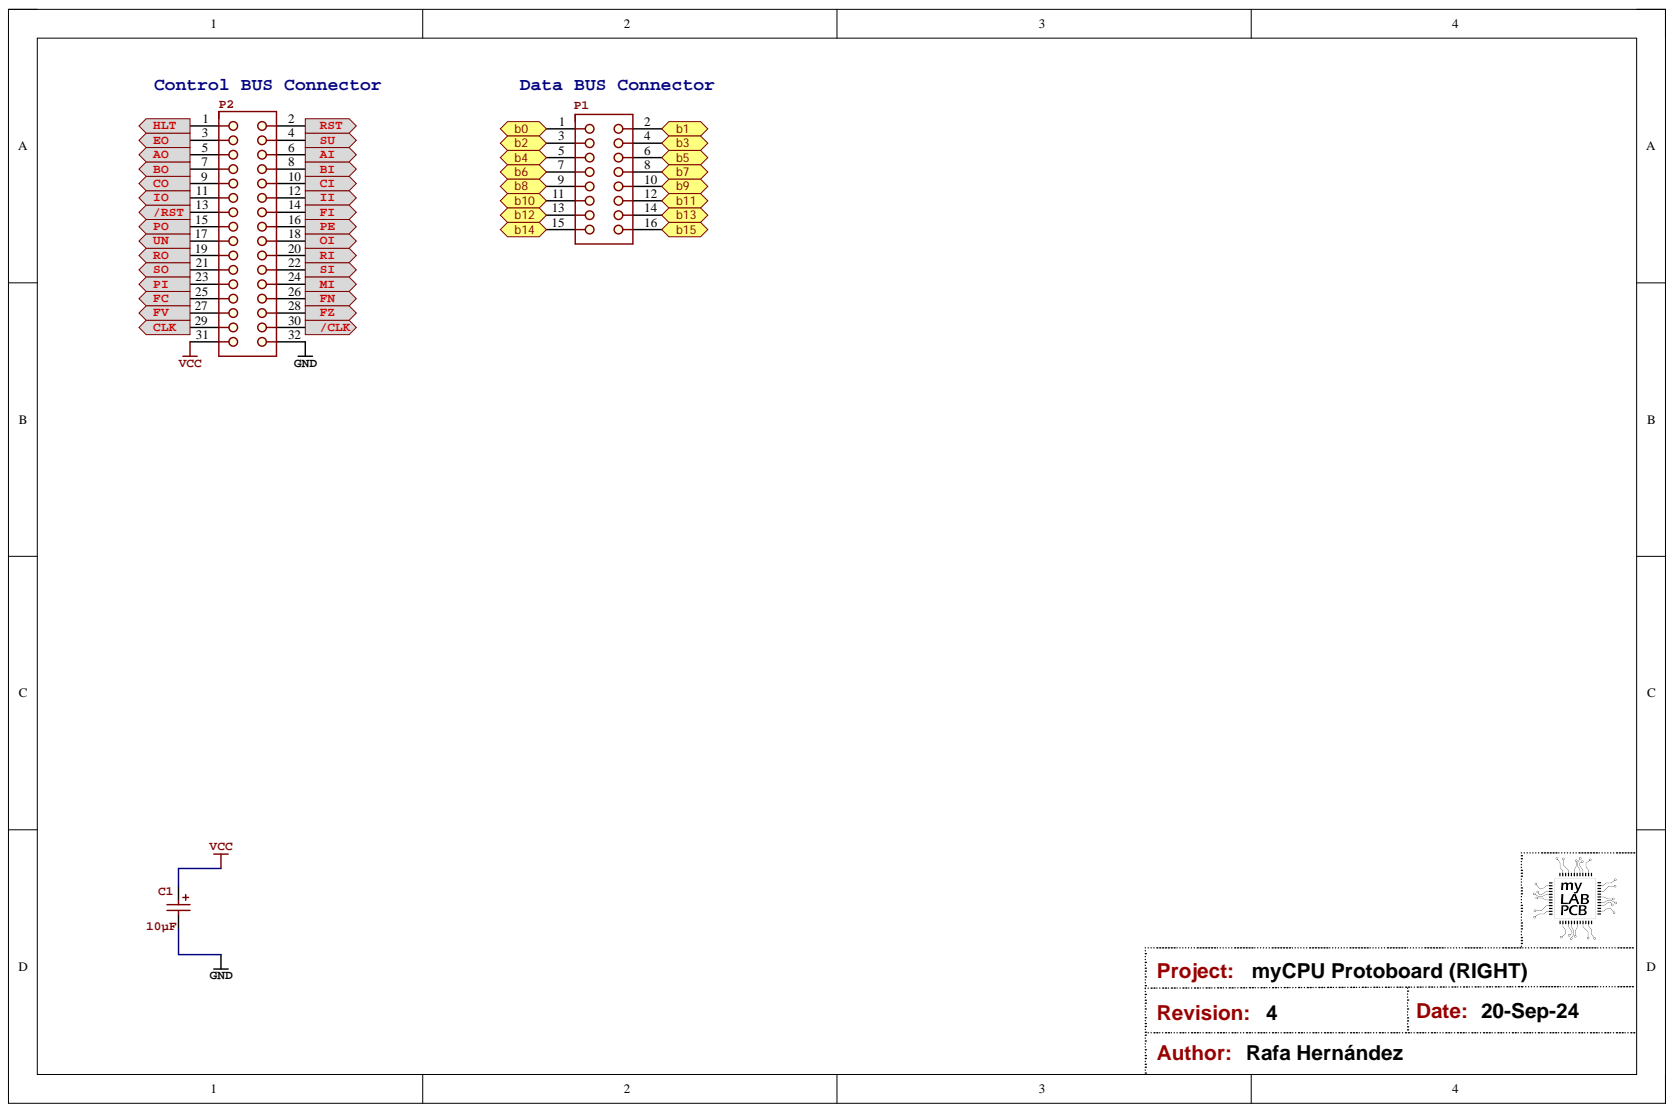
[picture p194: page 3]

Project: myCPU Protoboard (RIGHT)

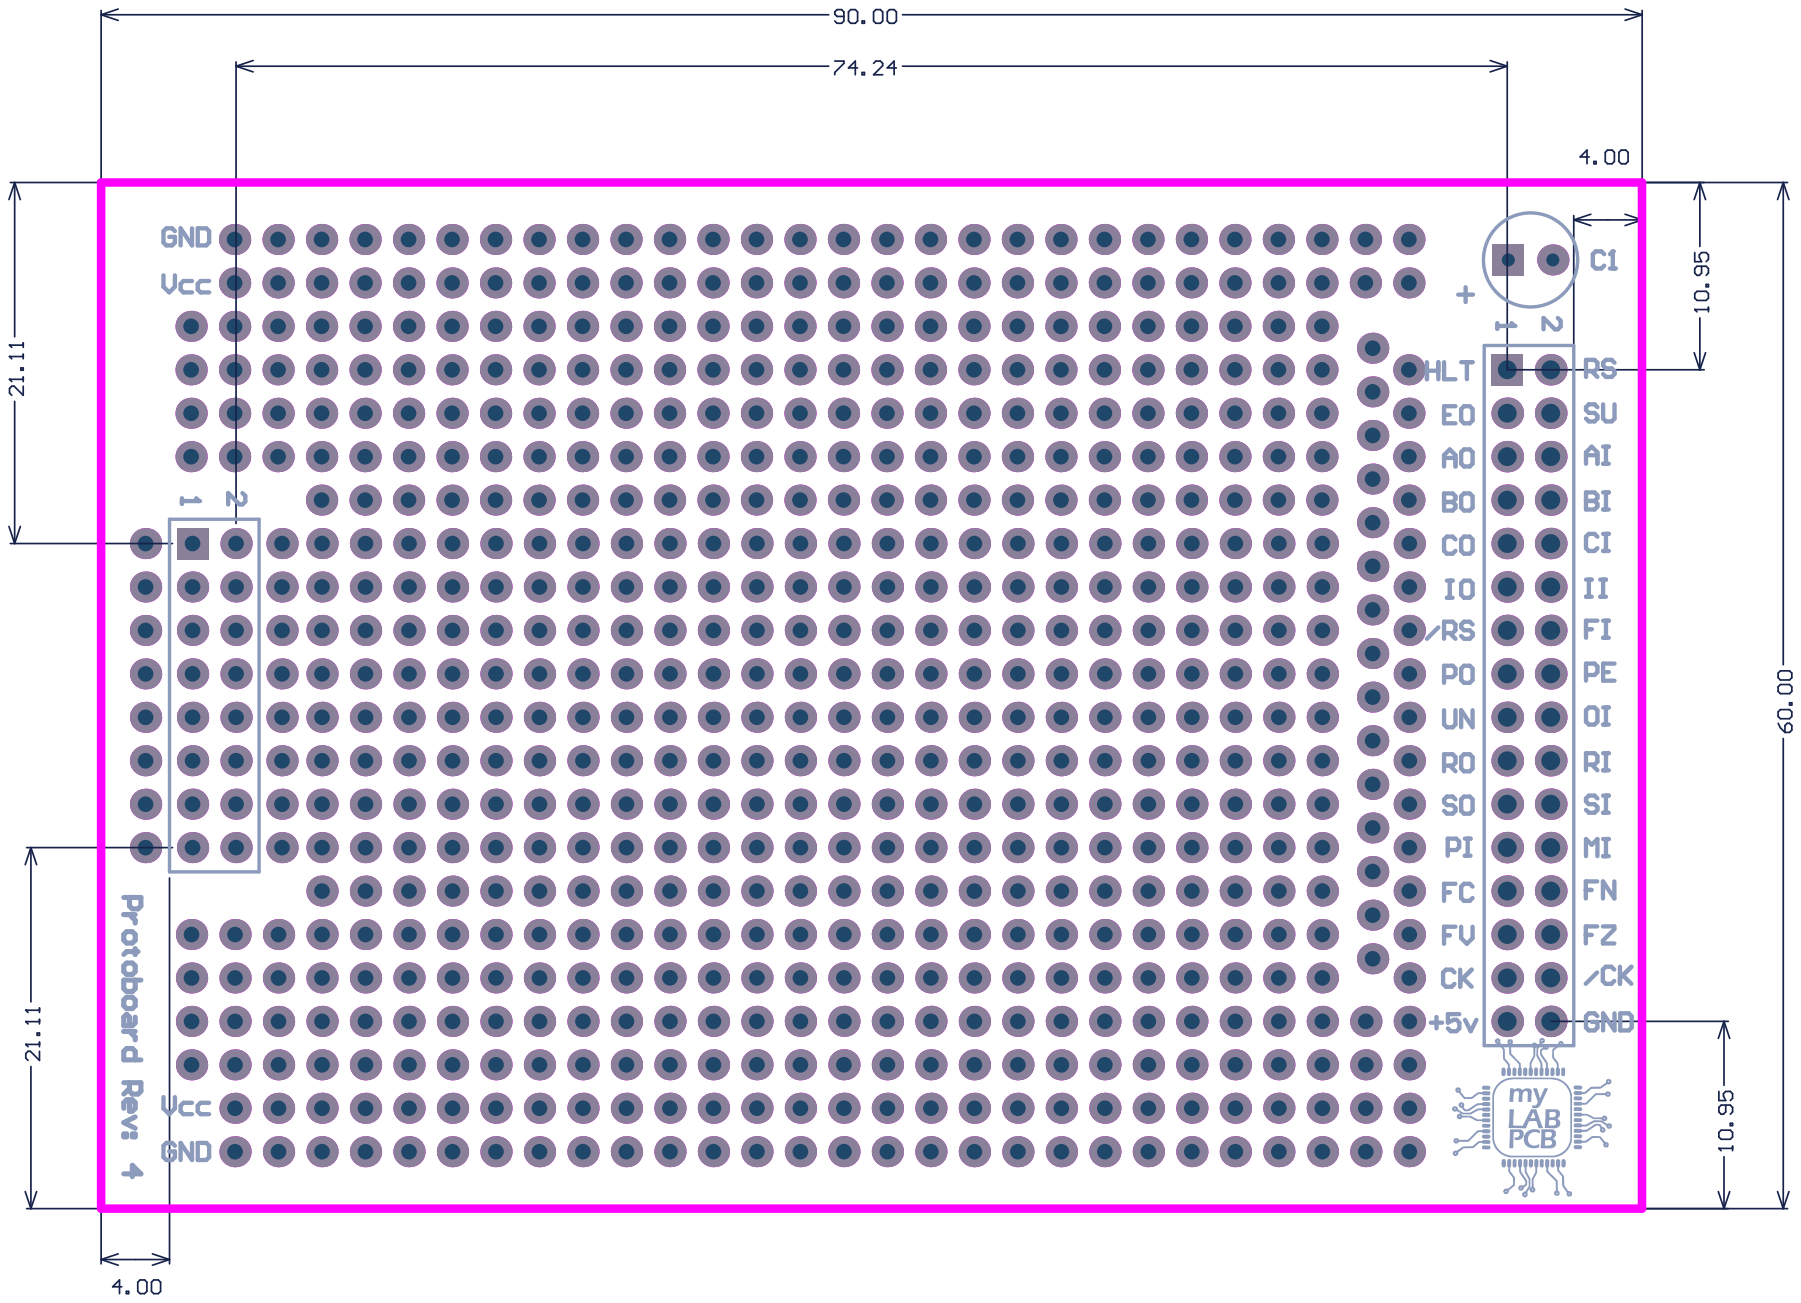
[picture p195: page 4]

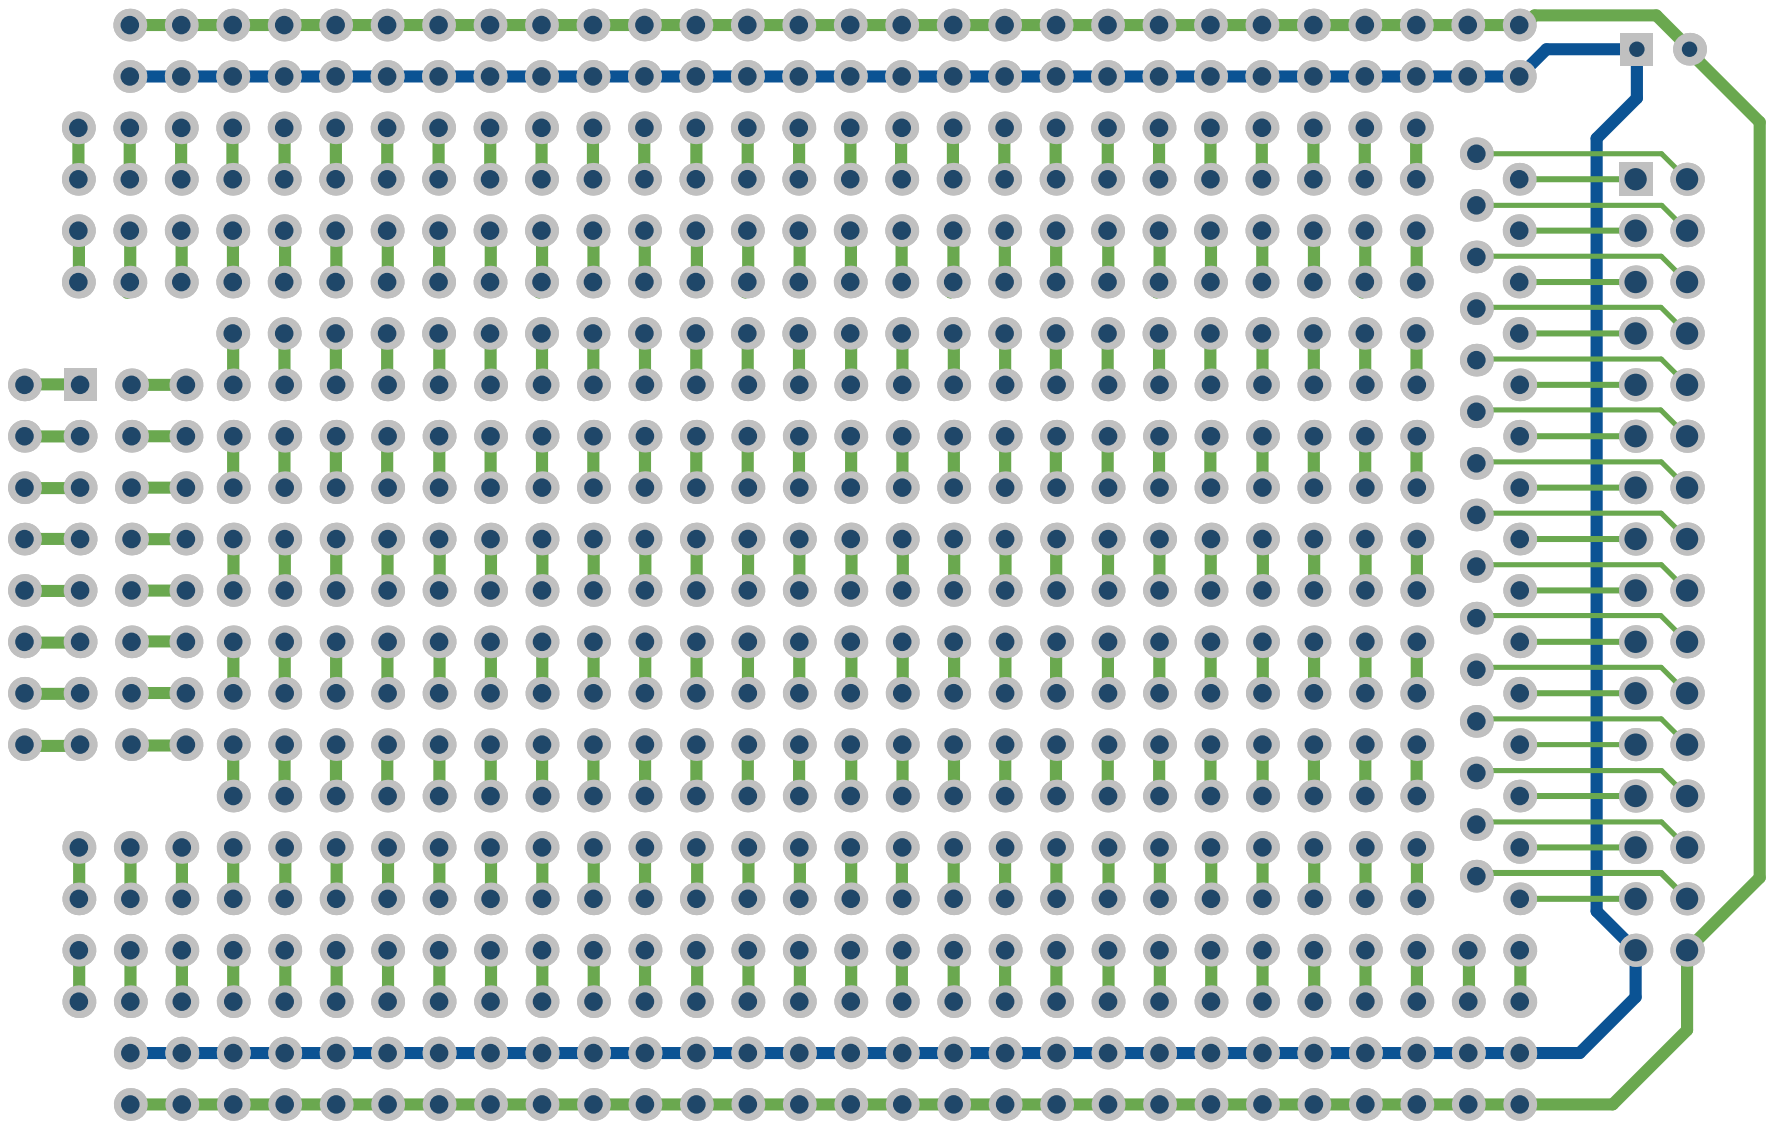
[picture p196: page 5]
