mylabpcb/myCPU/Simulator/myCPU16_Sim.pdf

7-4 | CO FC | 1 | 0 FI | 1HLT | CLK FN | 1 | 0 | 1 0123 | 0123 0123 FZ FV | 0123 | 0123 | 0123 0123 CLK | RST | 0123 0123 | 01234567 | 012 | 0123456789

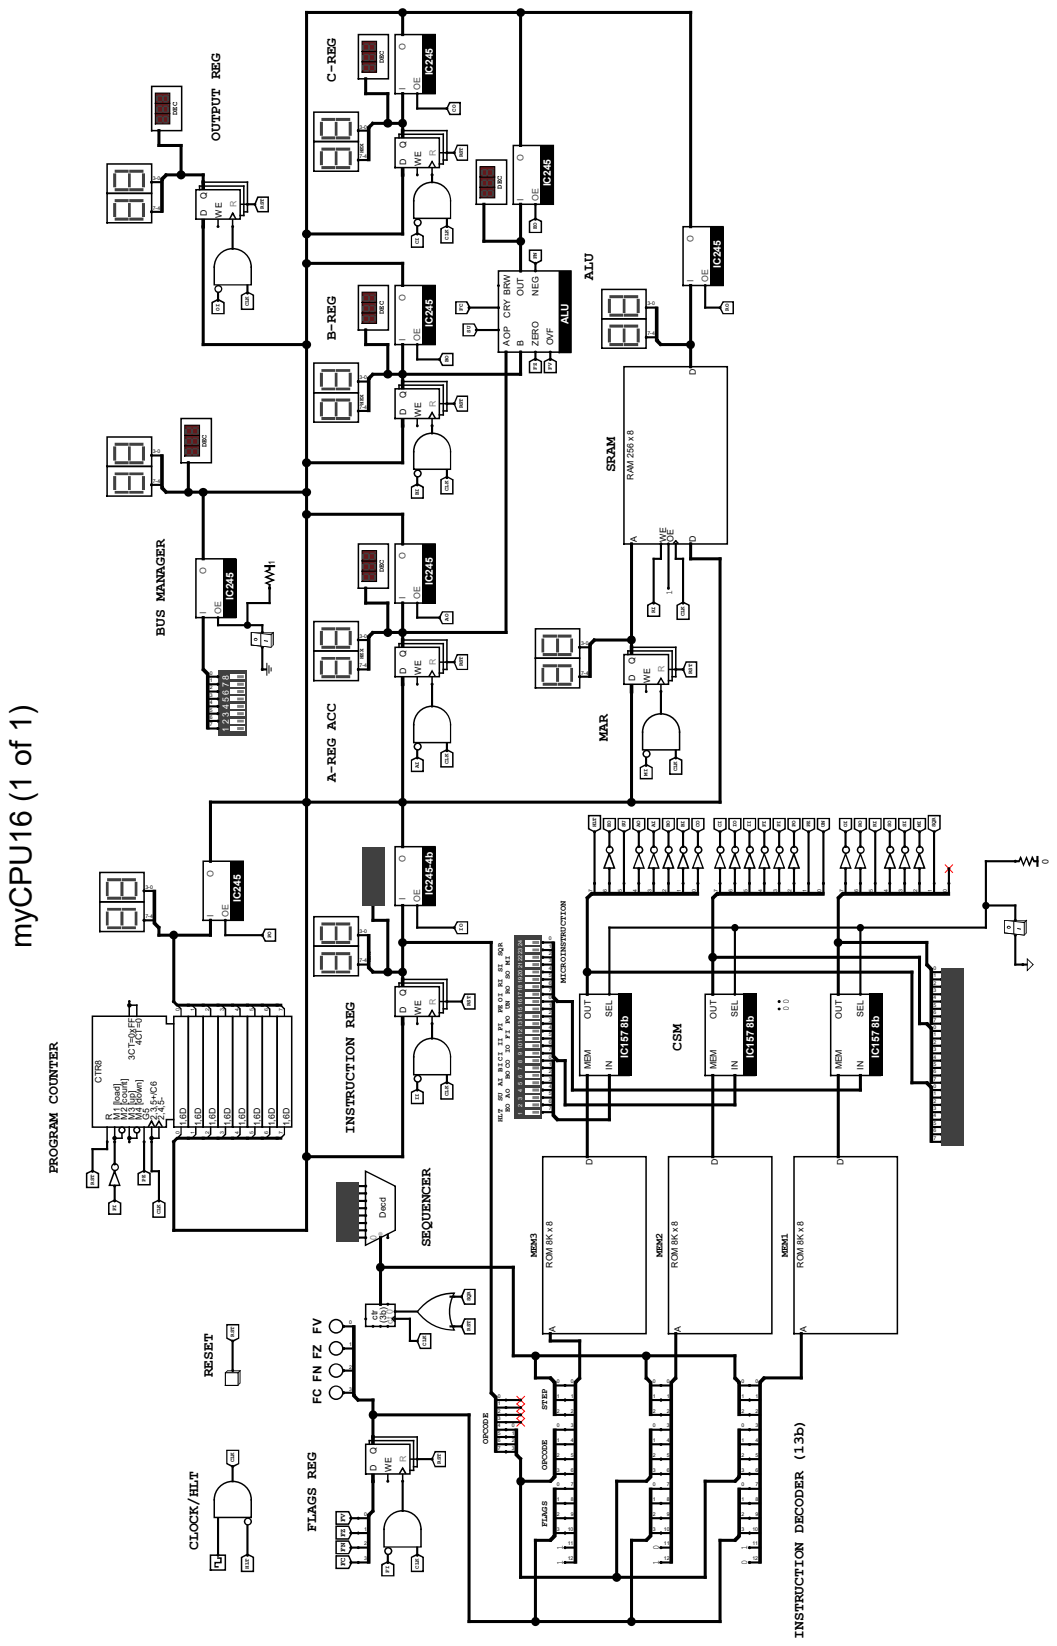
[picture p197: page 1]
0 HLT; SQR MI; CLKAI; CLK 0; RST 1234567; RST; CLK 1 1; CLK; ROCLK; EO RST; 12 RST; RST SQR 0 Decd CTR⁸ RM¹ [load] M² [count] M³ [up] M⁴ [down] G⁵ 2,3,5+/C⁶ 2,4,5⁻ 3CT=0xFF 4CT=0; R WED Q; WE OE RAM ²⁵⁶ x 8 D Q; MEM2; D A ROM ⁸K x 8; MEM1; D A ROM ⁸K x 8 MEM3; D A ROM ⁸K x 8 0 ctctr (3b⁾; SEQUENCER; HLT PROGRAM COUNTER; EO SUAO AIBO INSTRUCTION REG; BICOCIIOII; CSMFIPIPO PEUNOIRORISOSIMIHEX; SQR; MICROINSTRUCTION A-REG ACC; MAR HEX BUS MANAGER; SRAM HEX B-REG; ALU HEX OUTPUT REG; C-REG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

myCPU16 (1 of 1) PI CLK RSTPE 01234567 II 01234567 CLK 01234567 01234567 0RST0 01234567
